lynchaj/nhyodyne/Z80BCKPLN2/ReadMe.md

# Extended backplane for Z80 Modular Backplane Computer

Sixteen backplane slots

Power LED indicator

Onboard power switch

Power input screw terminals for direct feed of 5V DC from power supply

# Jumpers

No jumpers or selectable options
