lynchaj/nhyodyne/Z80BCKPLN1/ReadMe.md

# Backplane board for Z80 Modular Backplane Computer

Eight backplane slots

Accepts 9V DC unregulated, center positive, 5.5mm external diameter, 2.1 internal diameter wall adapter power supply

Power LED

Uses either LM7805 5VDC voltage regulator or Pololu 5VDC switching power supply

Voltage regulator can be bypassed for direct 5VDC feed from power supply

# Jumpers

No jumpers or selectable options
