lynchaj/nhyodyne/Z80PROTO2/ReadMe.md

# Prototyping Board for Z80 Modular Backplane Computer

Provides area of plated through holes for general circuit prototyping

Provides pads and traces for common bus interface components

Power LED

Chip Select LED

No default IO ports but configurable if desired

# Jumpers

No jumpers to configure.  P47, P48, P49, and P50 are connect points for various CPU bus signals labeled on PCB
