lynchaj/nhyodyne/Z80ESP/HARDWARE/ReadMe.md

Z80 ESP IO is a board for video, keyboard, mouse, wifi, bluetooth, & sound using a pair of ESP32 dev modules

This board is currently not complete and should not be considered stable
