lynchaj/nhyodyne/6502PERI/Z80-6502IO.jpg

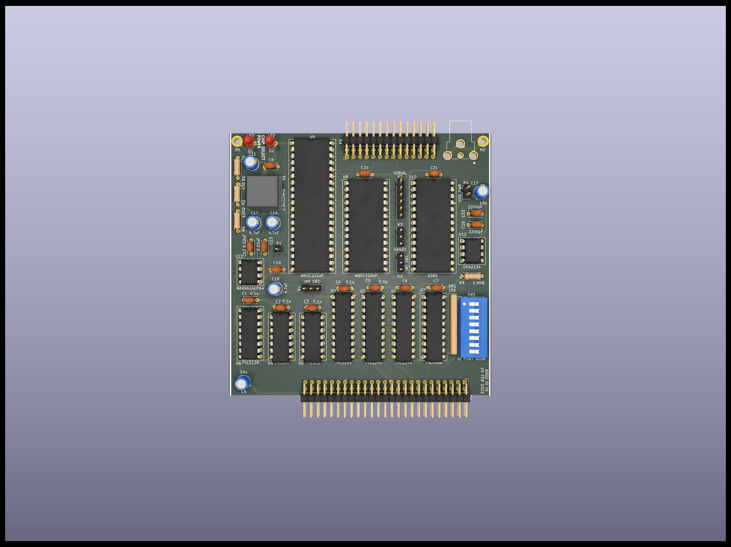
6502PERI/Z80-6502IO.jpg
