lynchaj/nhyodyne/Z80BCKPLN2/Z80BCKPLN2.jpg

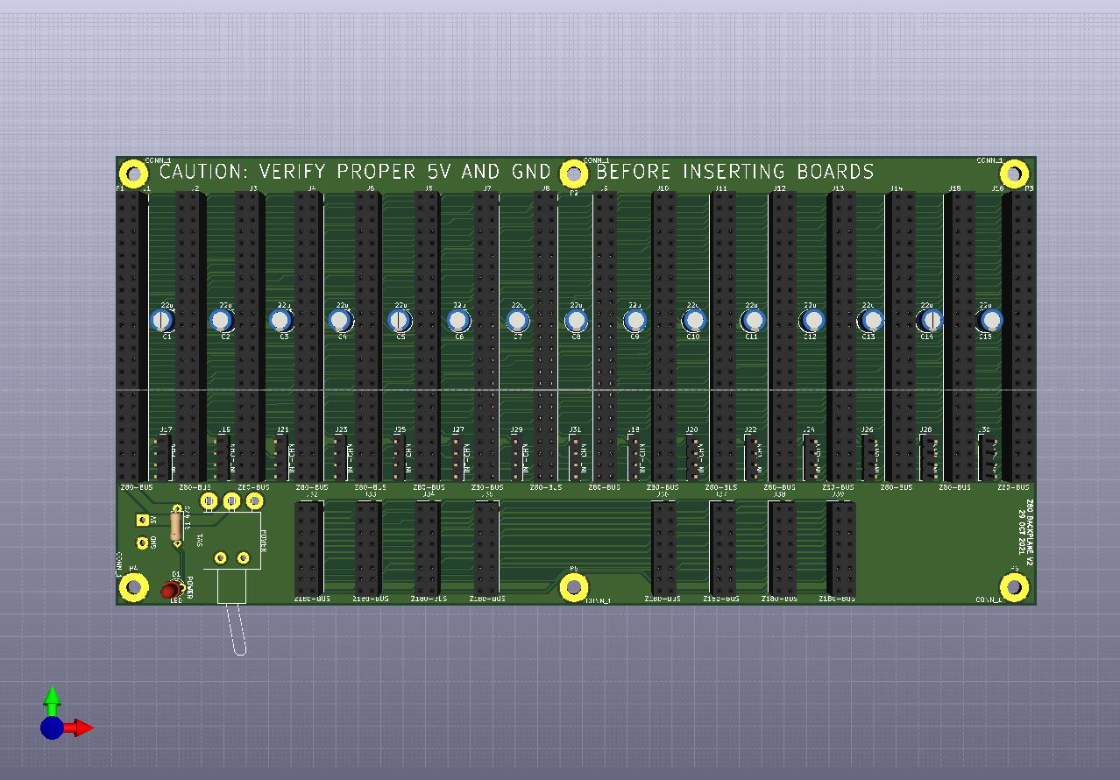
Z80BCKPLN2/Z80BCKPLN2.jpg
