lynchaj/nhyodyne/Z80CLOCK2/Z80CLOCK2.jpg

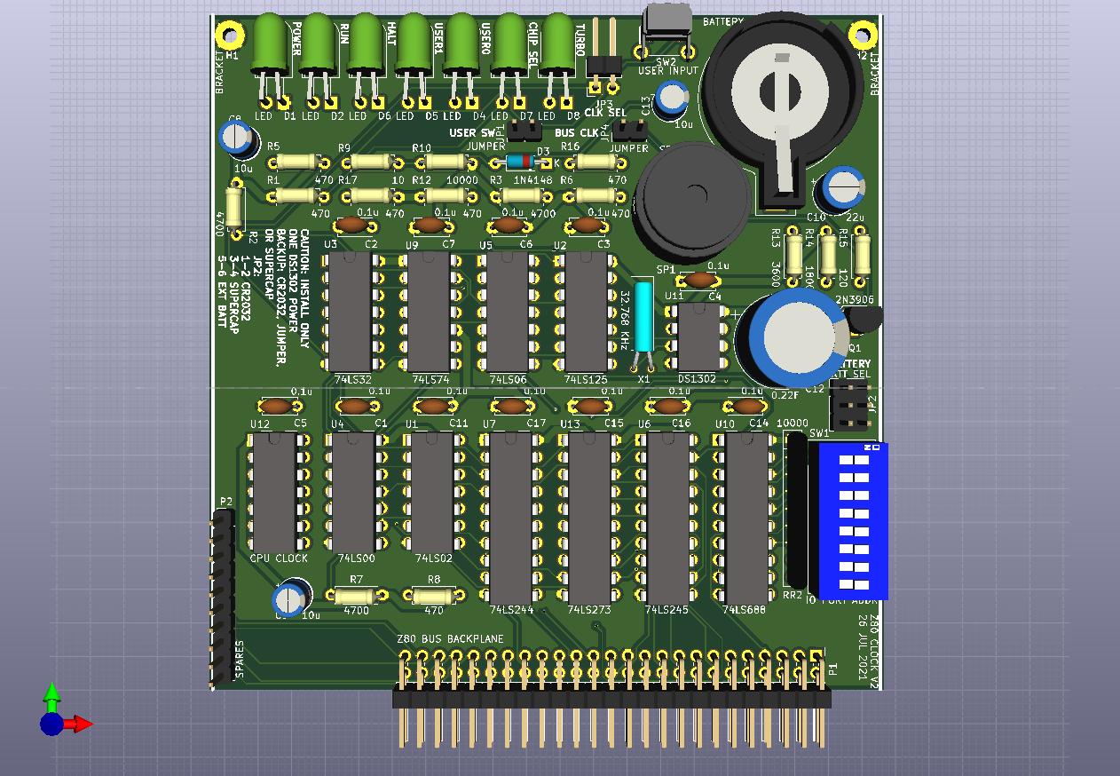
Z80CLOCK2/Z80CLOCK2.jpg
