lynchaj/nhyodyne/Z80CTCDART2/Z80CTCDART2.jpg

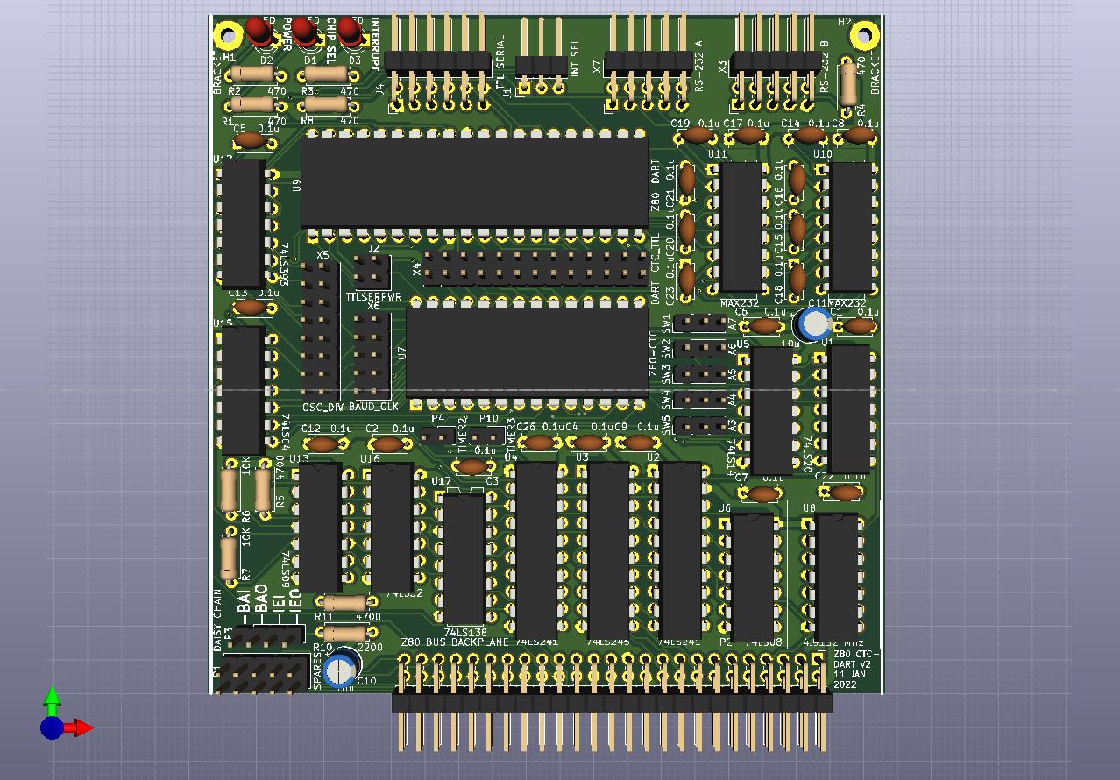
Z80CTCDART2/Z80CTCDART2.jpg
