lynchaj/nhyodyne/Z80DMA2/Z80DMA2.jpg

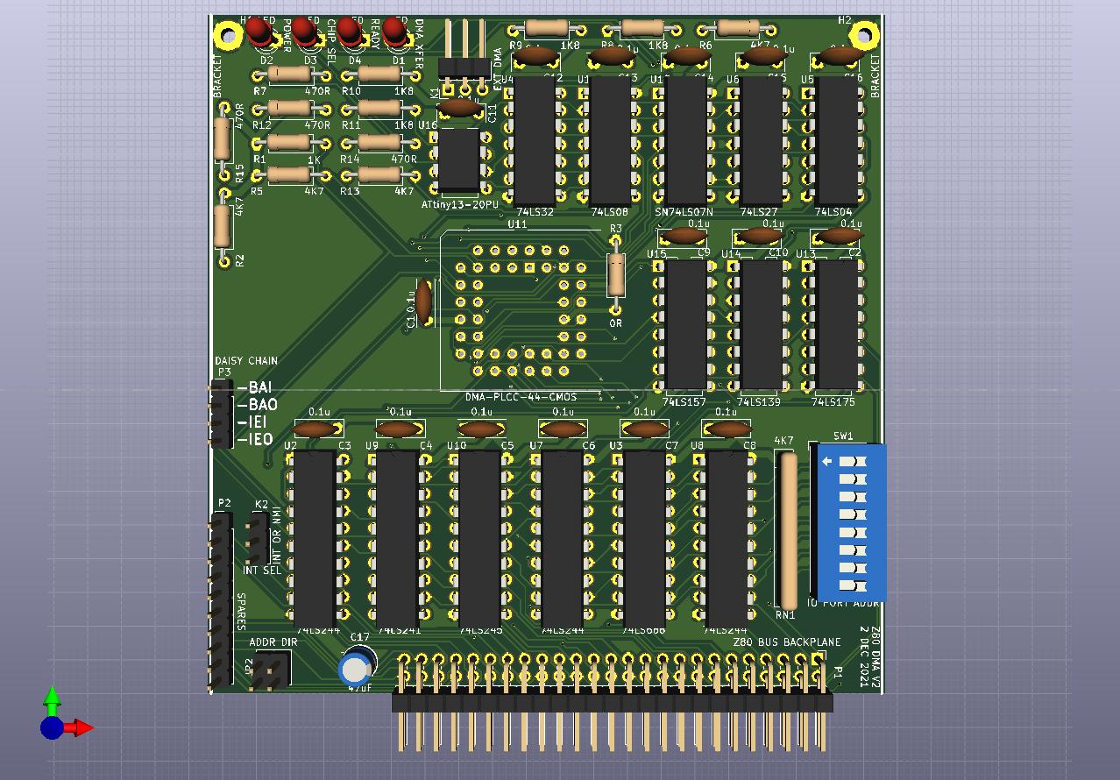
Z80DMA2/Z80DMA2.jpg
