lynchaj/nhyodyne/Z80DUALPIO2/Z80DUALPIO2.jpg

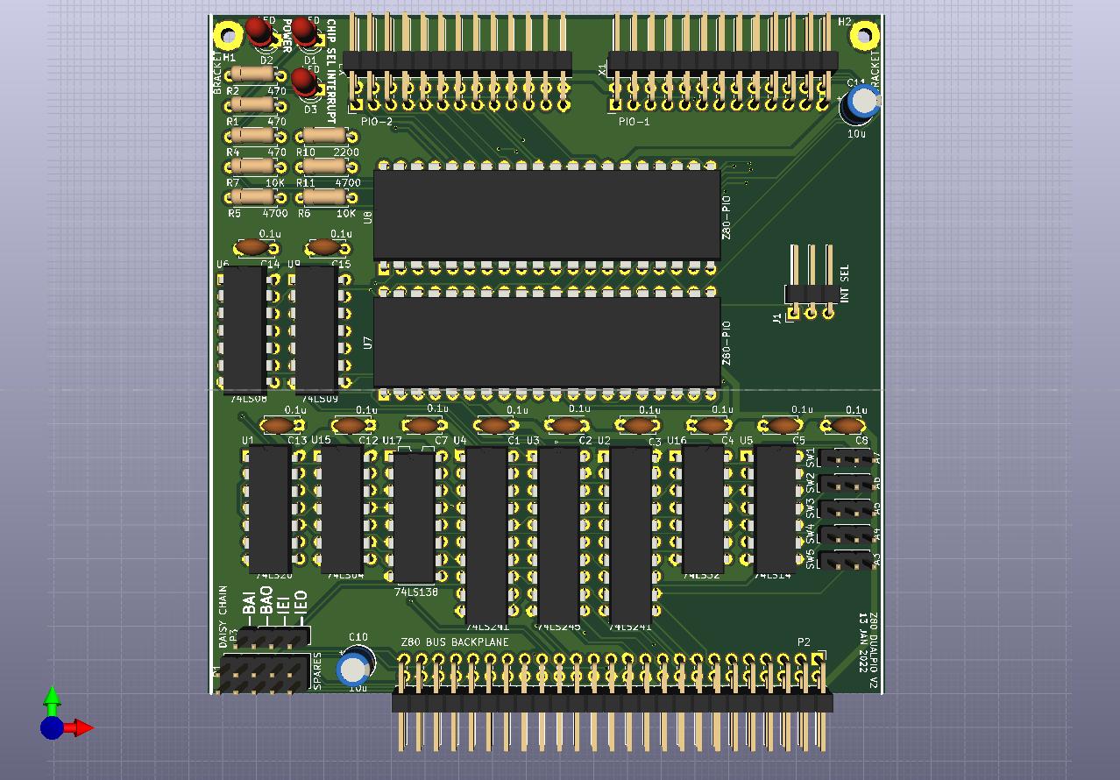
Z80DUALPIO2/Z80DUALPIO2.jpg
