lynchaj/nhyodyne/Z80DUART2/Z80DUART2.jpg

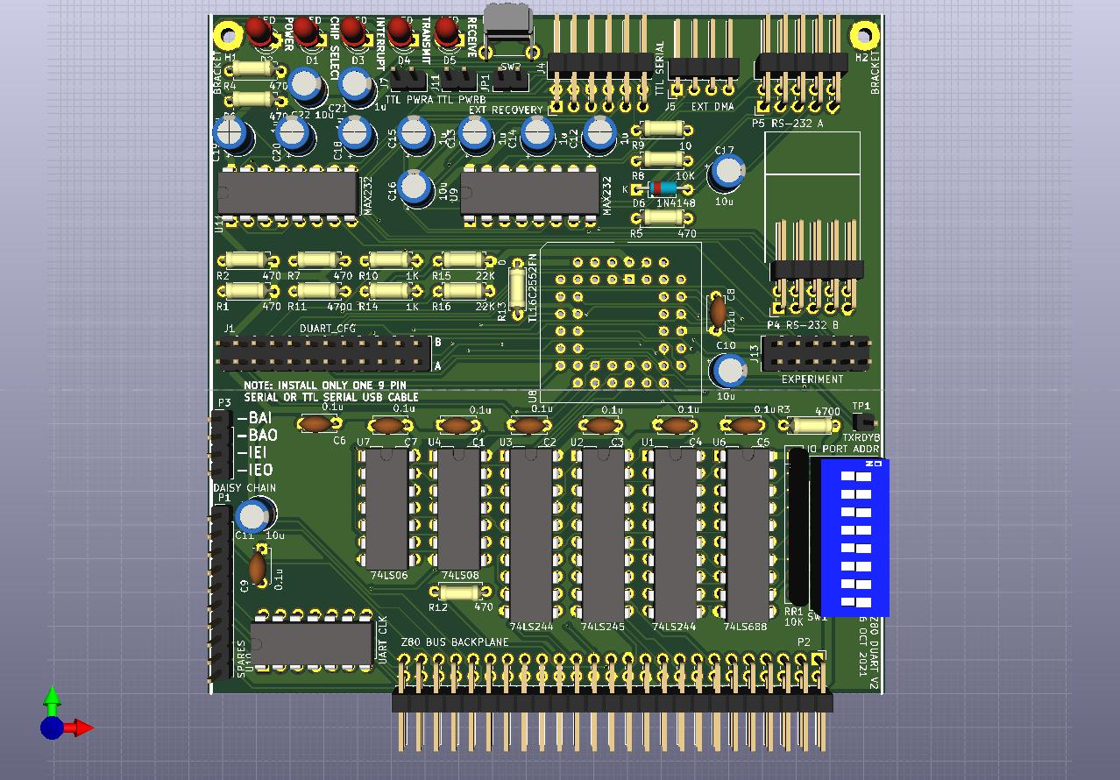
Z80DUART2/Z80DUART2.jpg
