lynchaj/nhyodyne/Z80ENET/Z80ENET.jpg

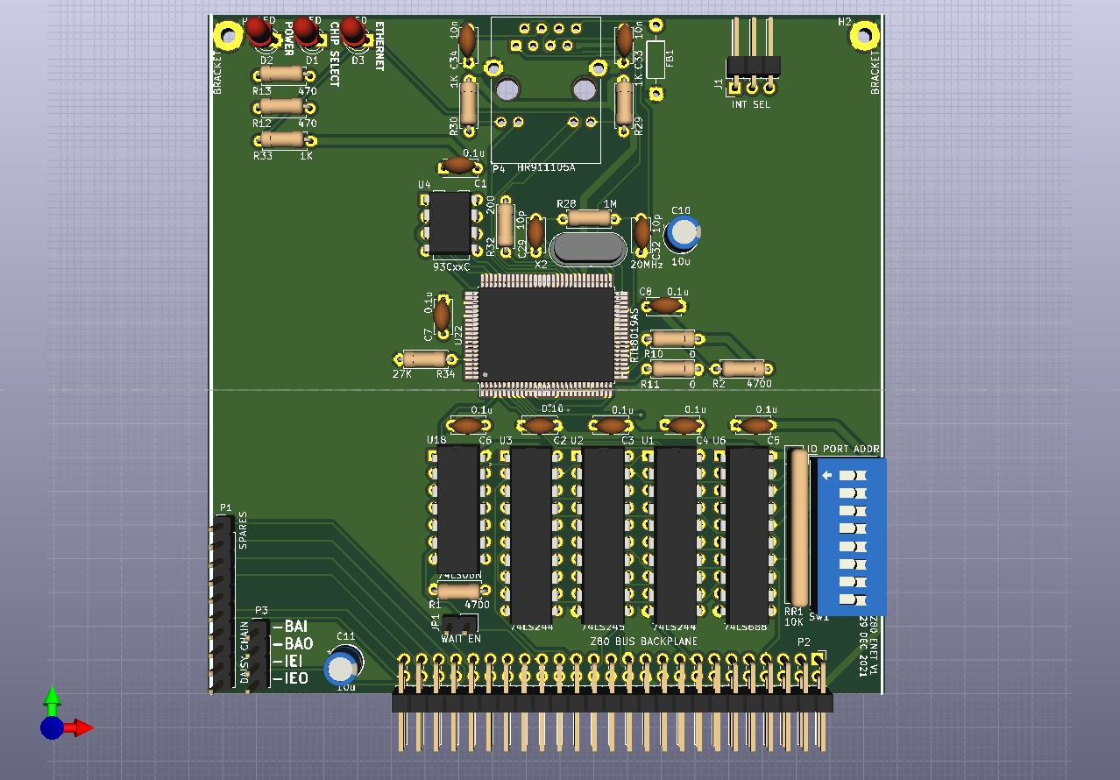
Z80ENET/Z80ENET.jpg
