lynchaj/nhyodyne/Z80FDC1/Z80FDC.jpg

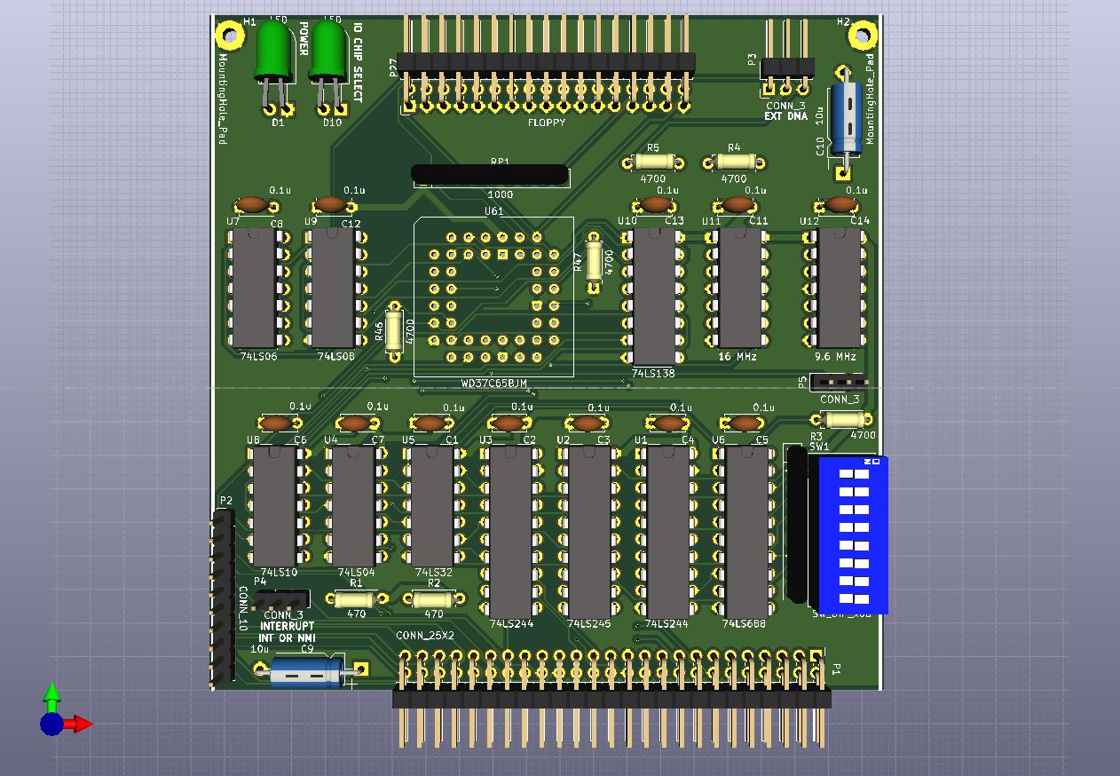
Z80FDC1/Z80FDC.jpg
