lynchaj/nhyodyne/Z80KBDMSE1/Photos/IMG_5907.JPG

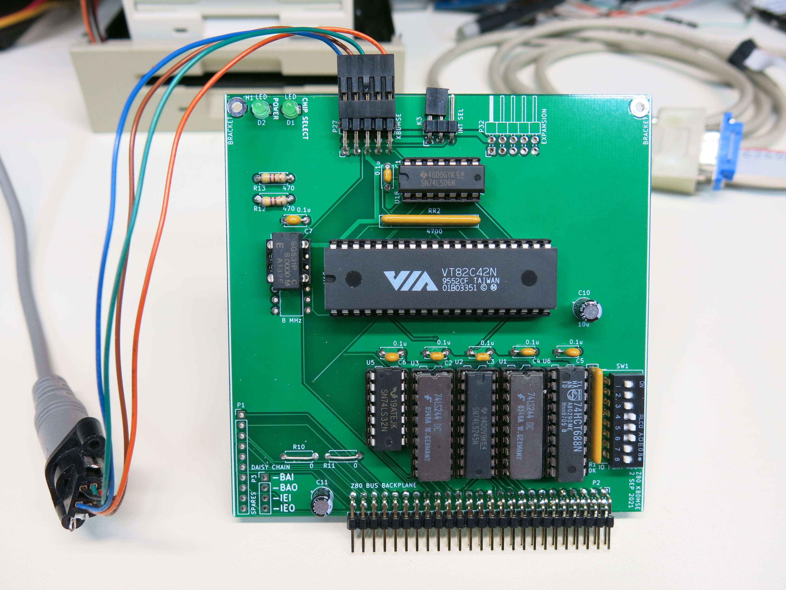
Z80KBDMSE1/Photos/IMG_5907.JPG
