lynchaj/nhyodyne/Z80KBDMSE1/Z80KBDMSE.jpg

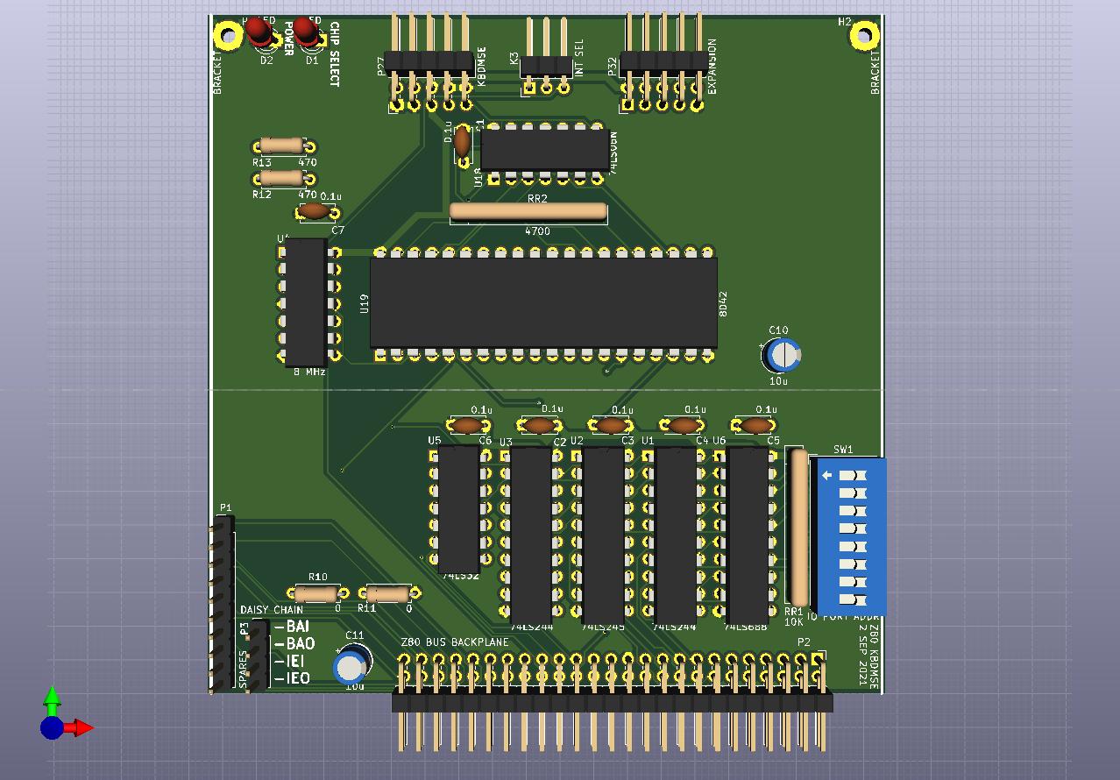
Z80KBDMSE1/Z80KBDMSE.jpg
