lynchaj/nhyodyne/Z80PPIDE2/Z80PPIDE2.jpg

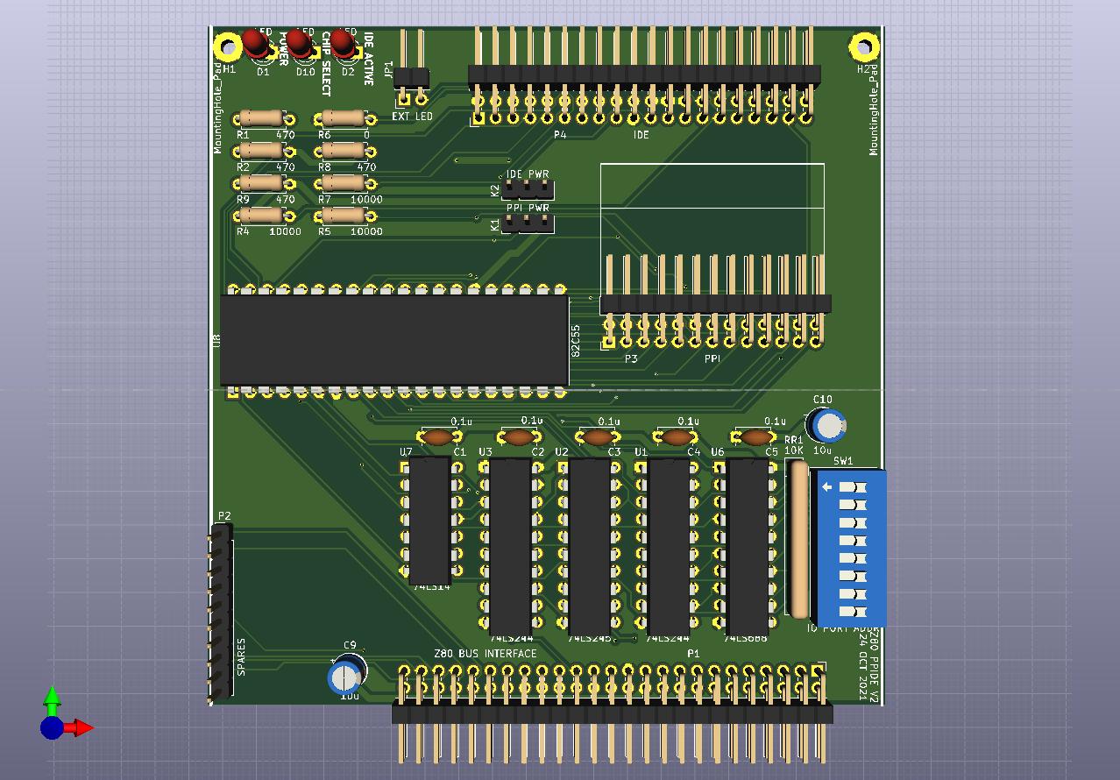
Z80PPIDE2/Z80PPIDE2.jpg
