lynchaj/nhyodyne/Z80PROC3/Z80PROC3.jpg

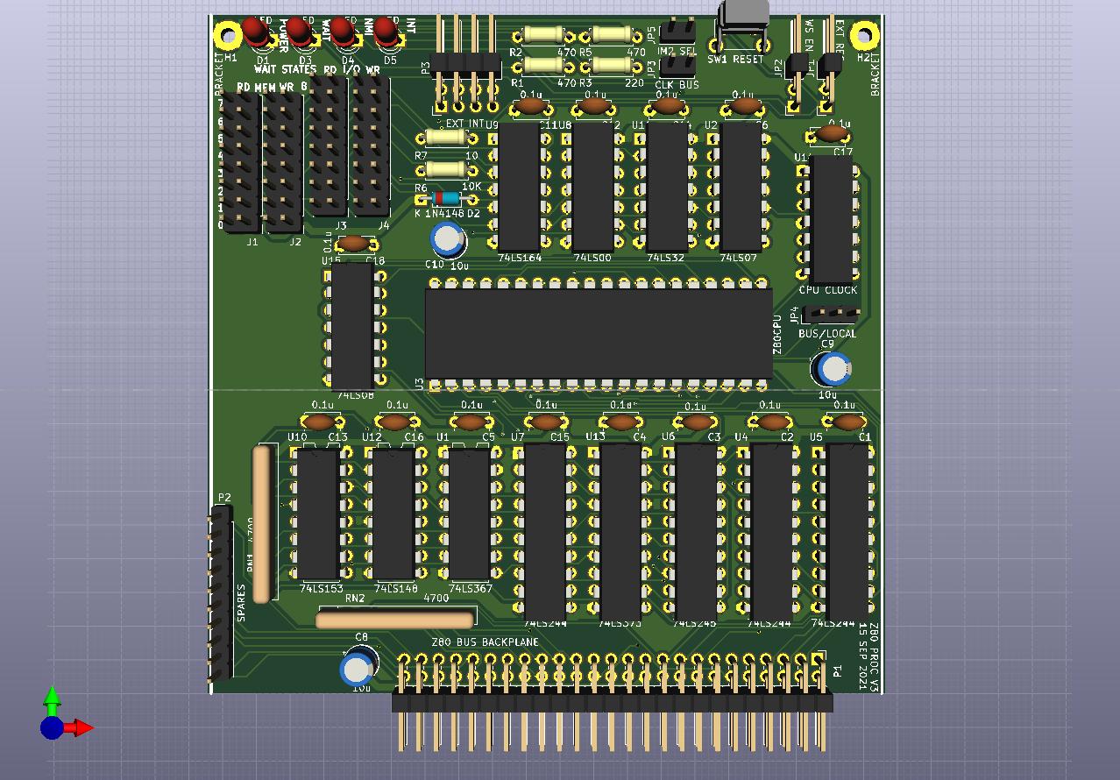
Z80PROC3/Z80PROC3.jpg
