lynchaj/nhyodyne/Z80PROTO2/Z80PROTO2.jpg

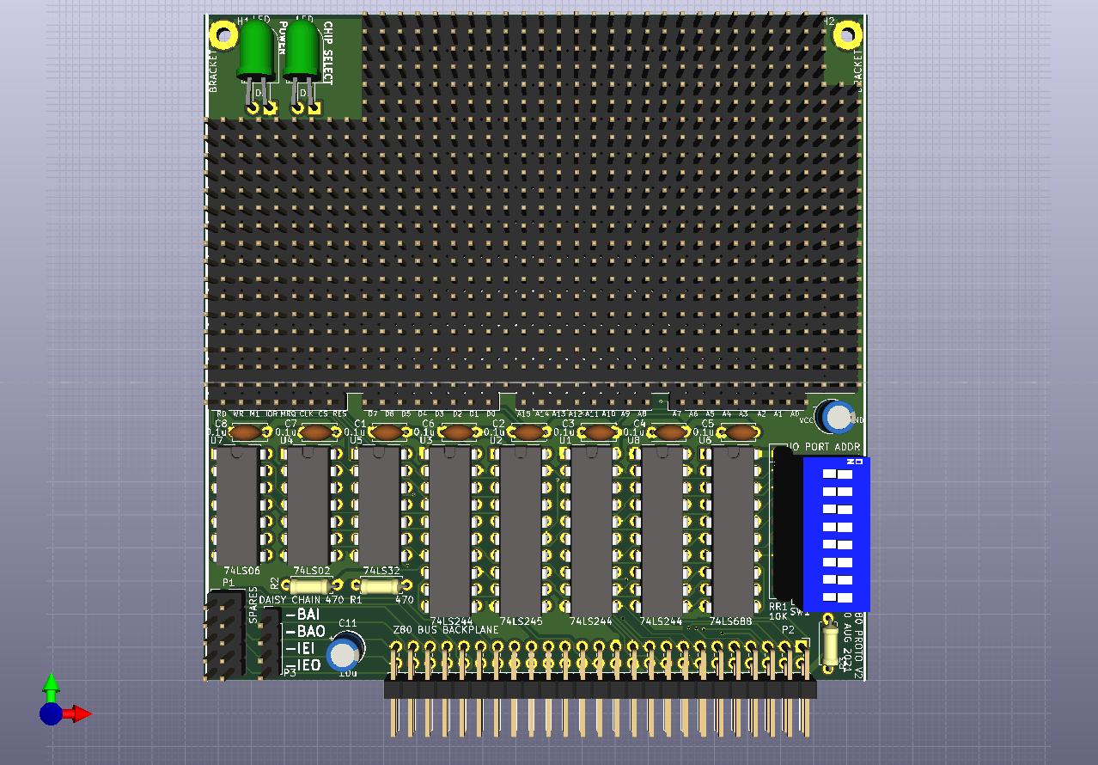
Z80PROTO2/Z80PROTO2.jpg
