lynchaj/nhyodyne/Z80RAM3/Z80RAM3.jpg

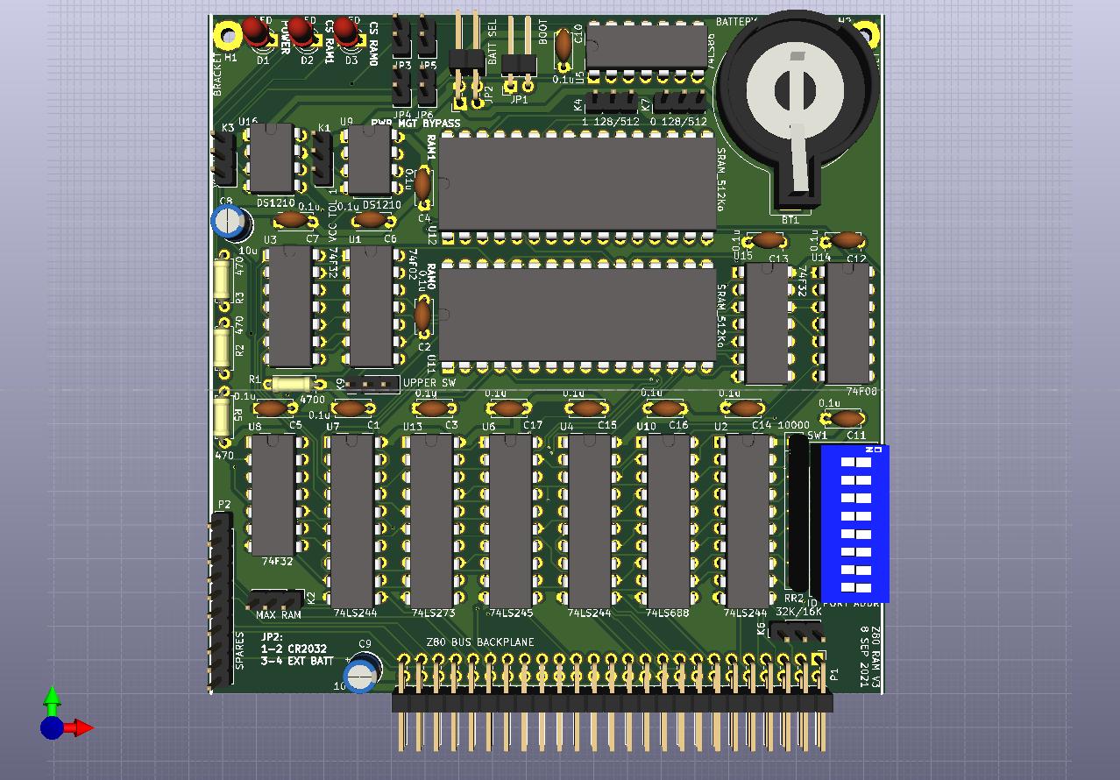
Z80RAM3/Z80RAM3.jpg
