lynchaj/nhyodyne/Z80SERIAL2/Z80SERIAL2.jpg

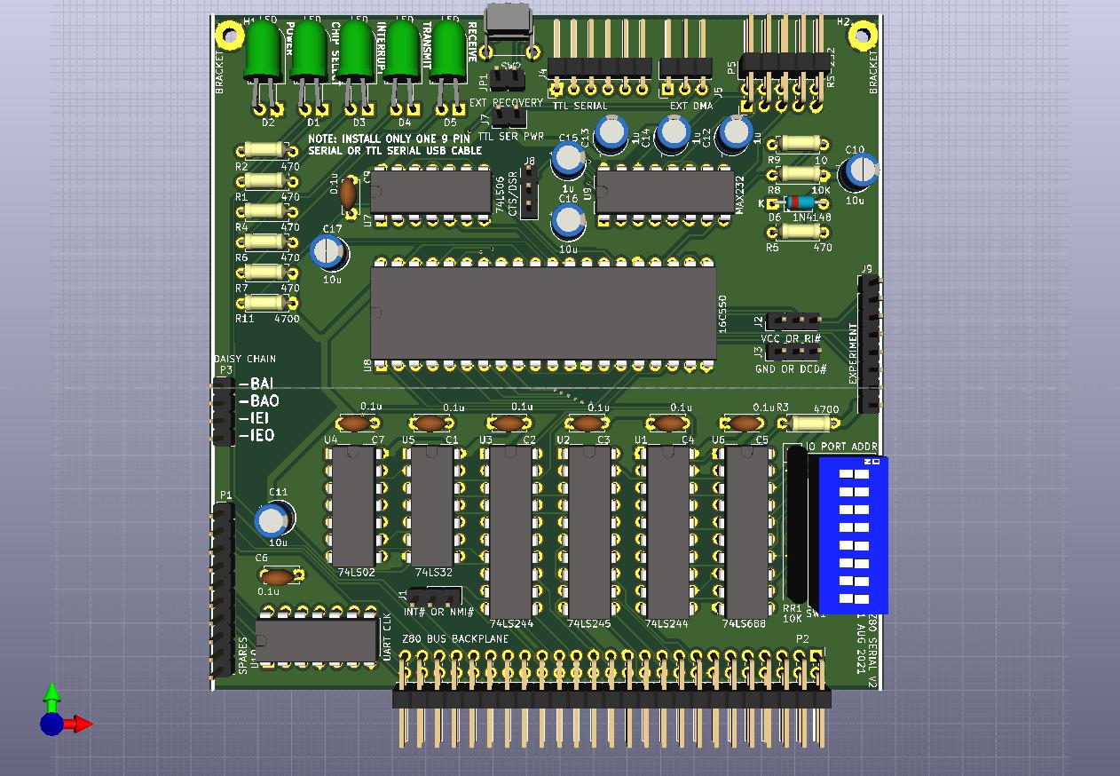
Z80SERIAL2/Z80SERIAL2.jpg
