lynchaj/nhyodyne/Z80SERIAL3/Z80SERIAL3.jpg

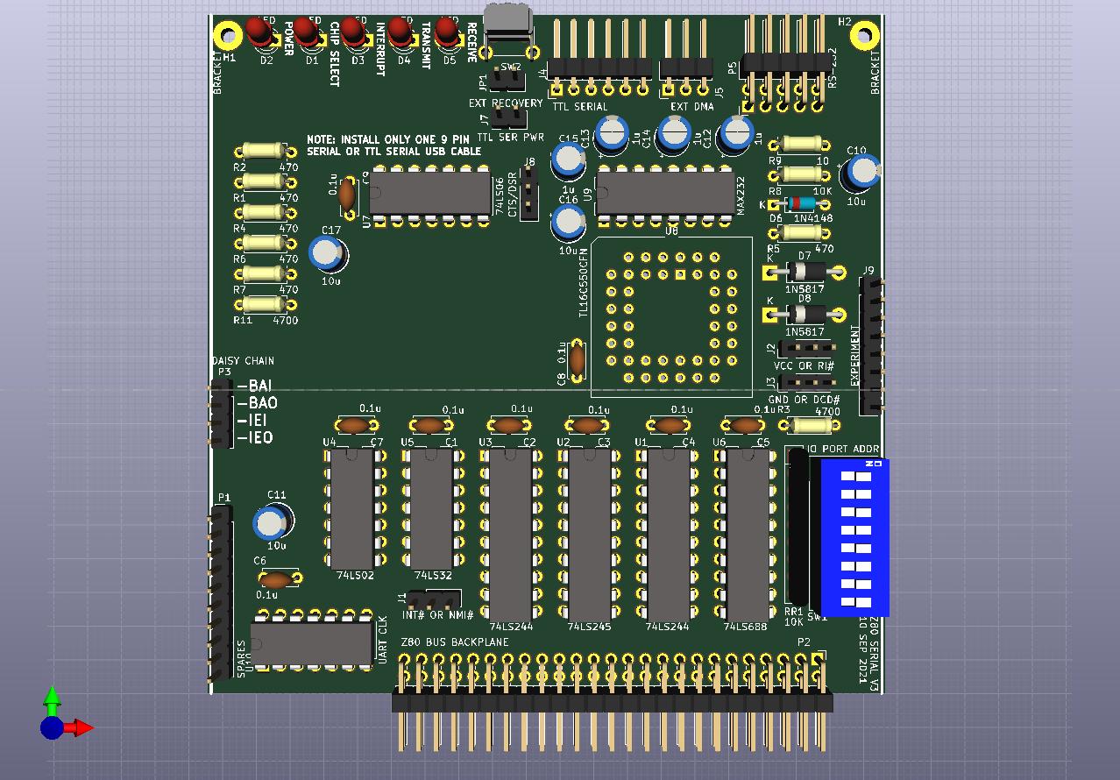
Z80SERIAL3/Z80SERIAL3.jpg
