lynchaj/nhyodyne/Z80VDC1/Photos/20211210_194827.jpg

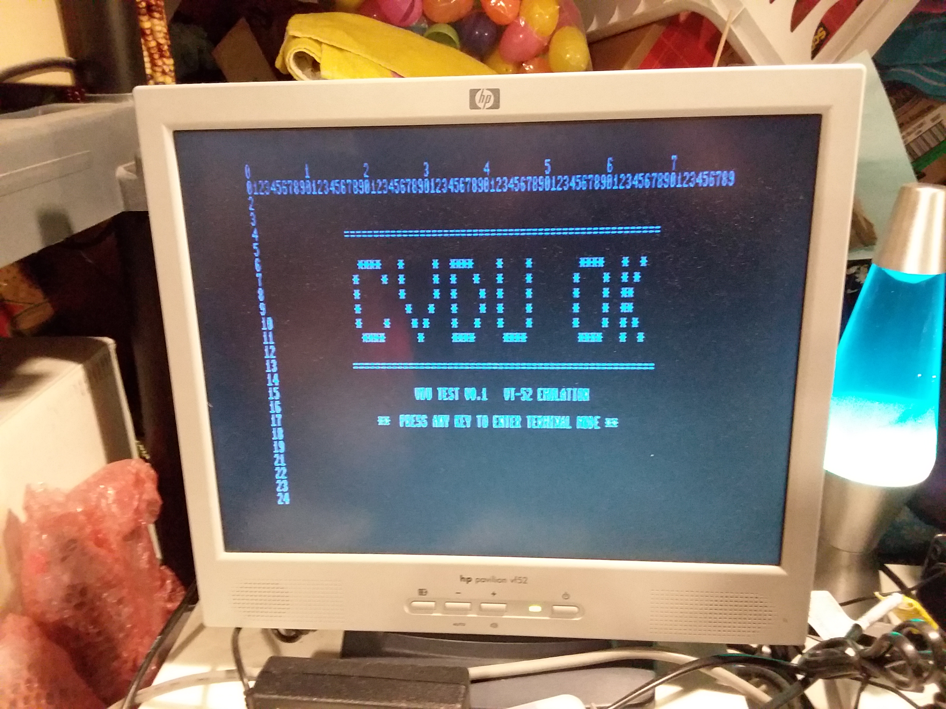
Z80VDC1/Photos/20211210_194827.jpg
