lynchaj/nhyodyne/Z80VDC1/Photos/IMG_5908.JPG

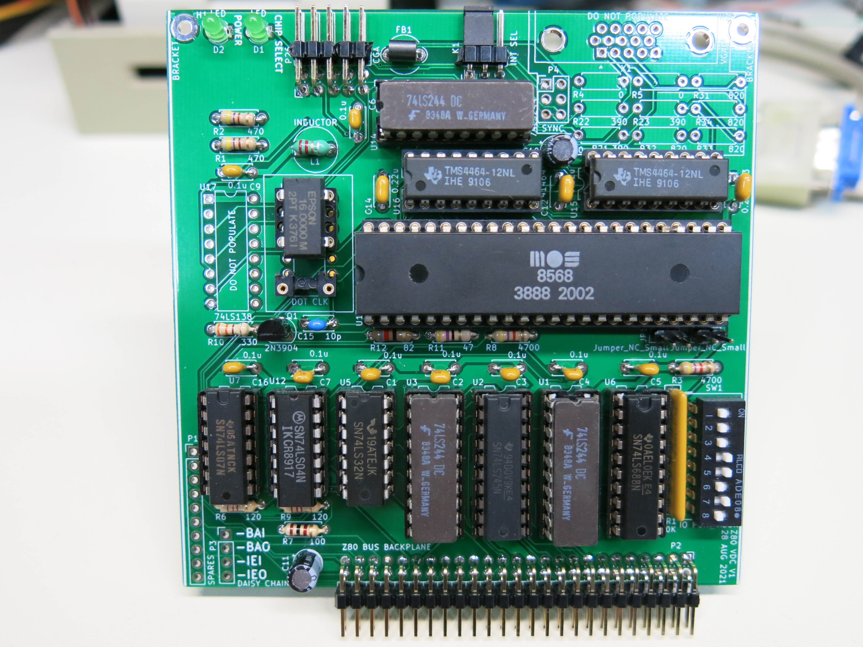
Z80VDC1/Photos/IMG_5908.JPG
