lynchaj/nhyodyne/Z80VDC1/Photos/IMG_5909.JPG

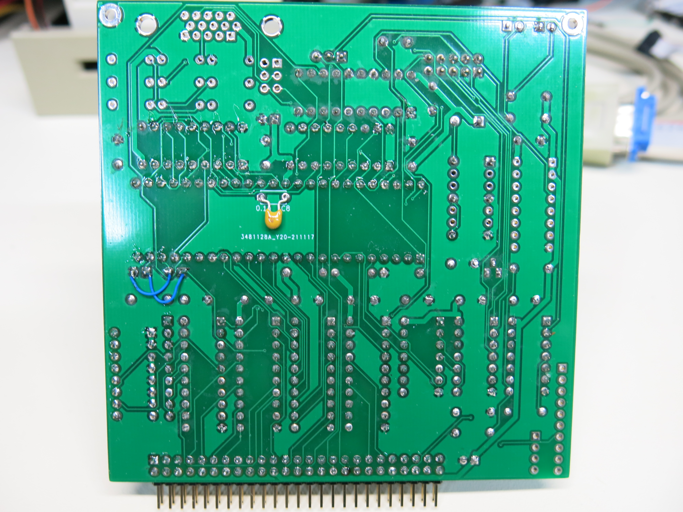
Z80VDC1/Photos/IMG_5909.JPG
