lynchaj/nhyodyne/Z80VDC1/Photos/IMG_5910.JPG

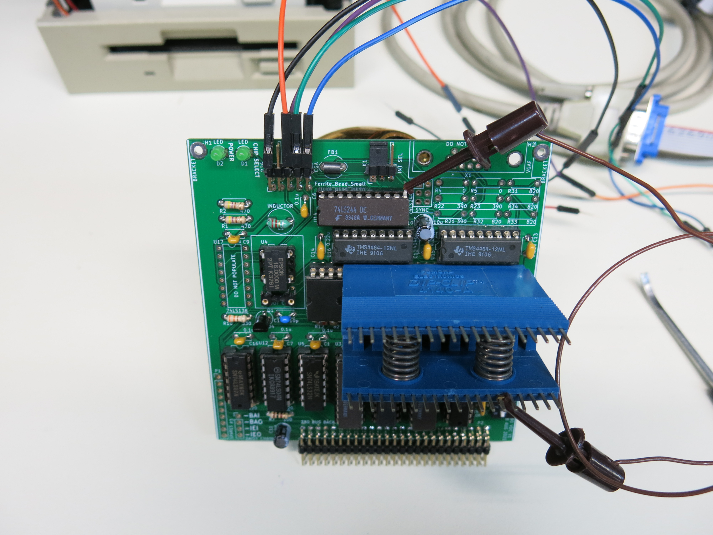
Z80VDC1/Photos/IMG_5910.JPG
