lynchaj/nhyodyne/Z80VDP1A/Z80VDP1A.jpg

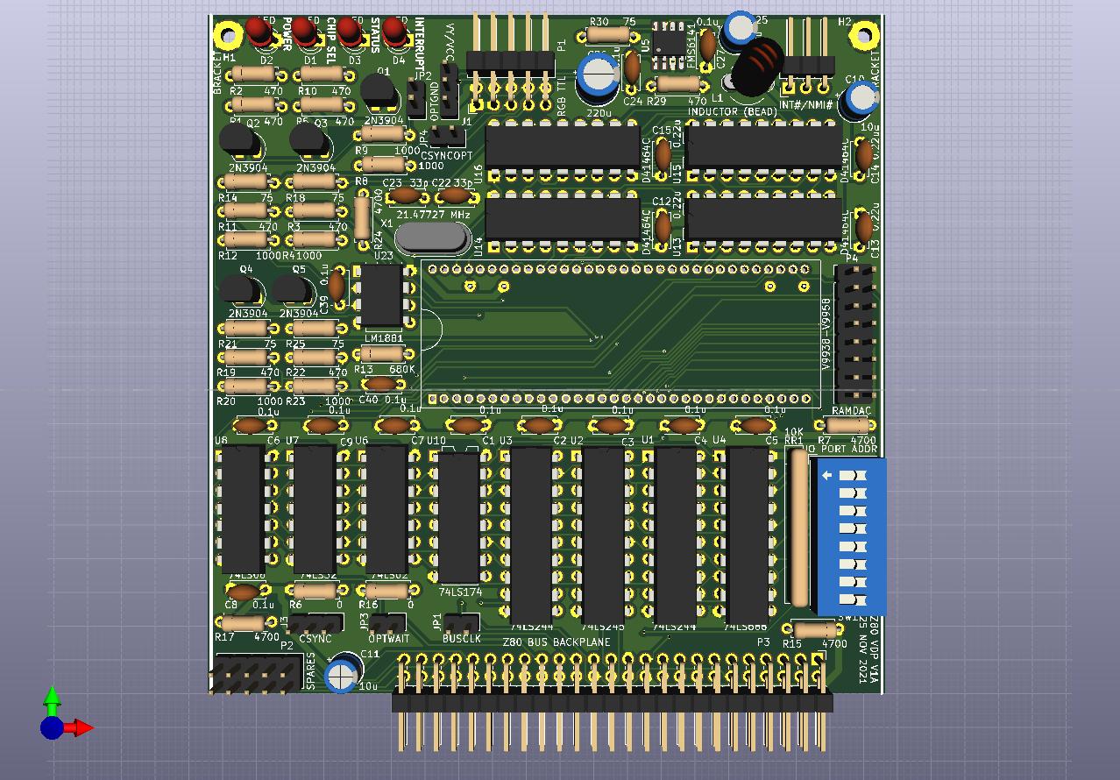
Z80VDP1A/Z80VDP1A.jpg
