lynchaj/nhyodyne/Z80MBC/TestPrograms/ReadMe.md

Folder for Z80 MBC test programs for initial build.  Meant to be burned into a ROM for hardware verification prior to booting RomWBW
