lynchaj/nhyodyne/Z80MBC/TestPrograms/mon8080/ReadMe.md

Folder for Dave Dunfield's Hardware Debug Monitor (HDM80) the amazing RAMless ROMonly debugging monitor for initial build debugging
