lynchaj/nhyodyne/Z80VDC1/Z80VDC-schematic.pdf

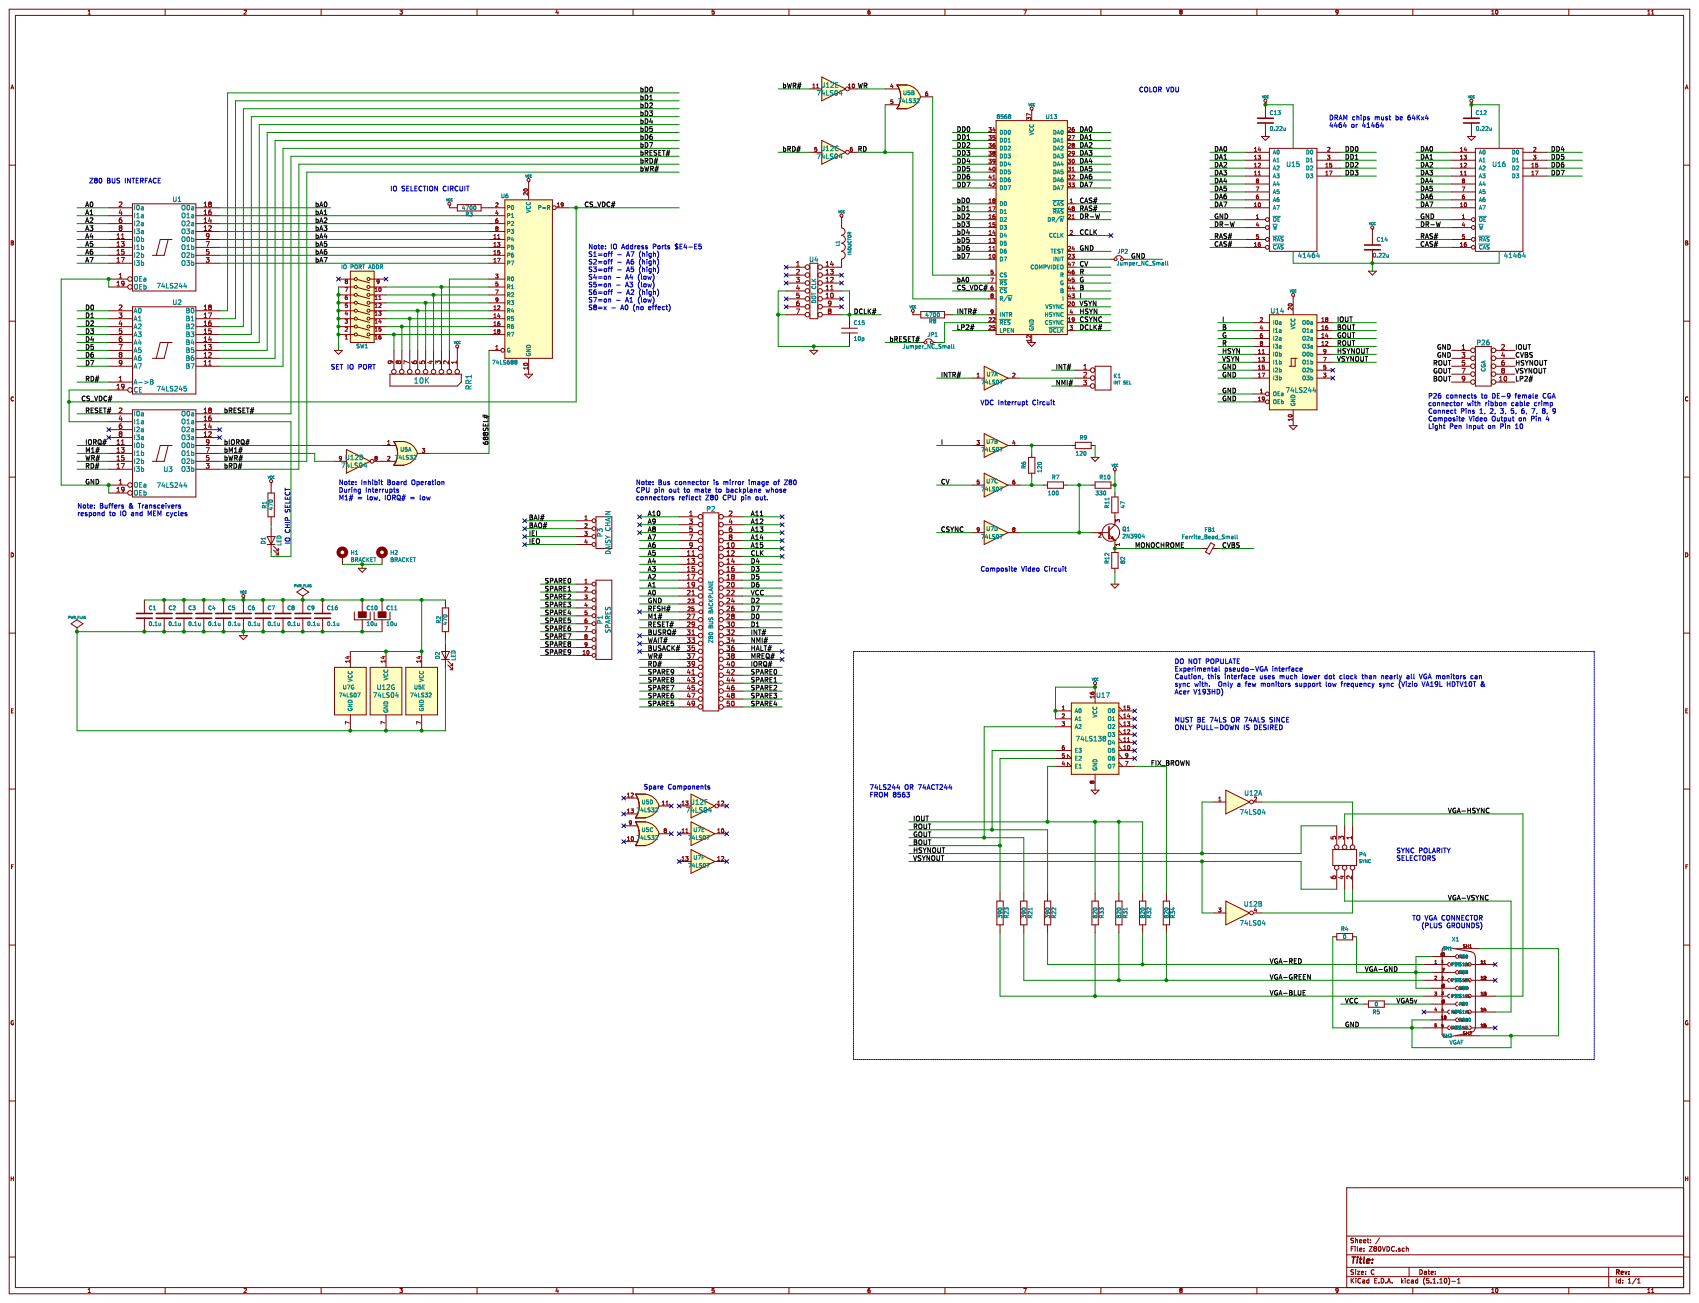
[picture p66: page 1]
