lynchaj/nhyodyne/Z80SERIAL3/Z80SERIAL3-schematic.pdf

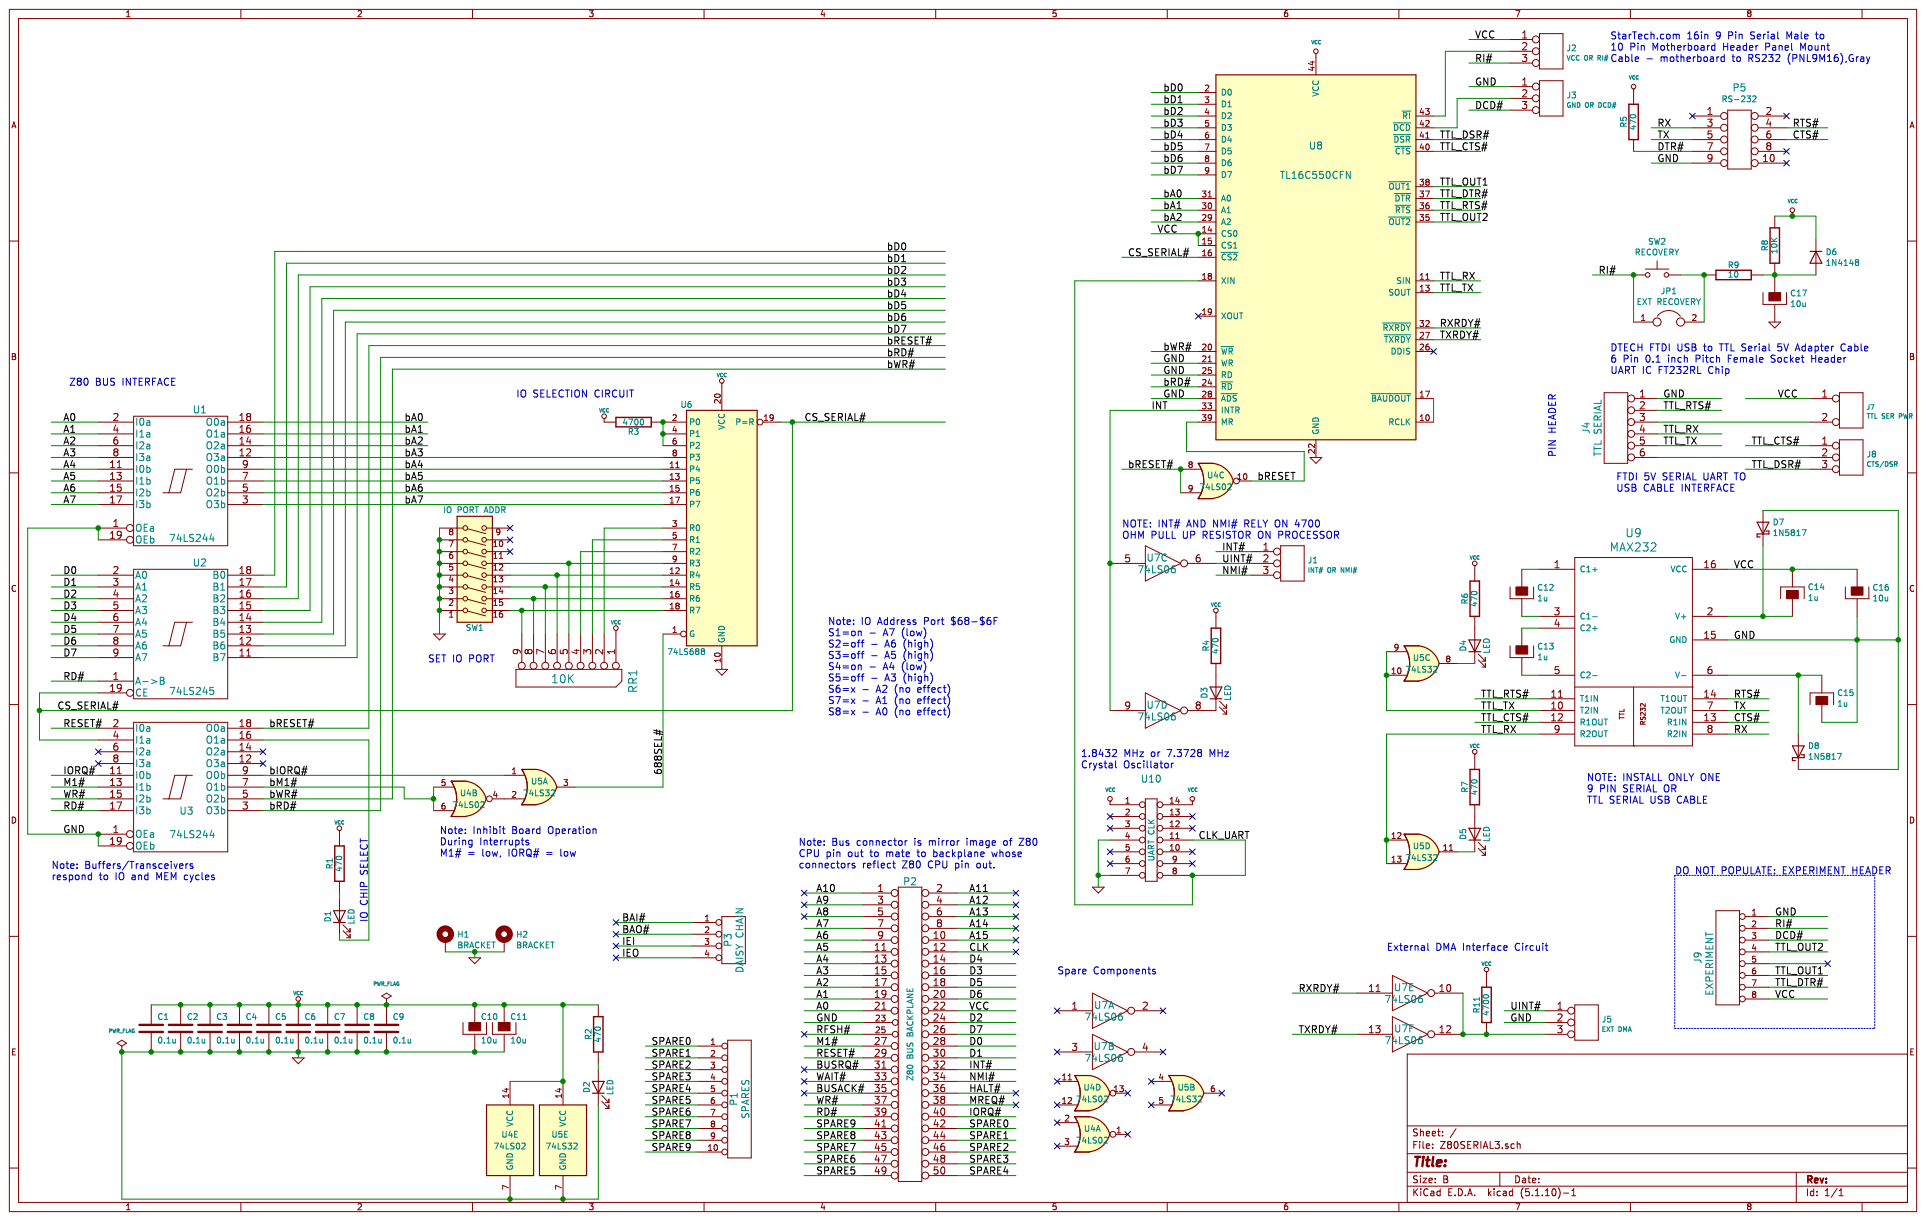
[picture p67: page 1]
