lynchaj/nhyodyne/Z80SERIAL2/Z80SERIAL2-schematic.pdf

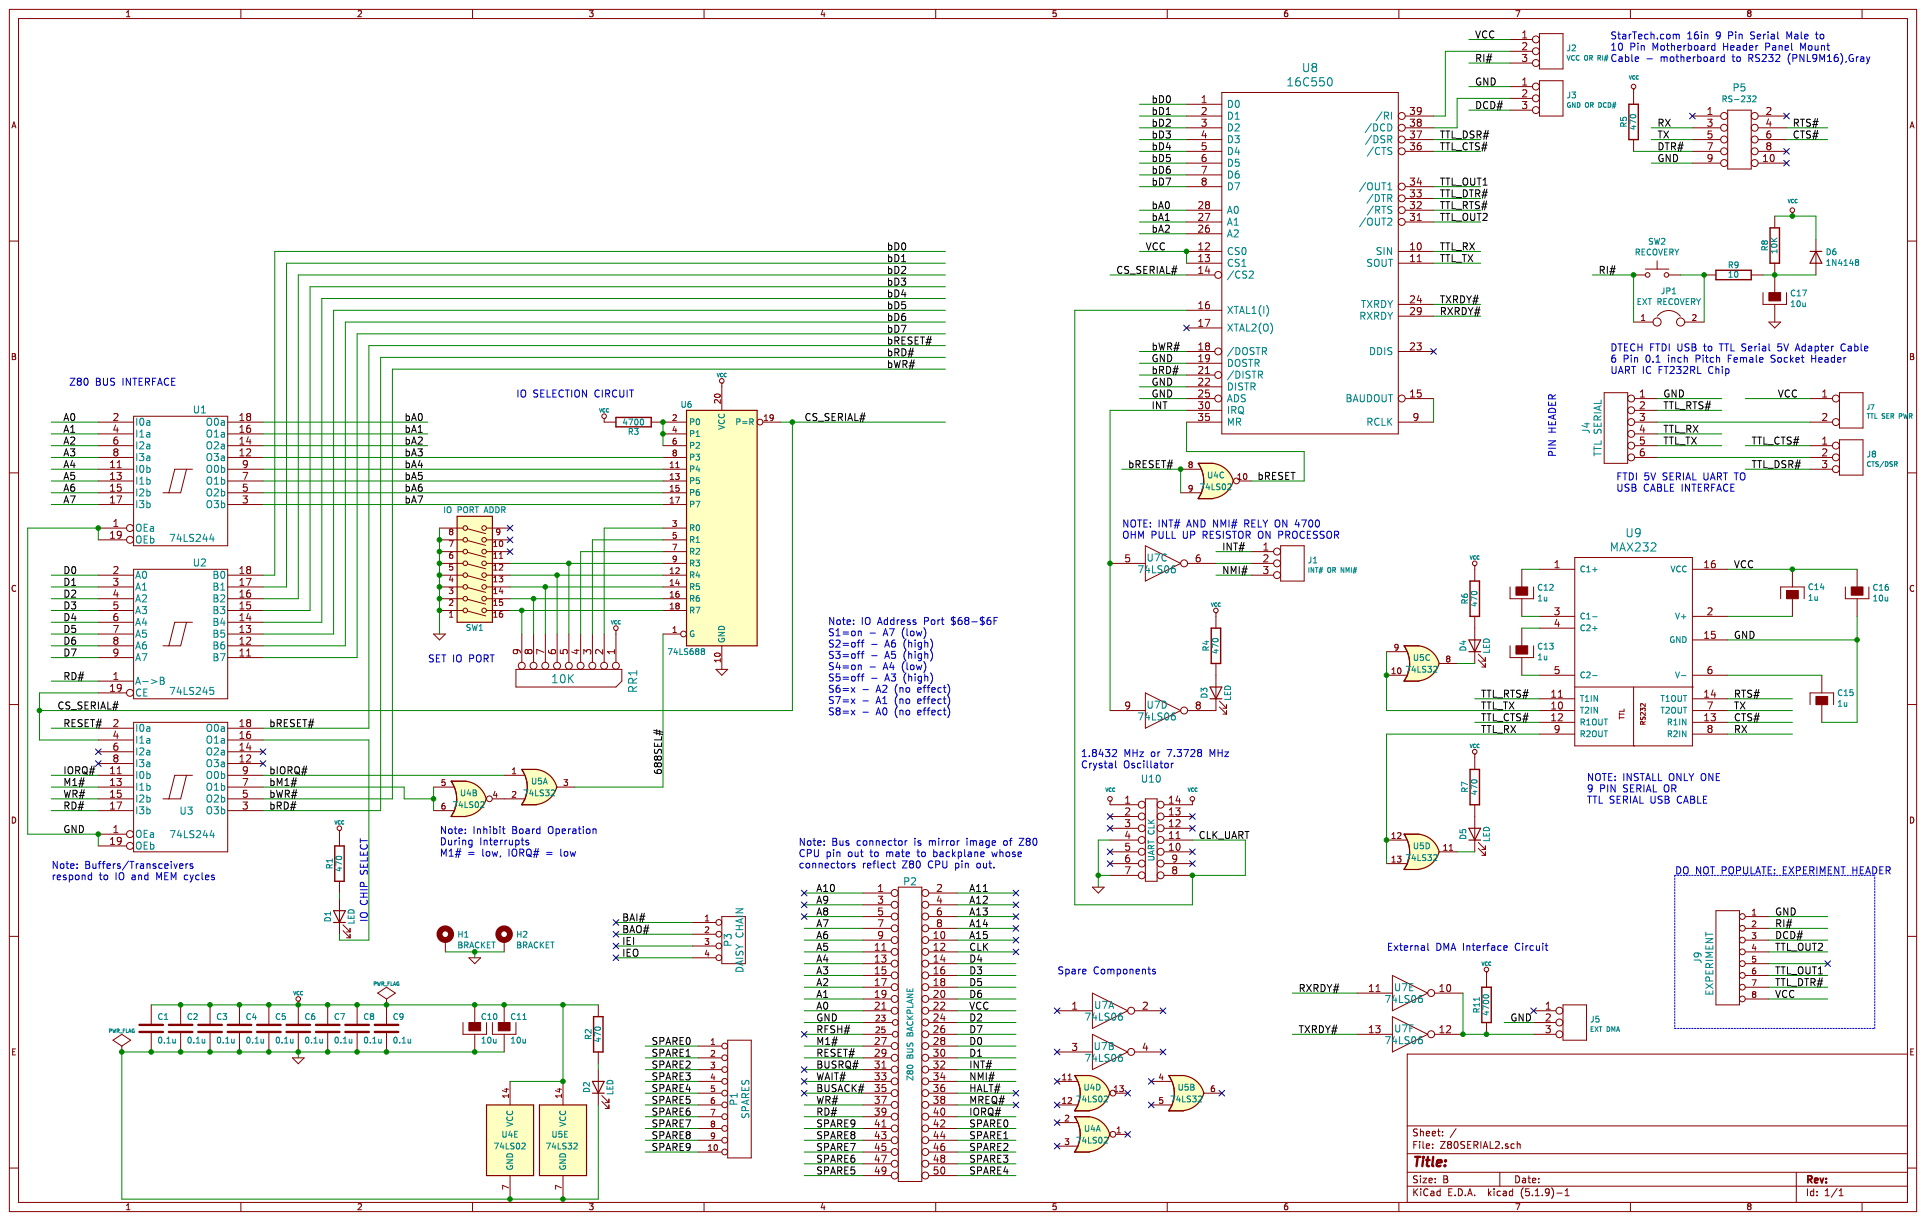
[picture p68: page 1]
