lynchaj/nhyodyne/Z80ROM2/Z80ROM2-schematic.pdf

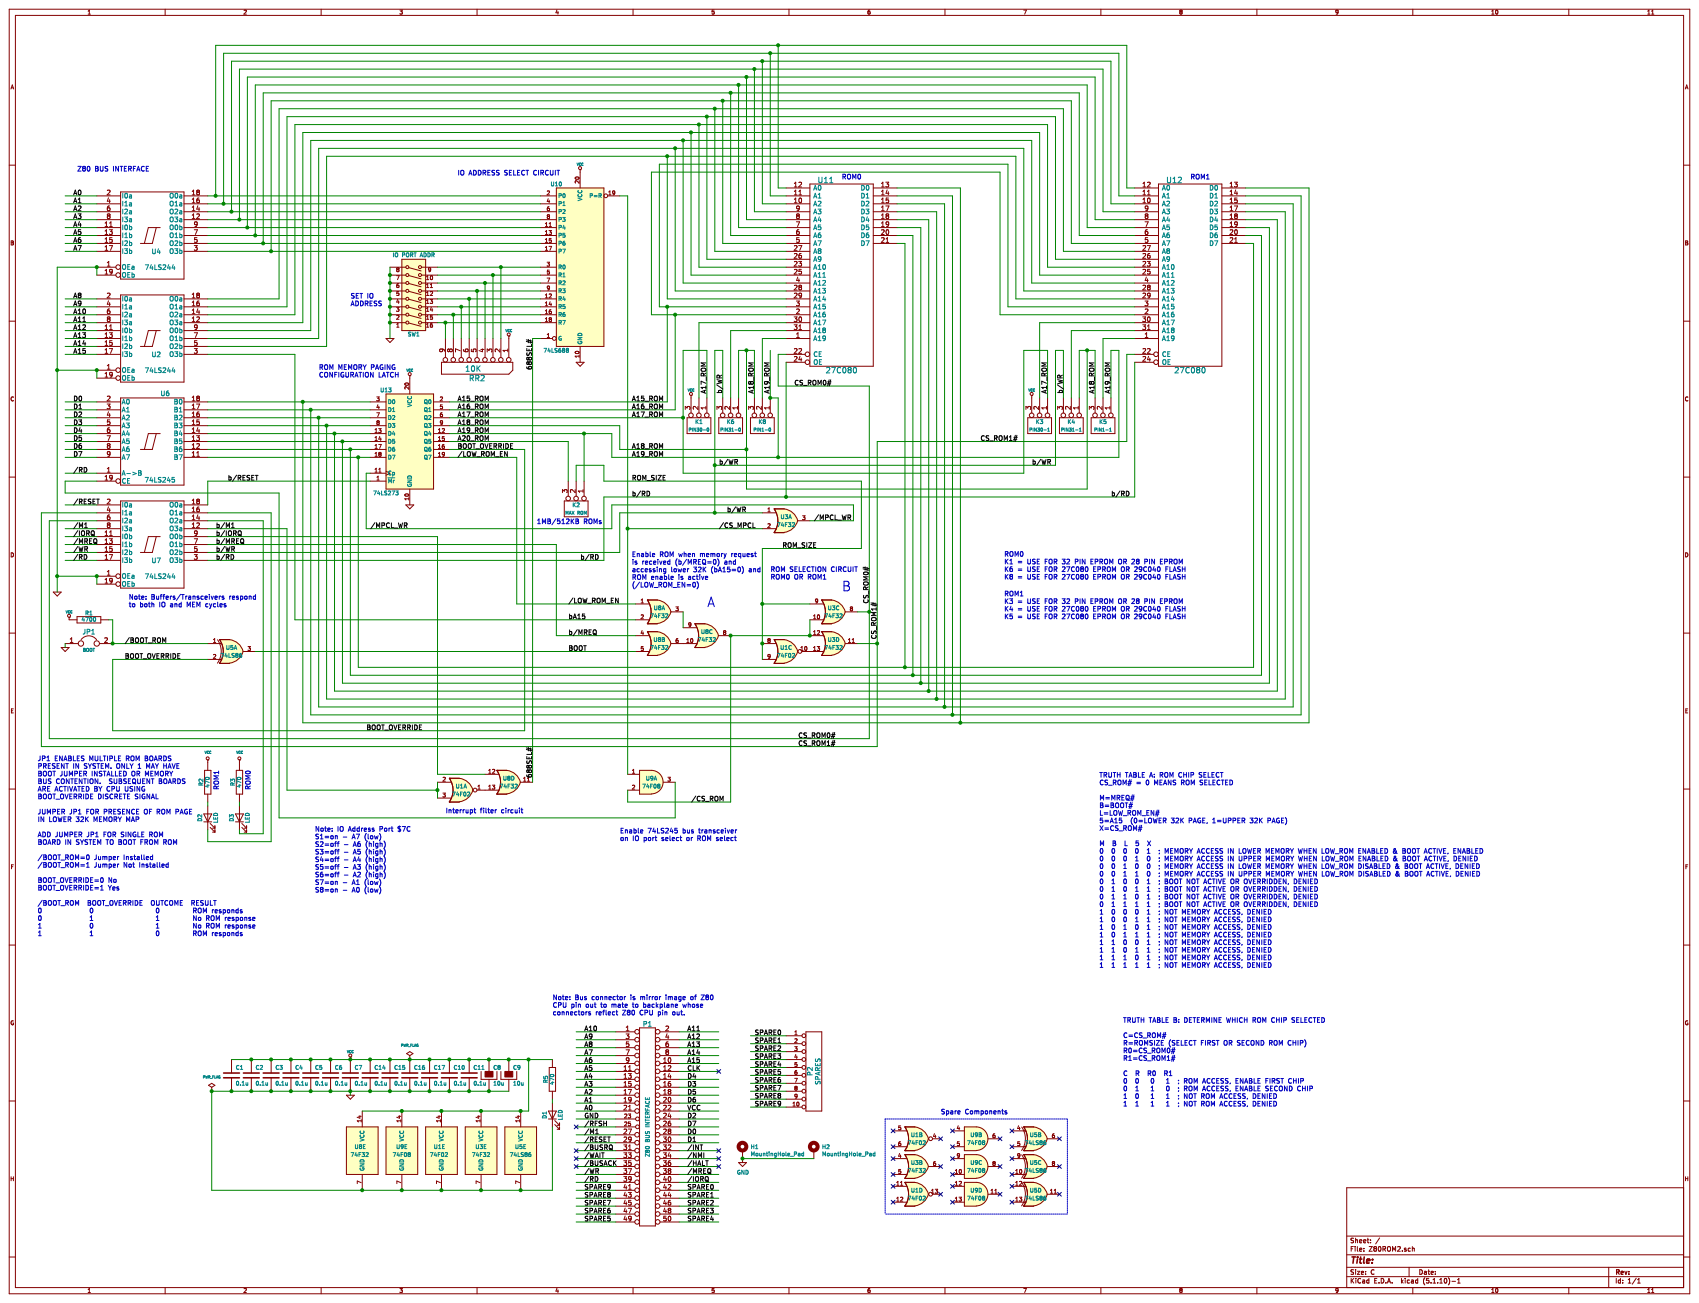
[picture p69: page 1]
