lynchaj/nhyodyne/Z80RAM3/Z80RAM3-schematic.pdf

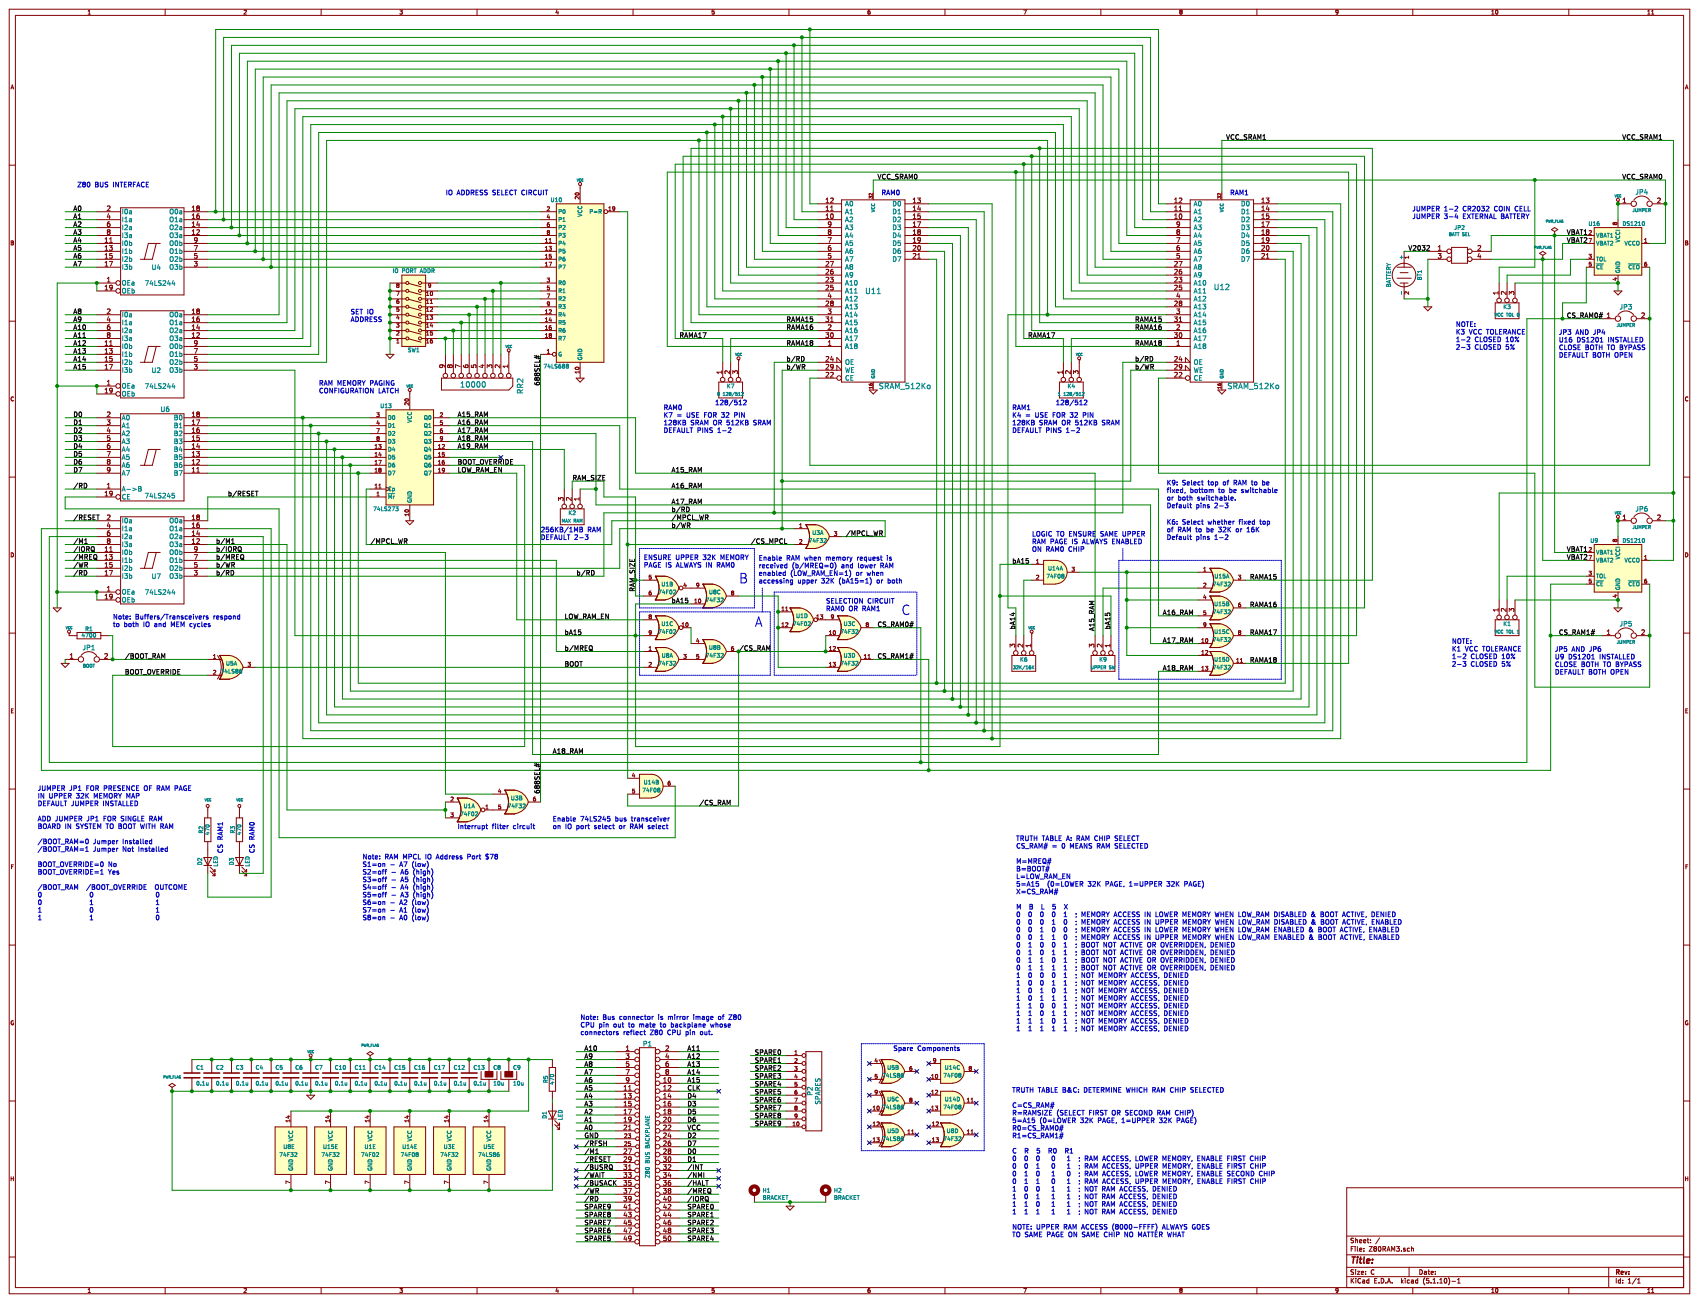
[picture p70: page 1]
