lynchaj/nhyodyne/Z80PROTO2/Z80PROTO2-schematic.pdf

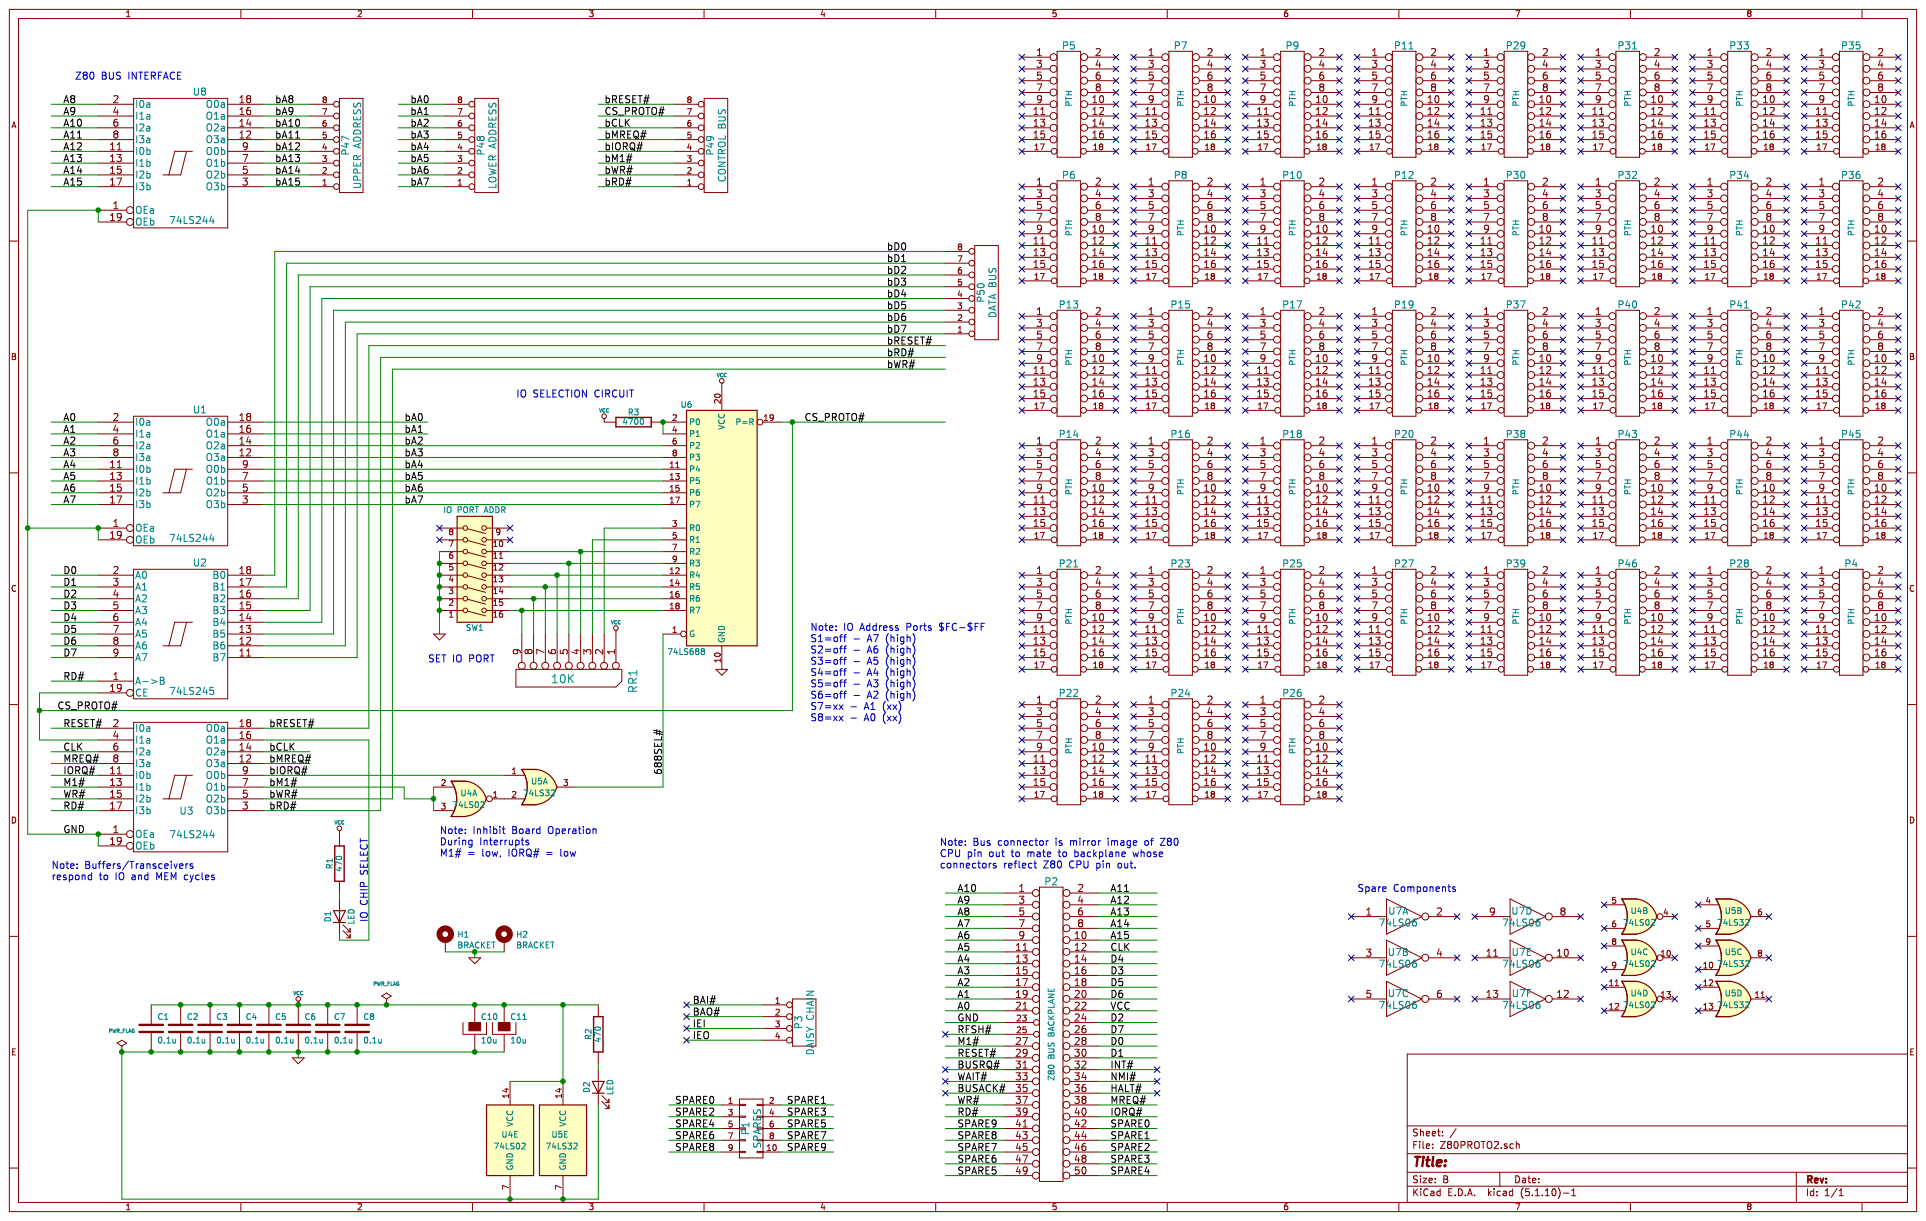
[picture p71: page 1]
