lynchaj/nhyodyne/Z80PROC3/Z80PROC3-schematic.pdf

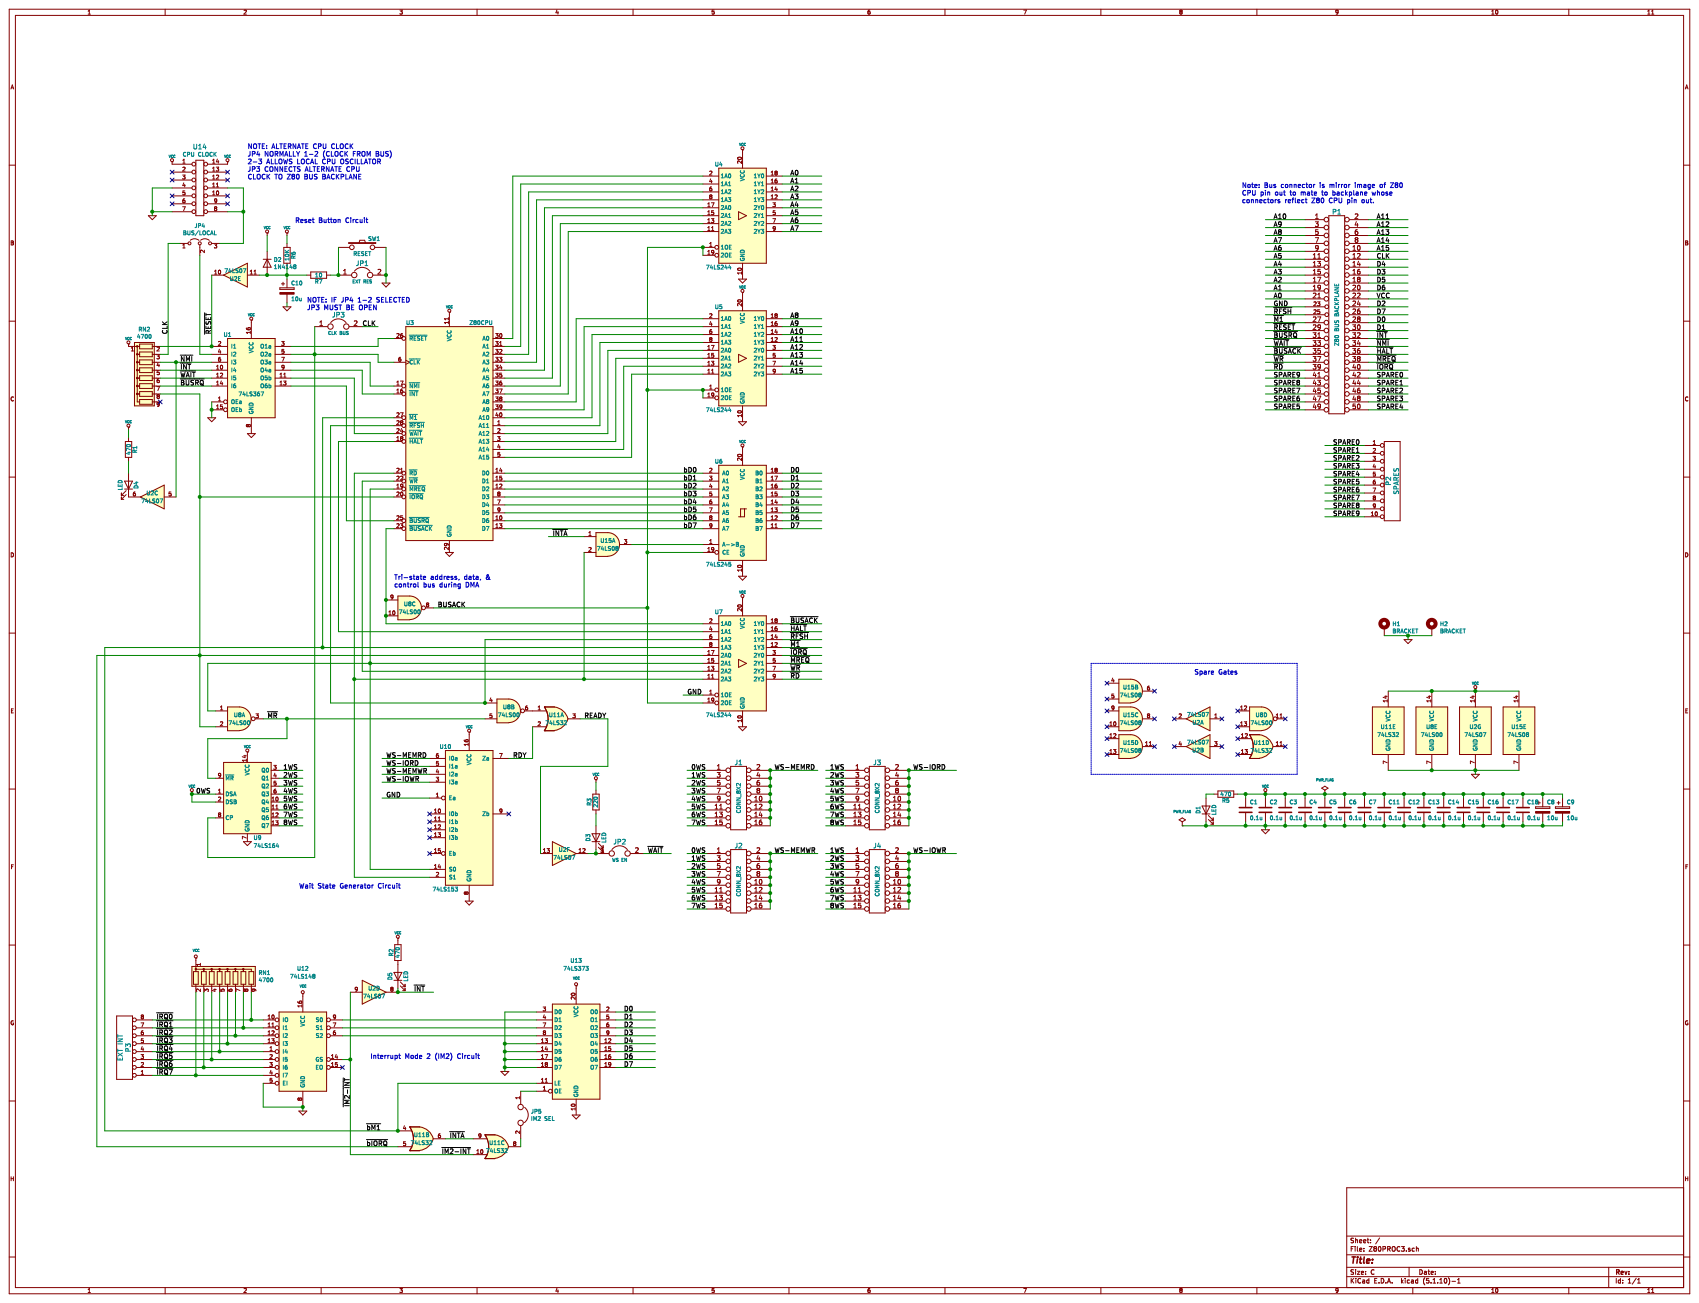
[picture p72: page 1]
