lynchaj/nhyodyne/Z80PPIDE2/Z80PPIDE2-schematic.pdf

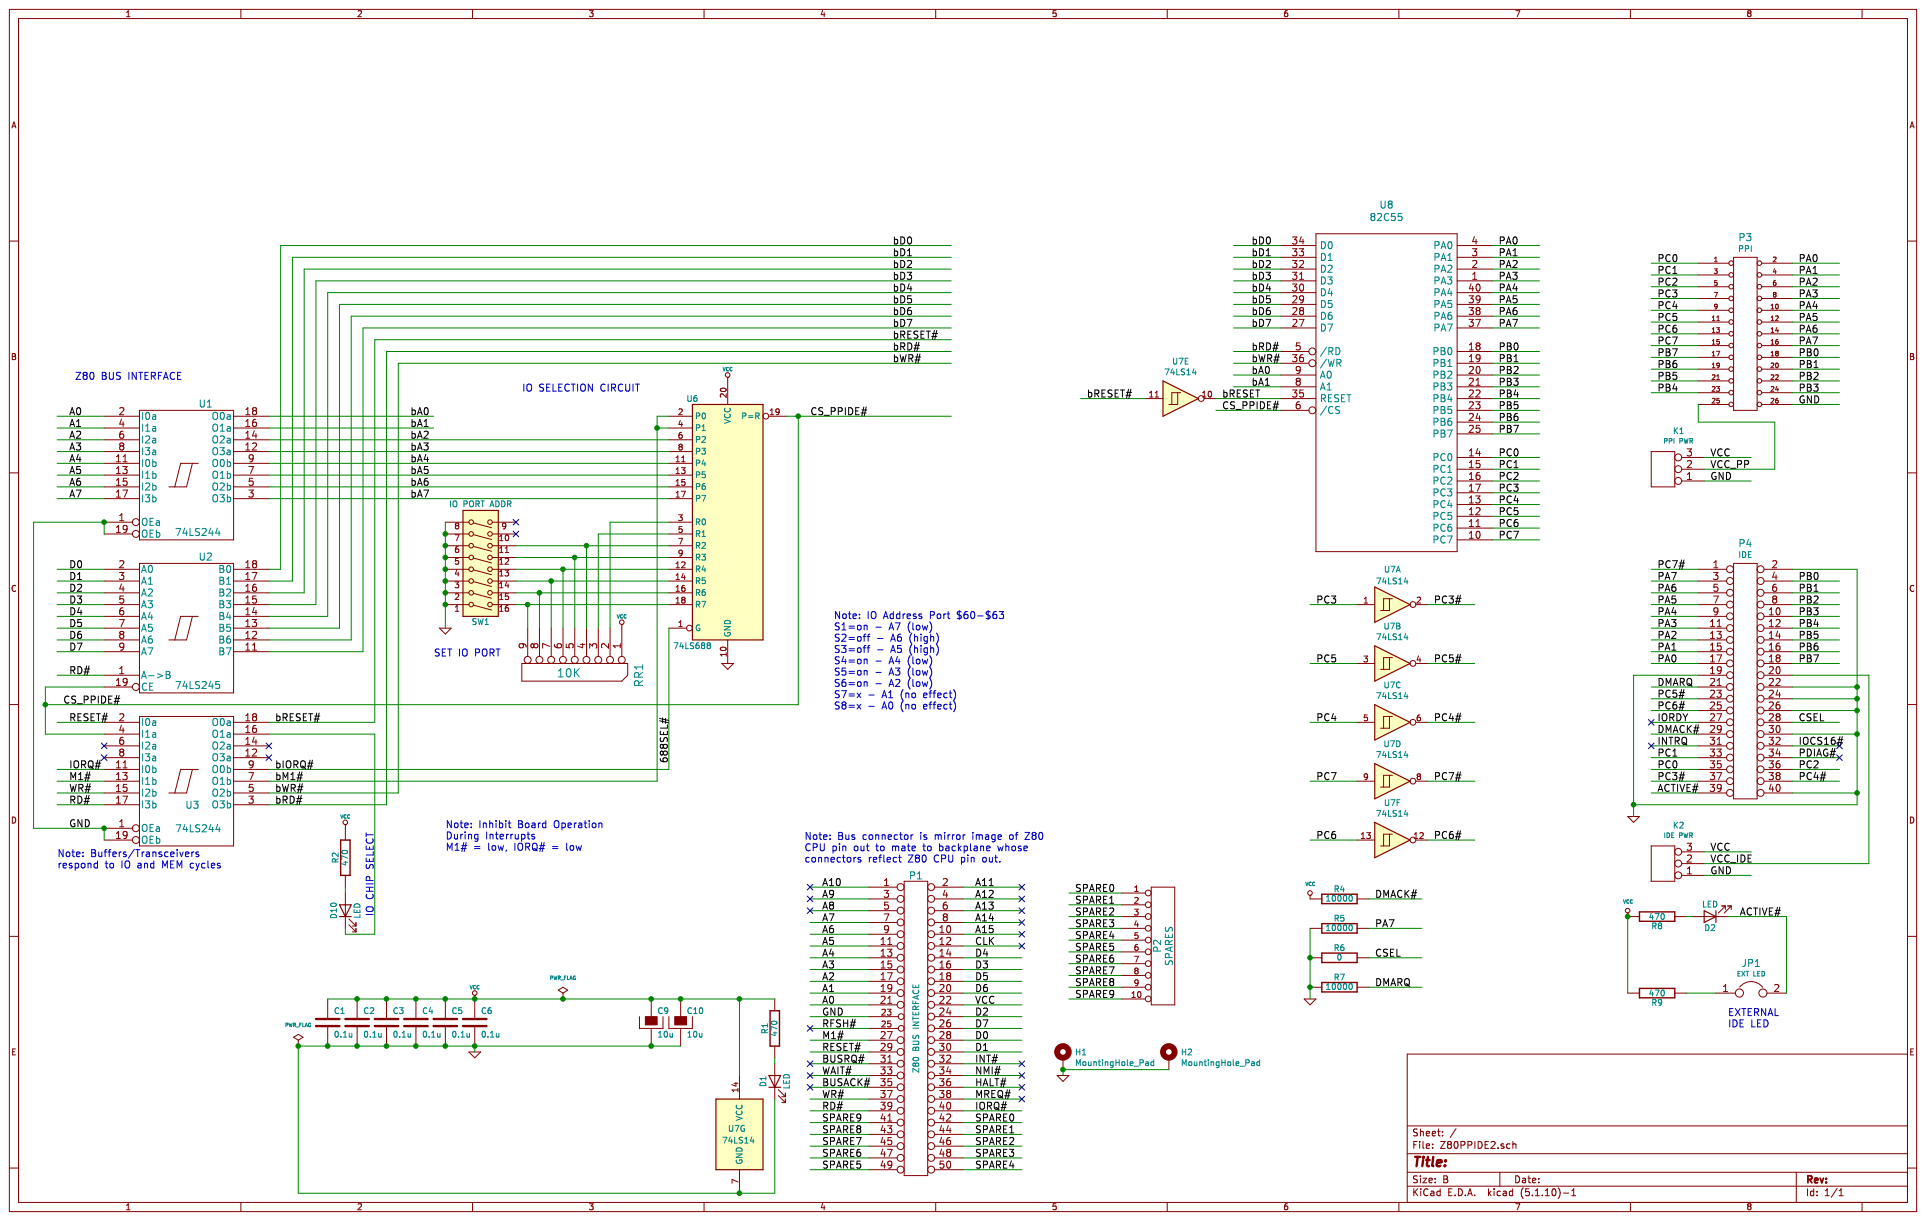
[picture p73: page 1]
