lynchaj/nhyodyne/Z80CLOCK2/Z80CLOCK2-schematic.pdf

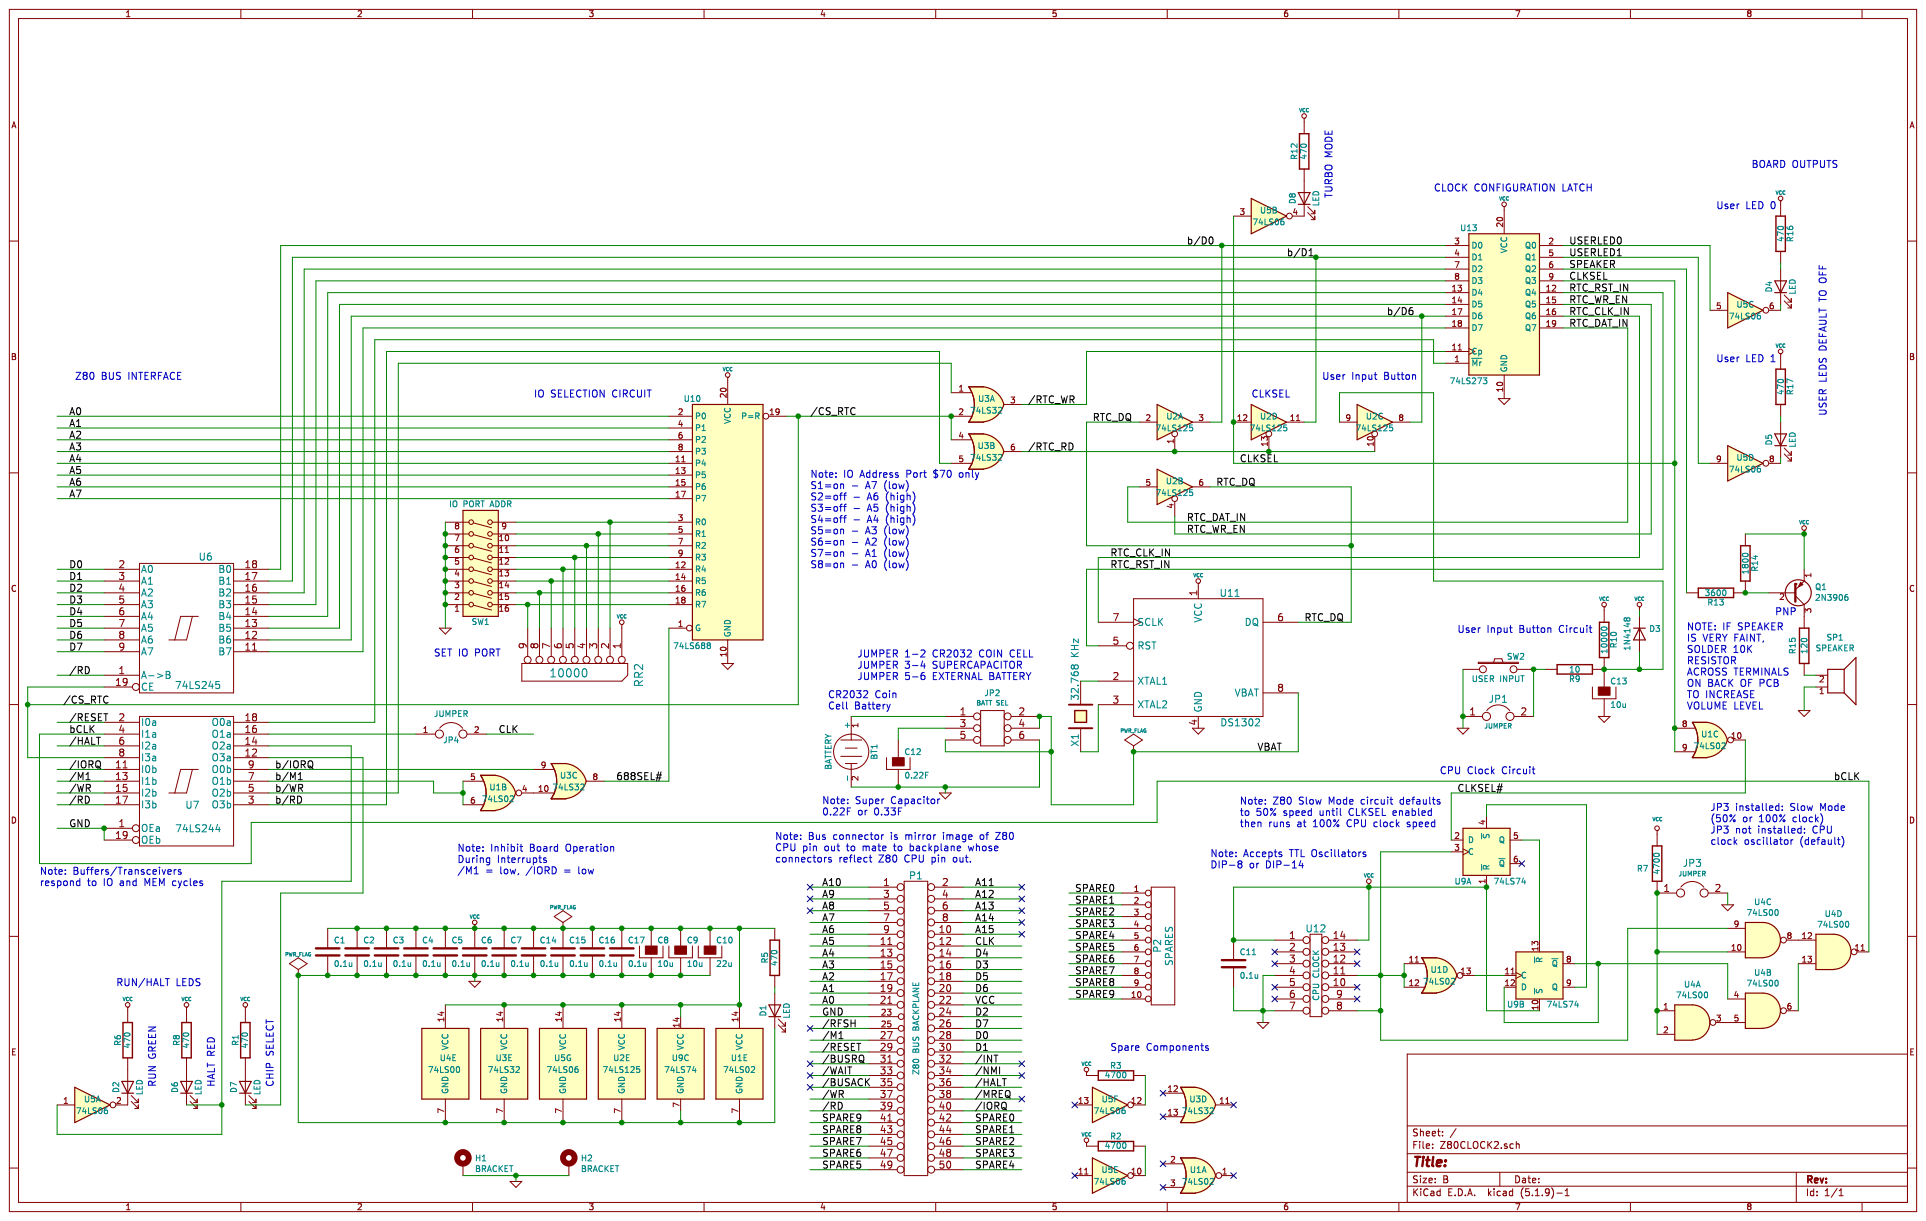
[picture p74: page 1]
