lynchaj/nhyodyne/Z80BCKPLN2/Z80BCKPLN2-schematic.pdf

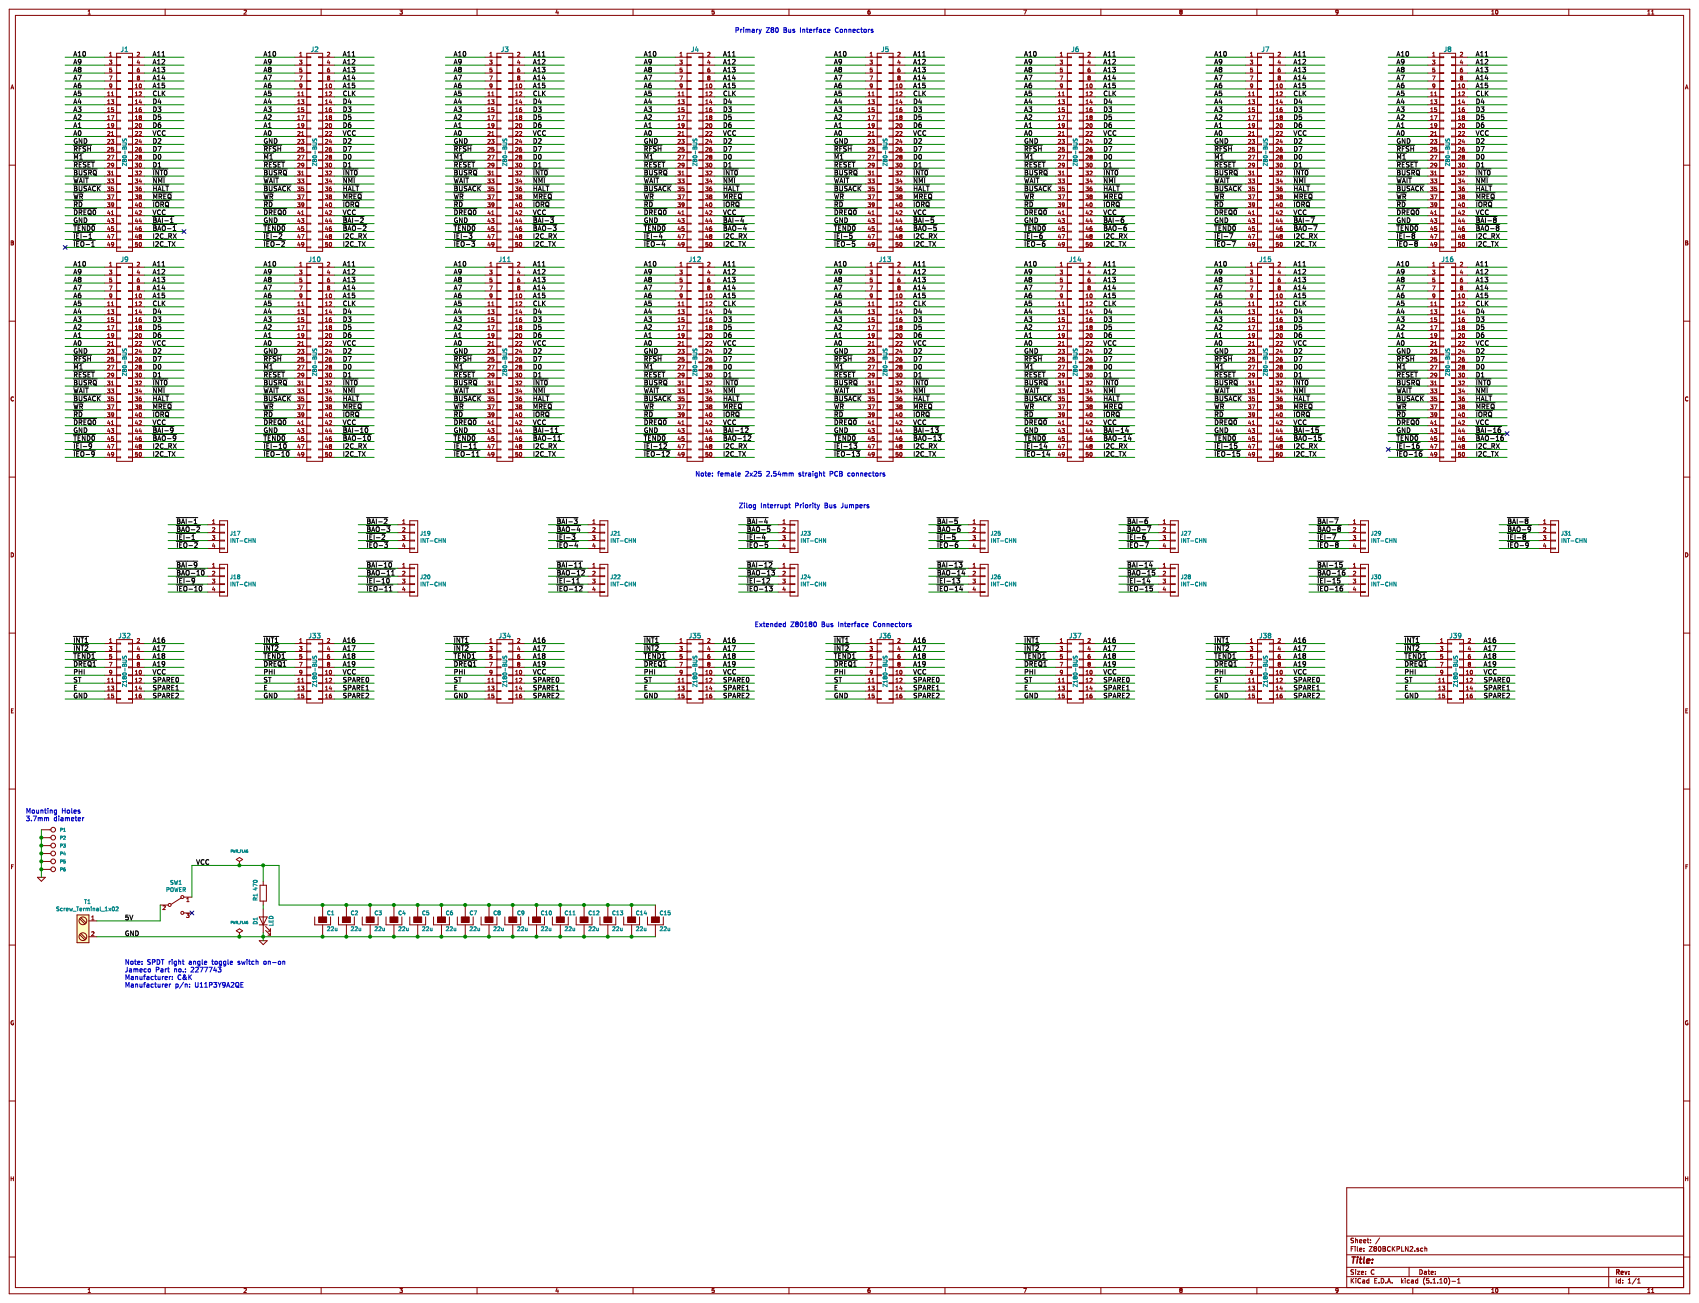
[picture p75: page 1]
