lynchaj/nhyodyne/Z80BCKPLN1/Z80BCKPLN-schematic.pdf

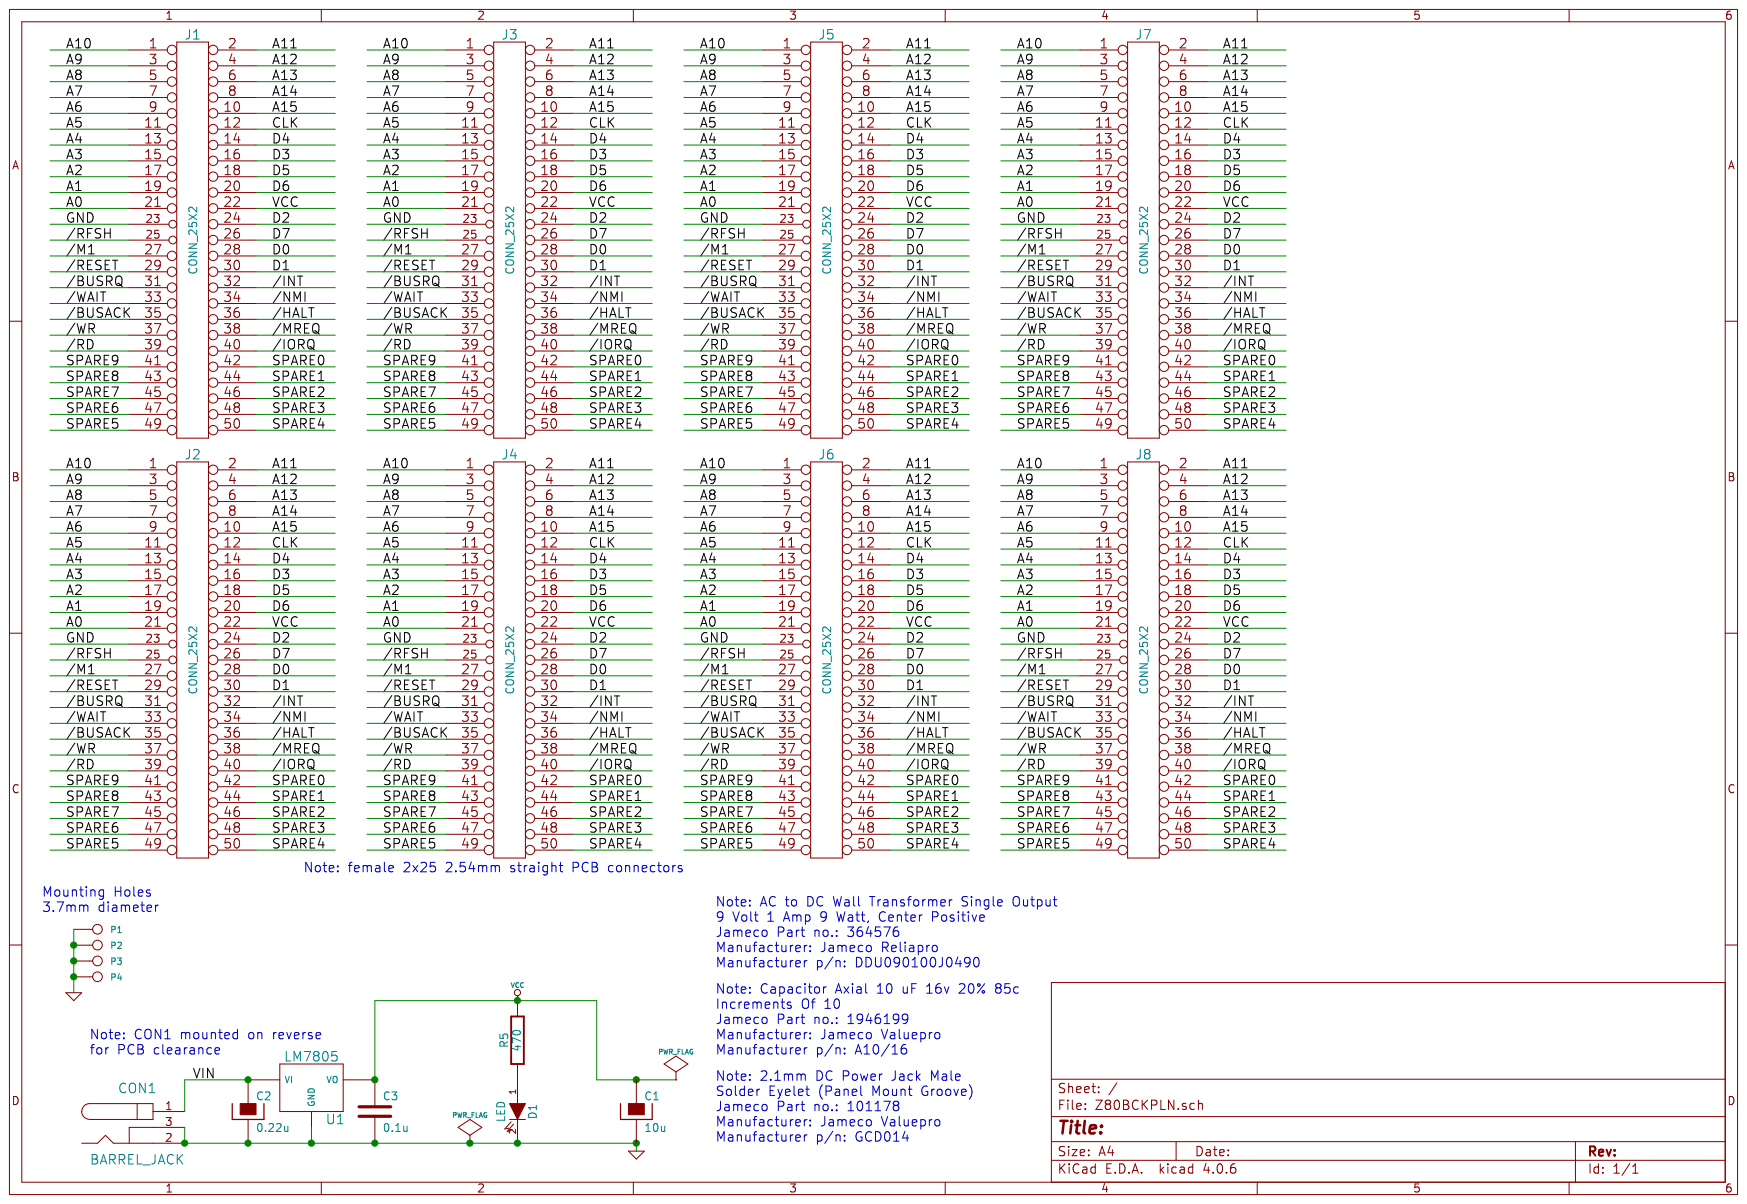
[picture p76: page 1]
