lynchaj/nhyodyne/Z80ESP/HARDWARE/z80esp-pcb-V1.pdf

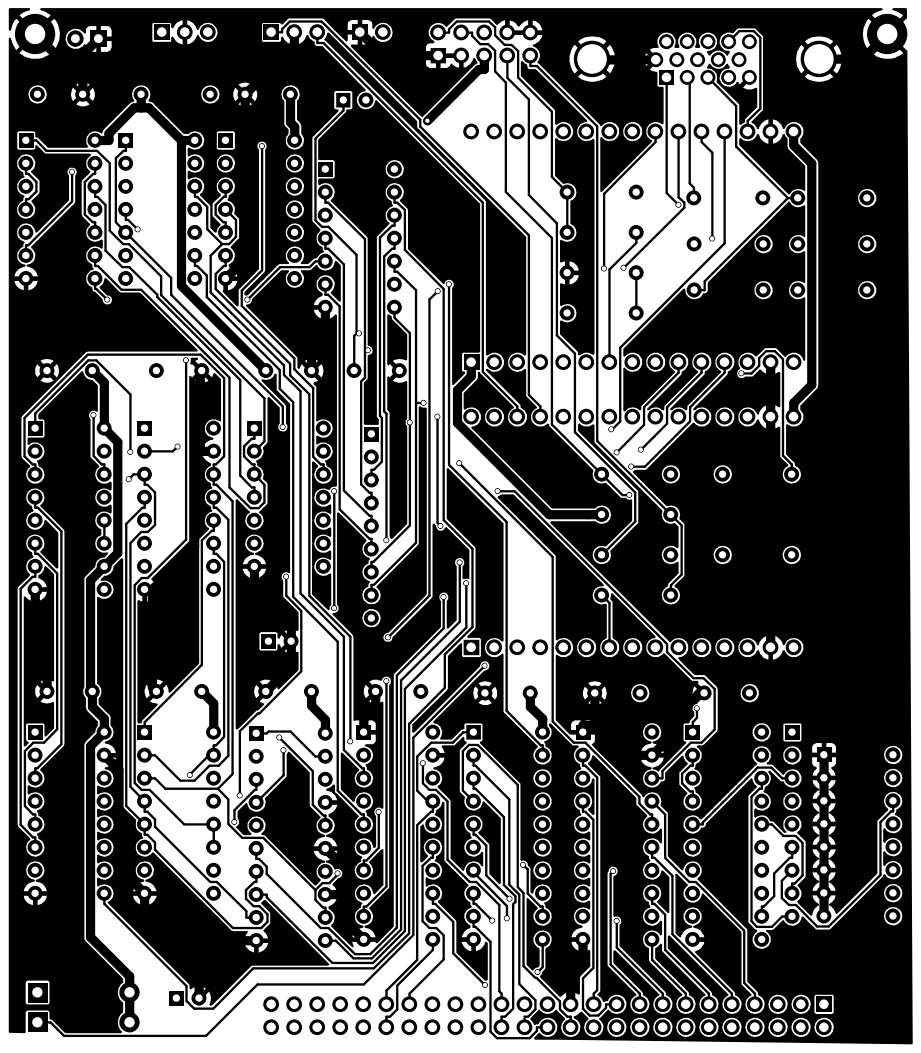
[picture p77: page 1]

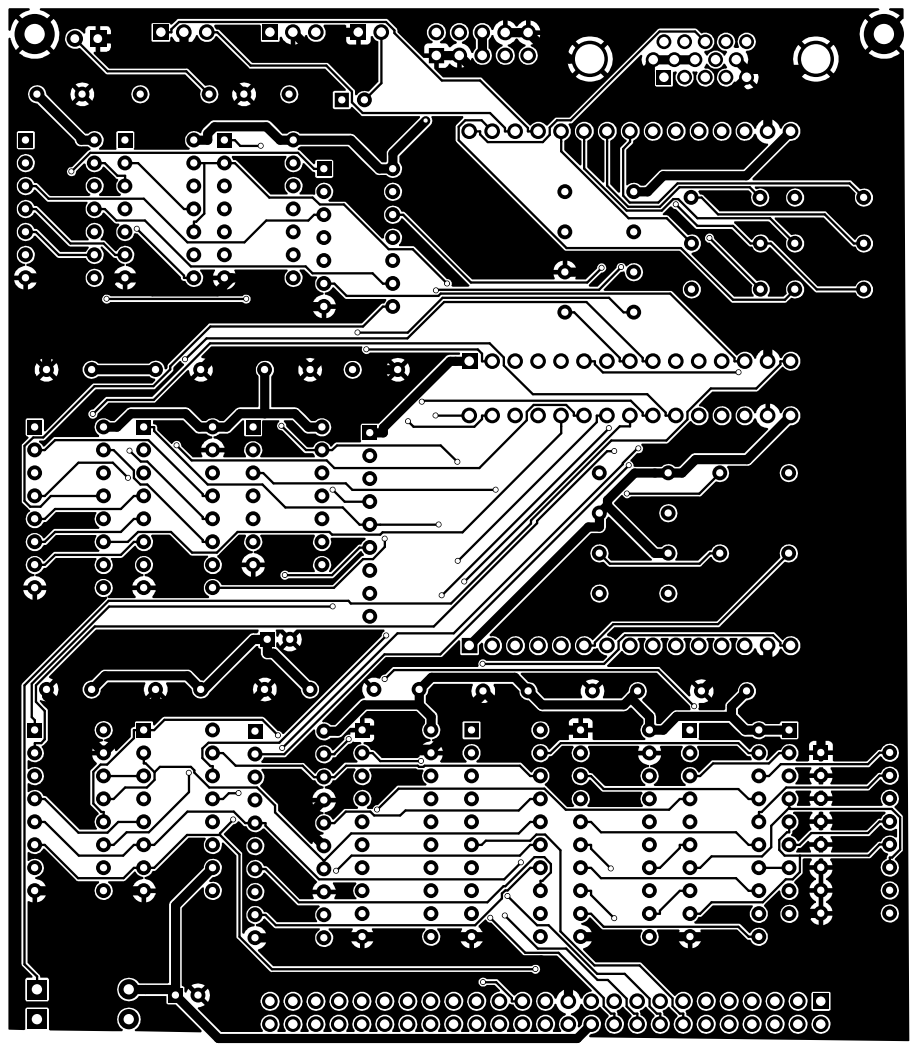
[picture p78: page 2]

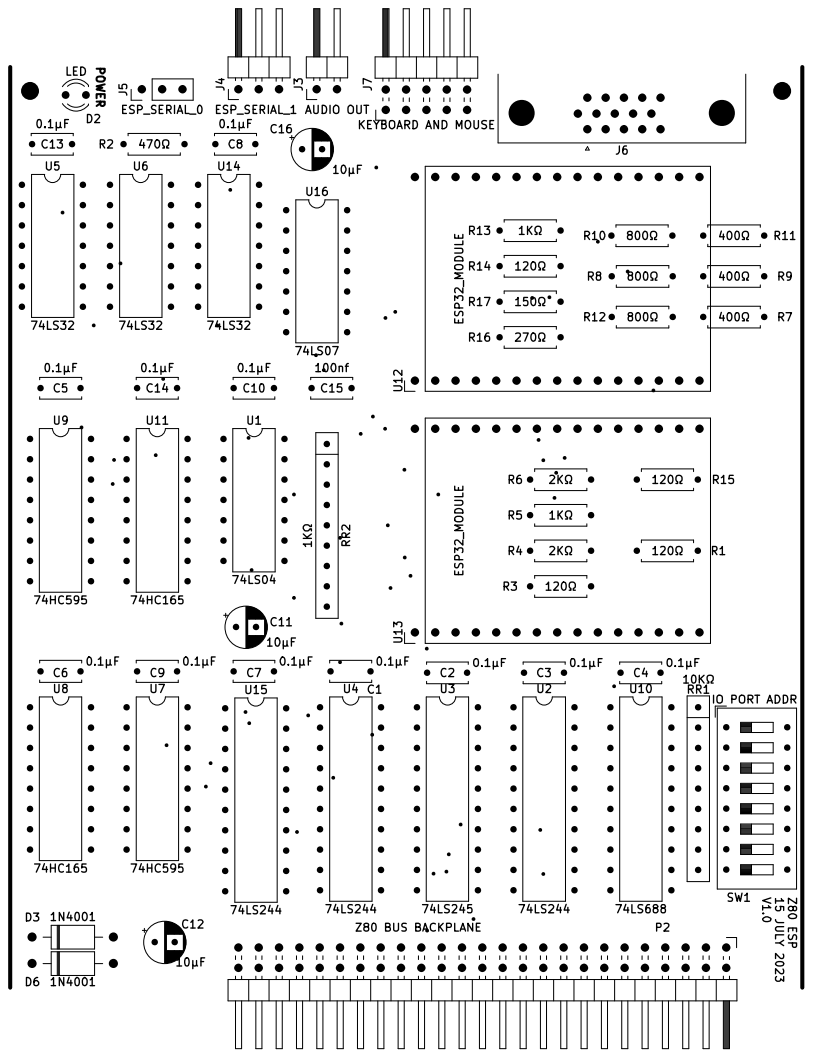
[picture p79: page 3]

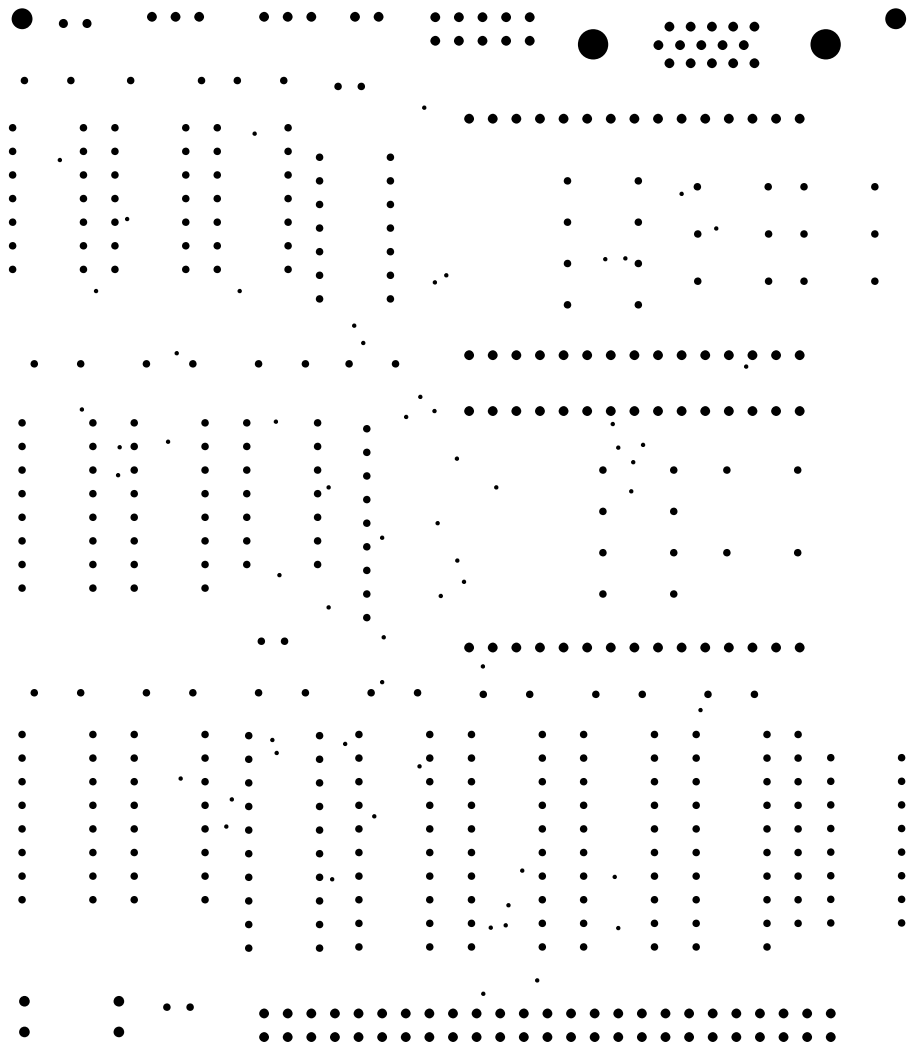
[picture p80: page 4]

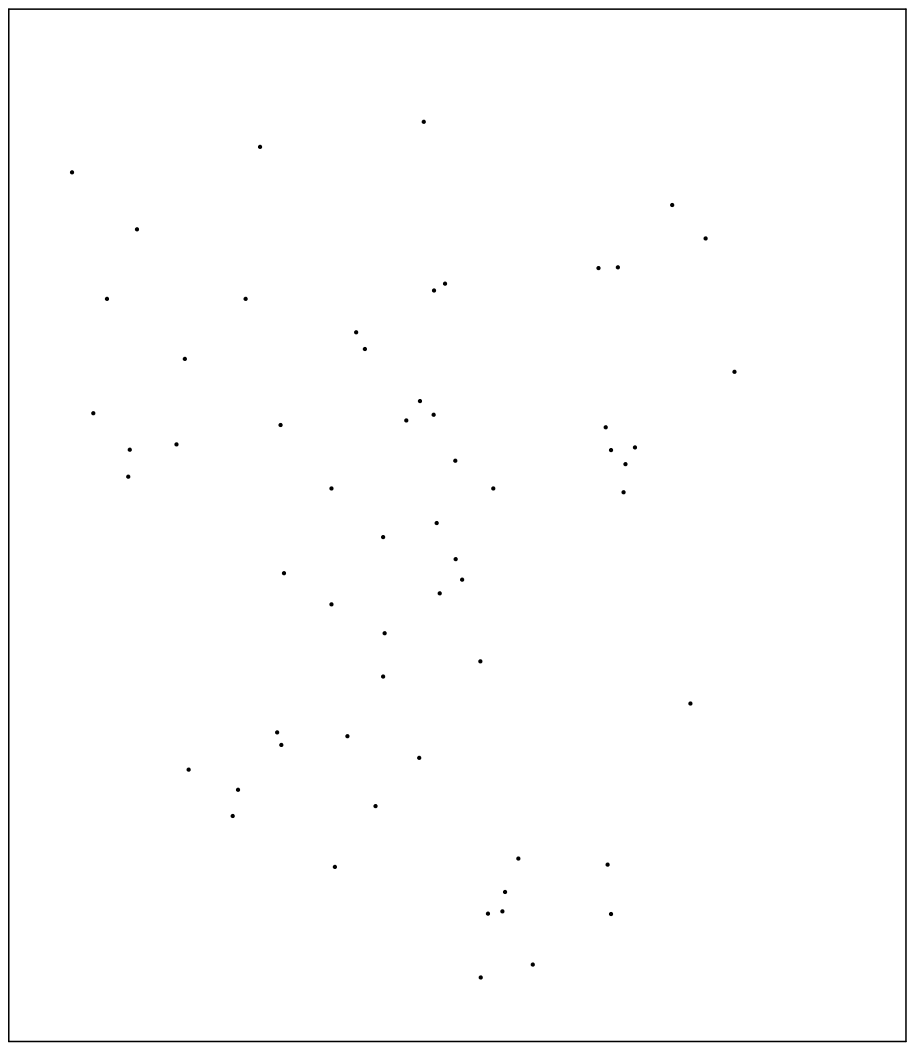
[picture p81: page 5]

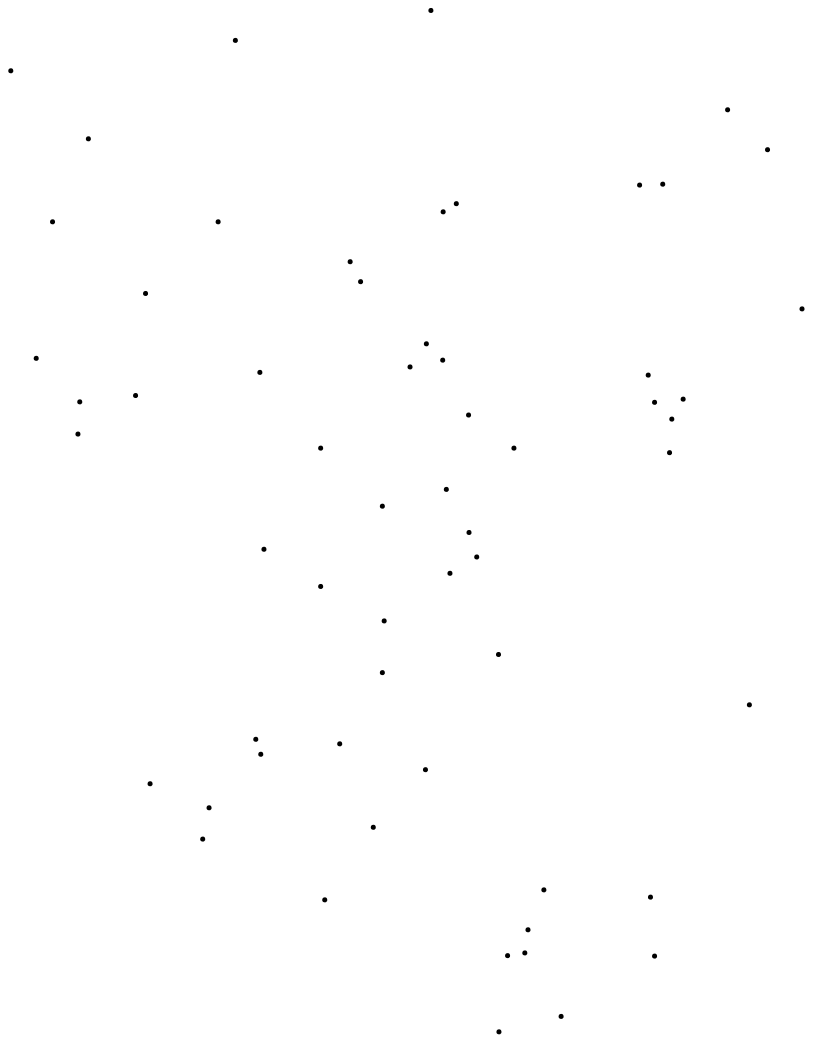
[picture p82: page 6]

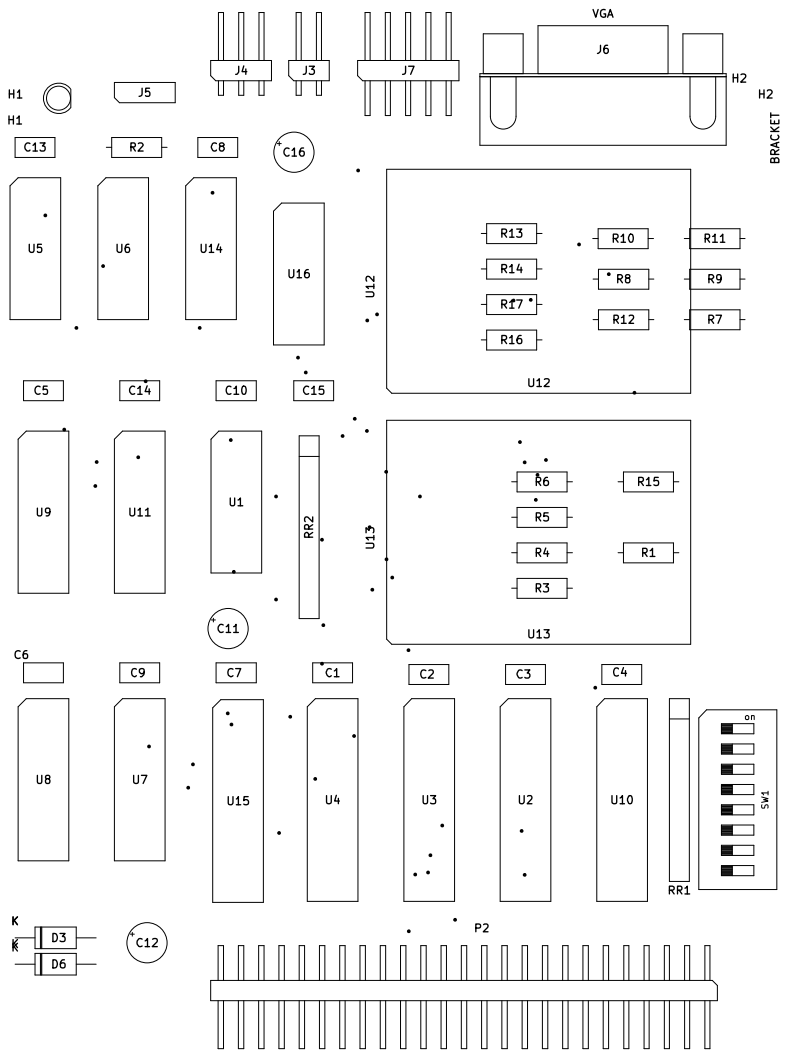
[picture p83: page 7]
