lynchaj/nhyodyne/Z80ESP/HARDWARE/z80esp-schematic-V1.pdf

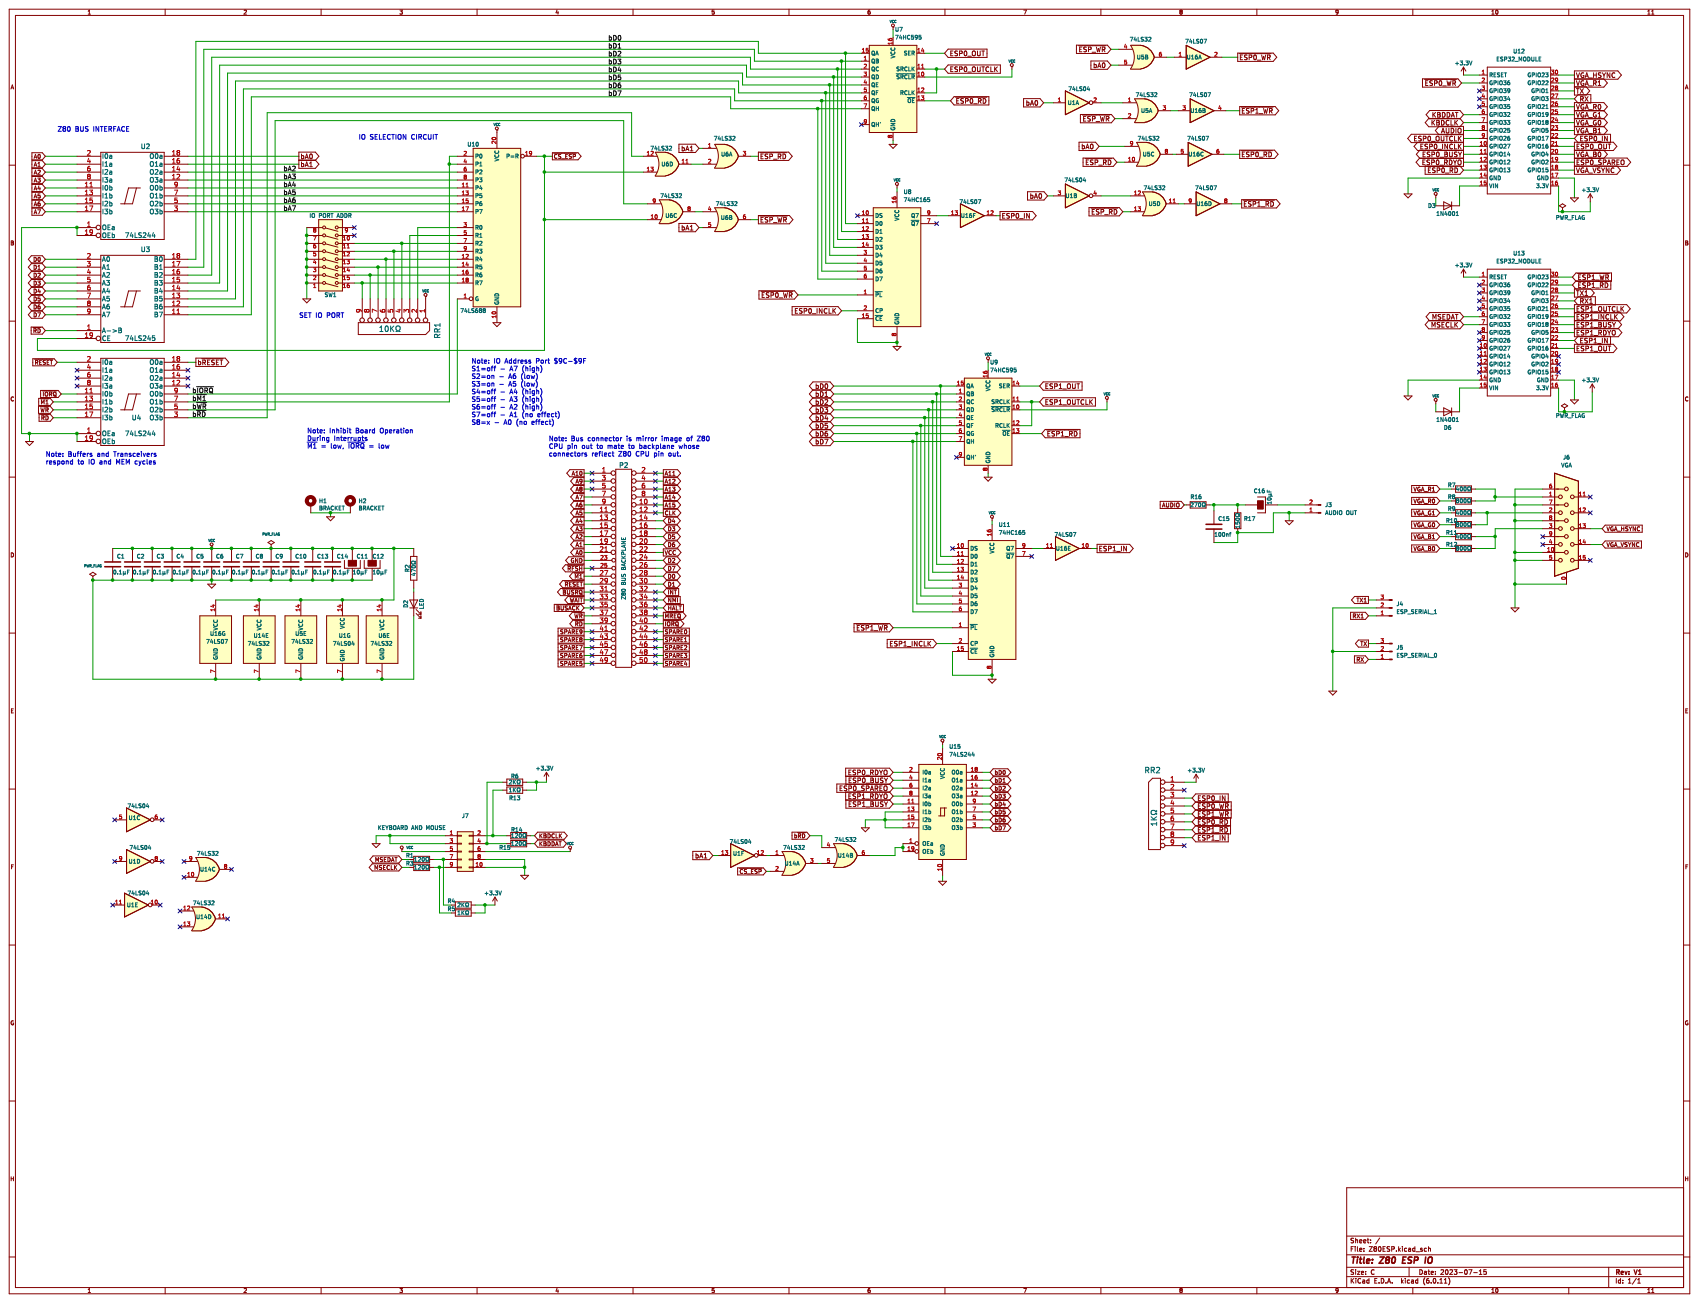
[picture p84: page 1]
