lynchaj/nhyodyne/6502PROC/hardware/MBC65C02_PCB_V1.4.pdf

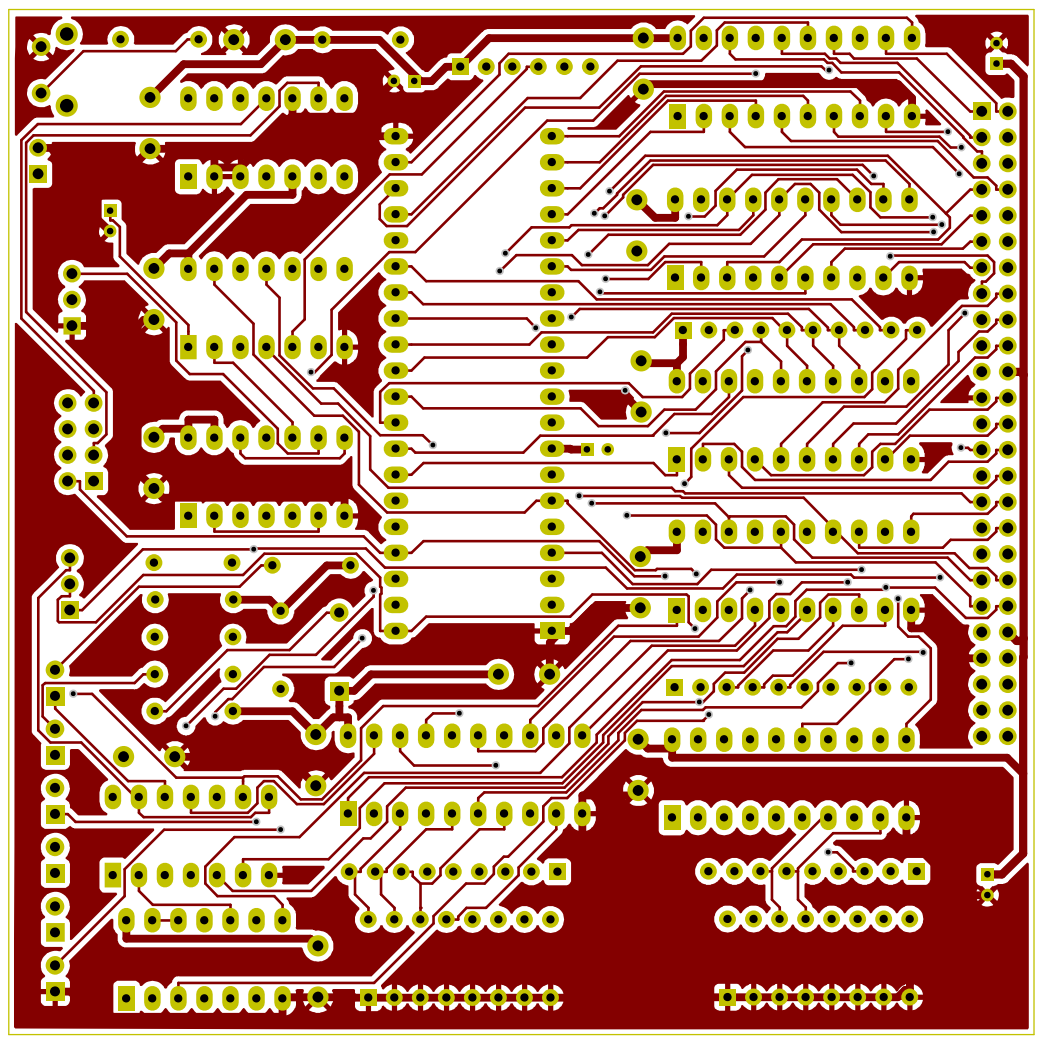
[picture p85: page 1]

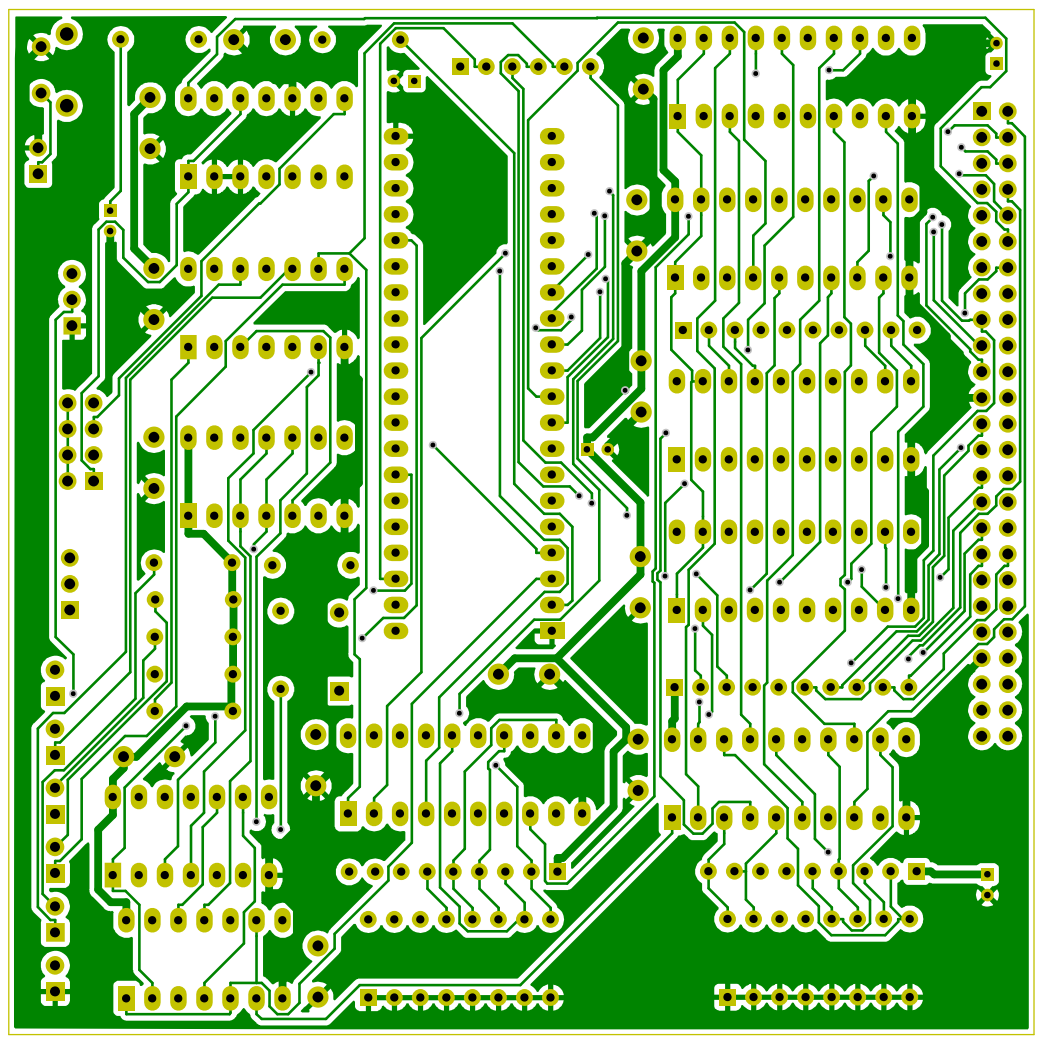
[picture p86: page 2]

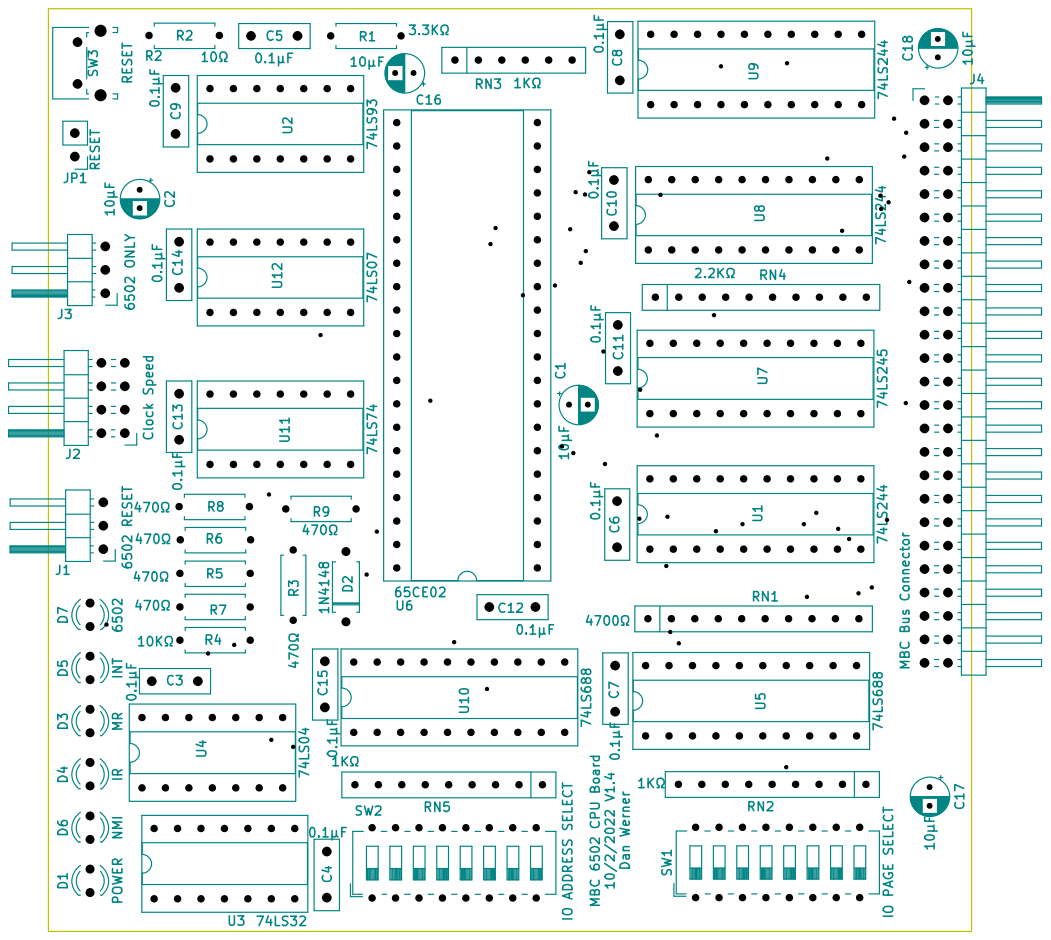
[picture p87: page 3]

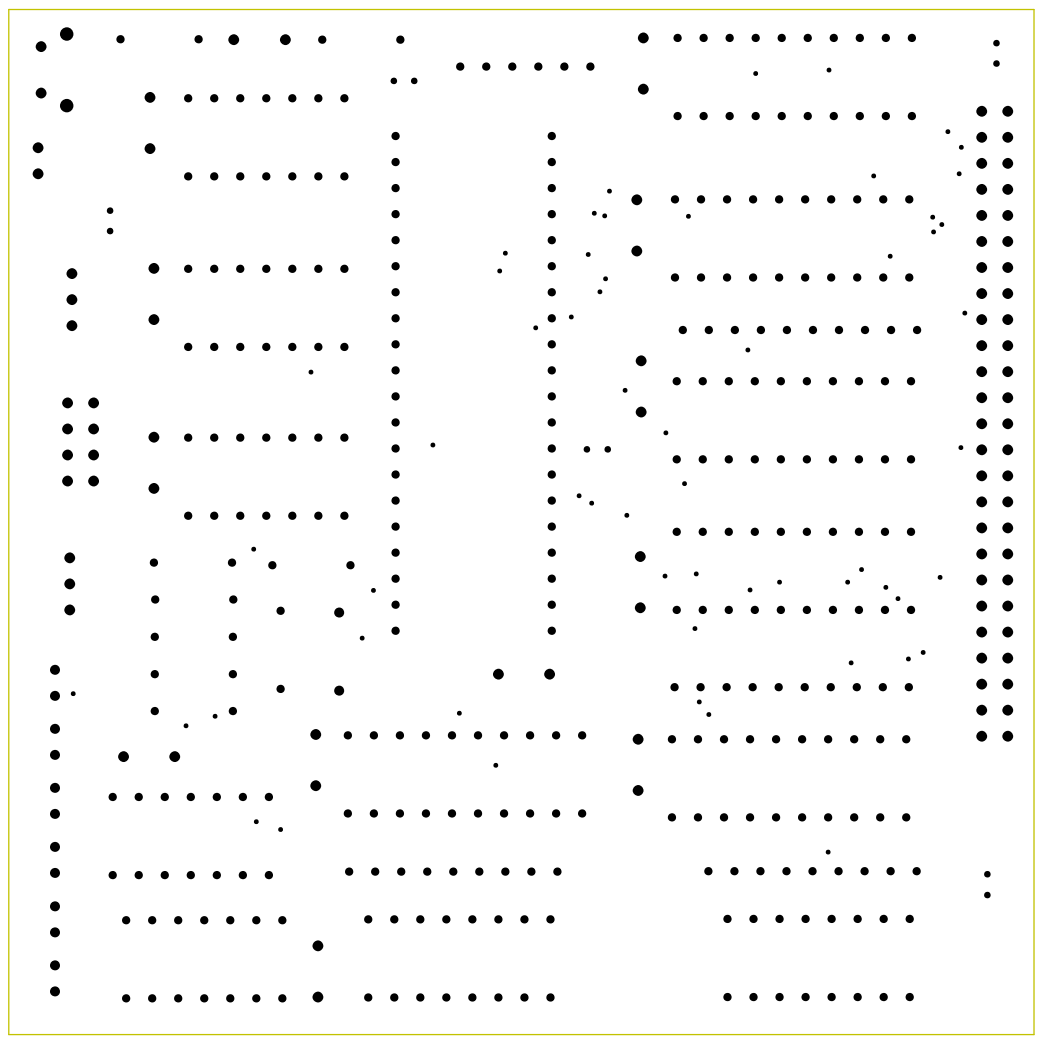
[picture p88: page 4]

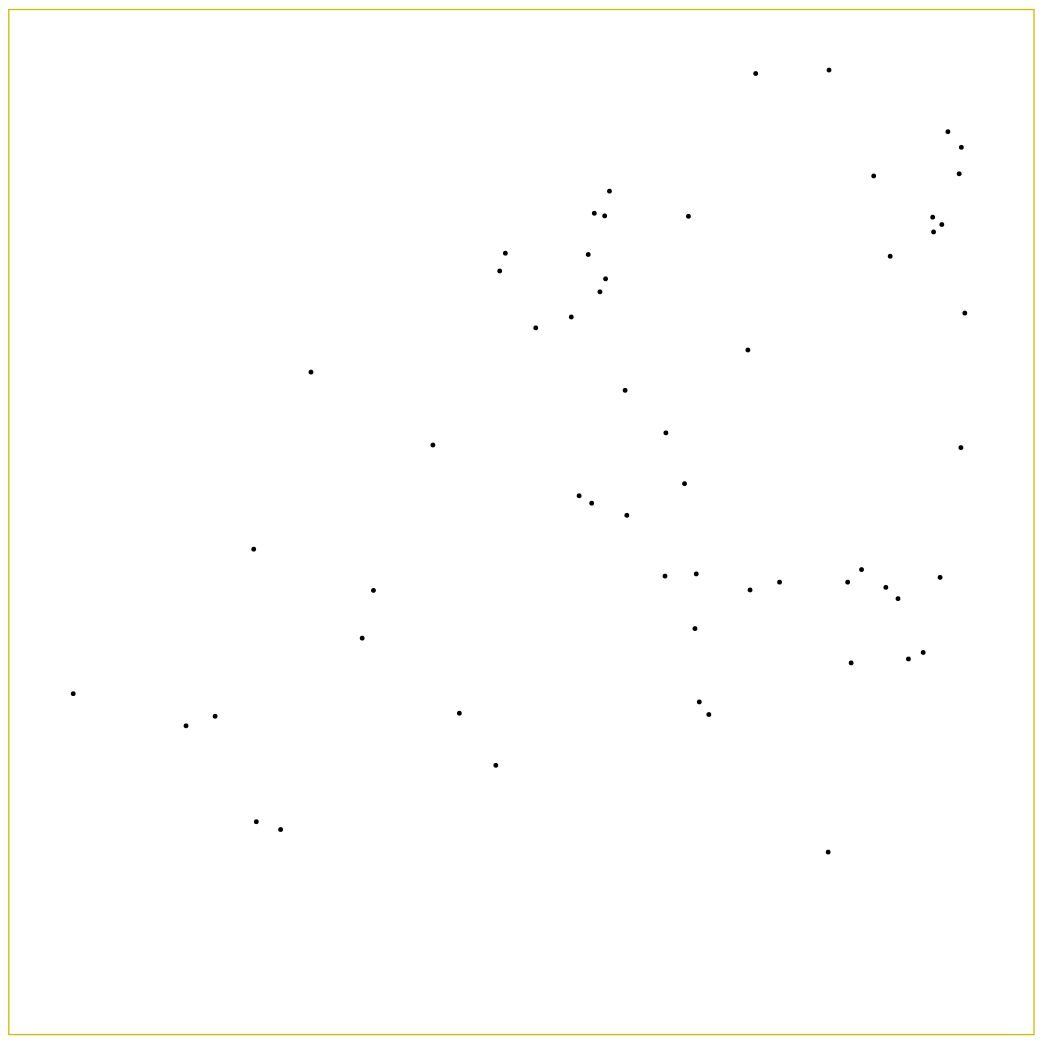
[picture p89: page 5]
