lynchaj/nhyodyne/6502PROC/hardware/MBC65C02_V1.4.pdf

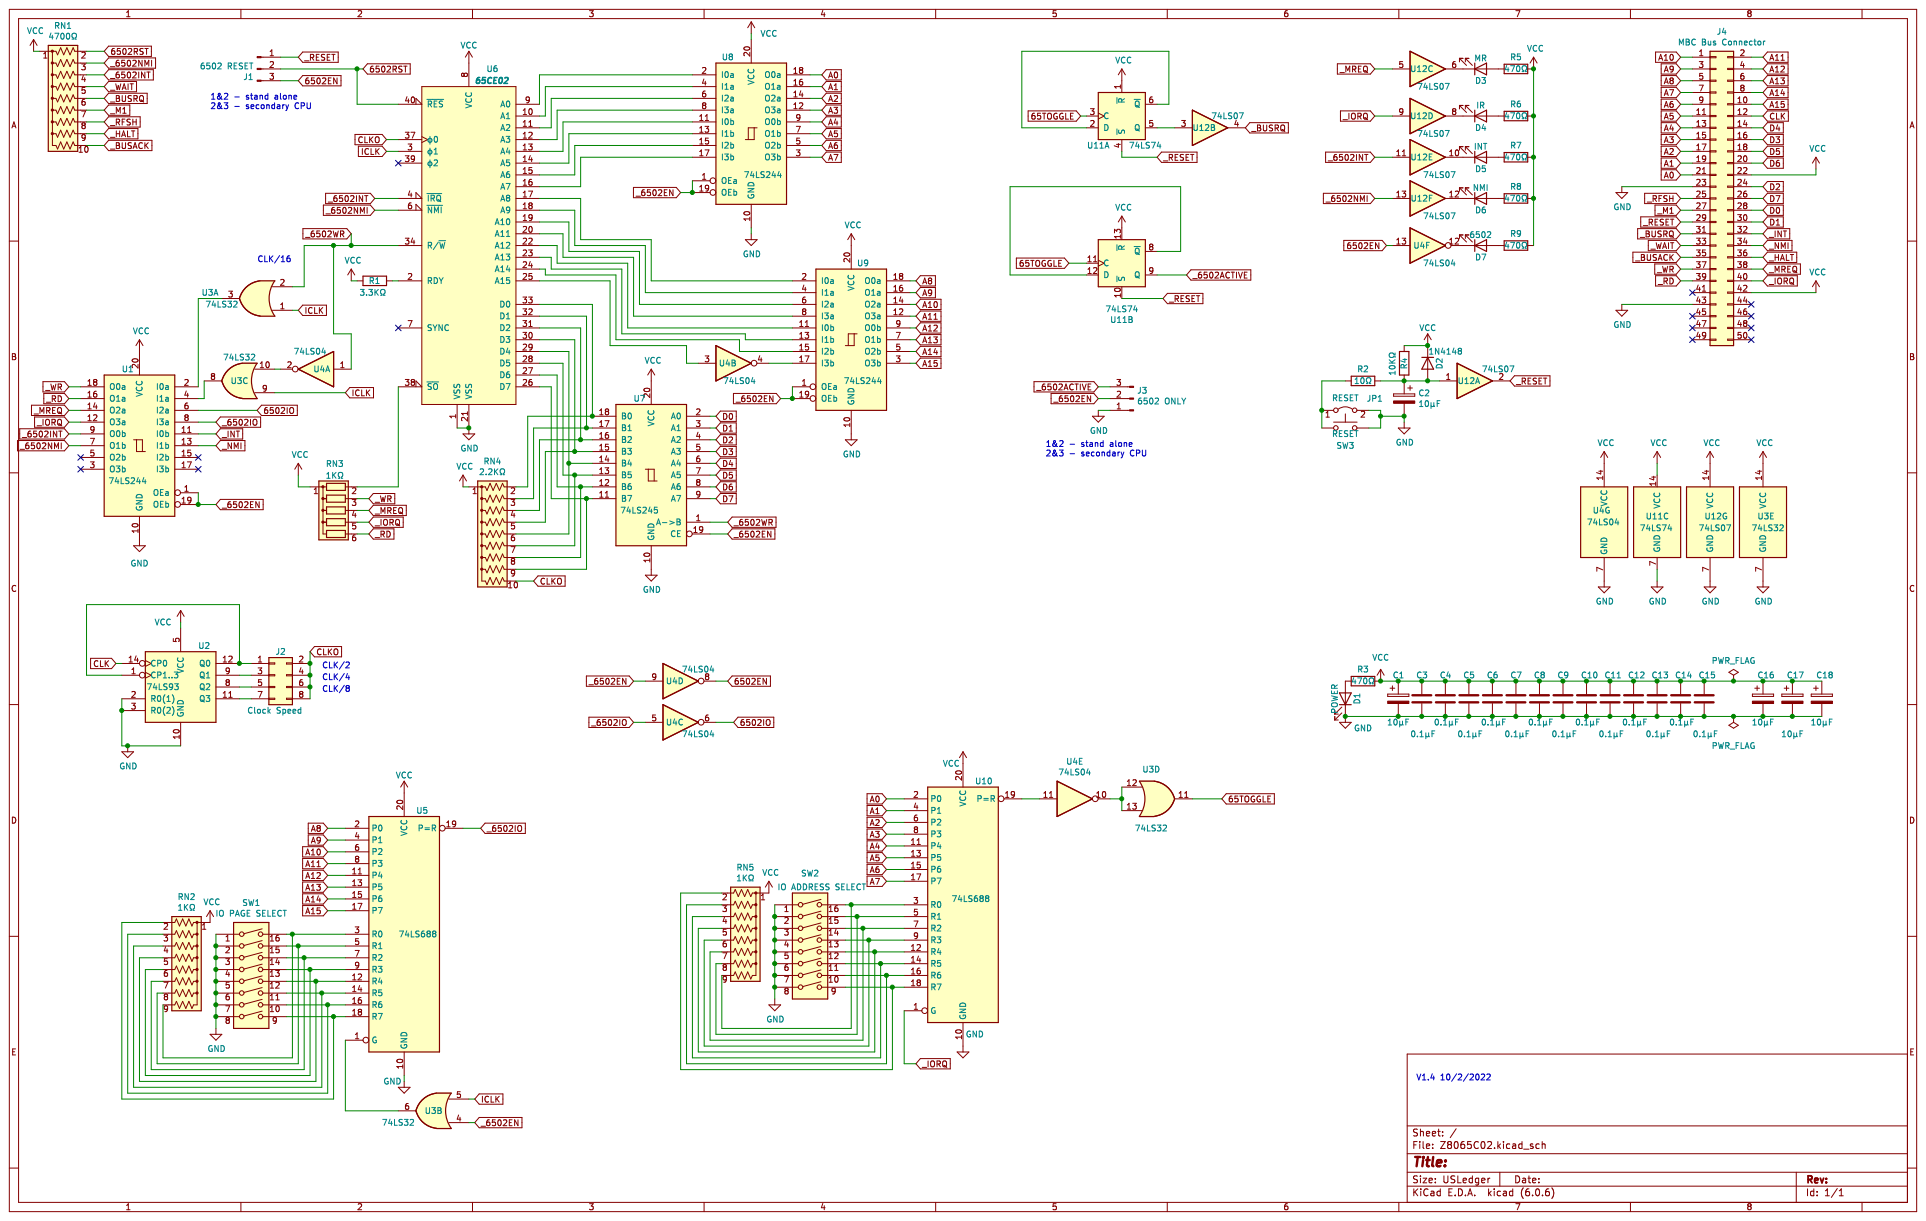
[picture p90: page 1]
