lynchaj/nhyodyne/6809PROC/hardware/6809Proc_PCB_1.2.pdf

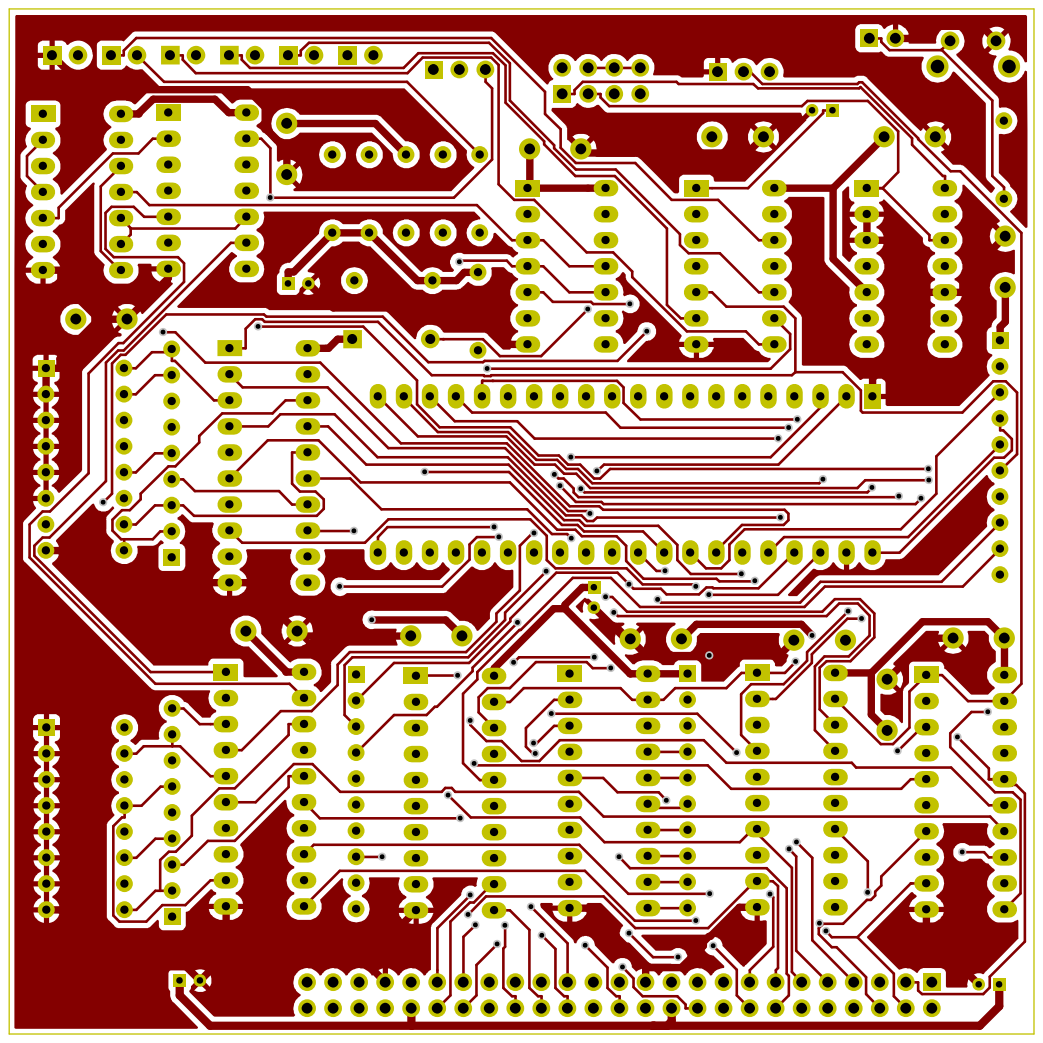
[picture p91: page 1]

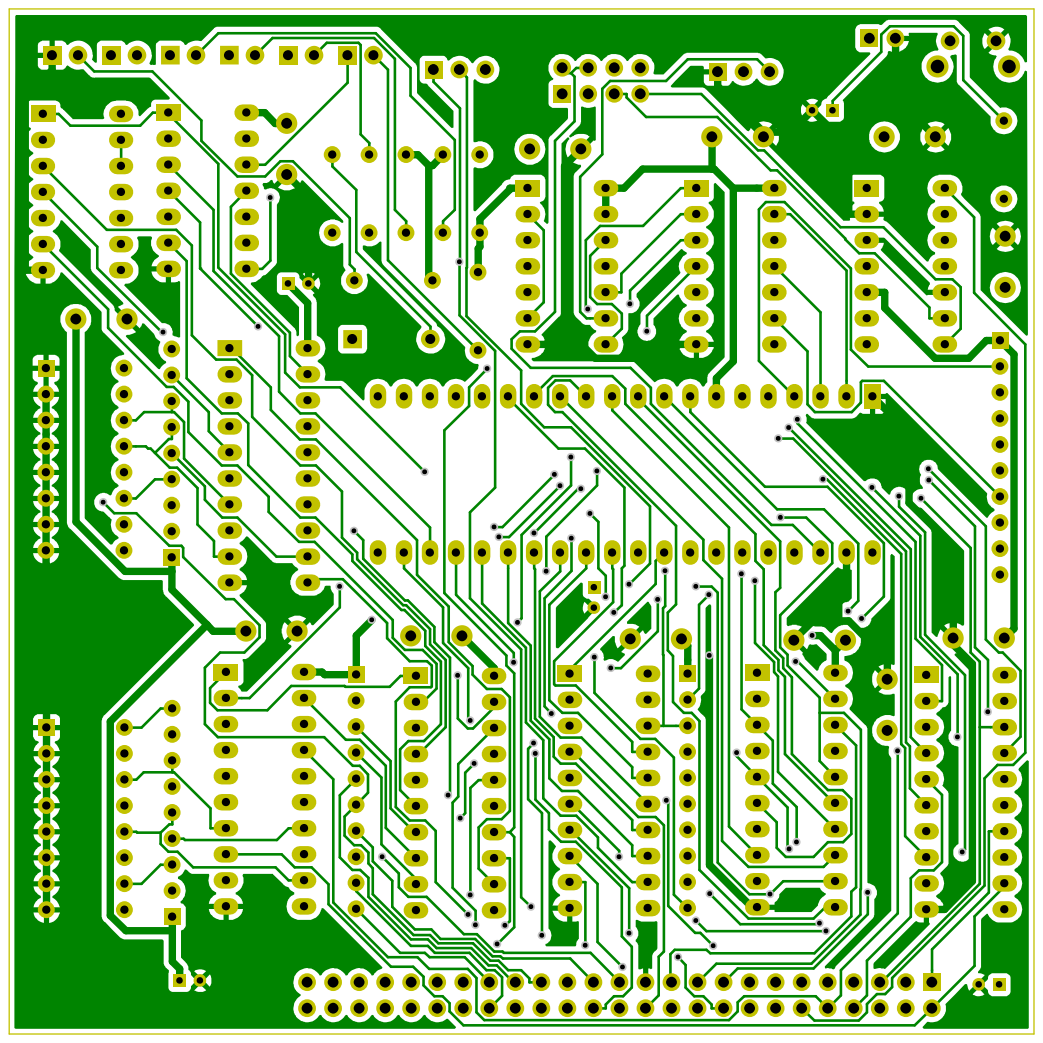
[picture p92: page 2]

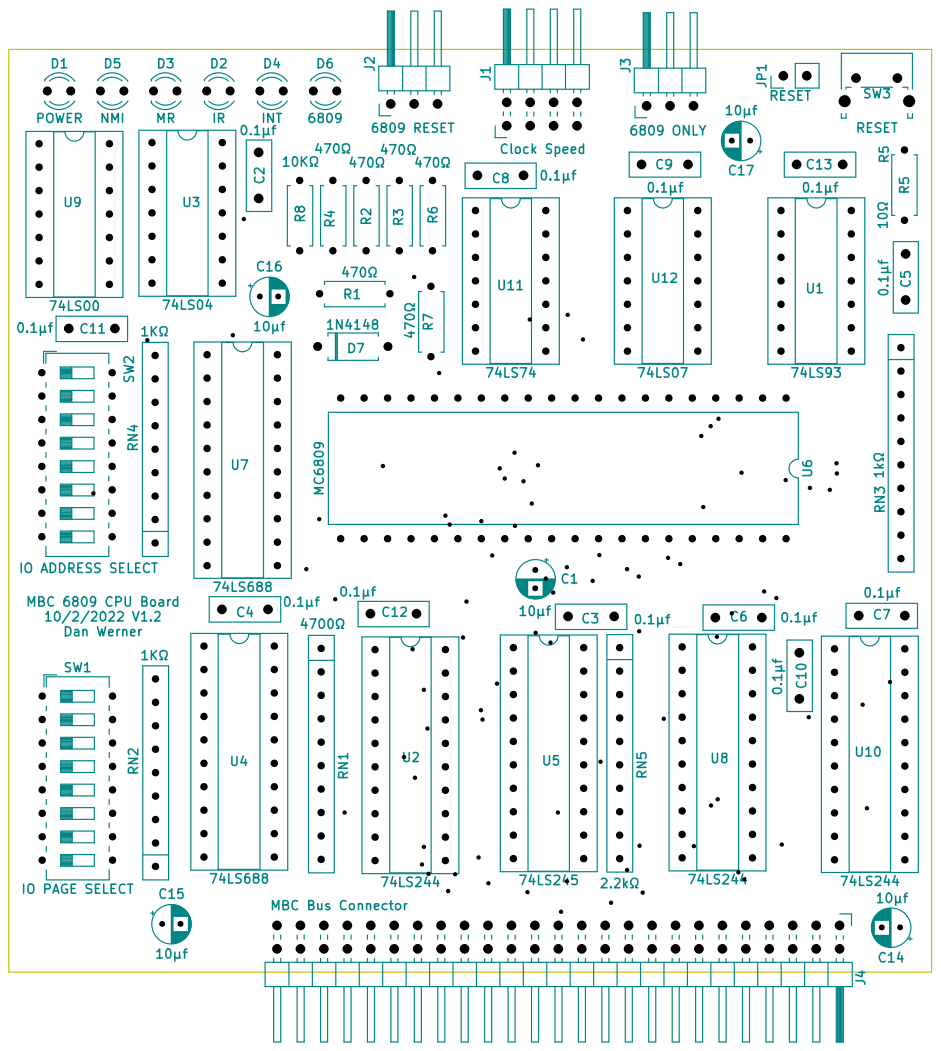
[picture p93: page 3]

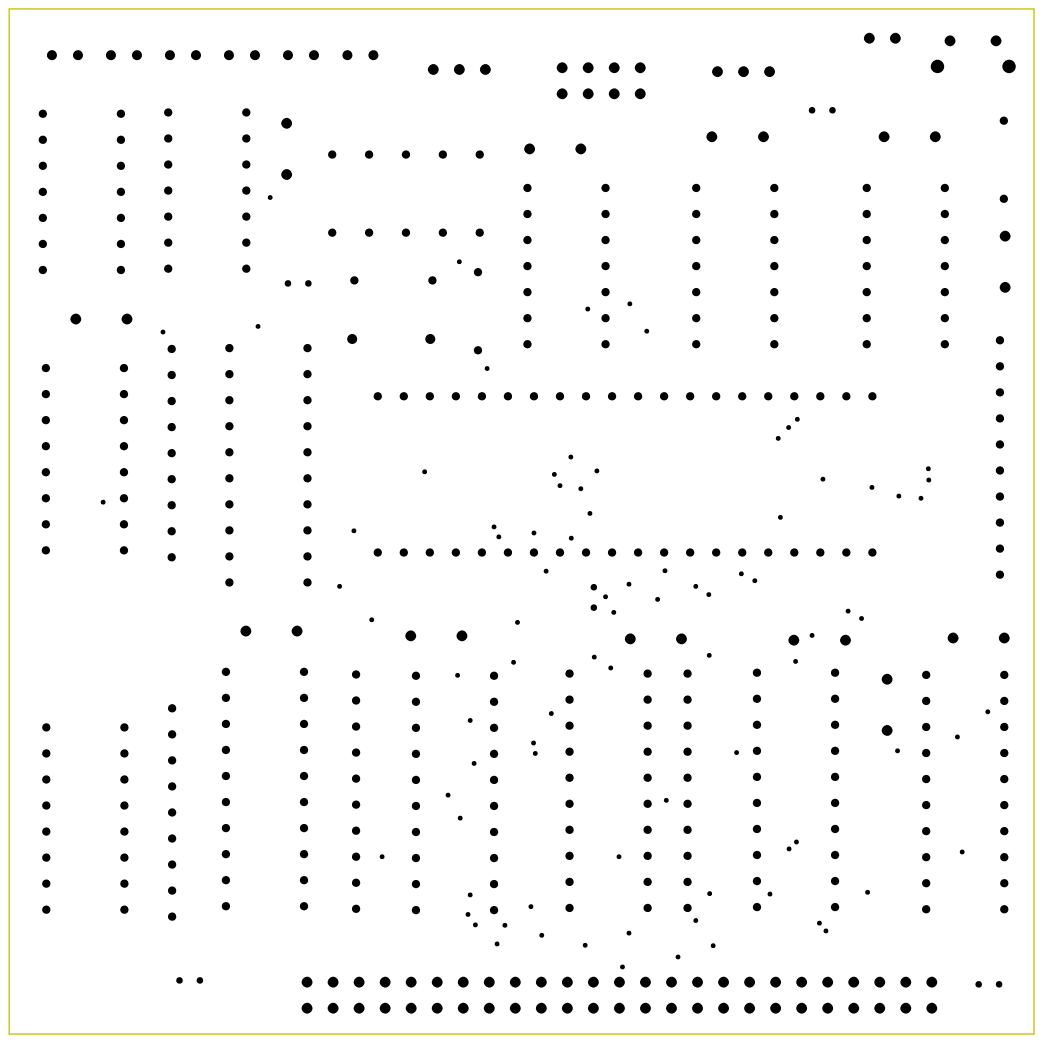
[picture p94: page 4]

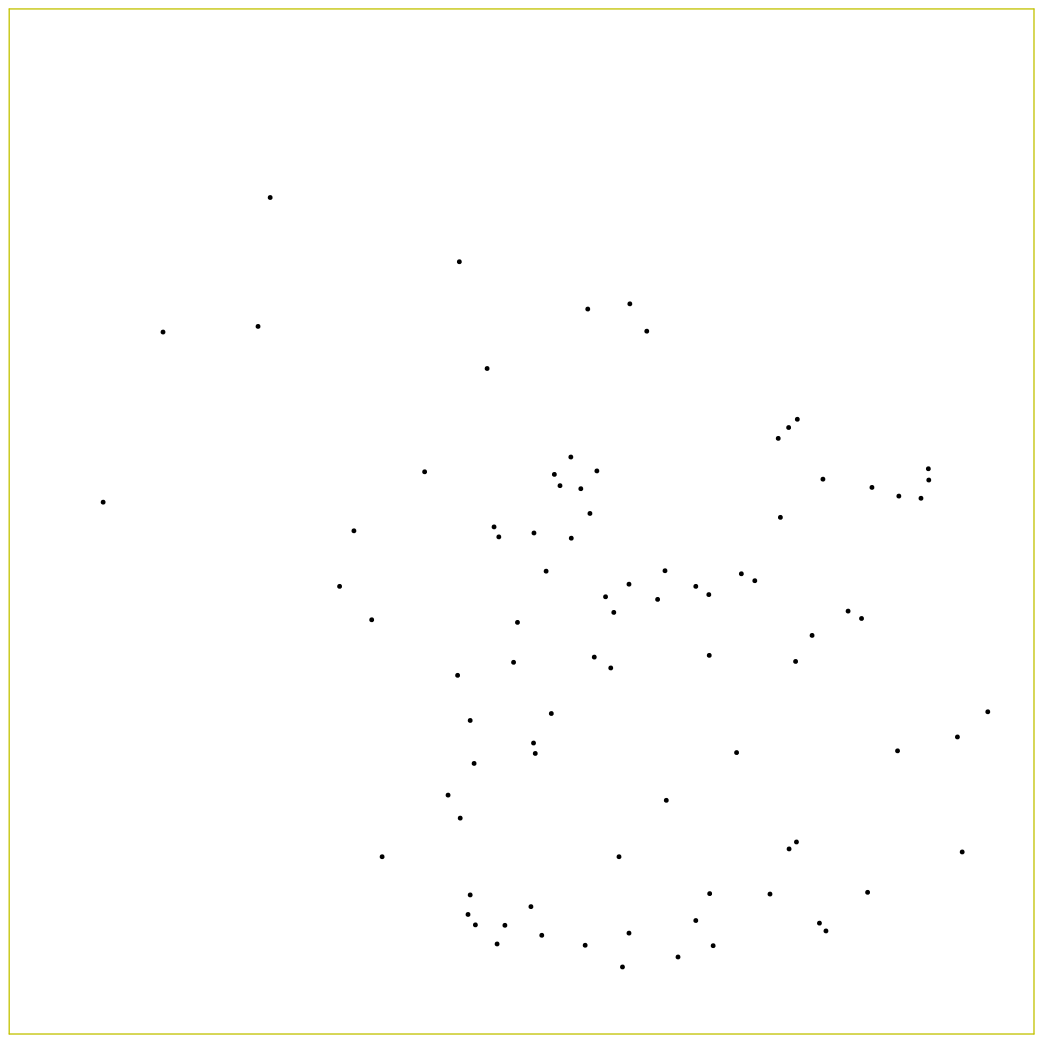
[picture p95: page 5]
