lynchaj/nhyodyne/6809PROC/hardware/6809Proc_Schematic_1.2.pdf

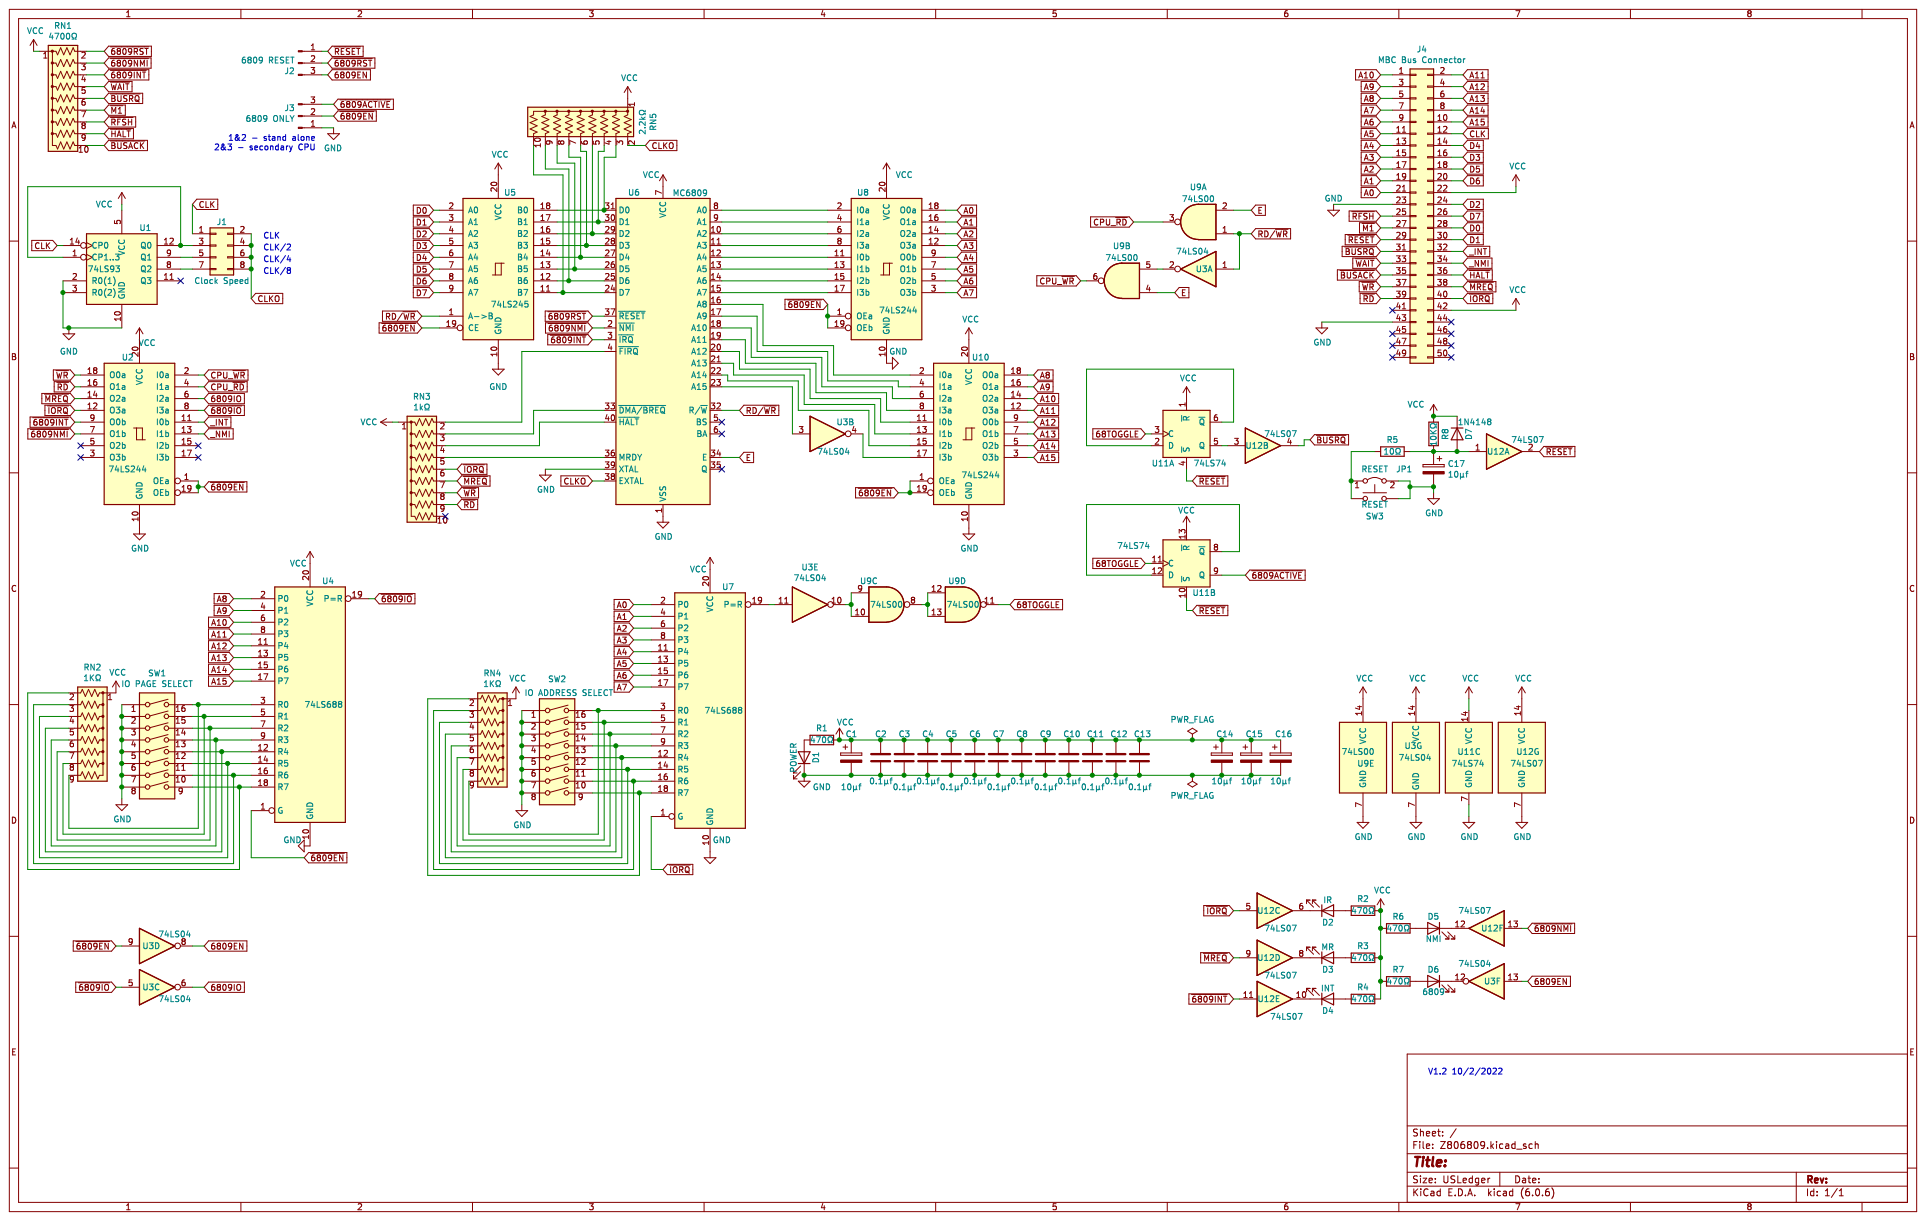
[picture p96: page 1]
