lynchaj/nhyodyne/6809PROC/hardware/6809Proc_PCB_1.1.pdf

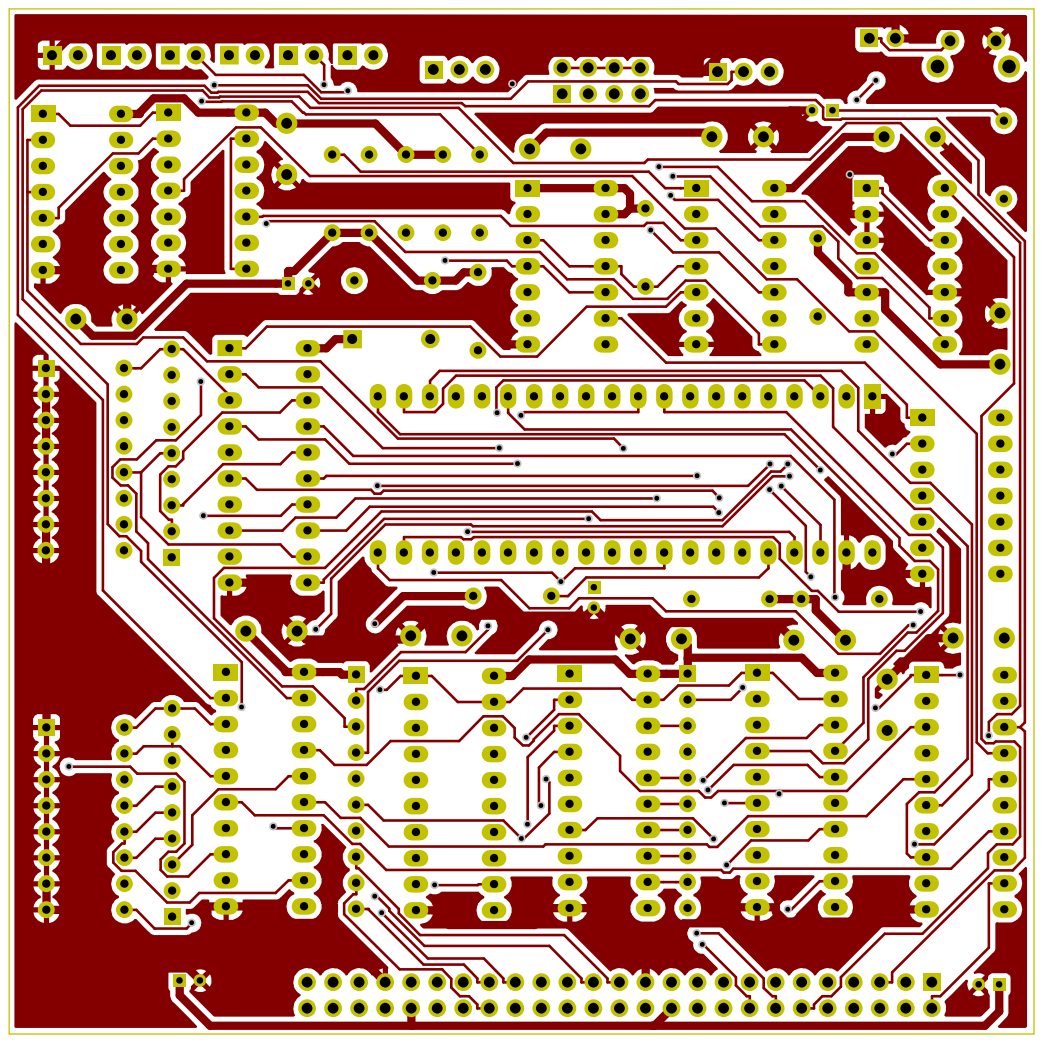
[picture p97: page 1]

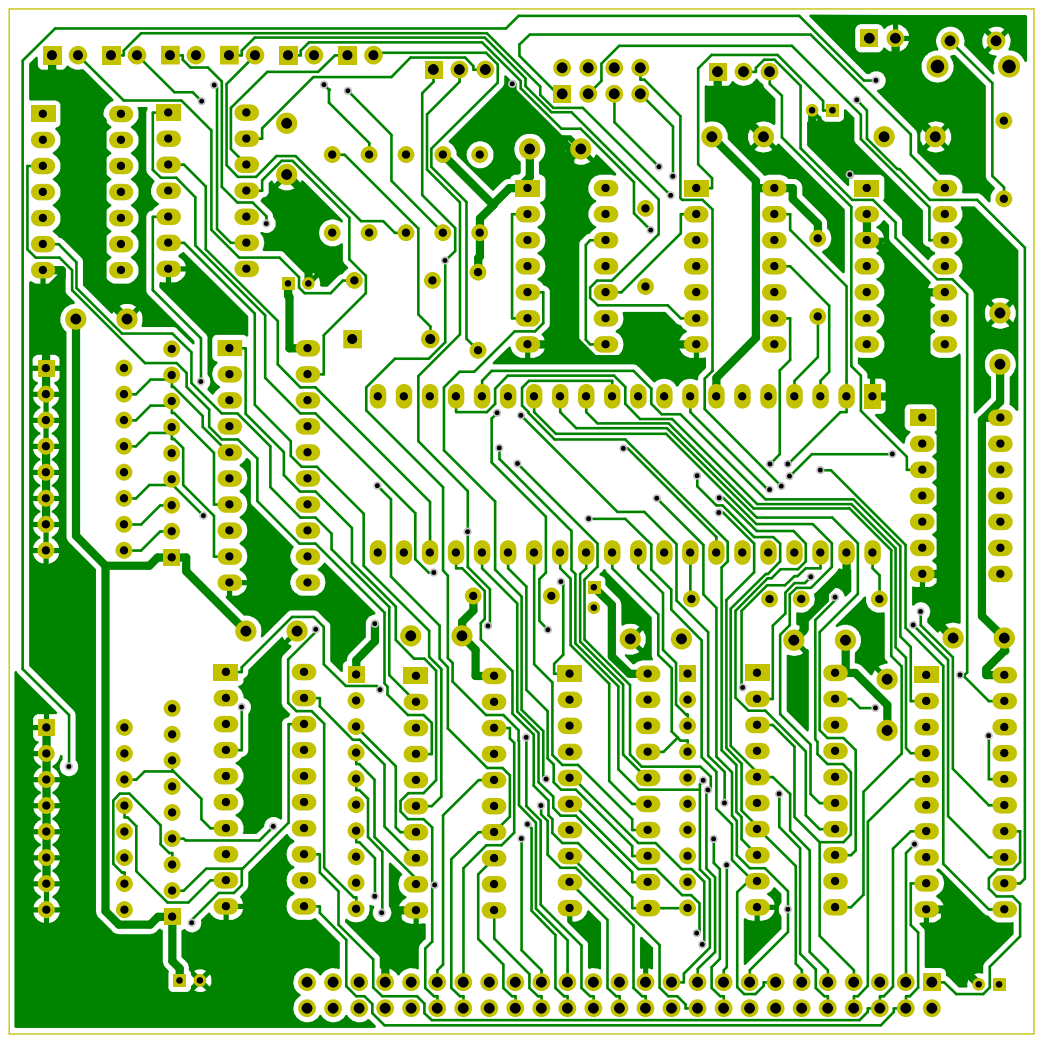
[picture p98: page 2]

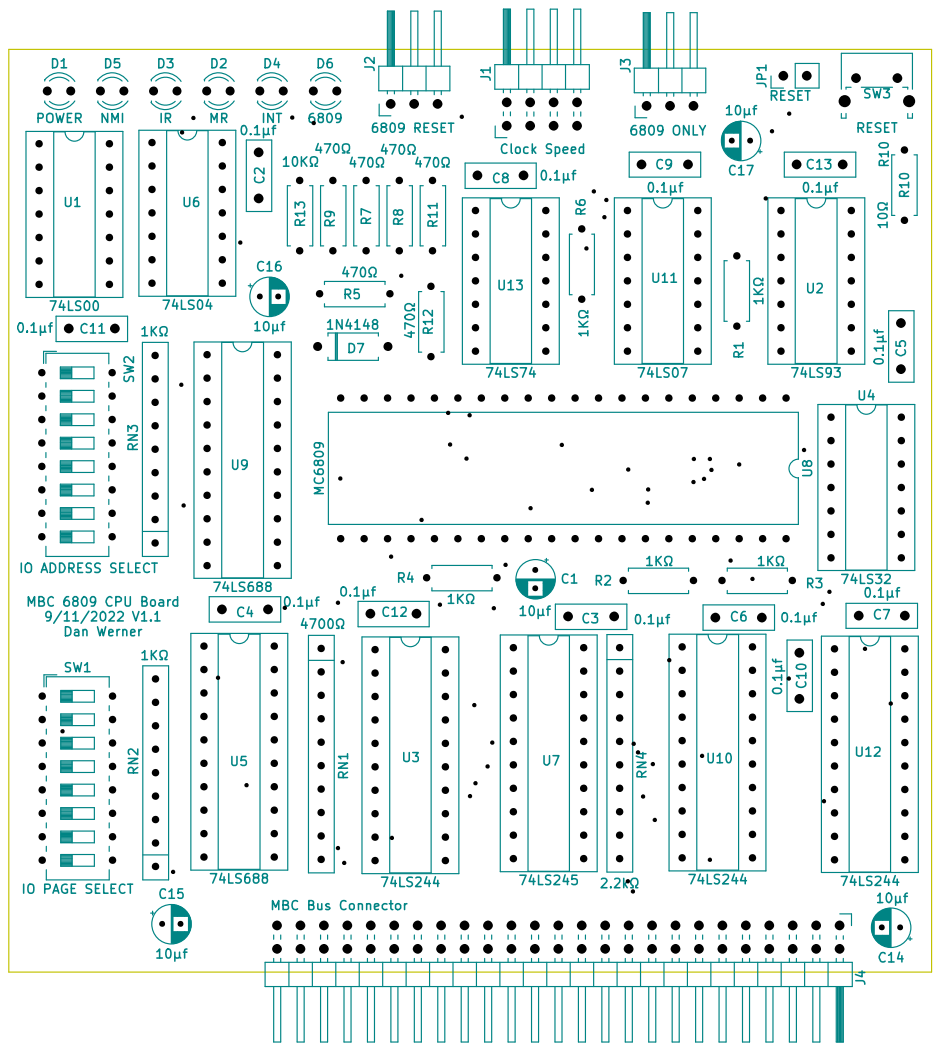
[picture p99: page 3]

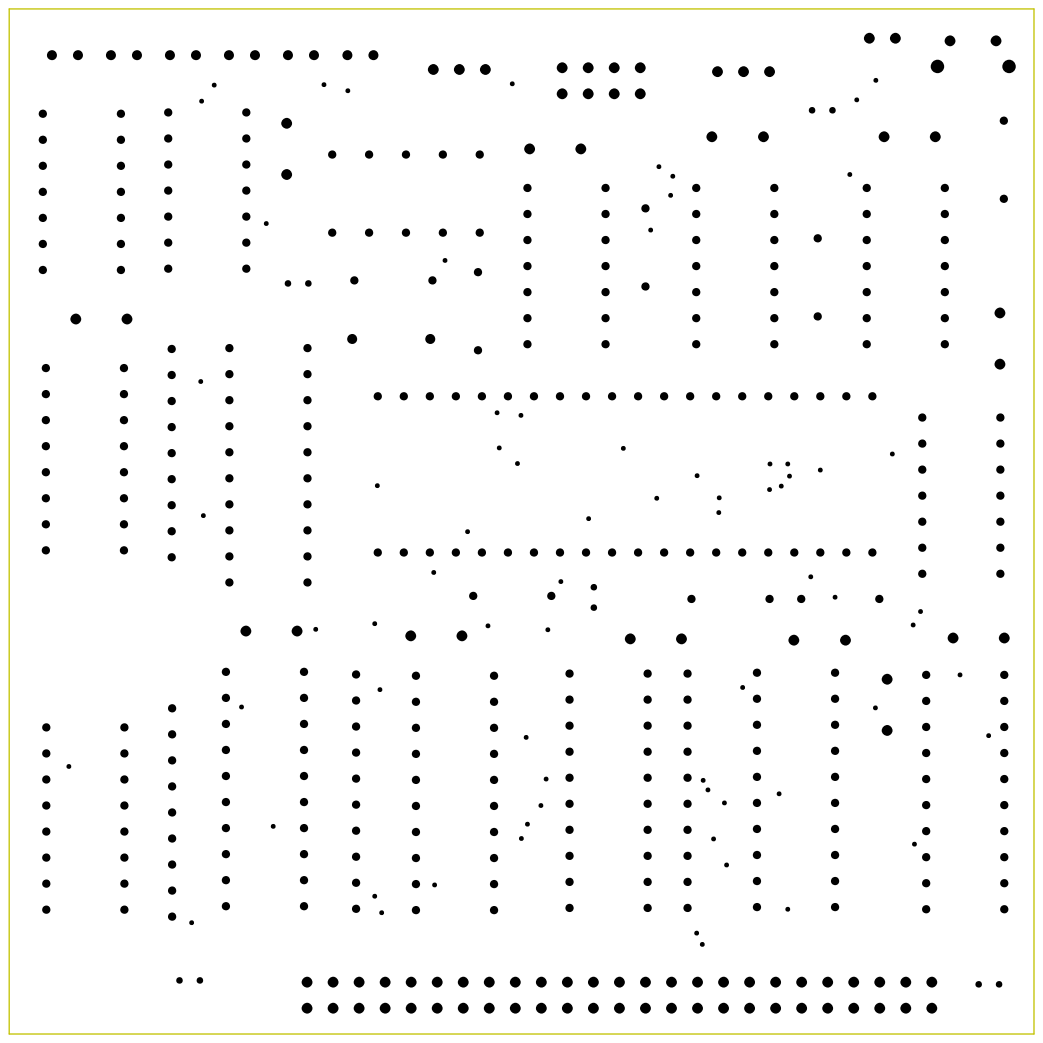
[picture p100: page 4]

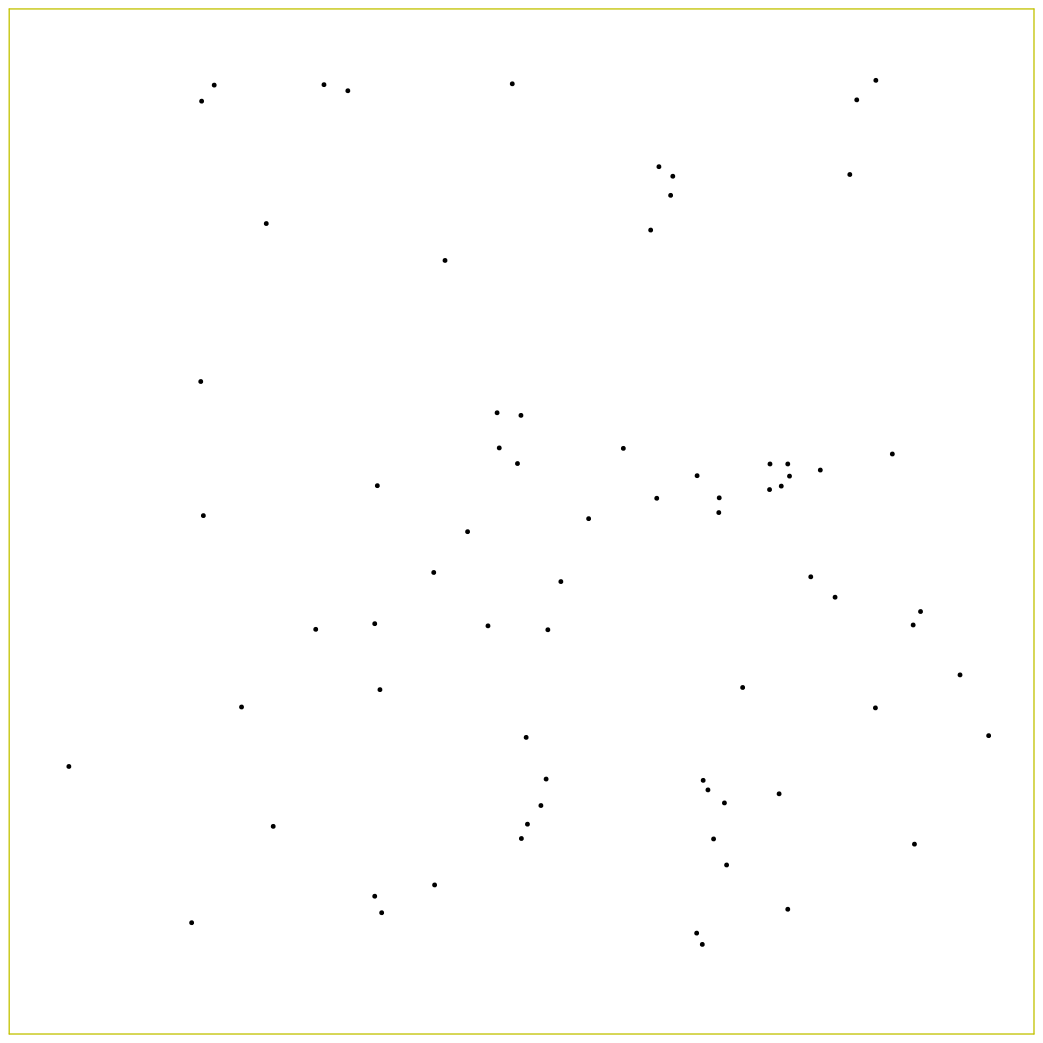
[picture p101: page 5]
