lynchaj/nhyodyne/6809PROC/hardware/6809Proc_Schematic_1.1.pdf

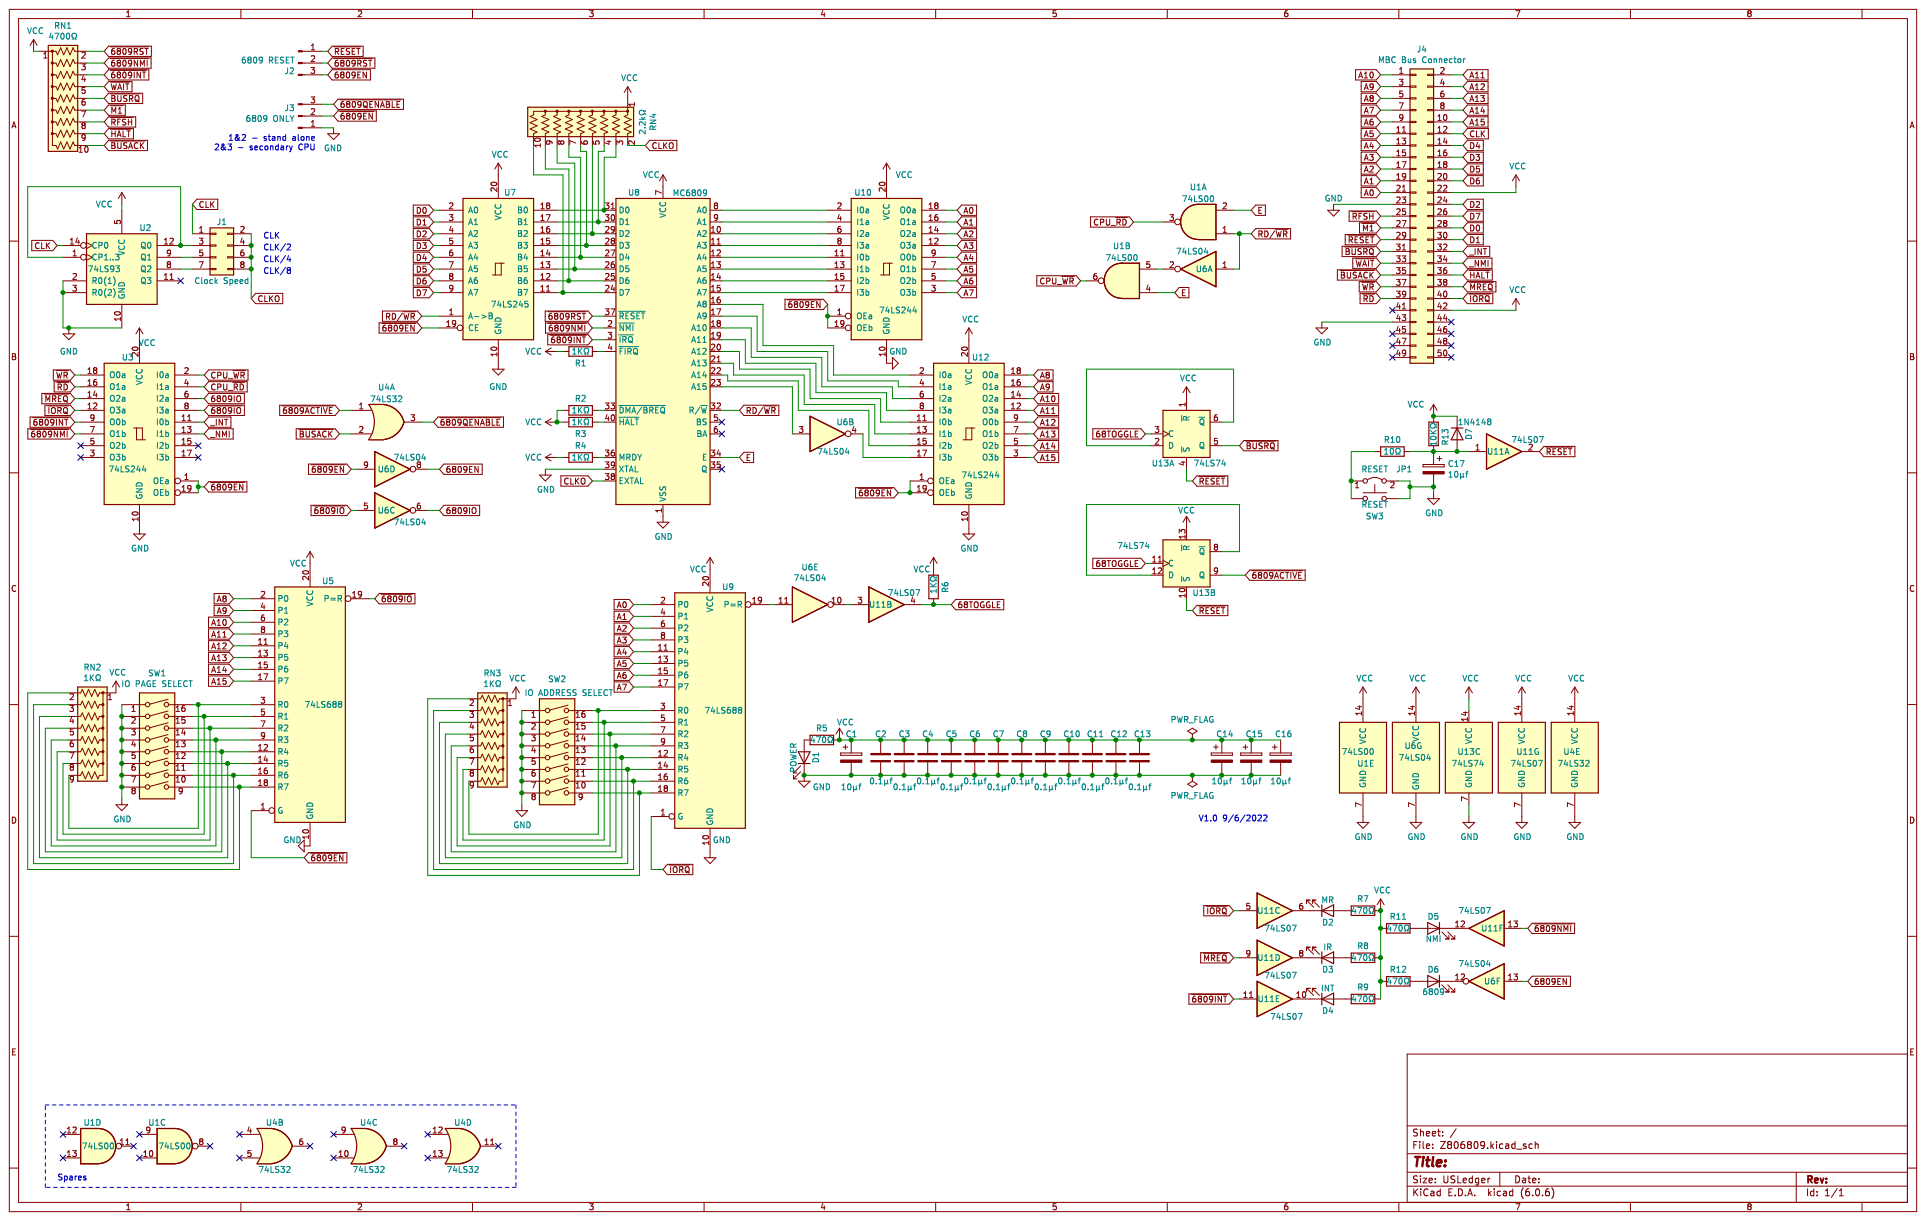
[picture p102: page 1]
