lynchaj/nhyodyne/6809PROC/hardware/6809Proc_PCB_1.0.pdf

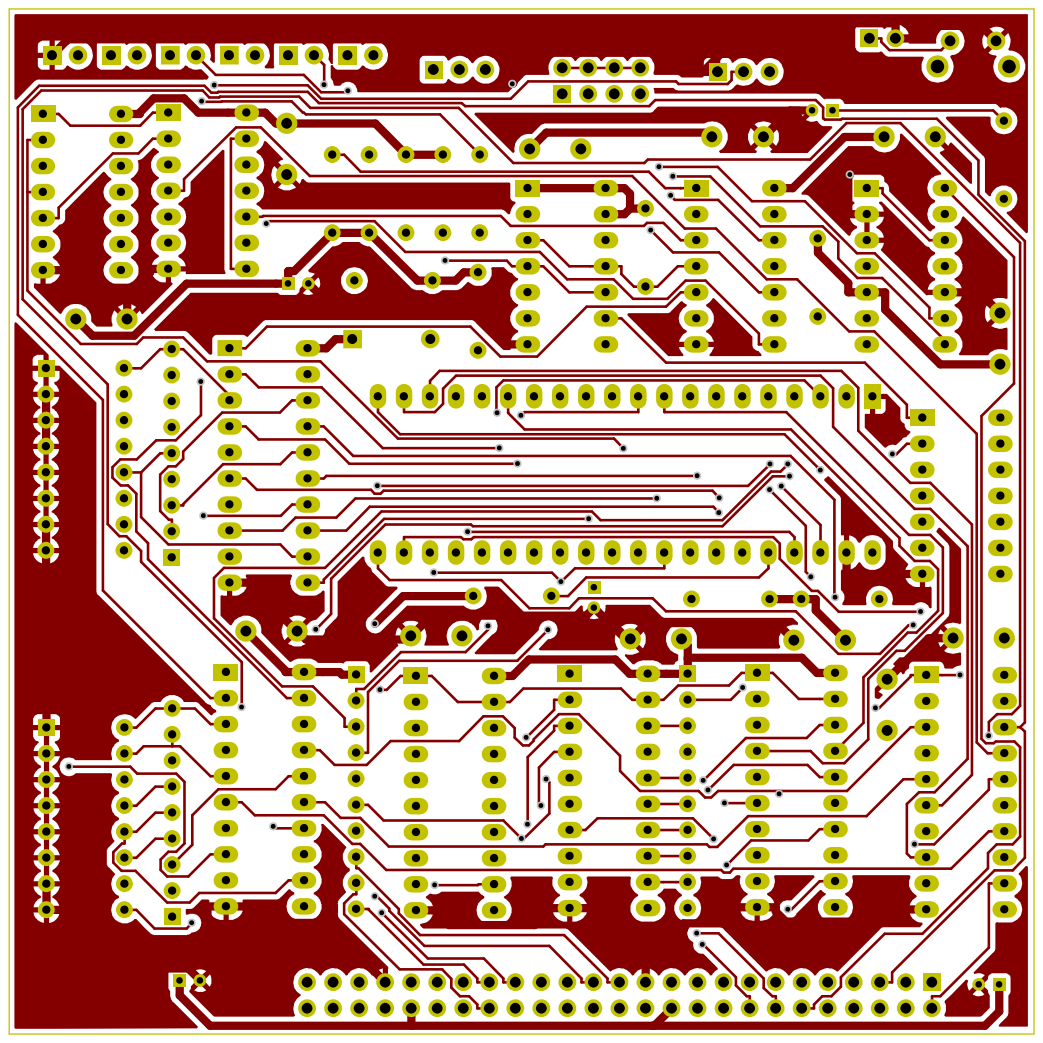
[picture p103: page 1]

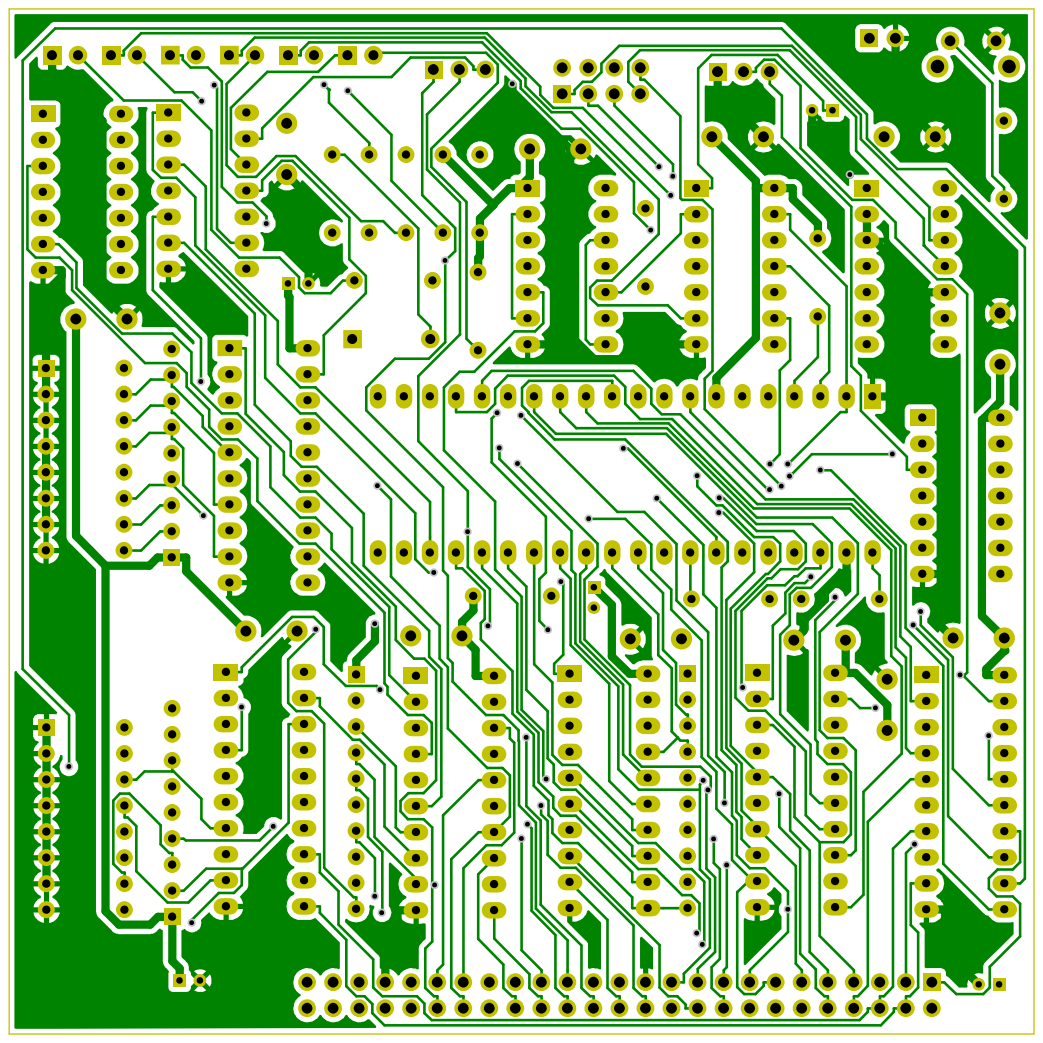
[picture p104: page 2]

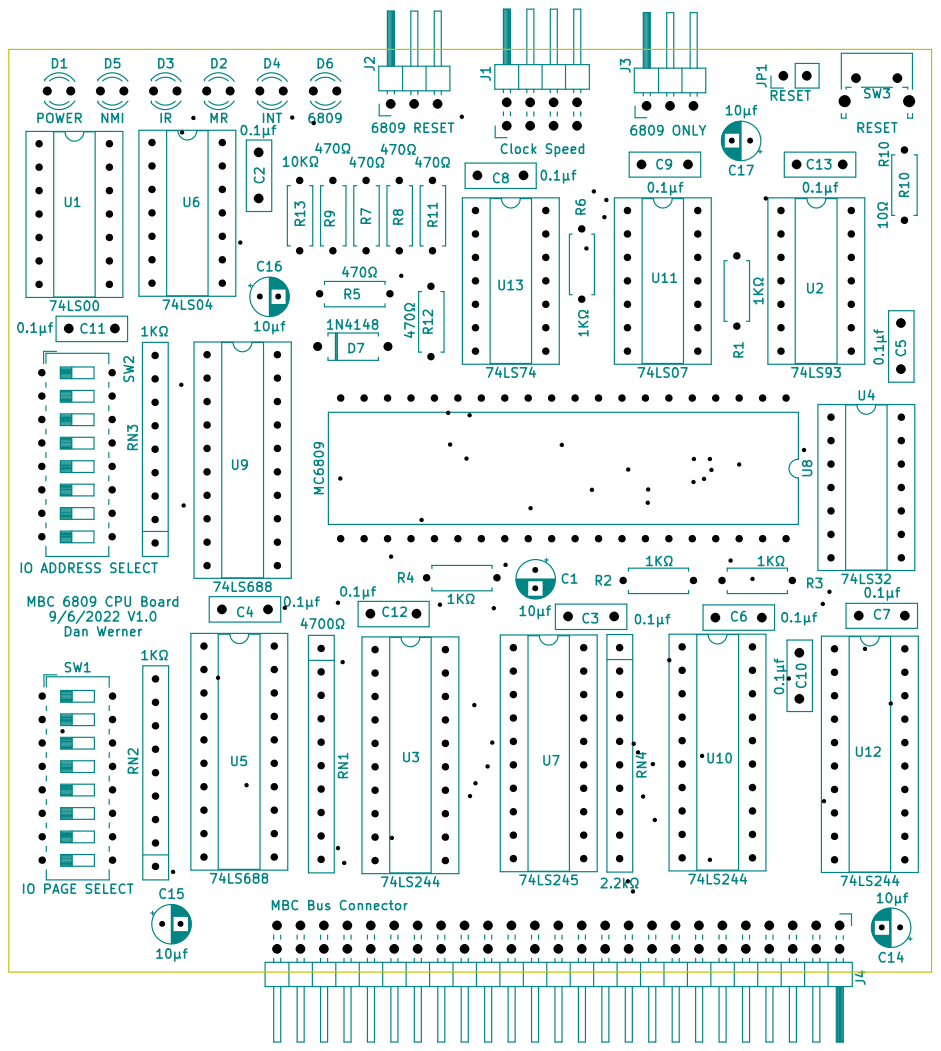
[picture p105: page 3]

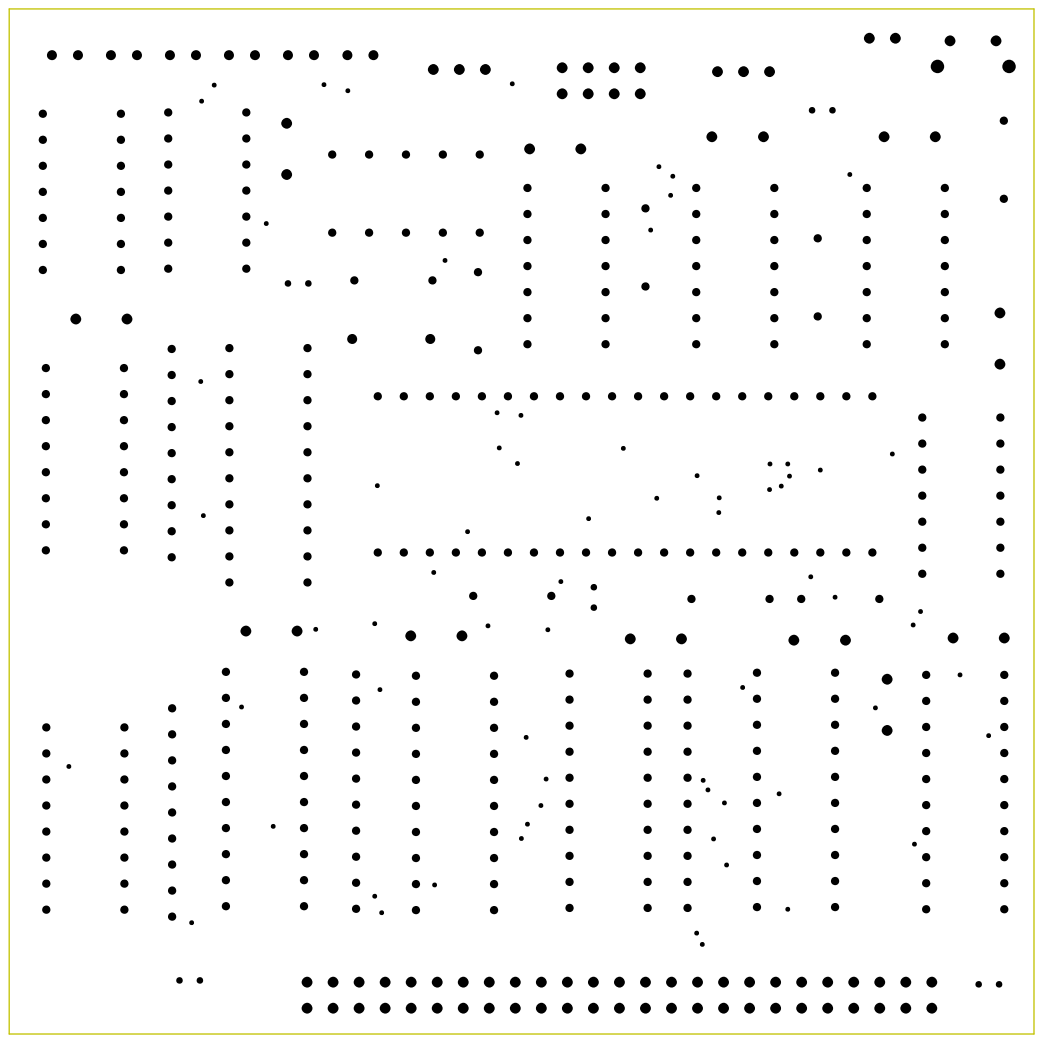
[picture p106: page 4]

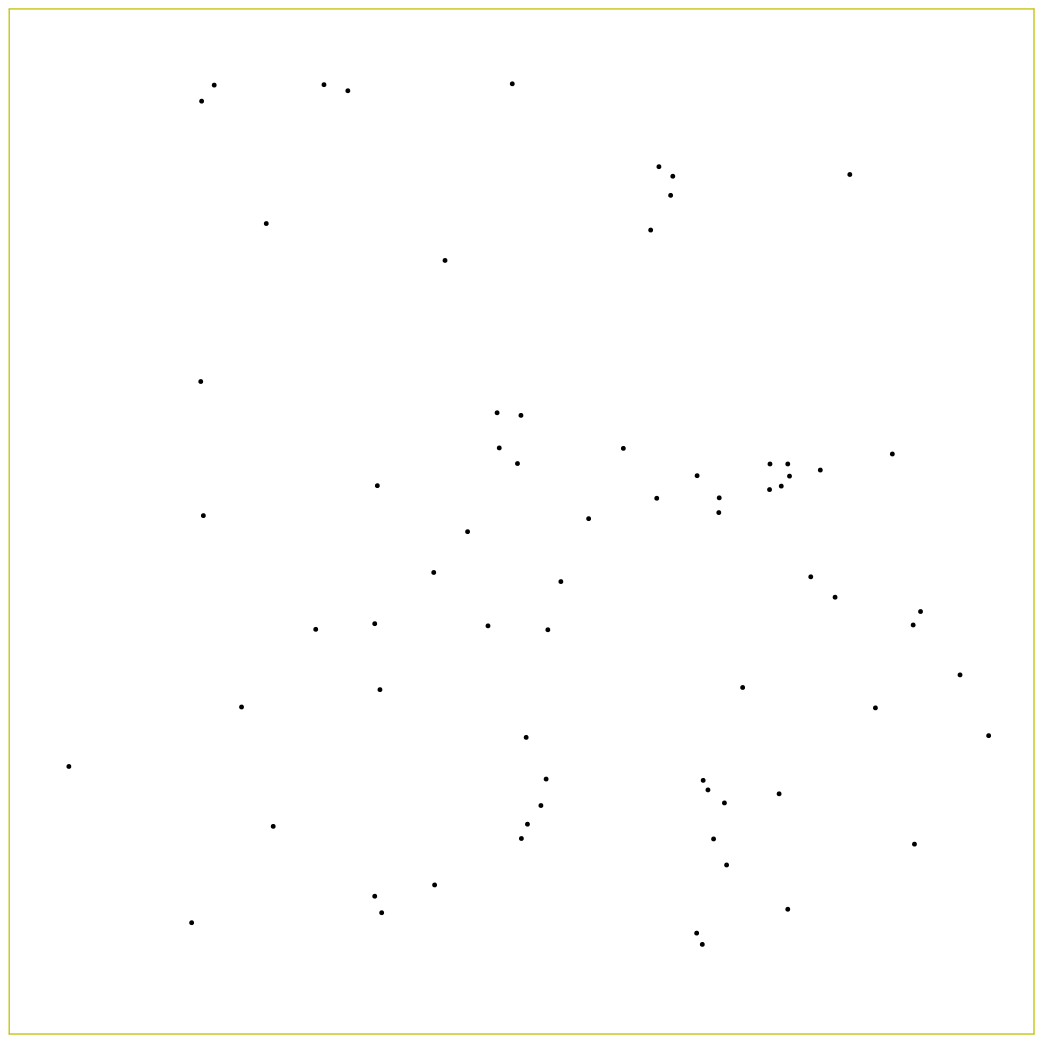
[picture p107: page 5]
