lynchaj/nhyodyne/6809PROC/hardware/6809Proc_Schematic_1.0.pdf

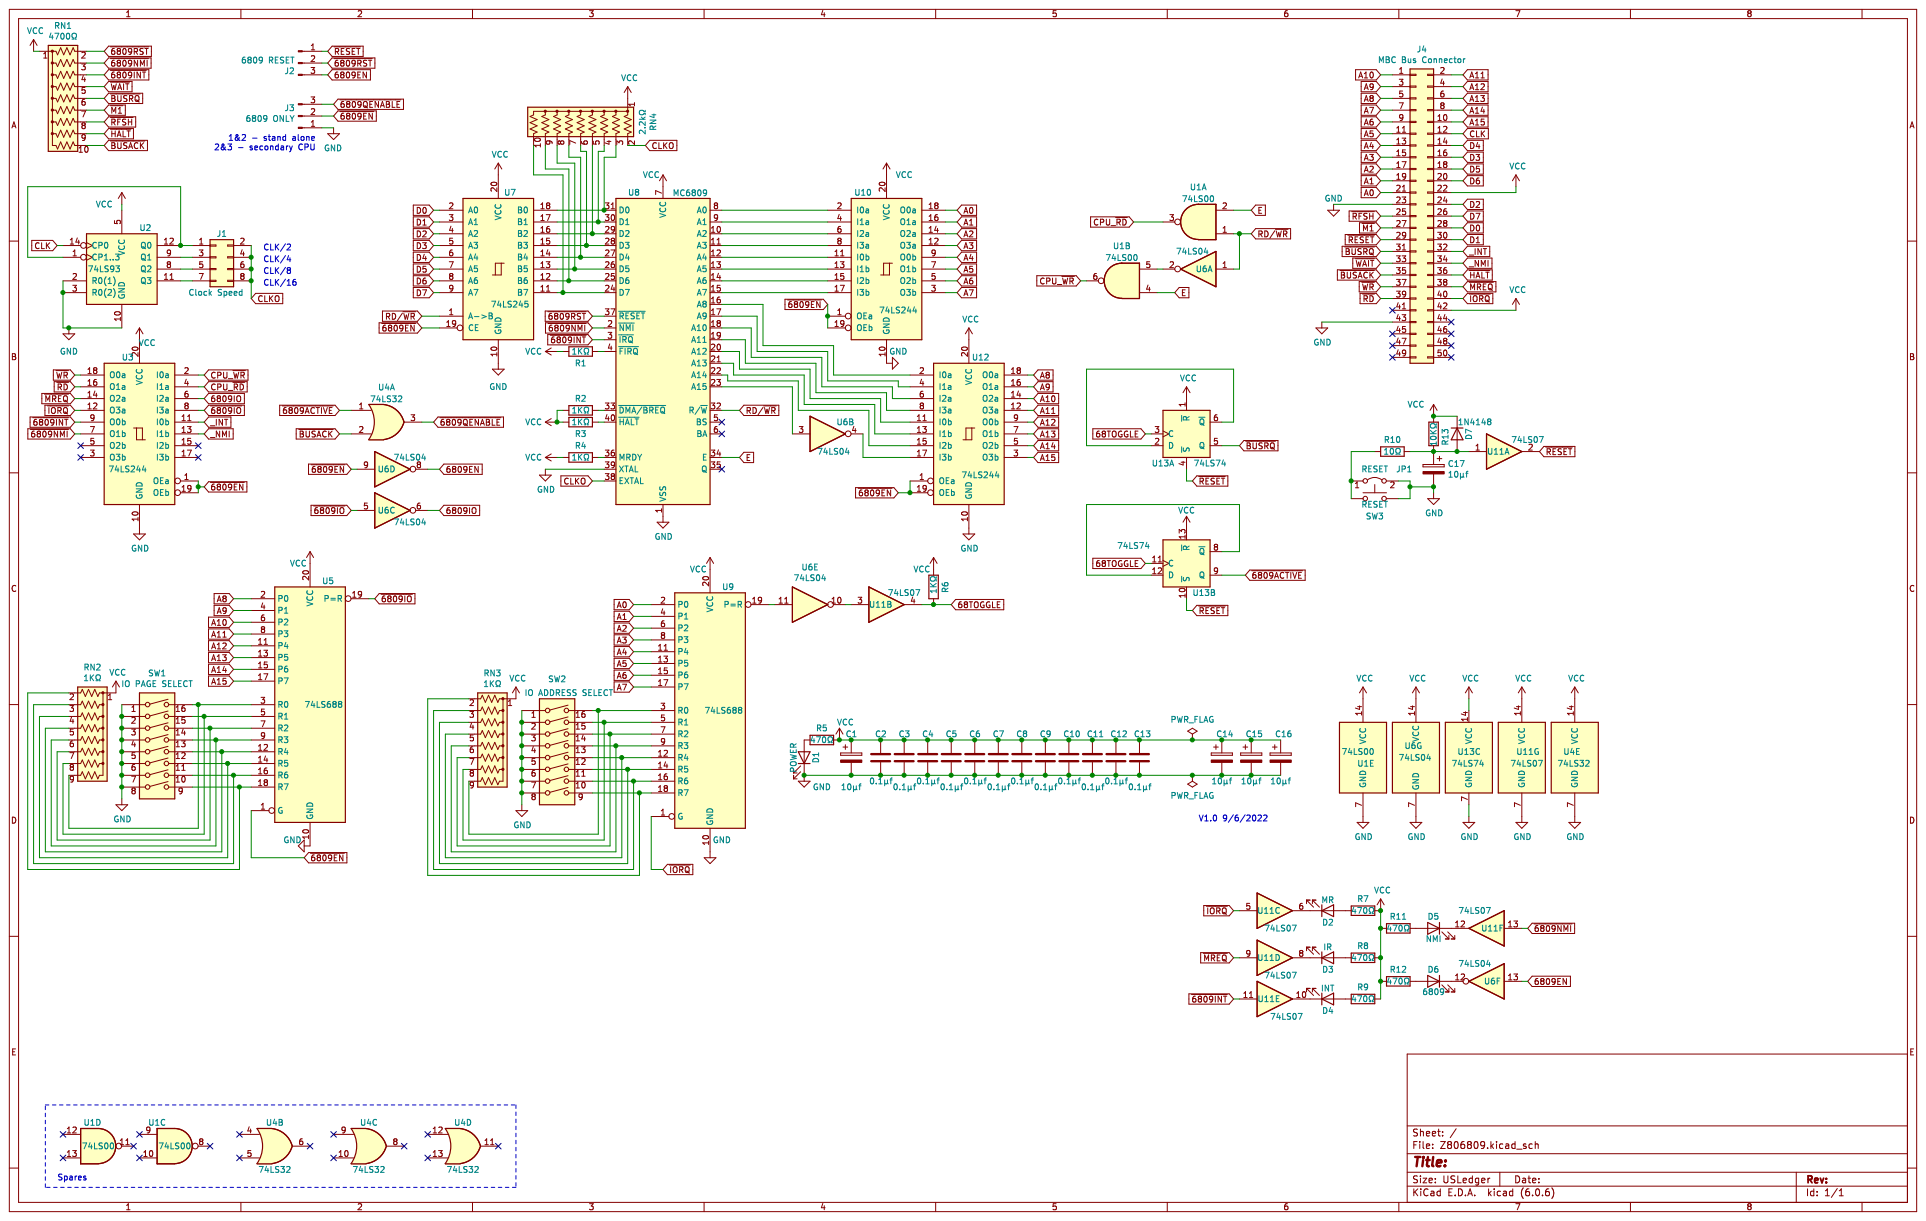
[picture p108: page 1]
