lynchaj/nhyodyne/6809PROC/hardware/6809Proc_PCB_0.75.pdf

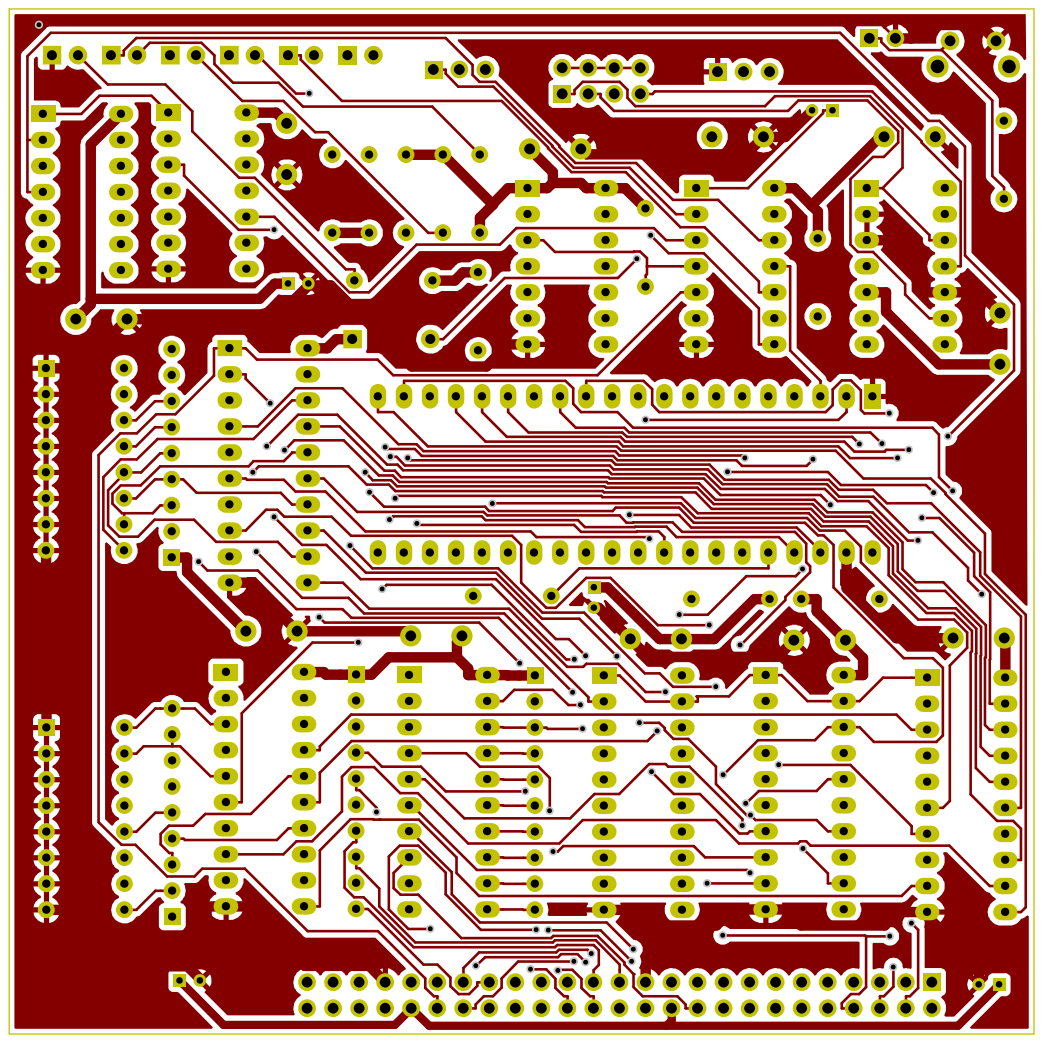
[picture p109: page 1]

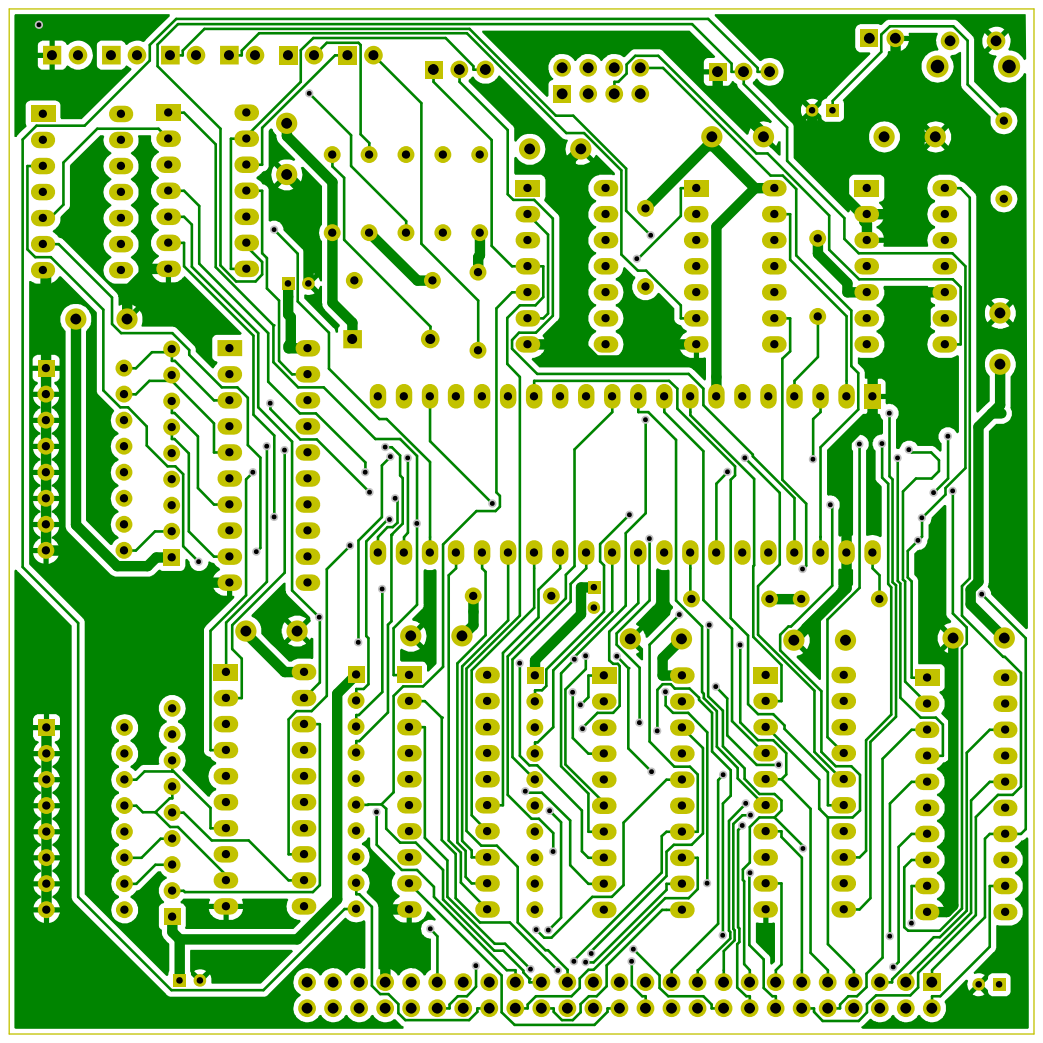
[picture p110: page 2]

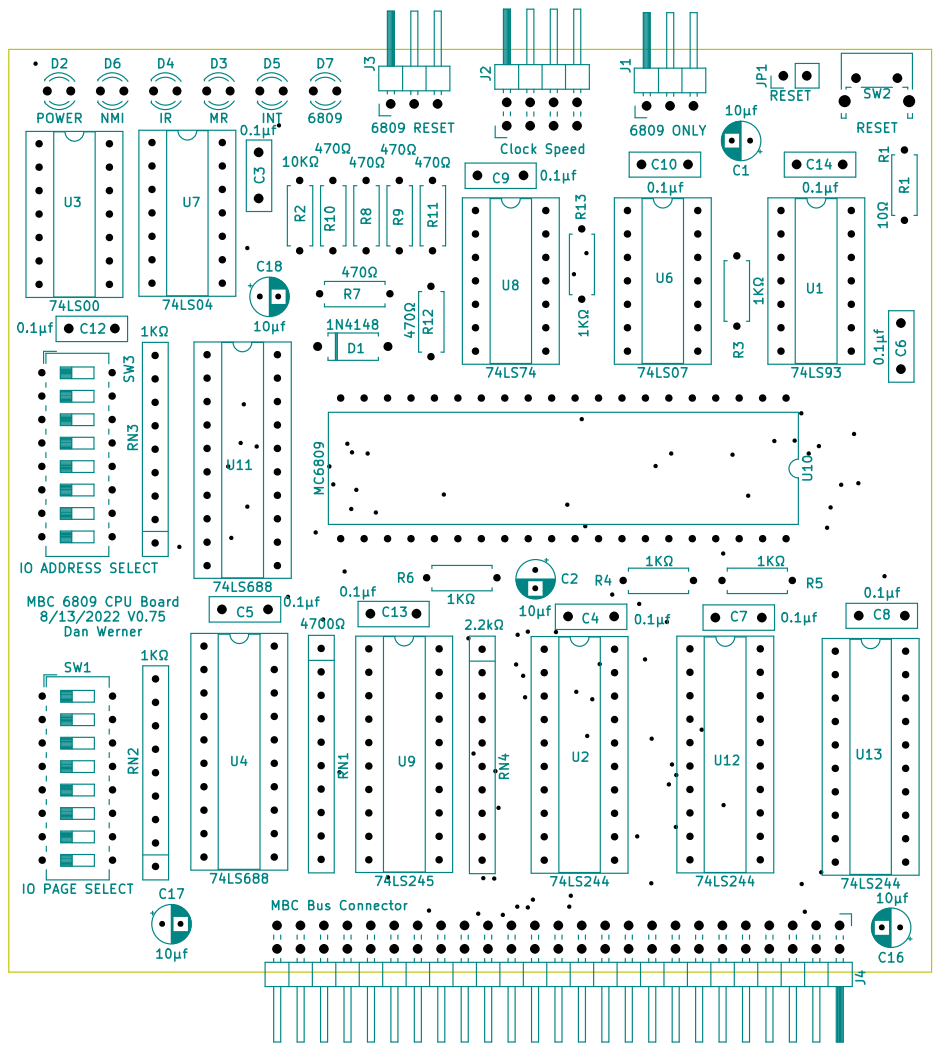
[picture p111: page 3]

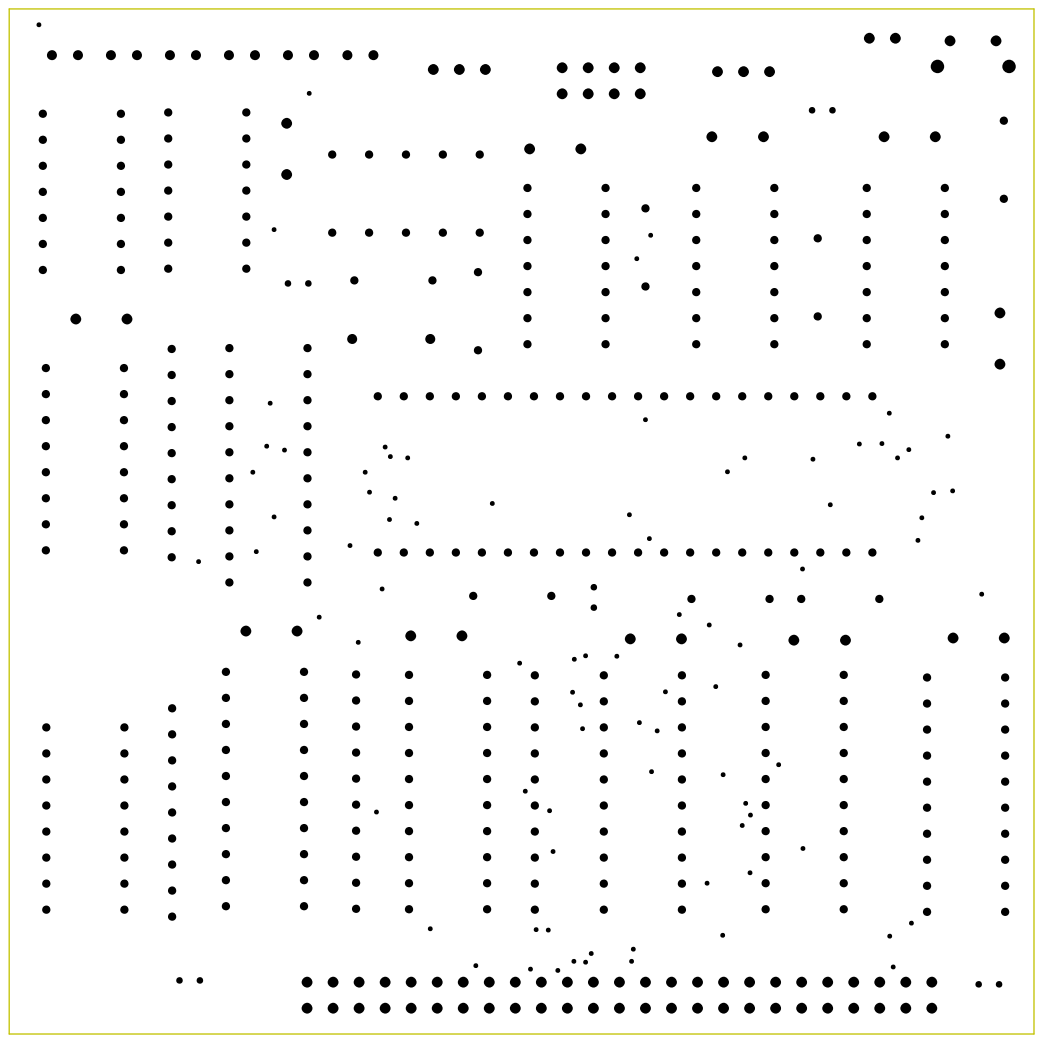
[picture p112: page 4]

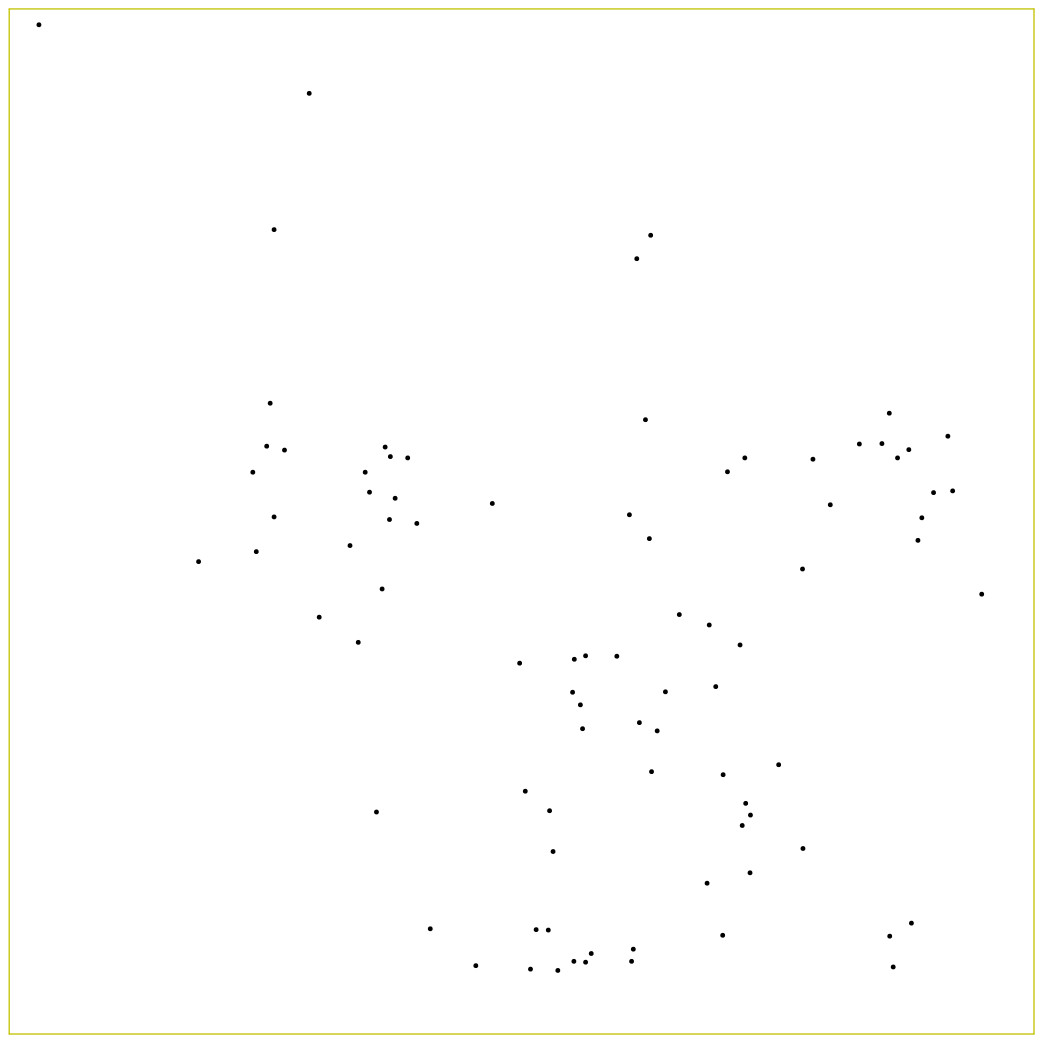
[picture p113: page 5]
