lynchaj/nhyodyne/6809PROC/hardware/6809Proc_Schematic_0.75.pdf

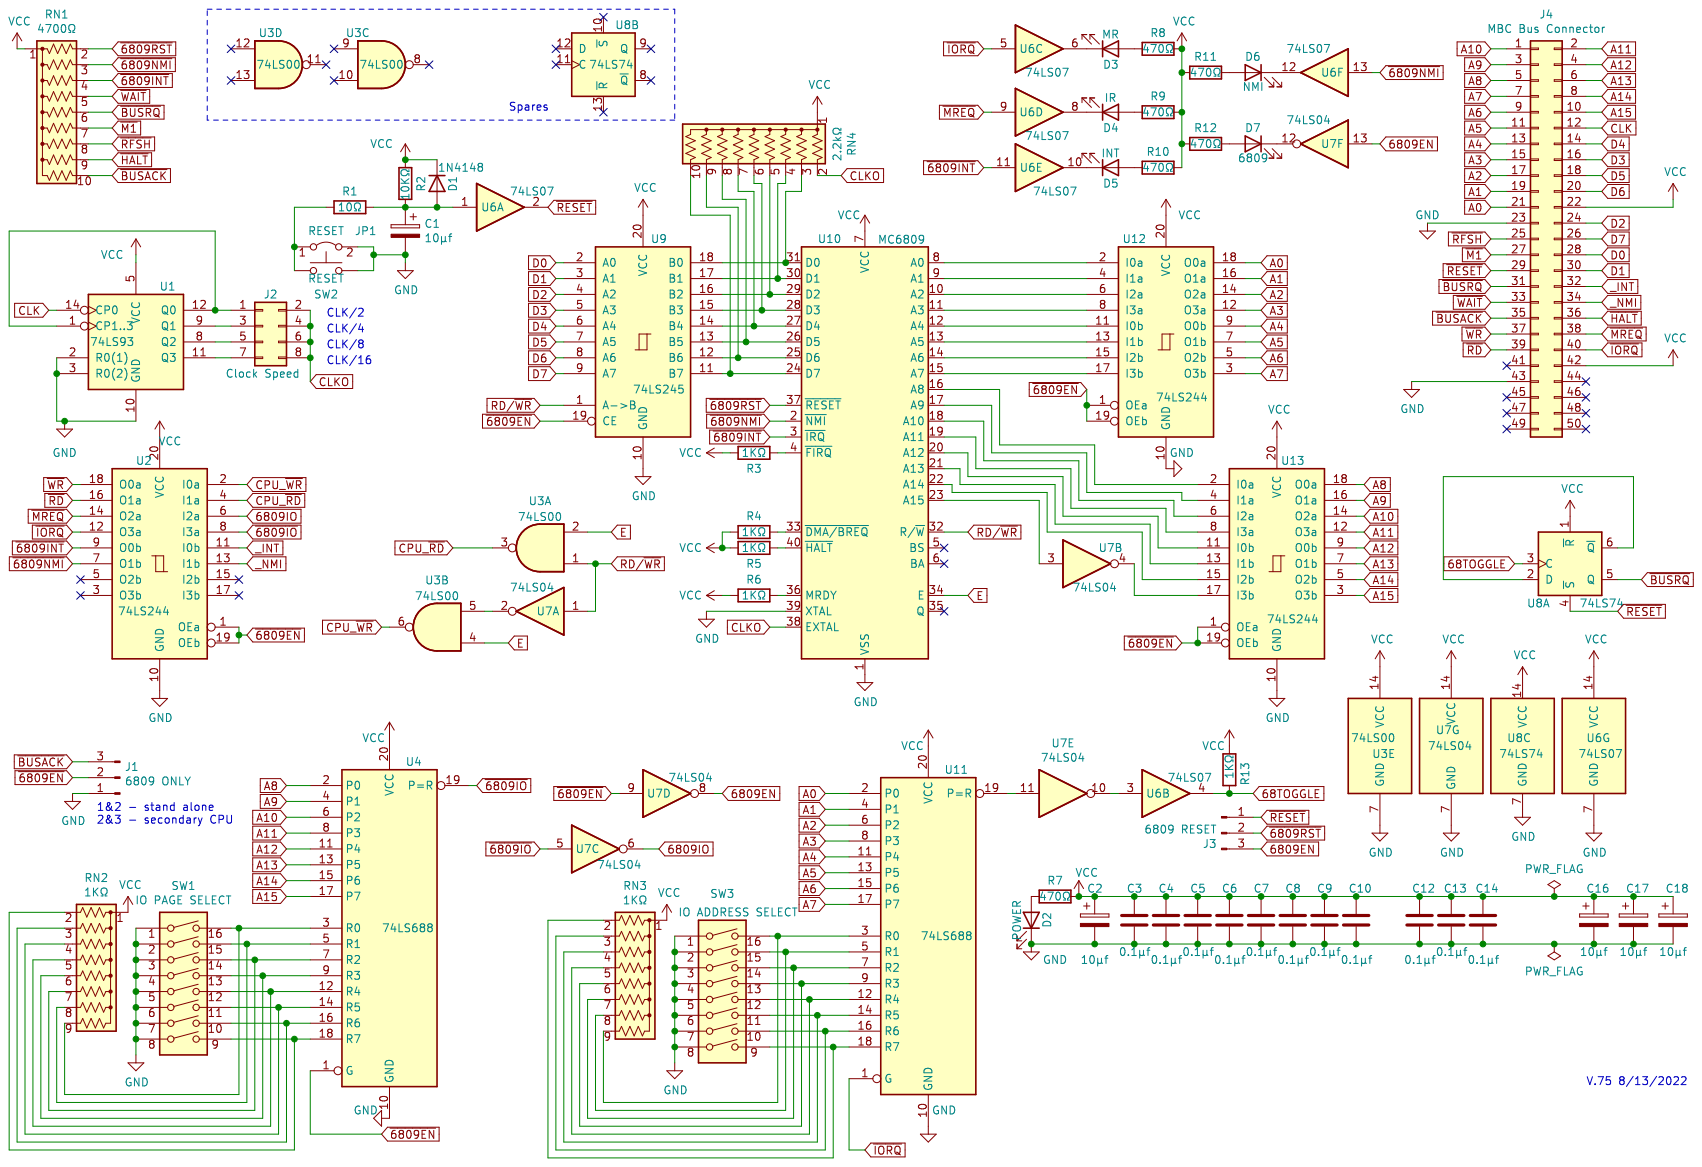
[picture p114: page 1]
