lynchaj/nhyodyne/6809PROC/hardware/6809Proc_PCB_0.5.pdf

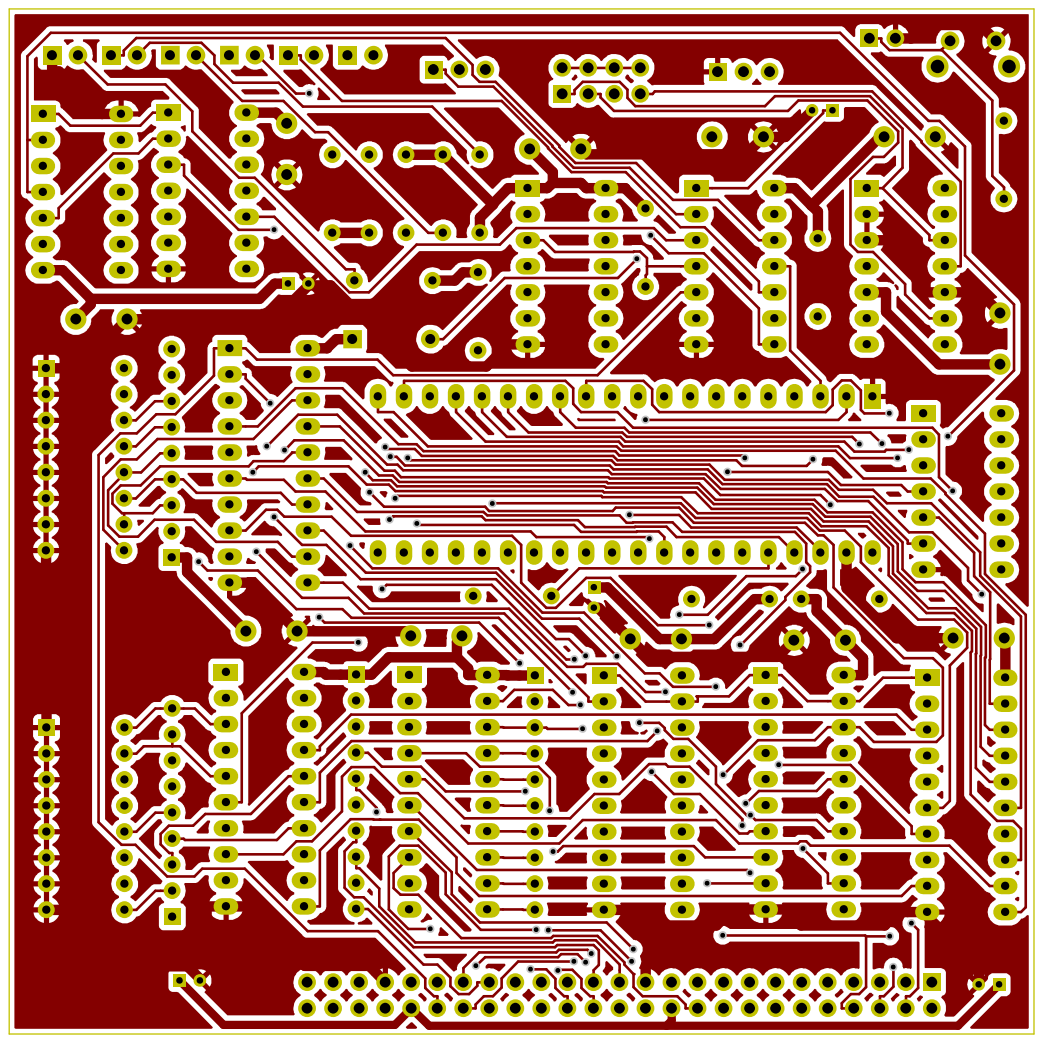
[picture p115: page 1]

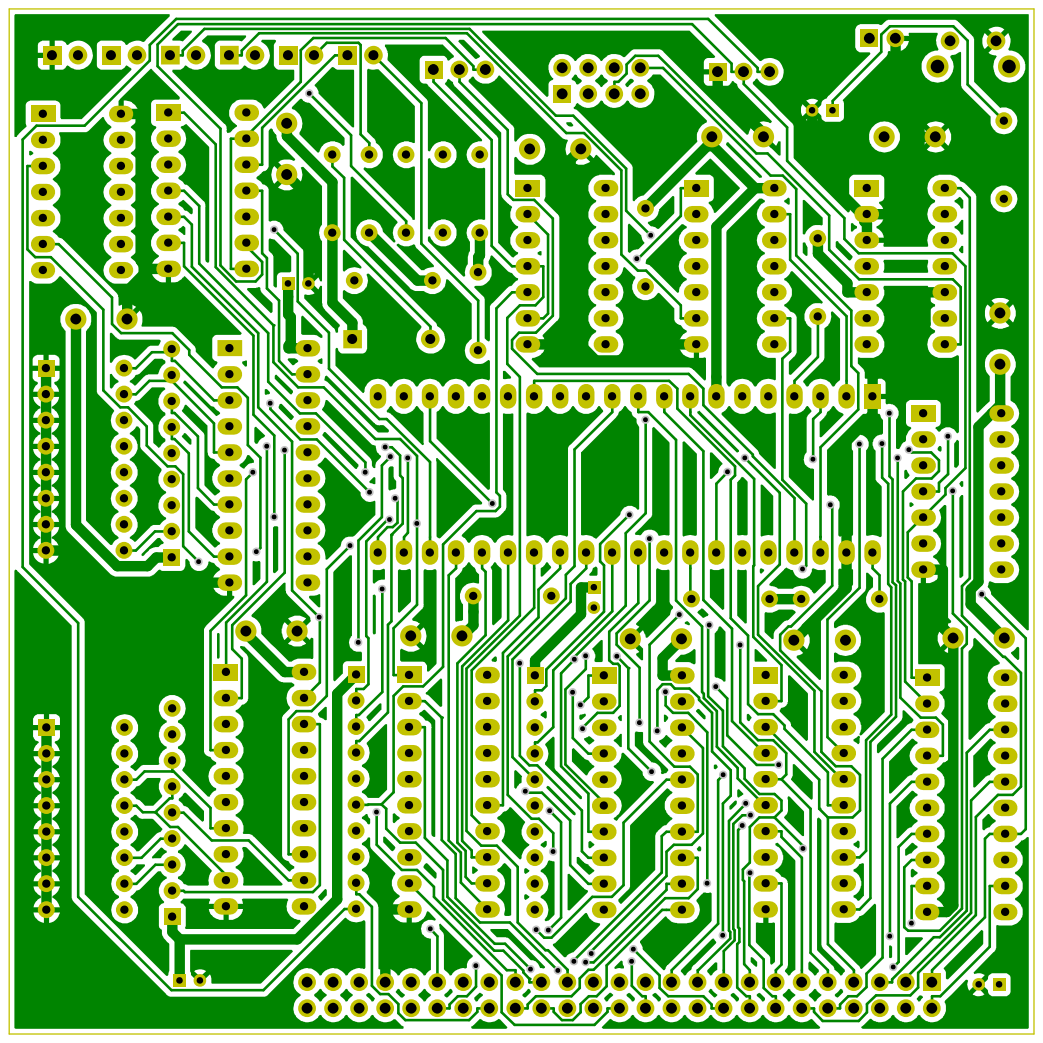
[picture p116: page 2]

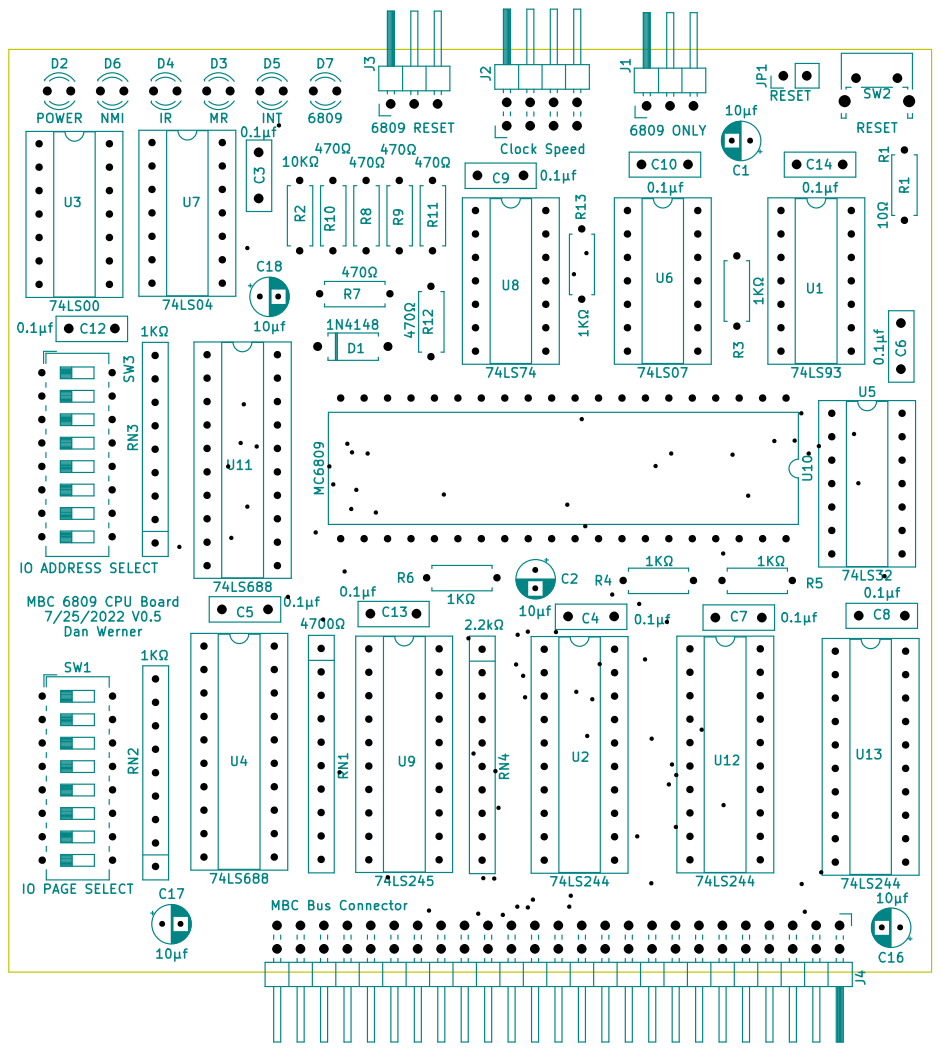
[picture p117: page 3]

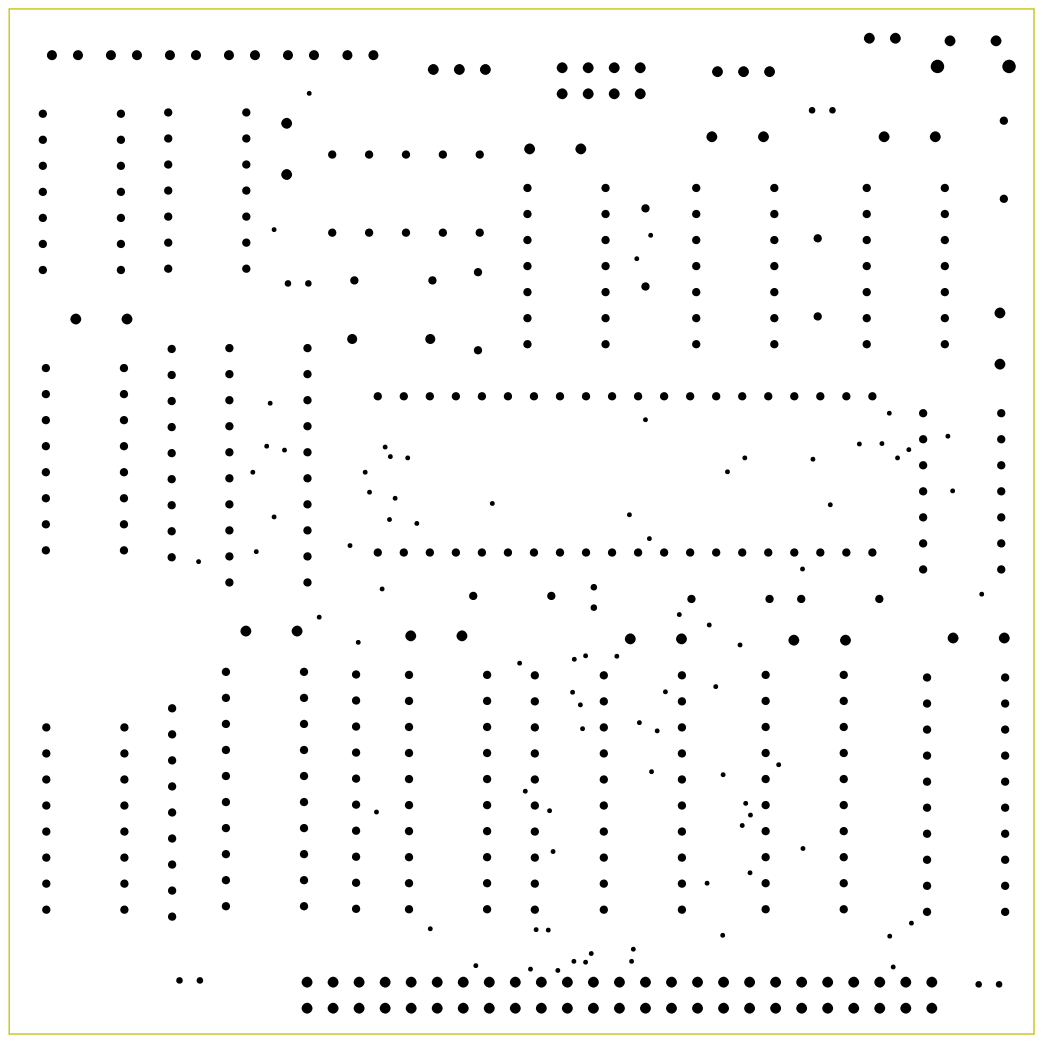
[picture p118: page 4]

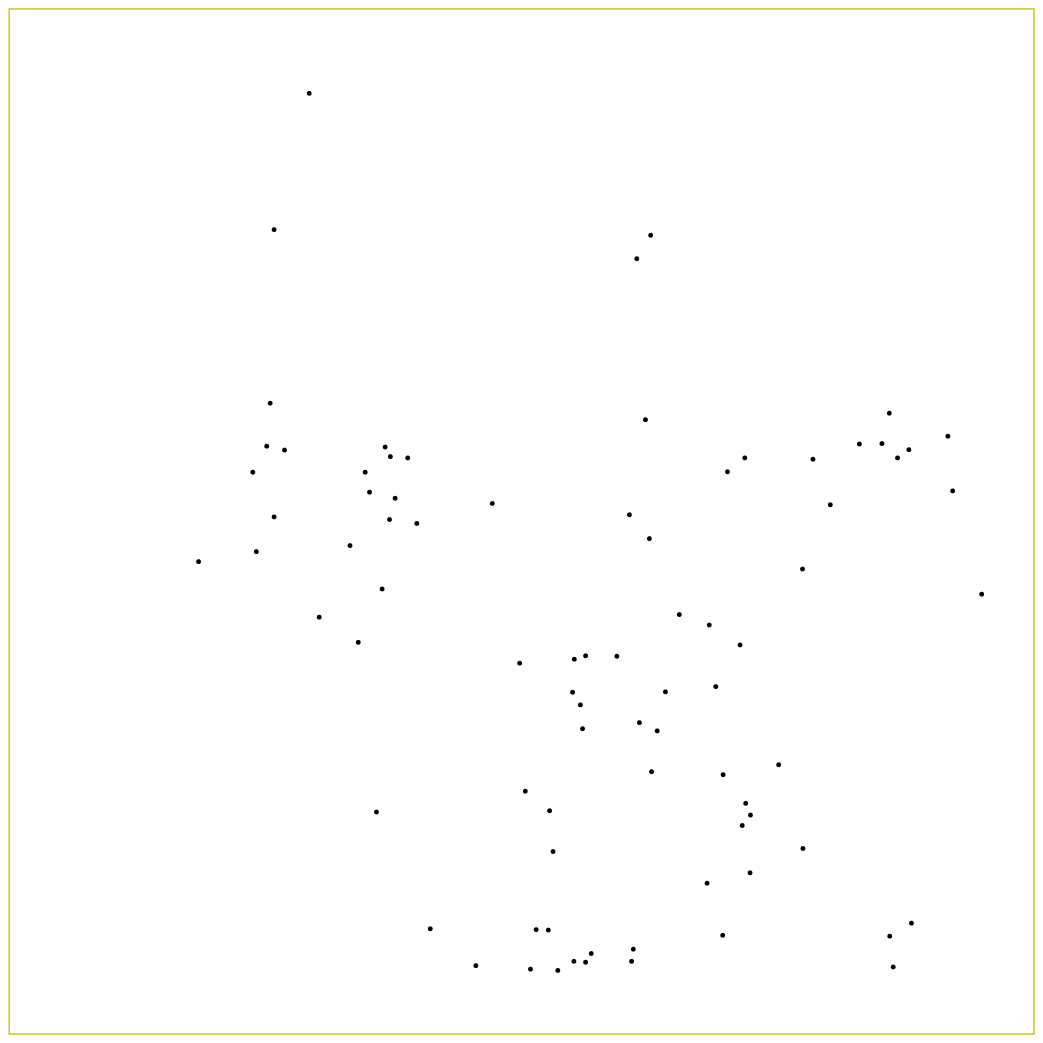
[picture p119: page 5]
