lynchaj/nhyodyne/6809PROC/hardware/6809Proc_Schematic_0.5.pdf

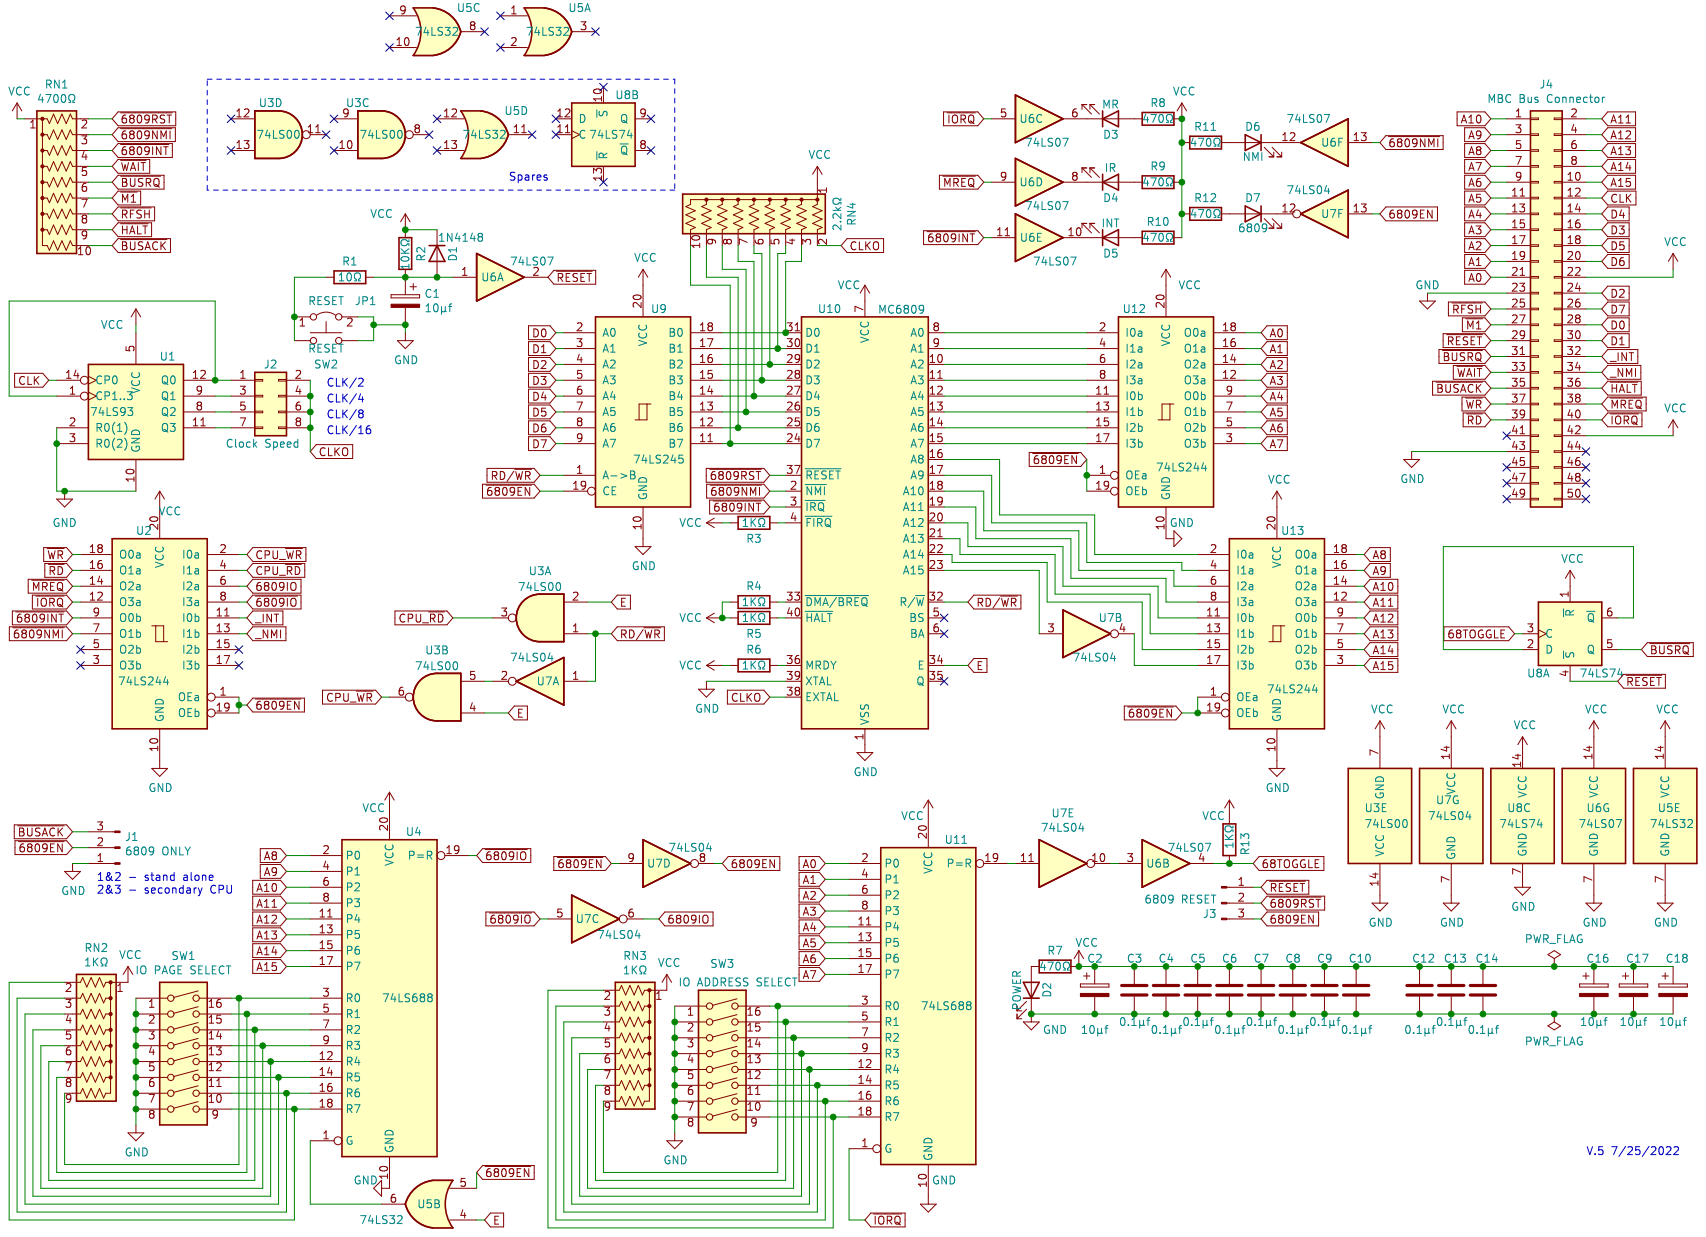
[picture p120: page 1]
