lynchaj/nhyodyne/Z80VDP1B/Z80VDP1B-PCB.pdf

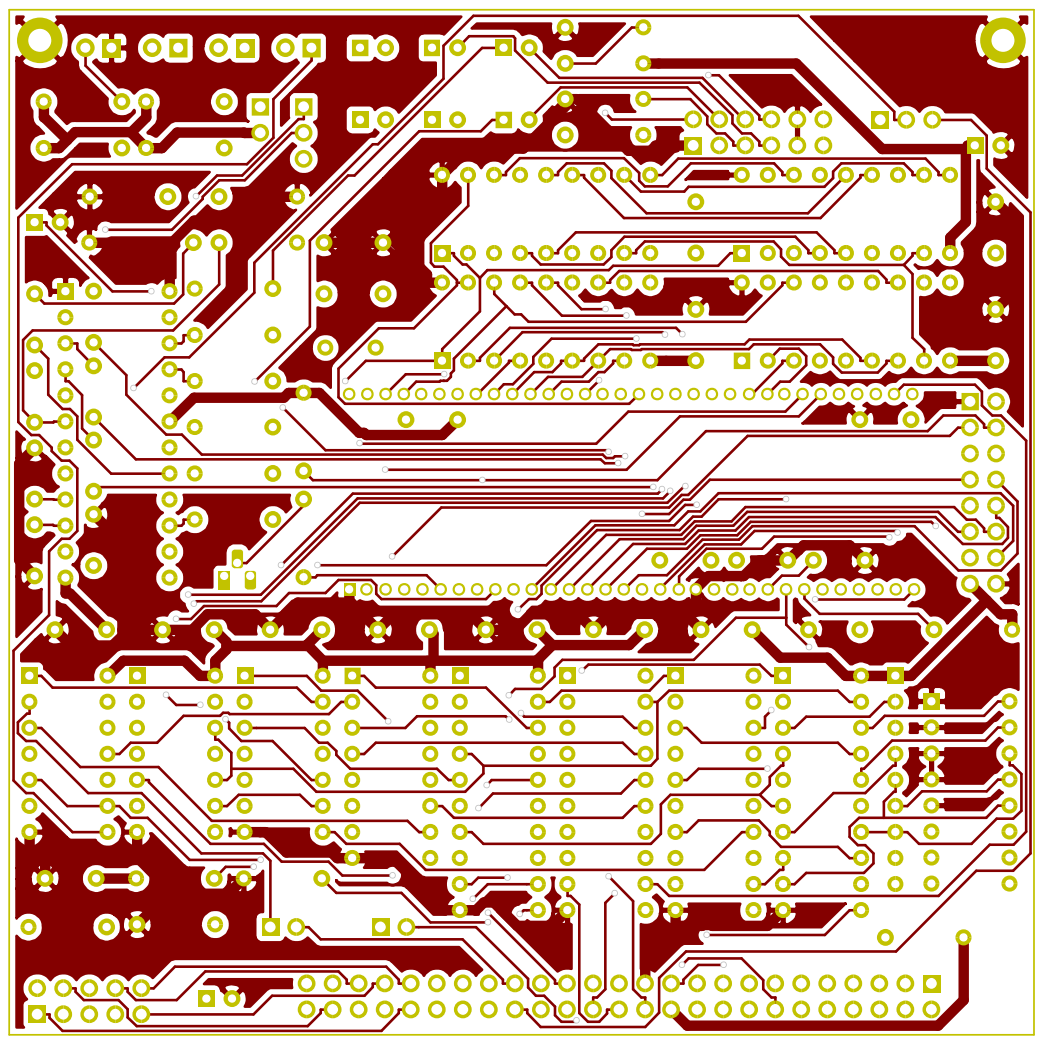
[picture p121: page 1]

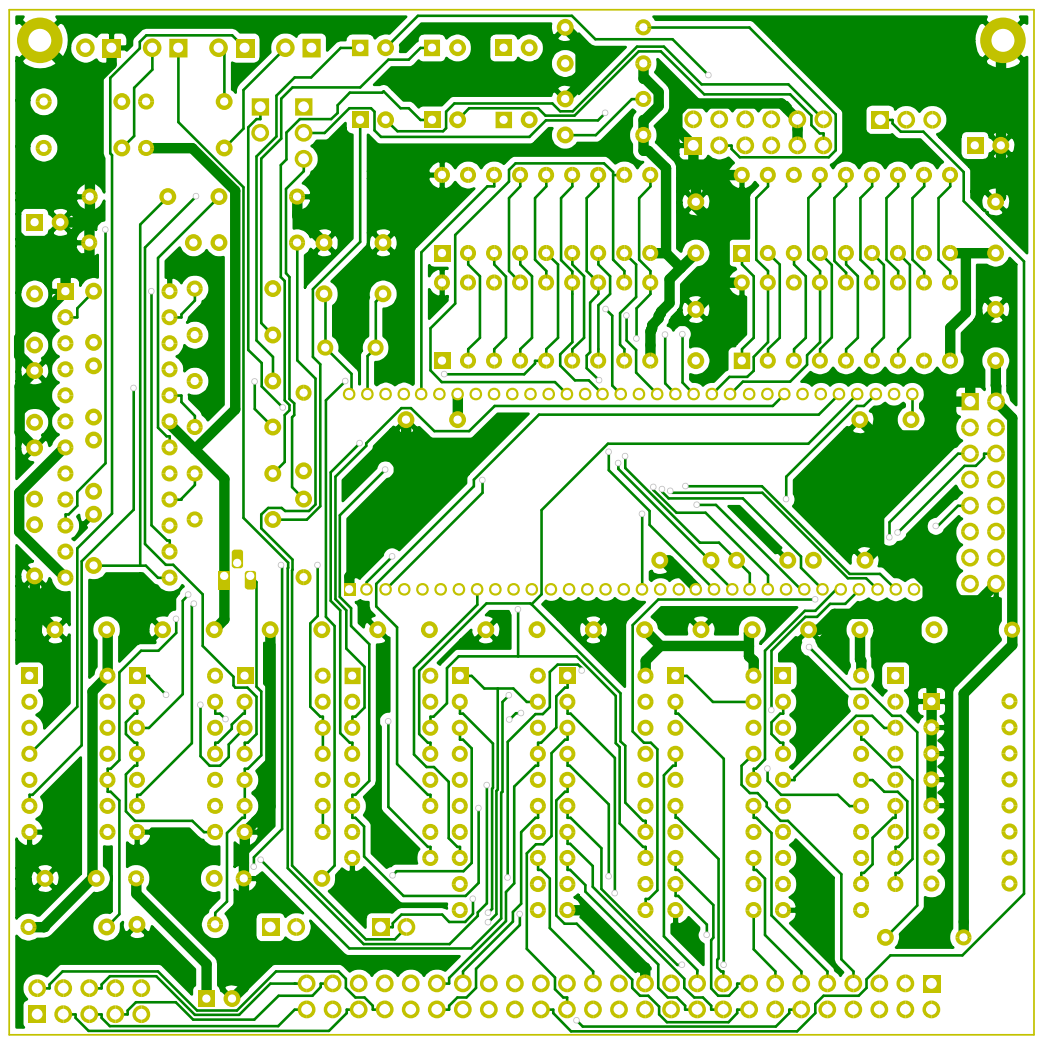
[picture p122: page 2]

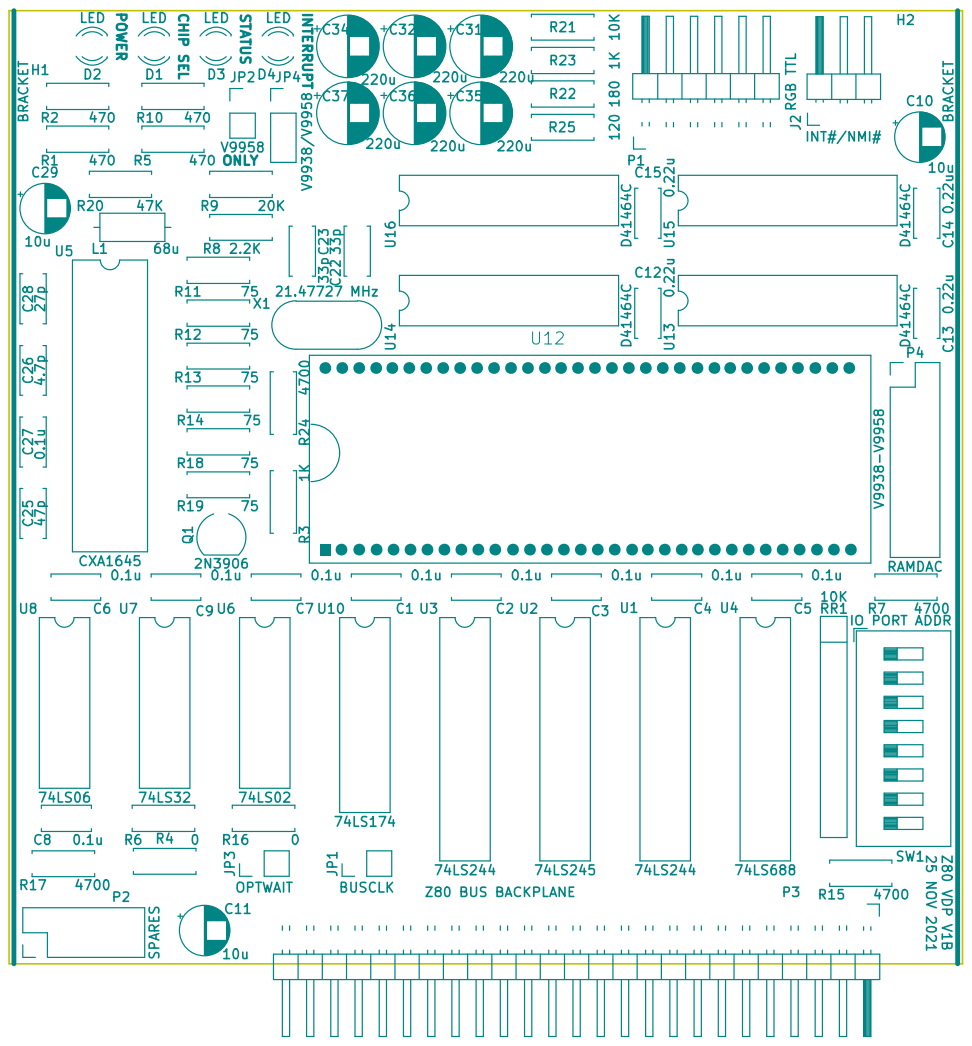
[picture p123: page 3]

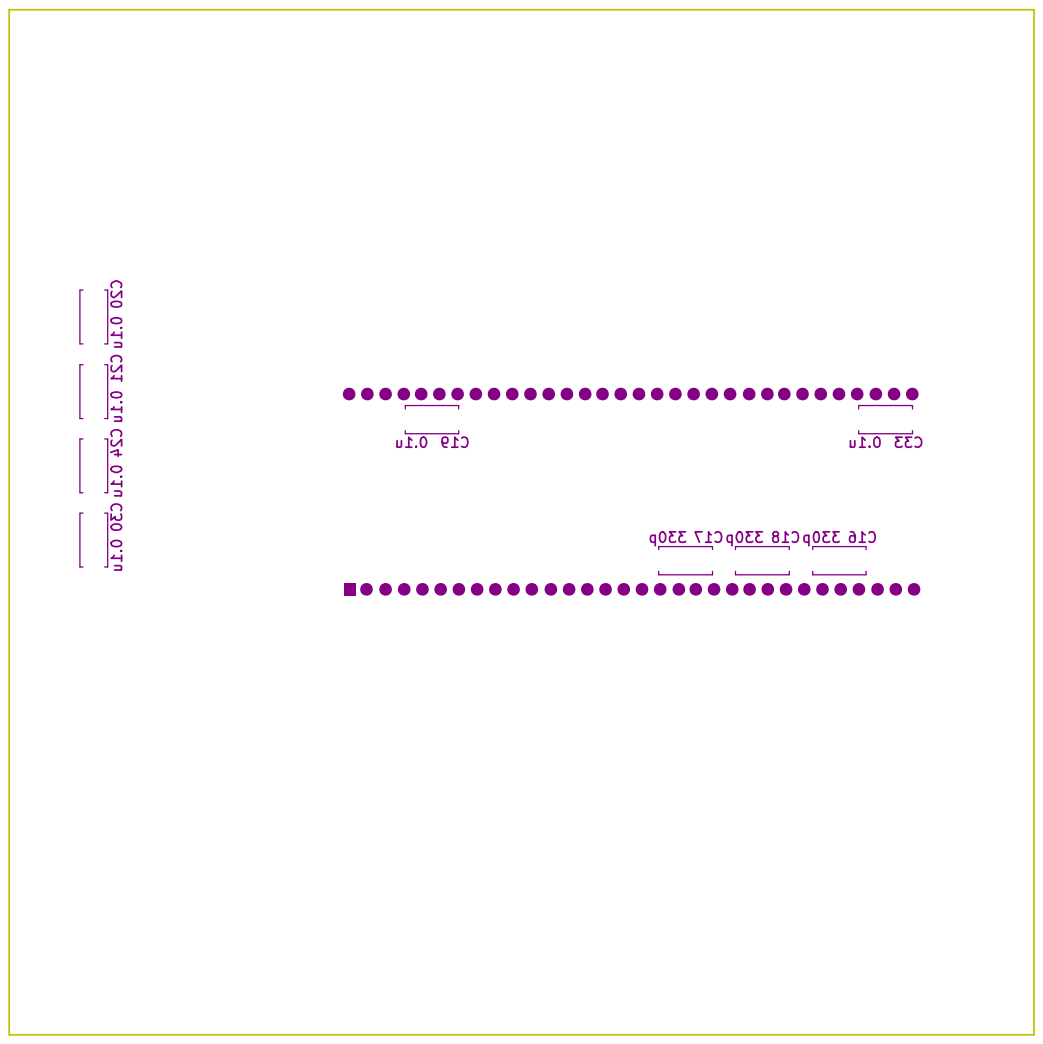
[picture p124: page 4]

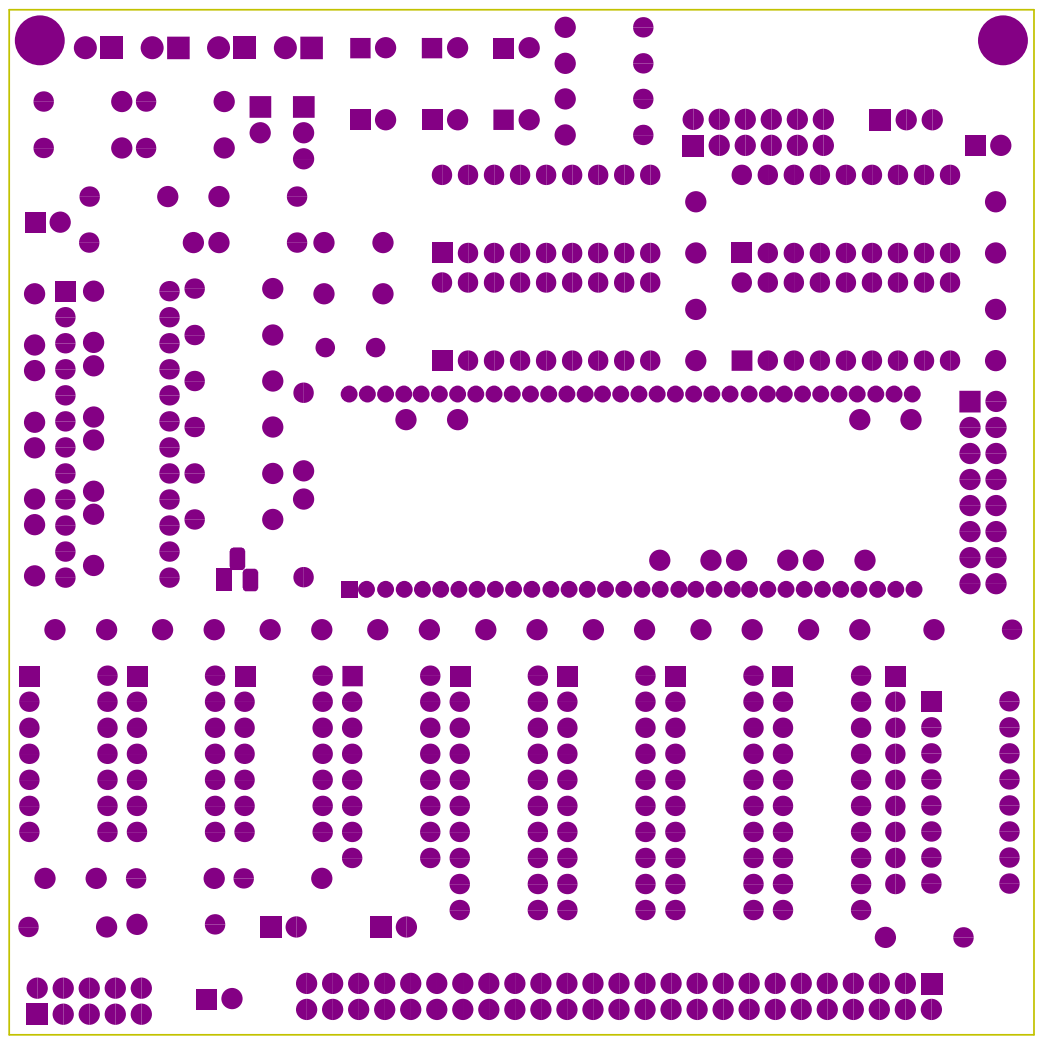
[picture p125: page 5]

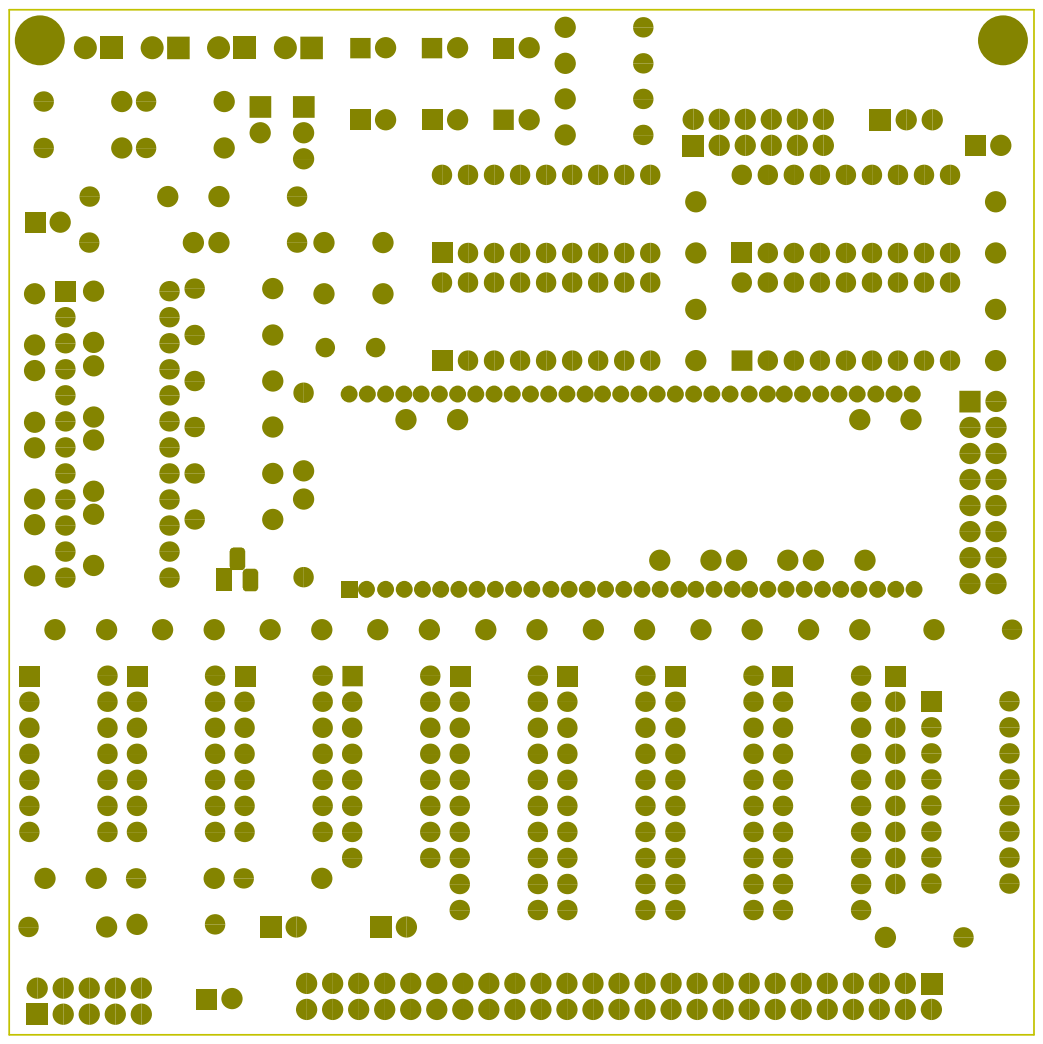
[picture p126: page 6]



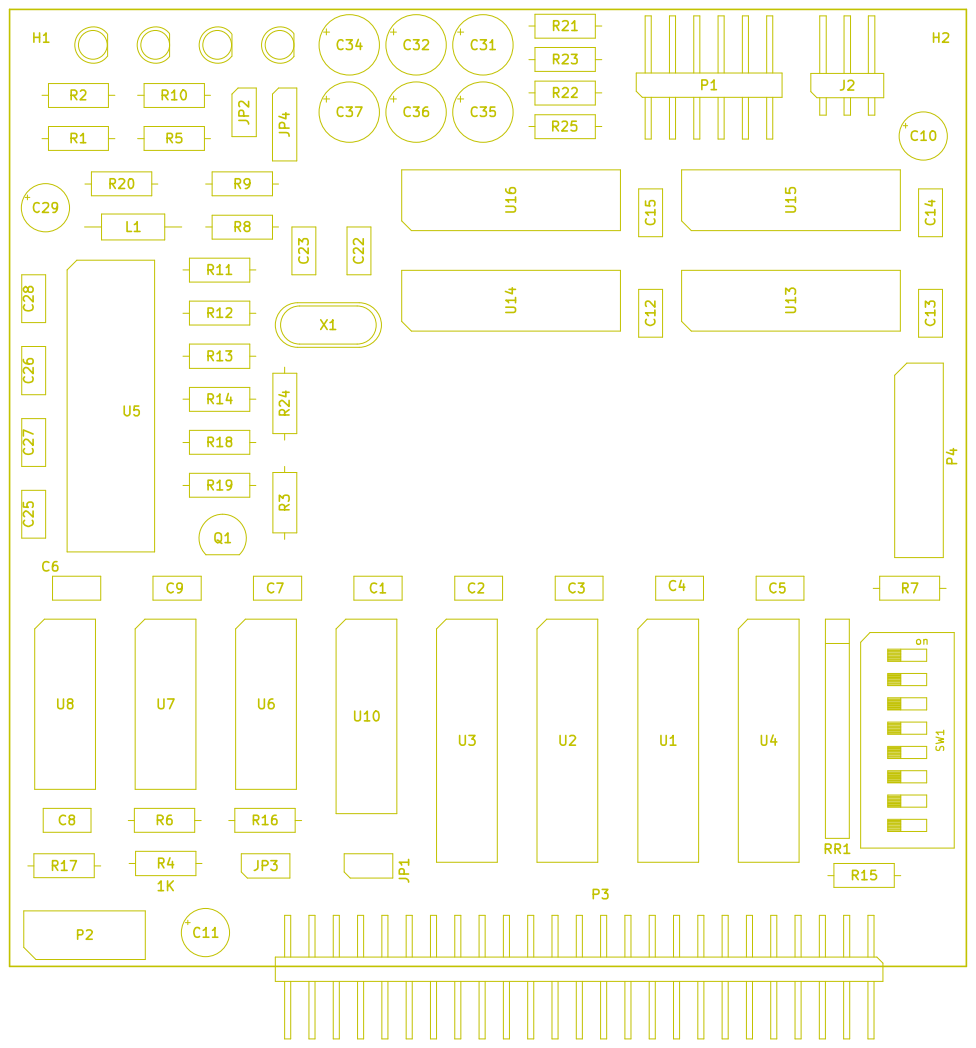
[picture p127: page 9]

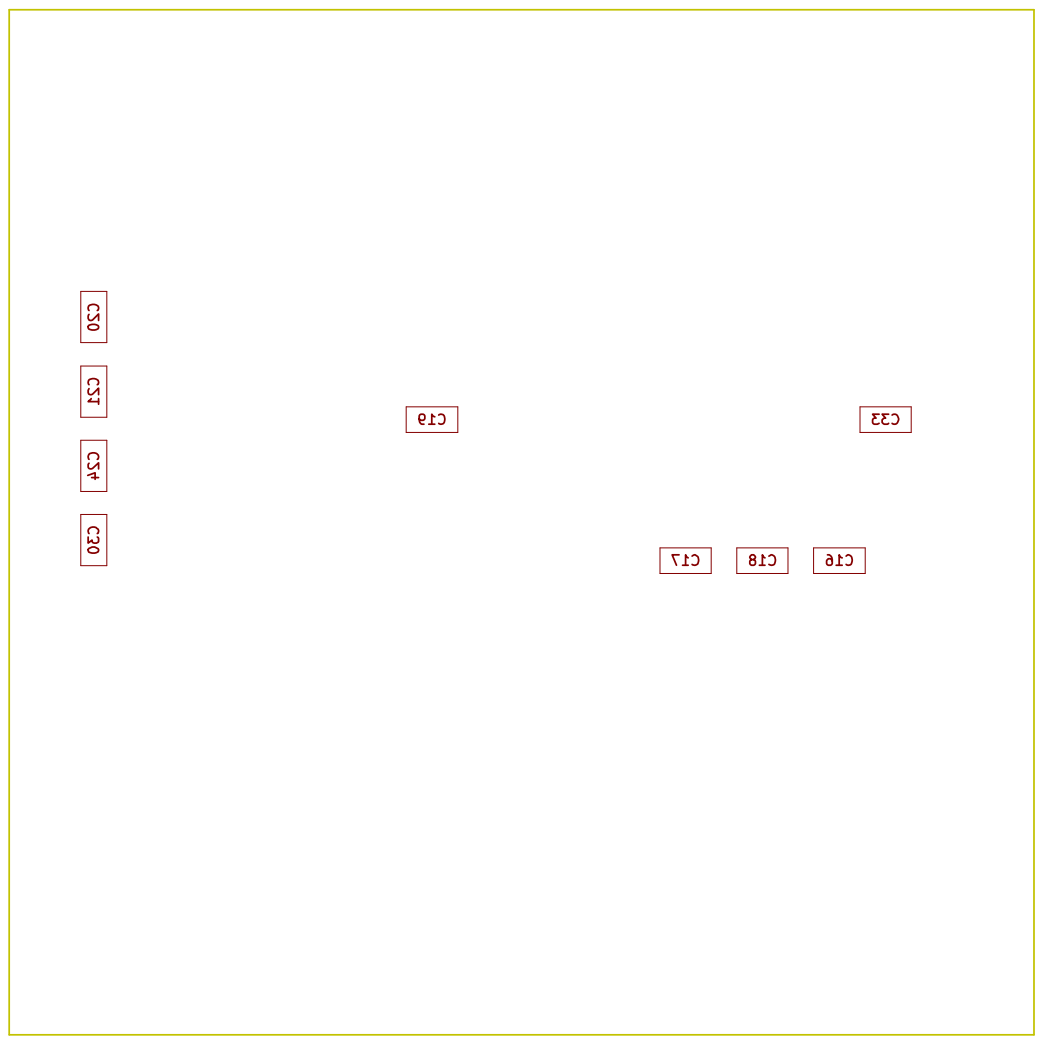
[picture p128: page 10]
