lynchaj/nhyodyne/Z80VDP1A/Z80VDP1A-PCB.pdf

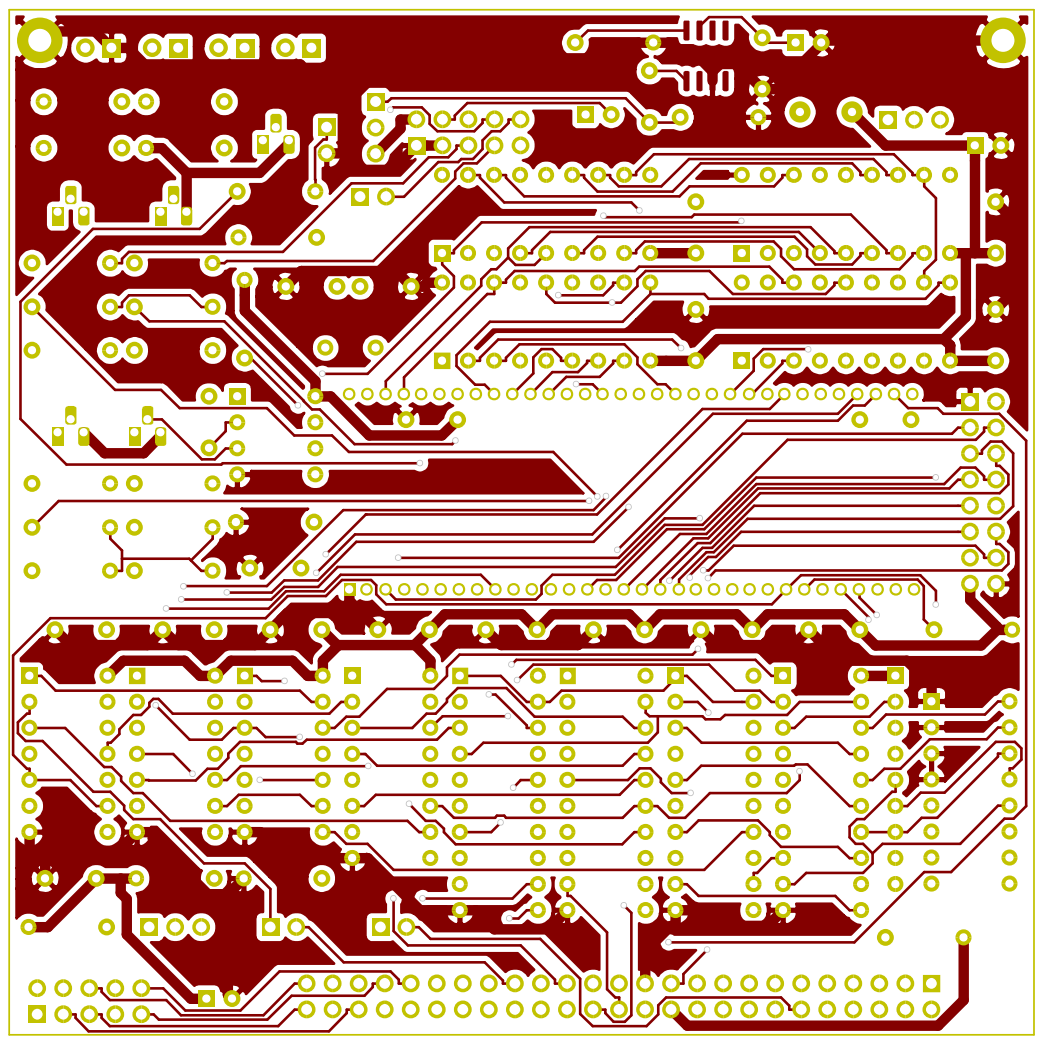
[picture p129: page 1]

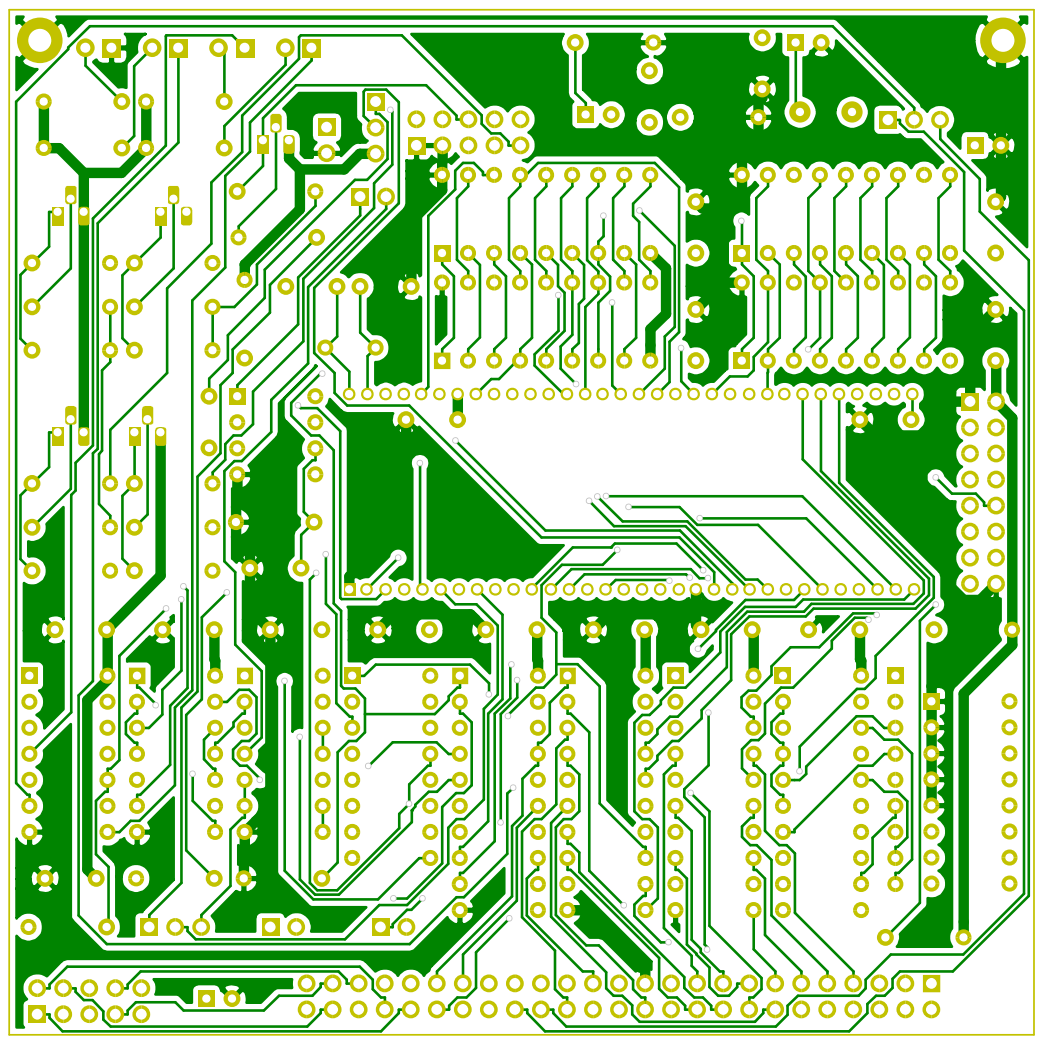
[picture p130: page 2]

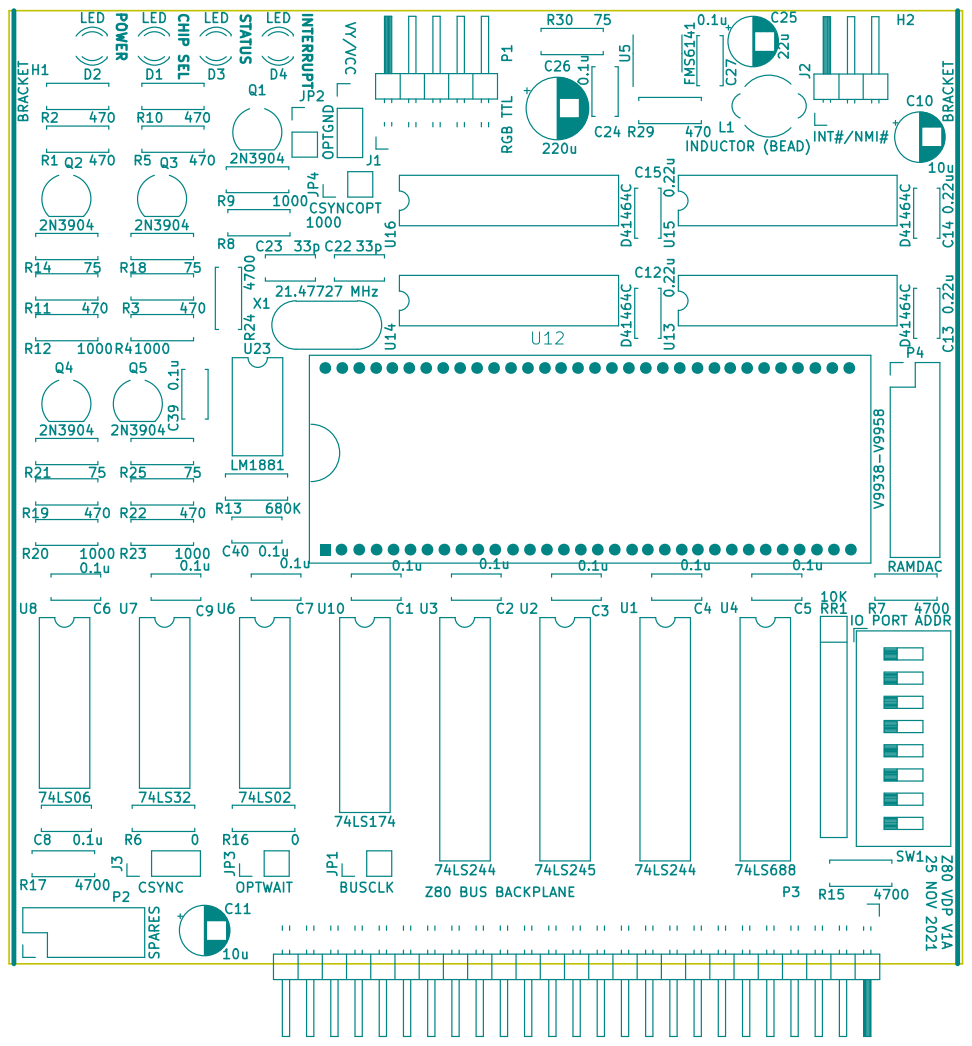
[picture p131: page 3]

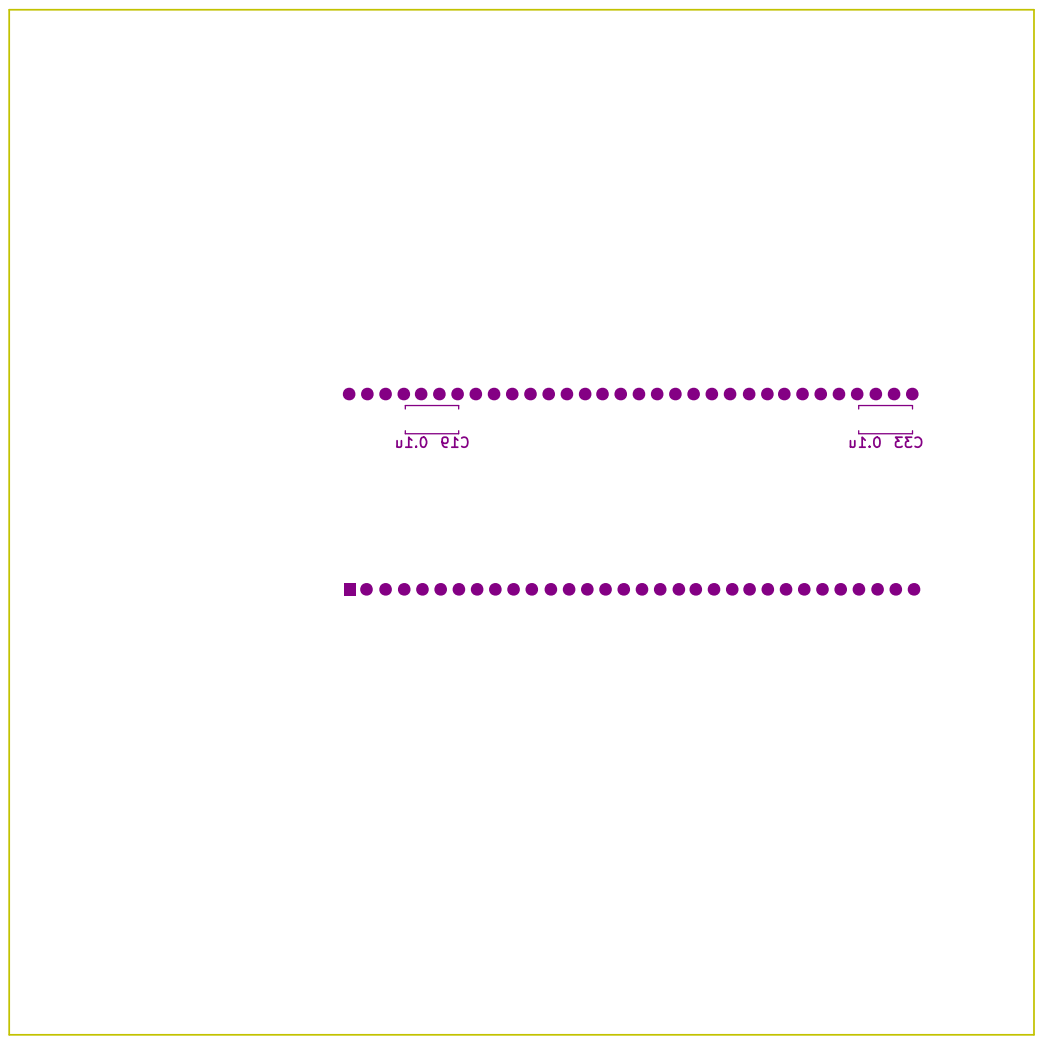
[picture p132: page 4]

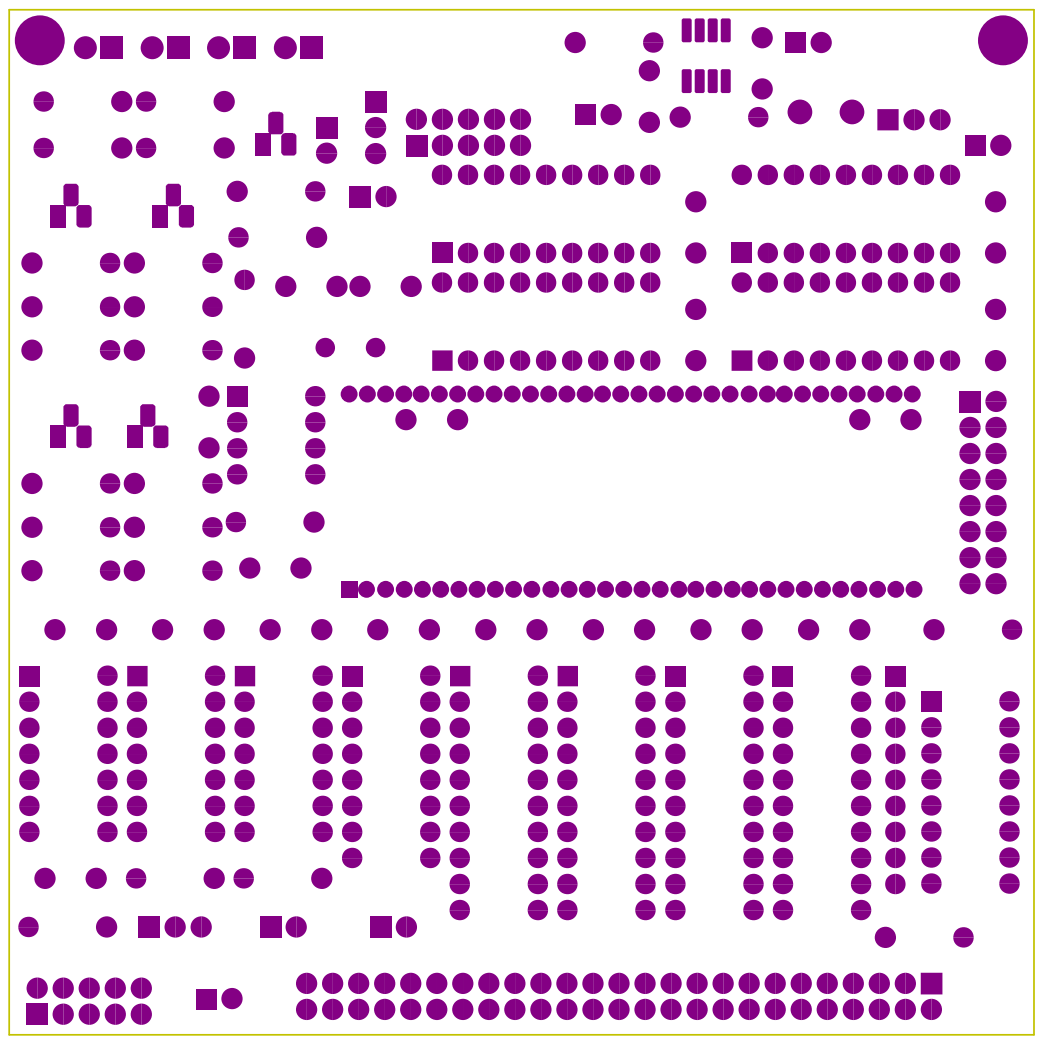
[picture p133: page 5]

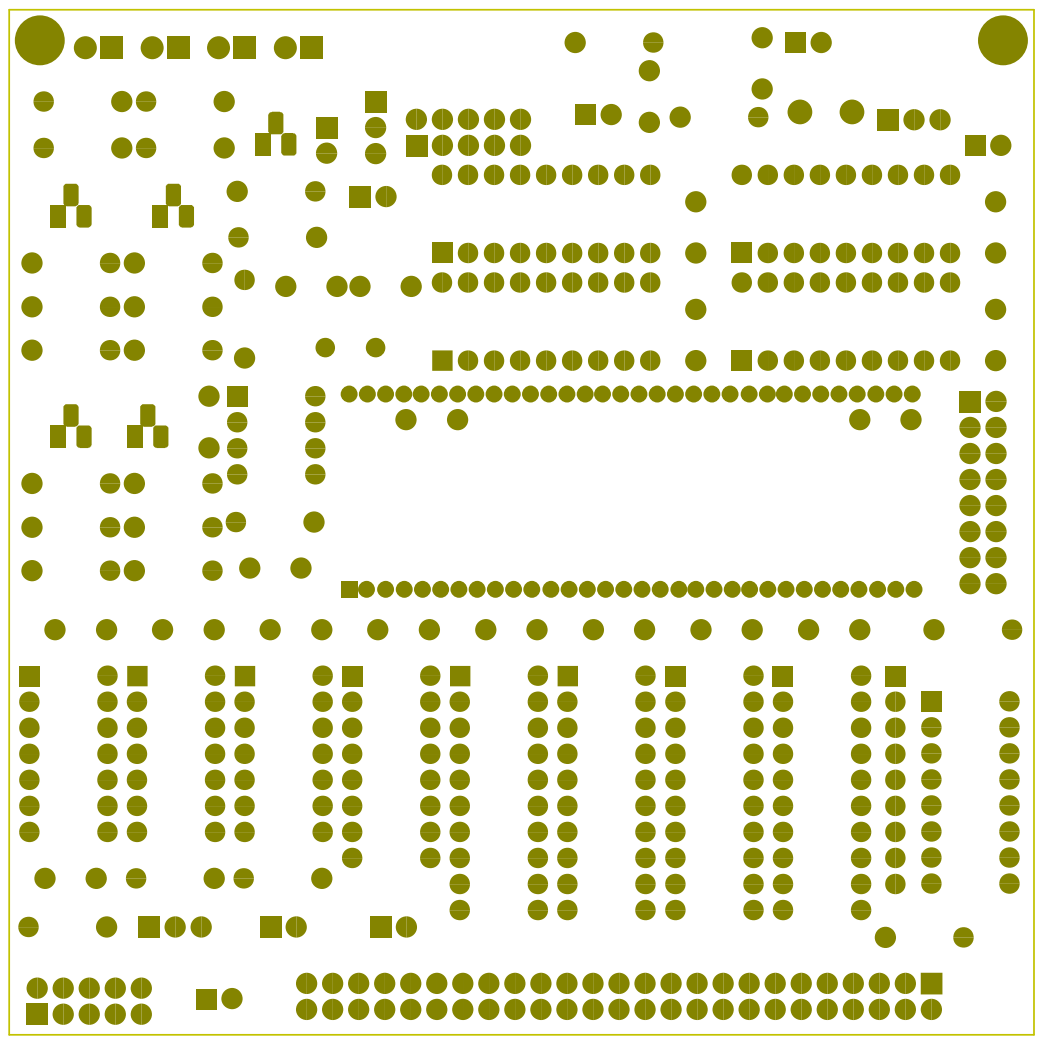
[picture p134: page 6]



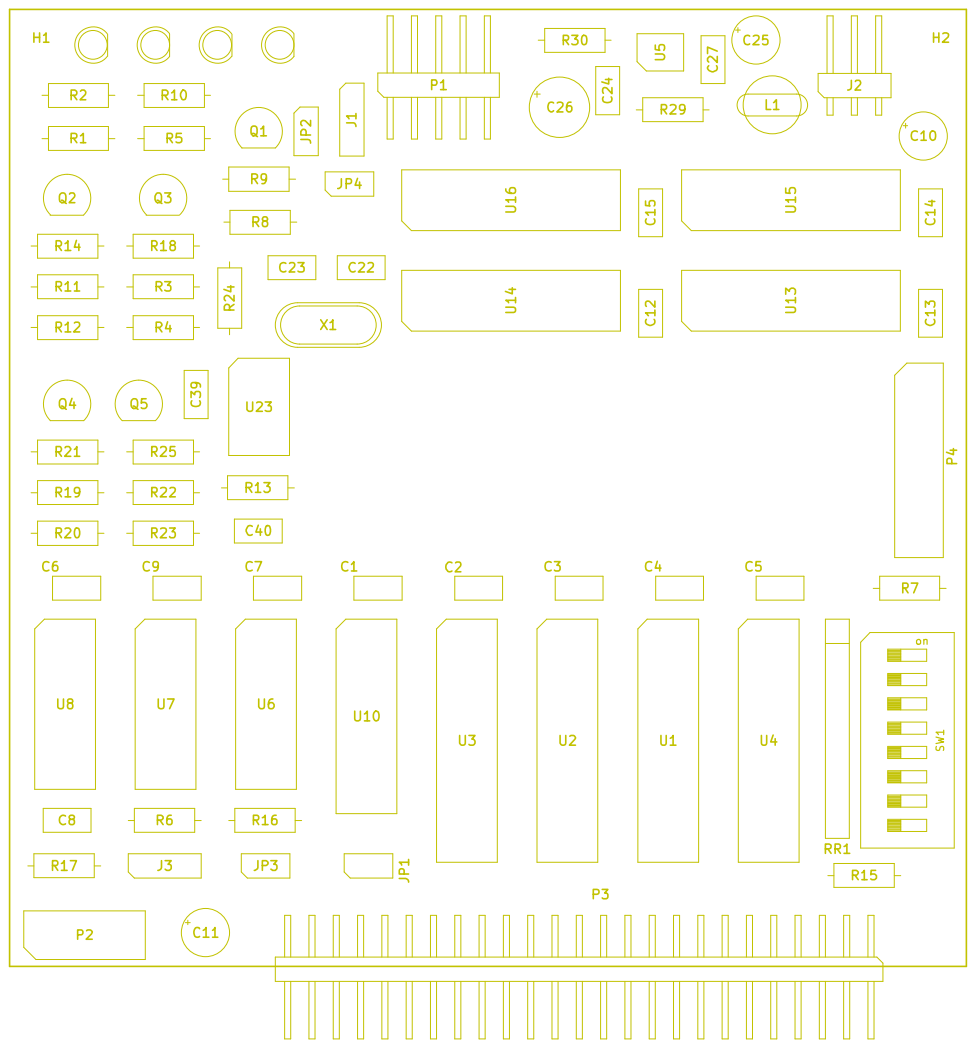
[picture p135: page 9]

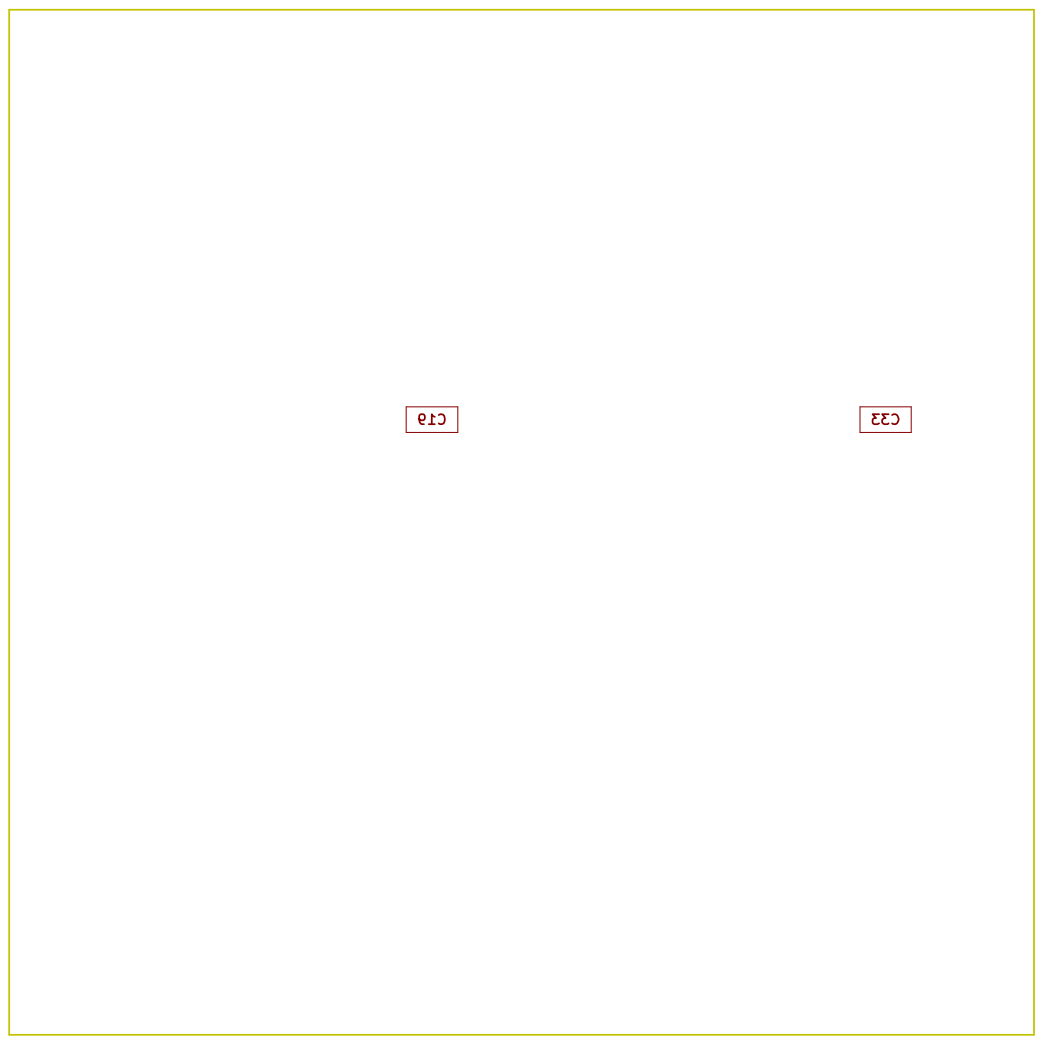
[picture p136: page 10]
