lynchaj/nhyodyne/Z80PSG1/Z80PSG1-PCB.pdf

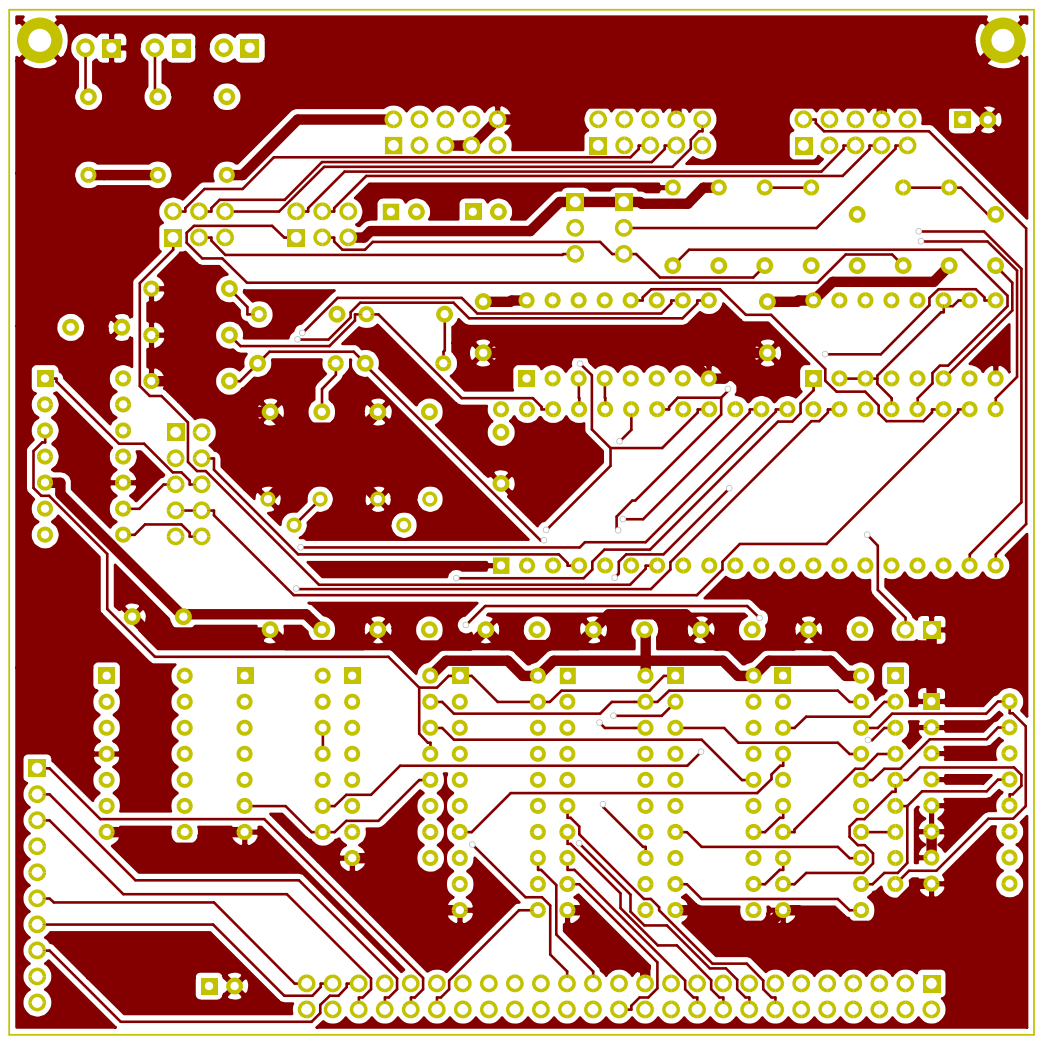
[picture p137: page 1]

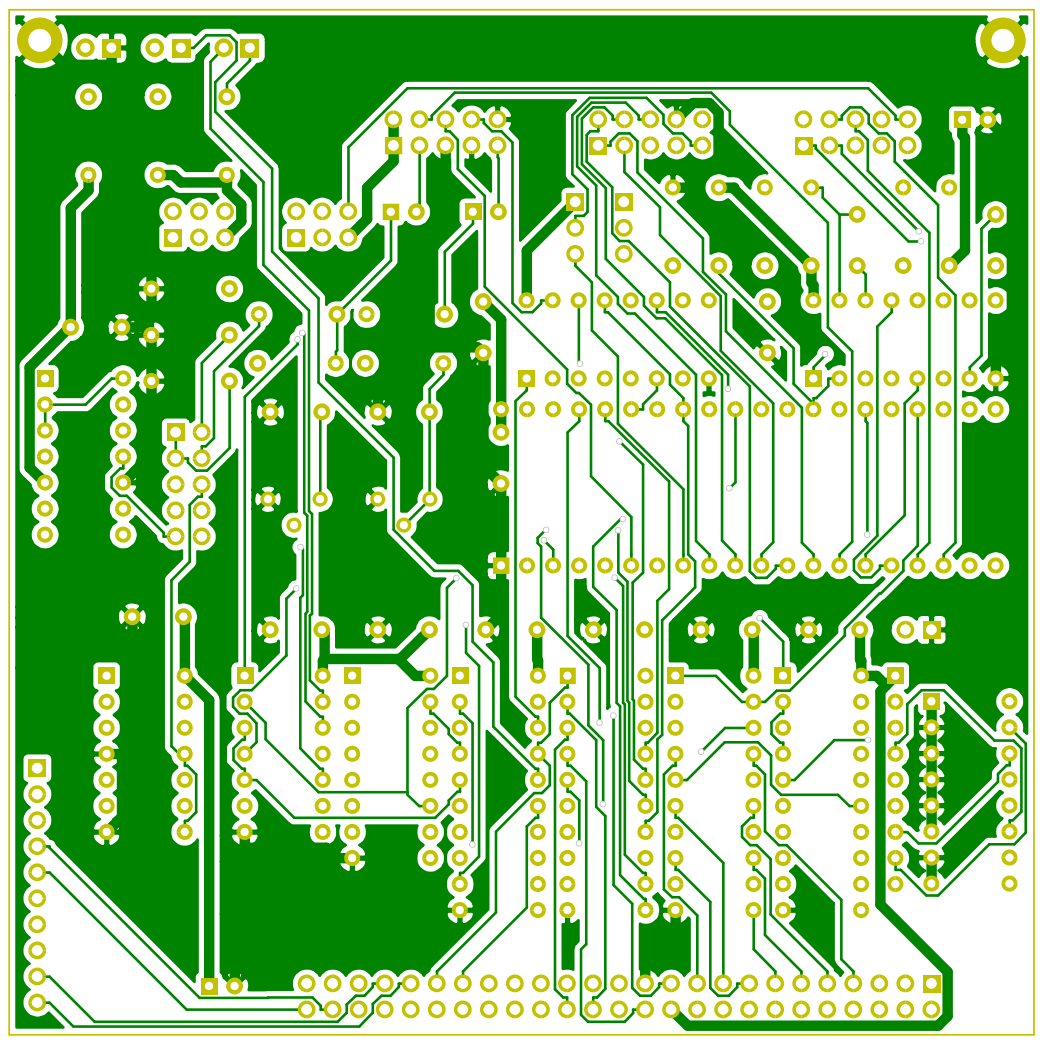
[picture p138: page 2]

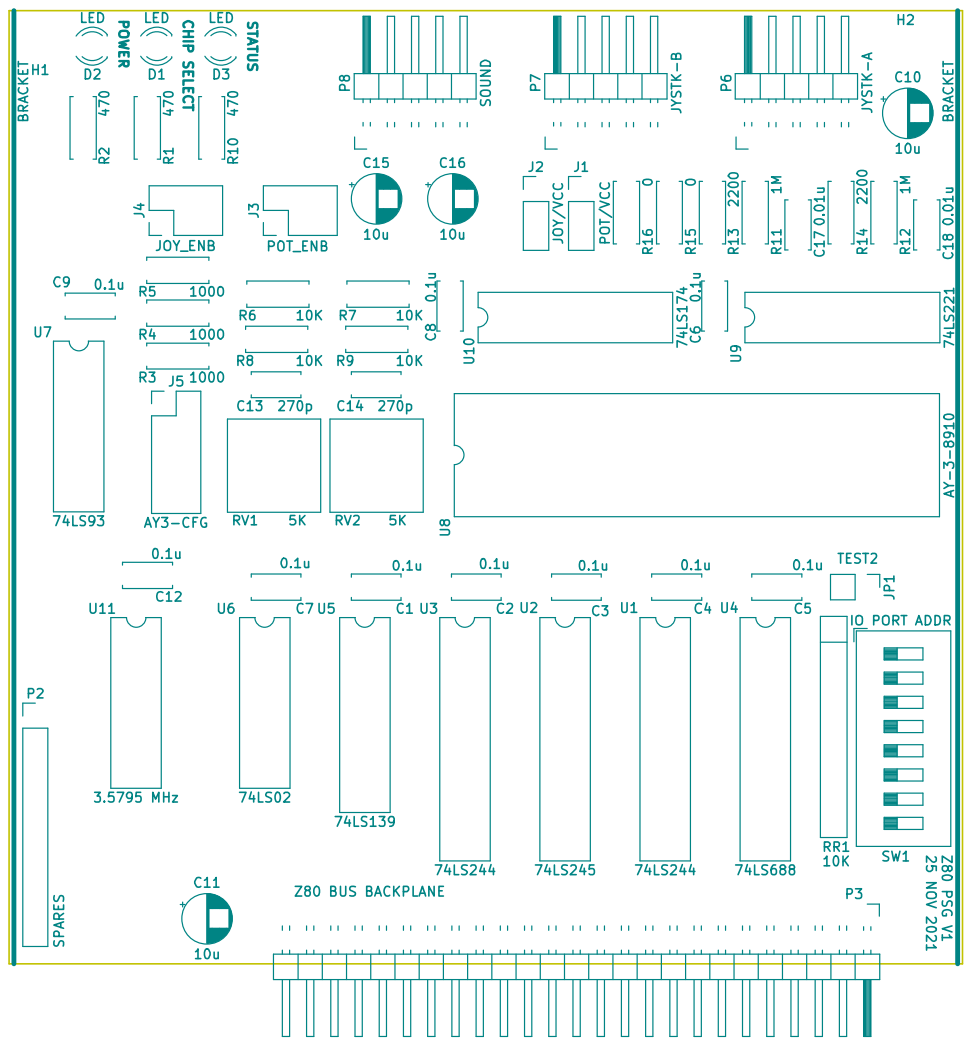
[picture p139: page 3]

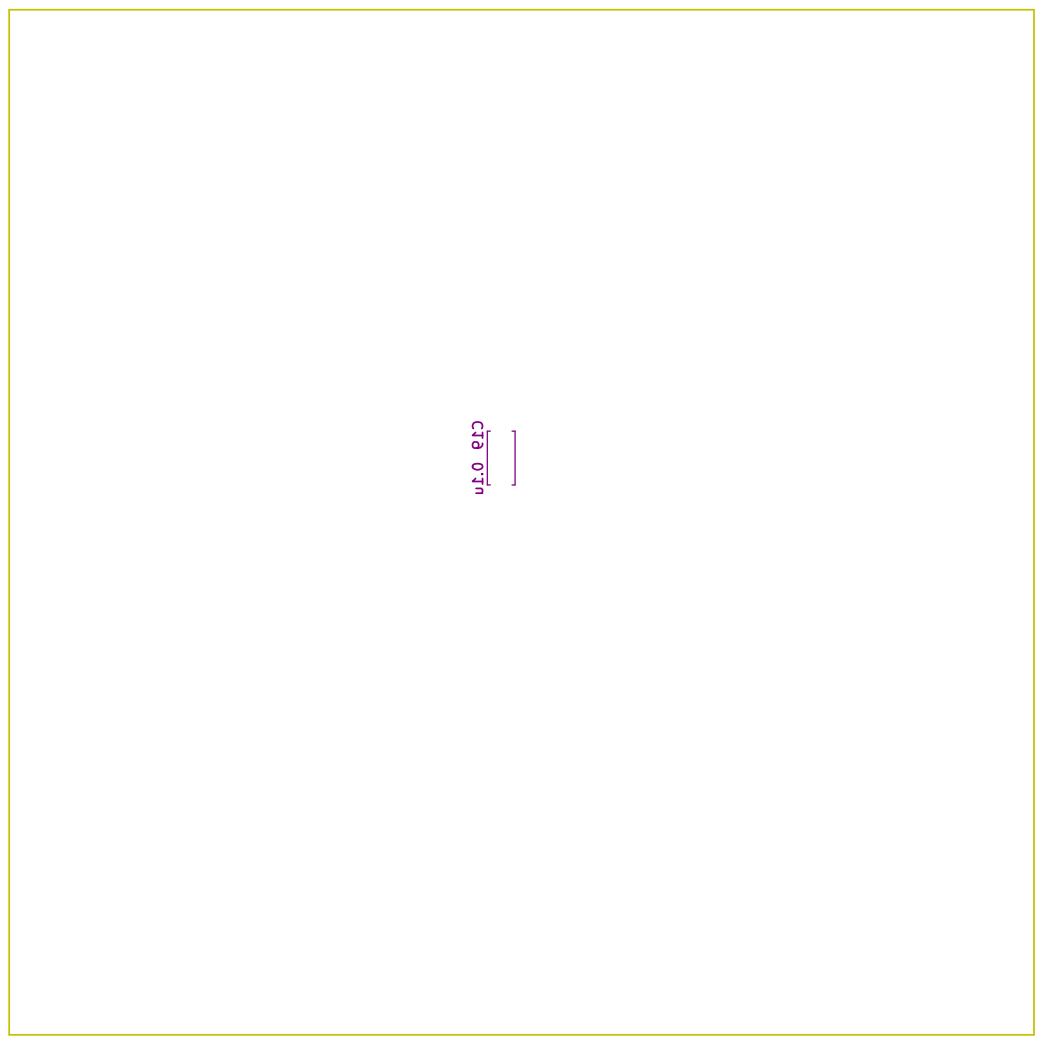
[picture p140: page 4]

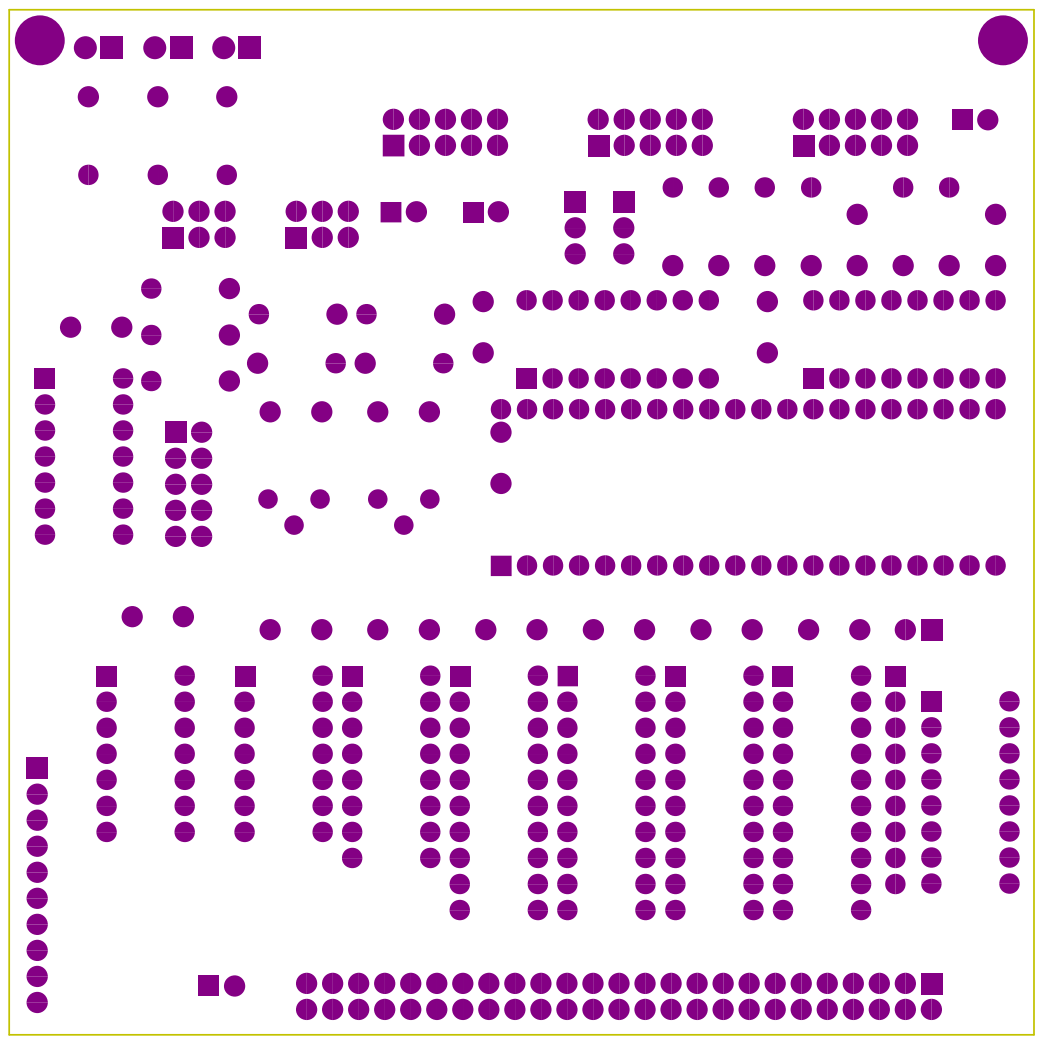
[picture p141: page 5]

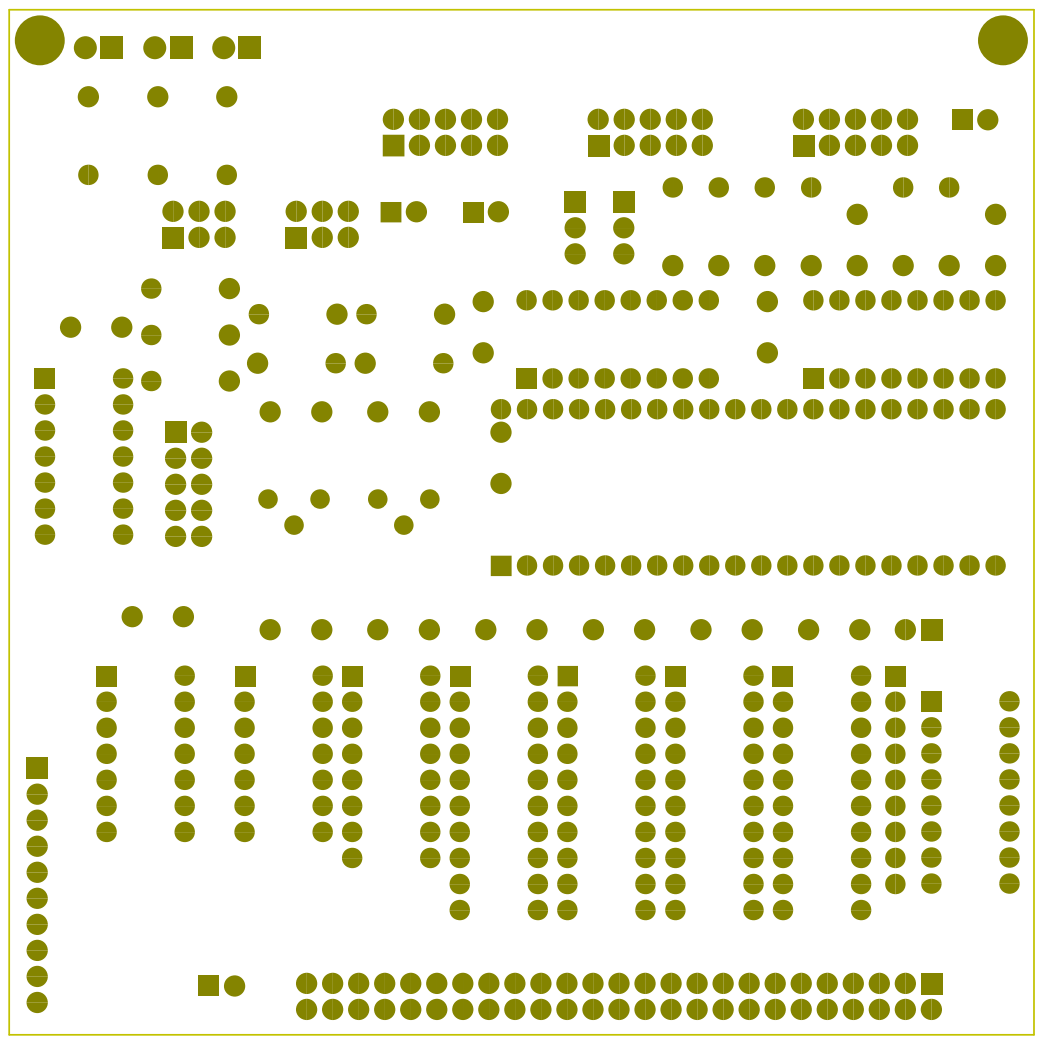
[picture p142: page 6]



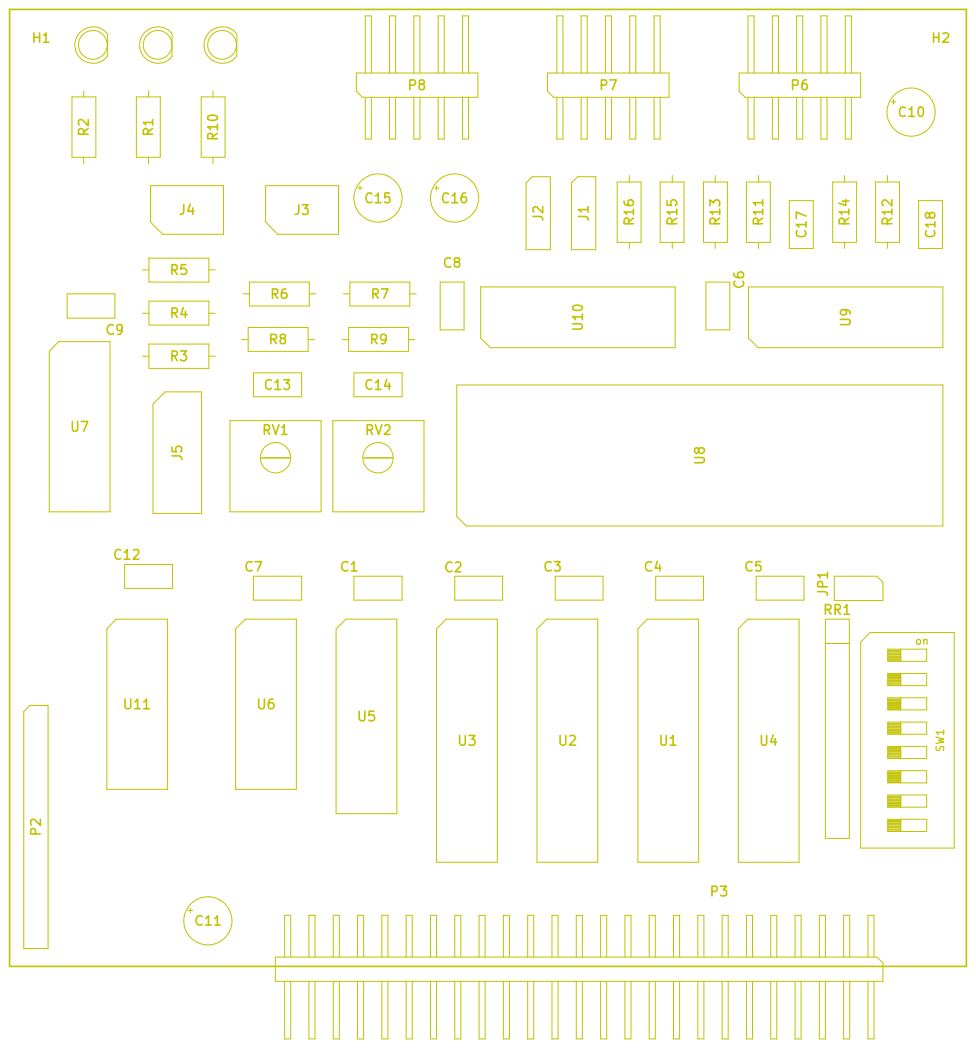
[picture p143: page 9]

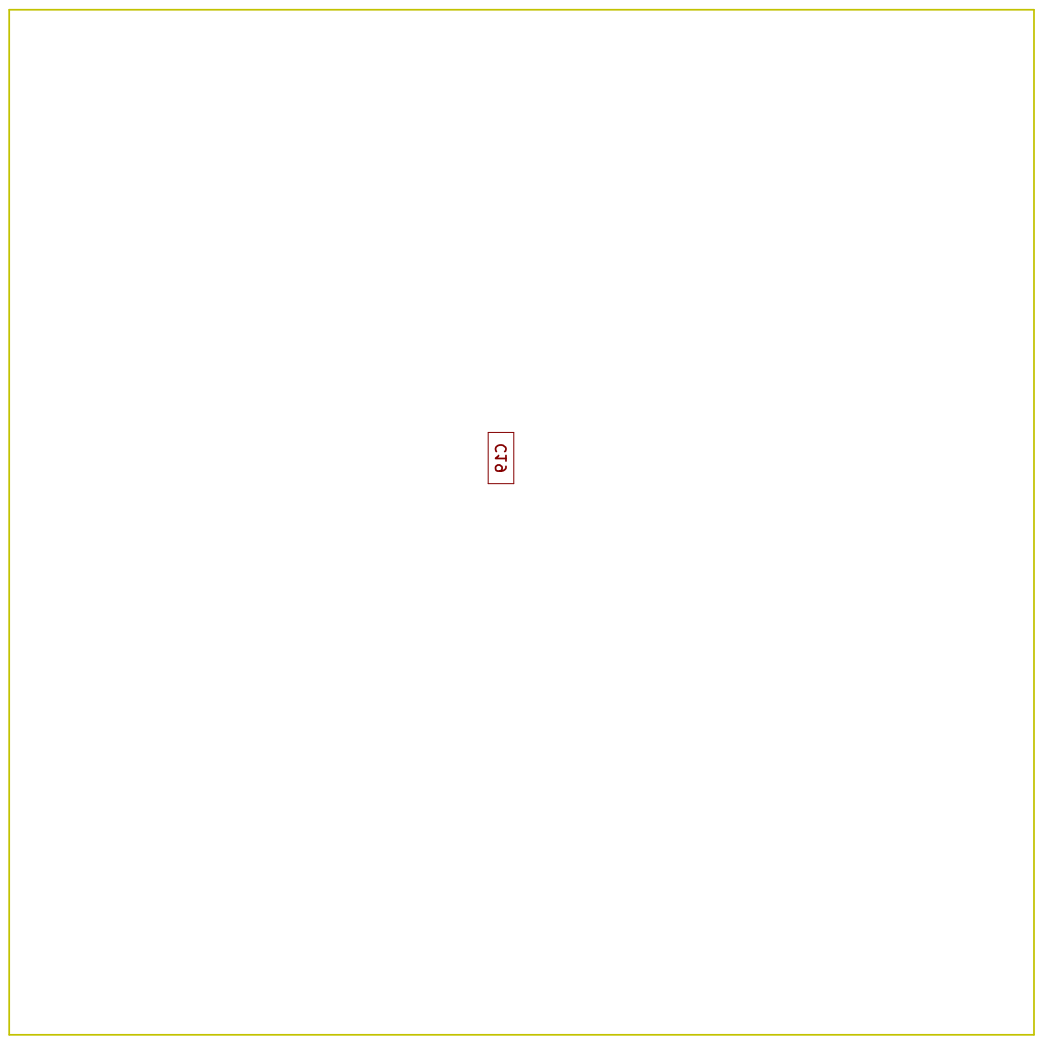
[picture p144: page 10]
