lynchaj/nhyodyne/Z80DUALPIO2/Z80DUALPIO2-PCB.pdf

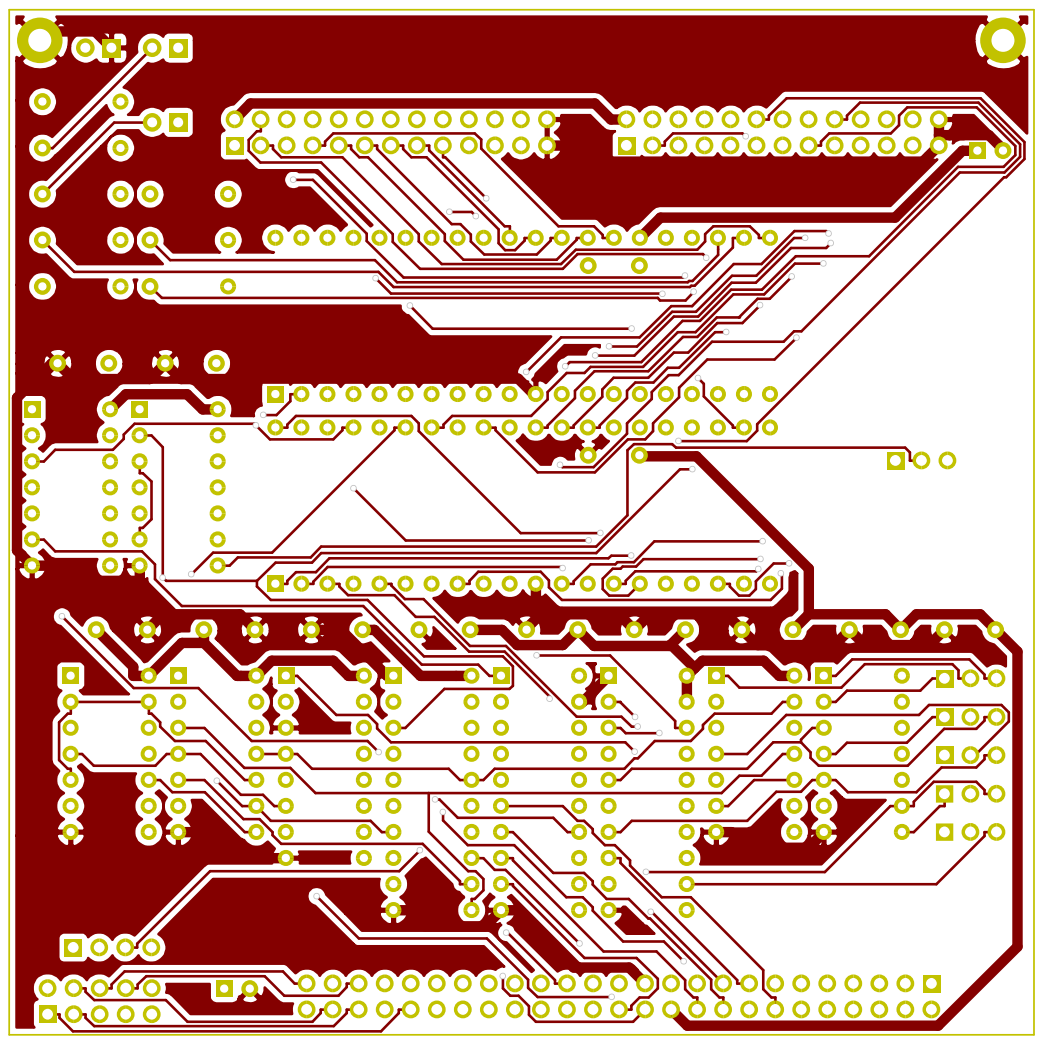
[picture p145: page 1]

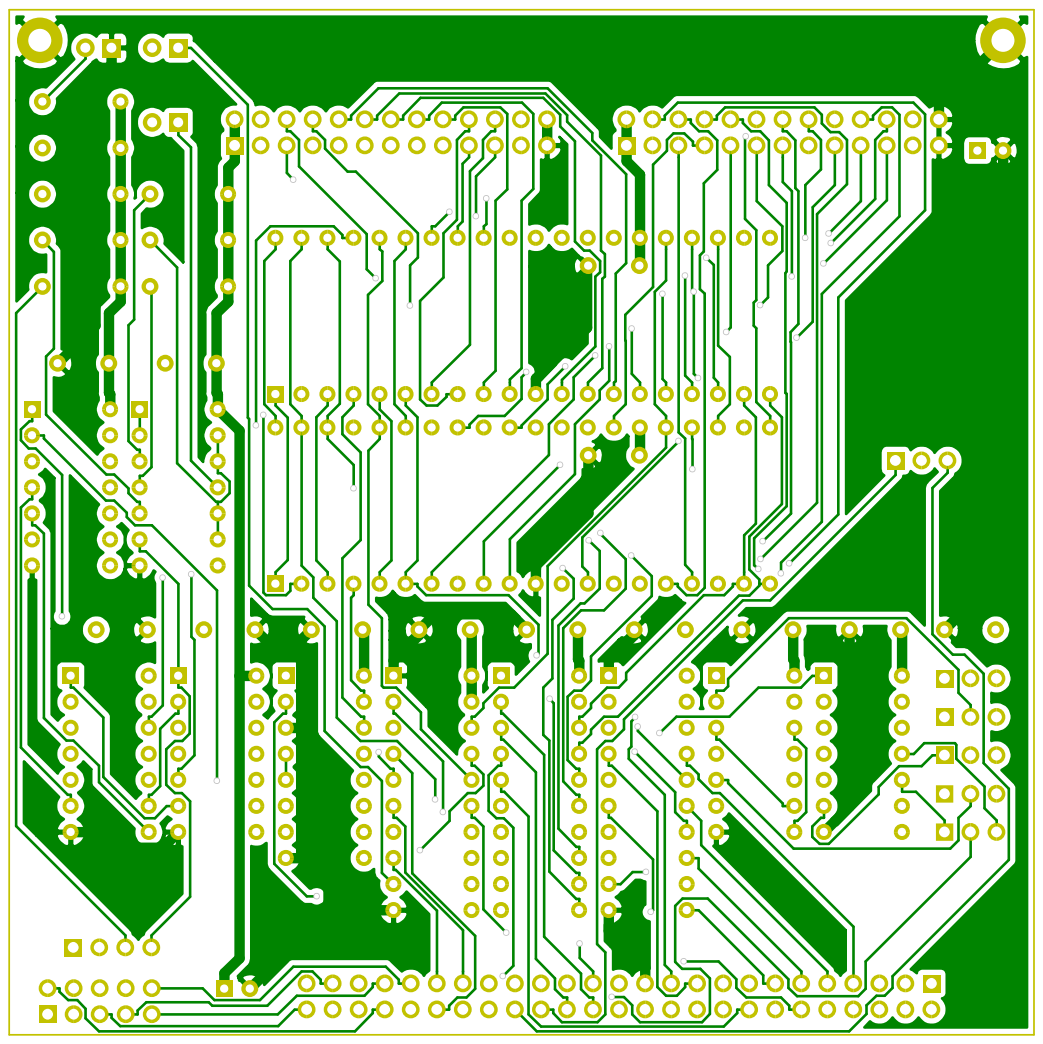
[picture p146: page 2]

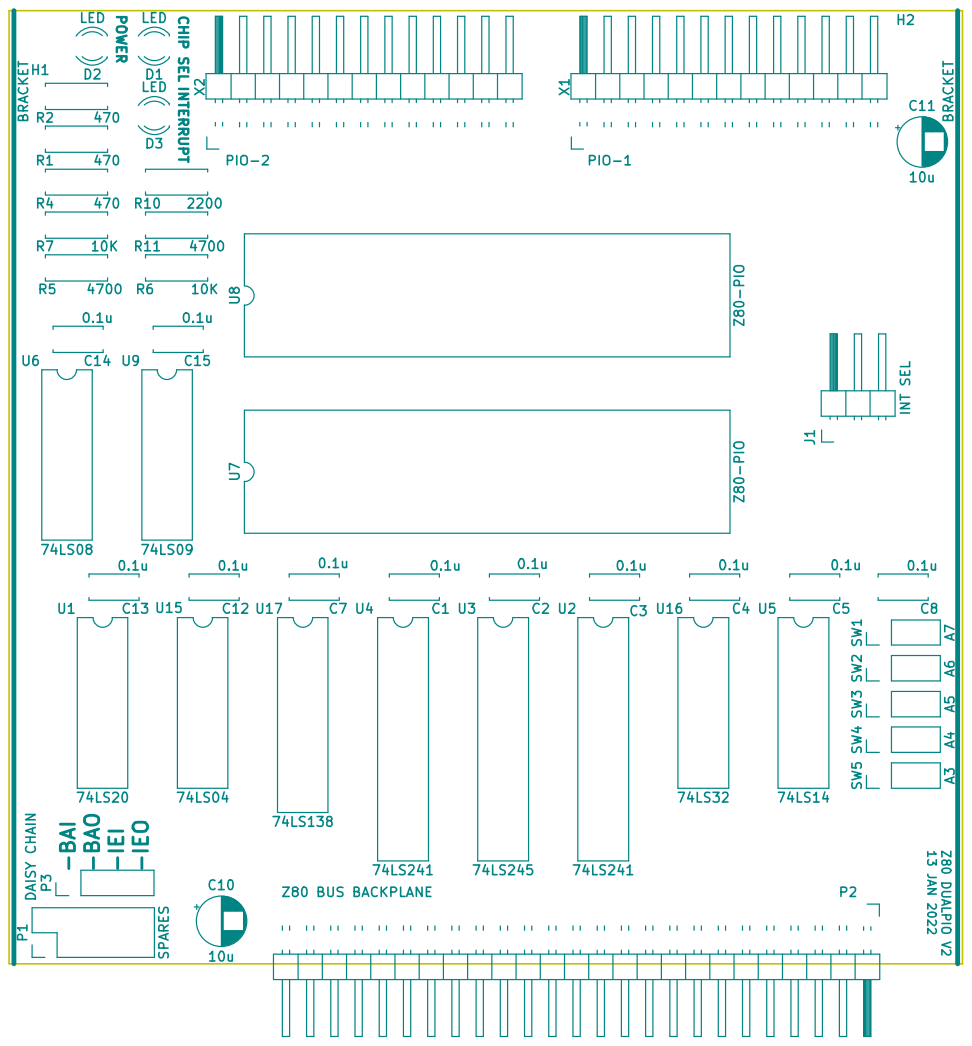
[picture p147: page 3]

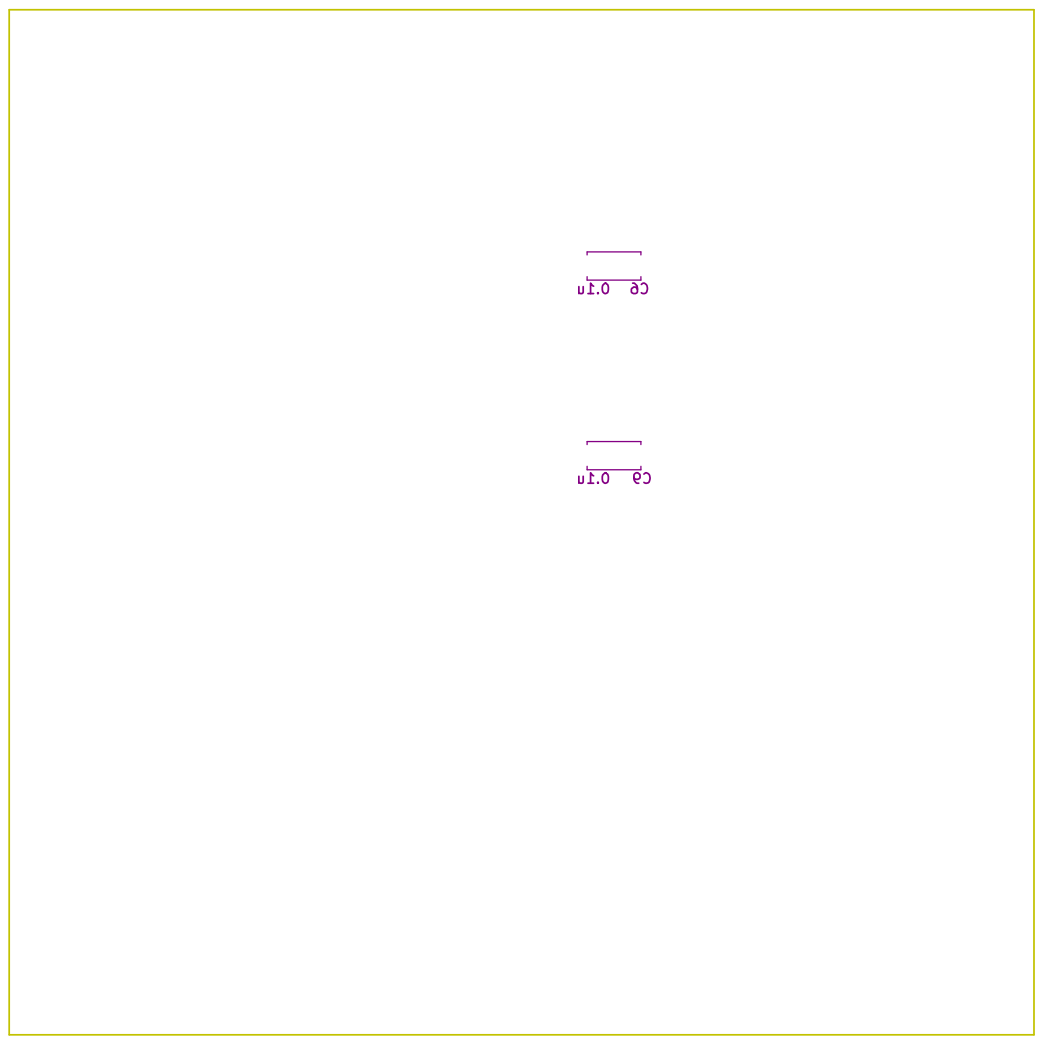
[picture p148: page 4]

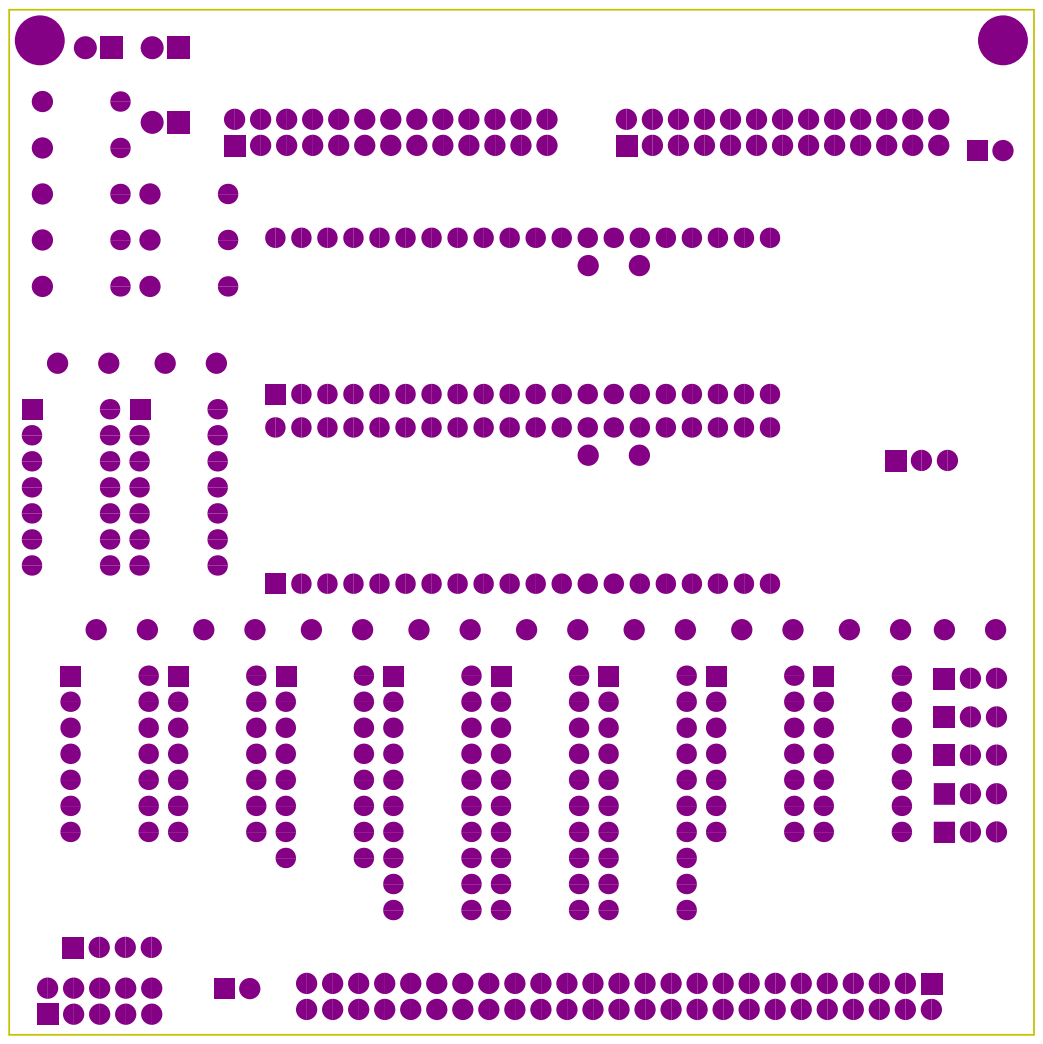
[picture p149: page 5]

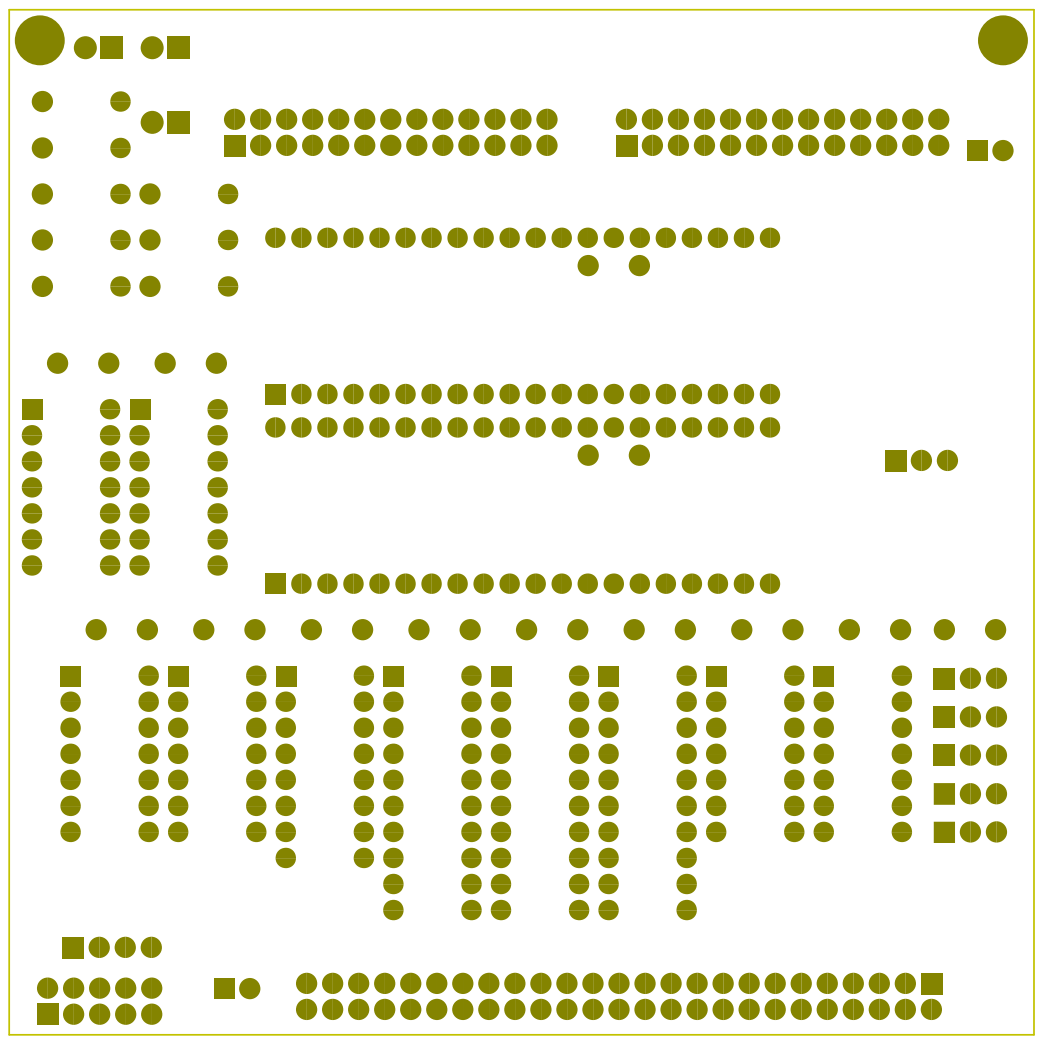
[picture p150: page 6]
