lynchaj/nhyodyne/Z80CTCDART2/Z80CTCDART2-PCB.pdf

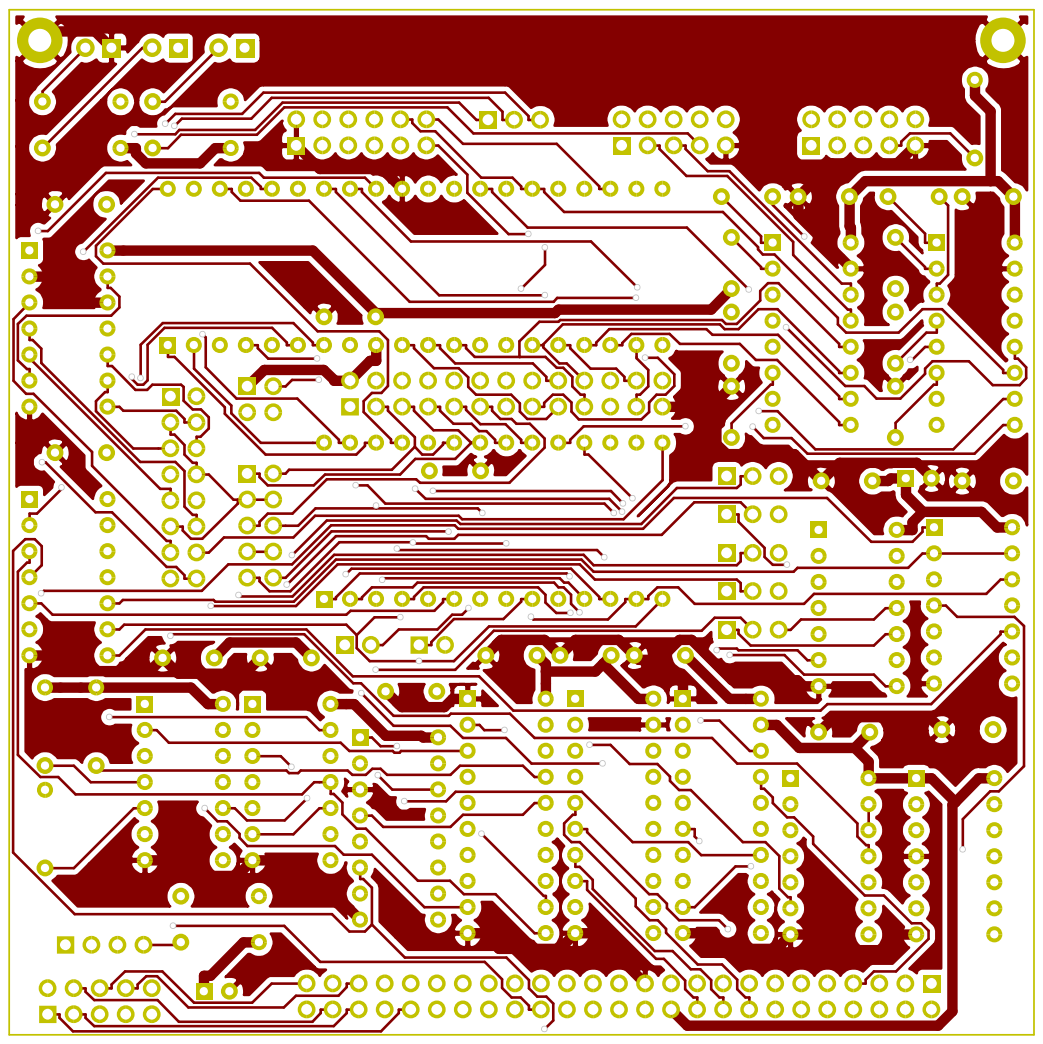
[picture p151: page 1]

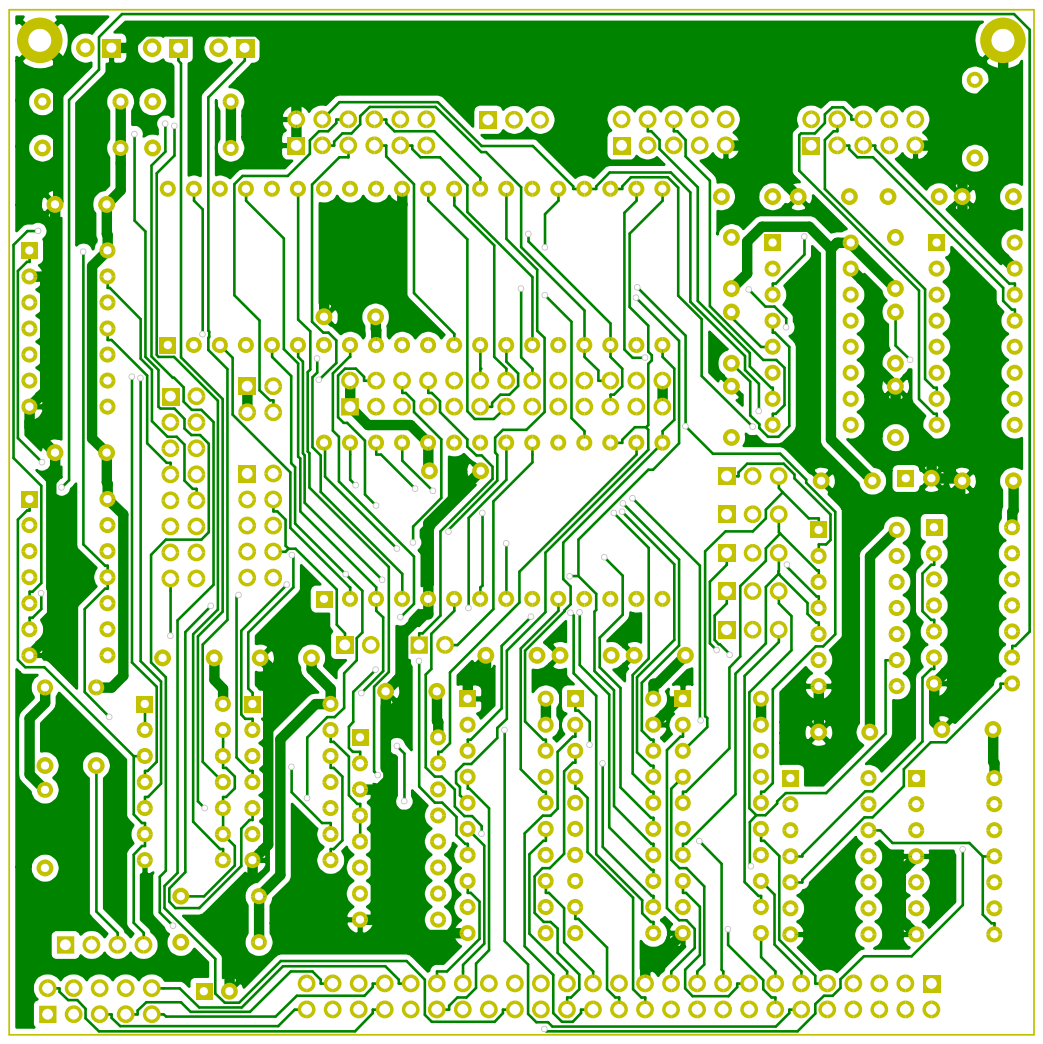
[picture p152: page 2]

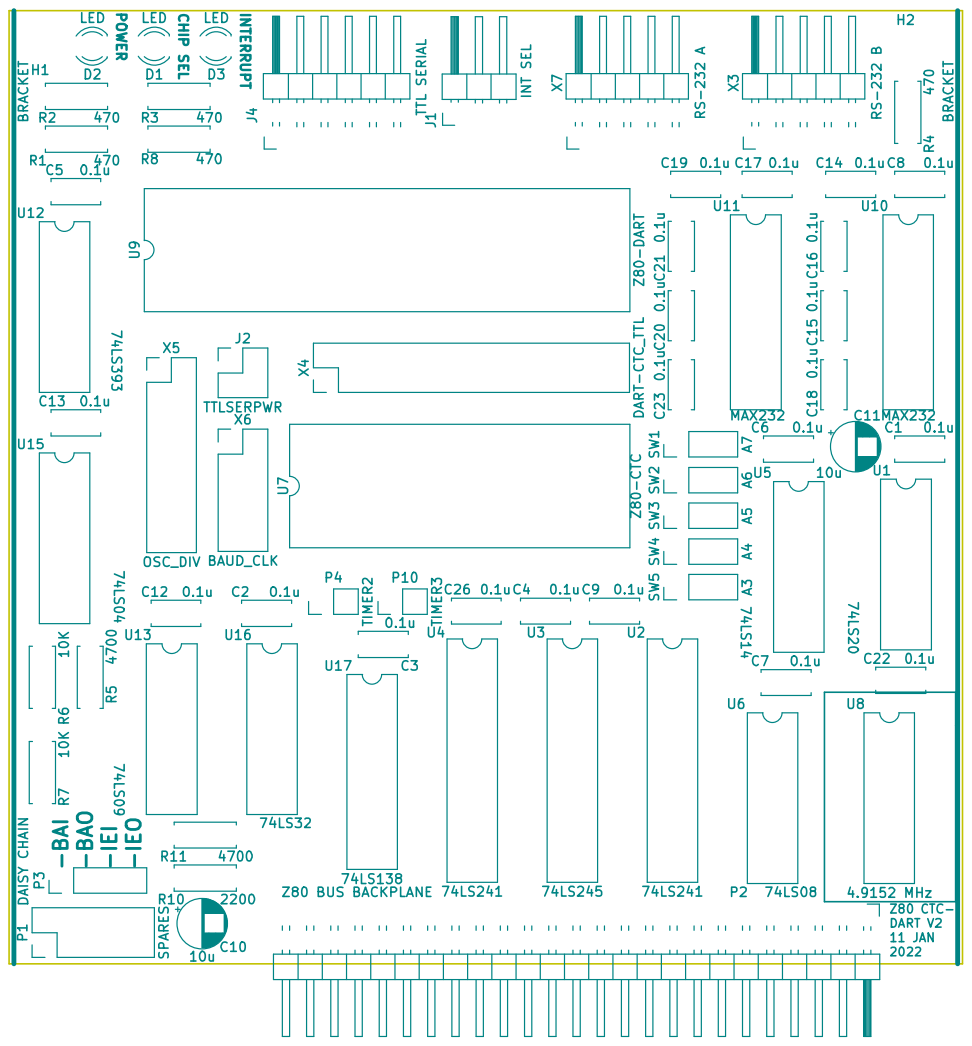
[picture p153: page 3]

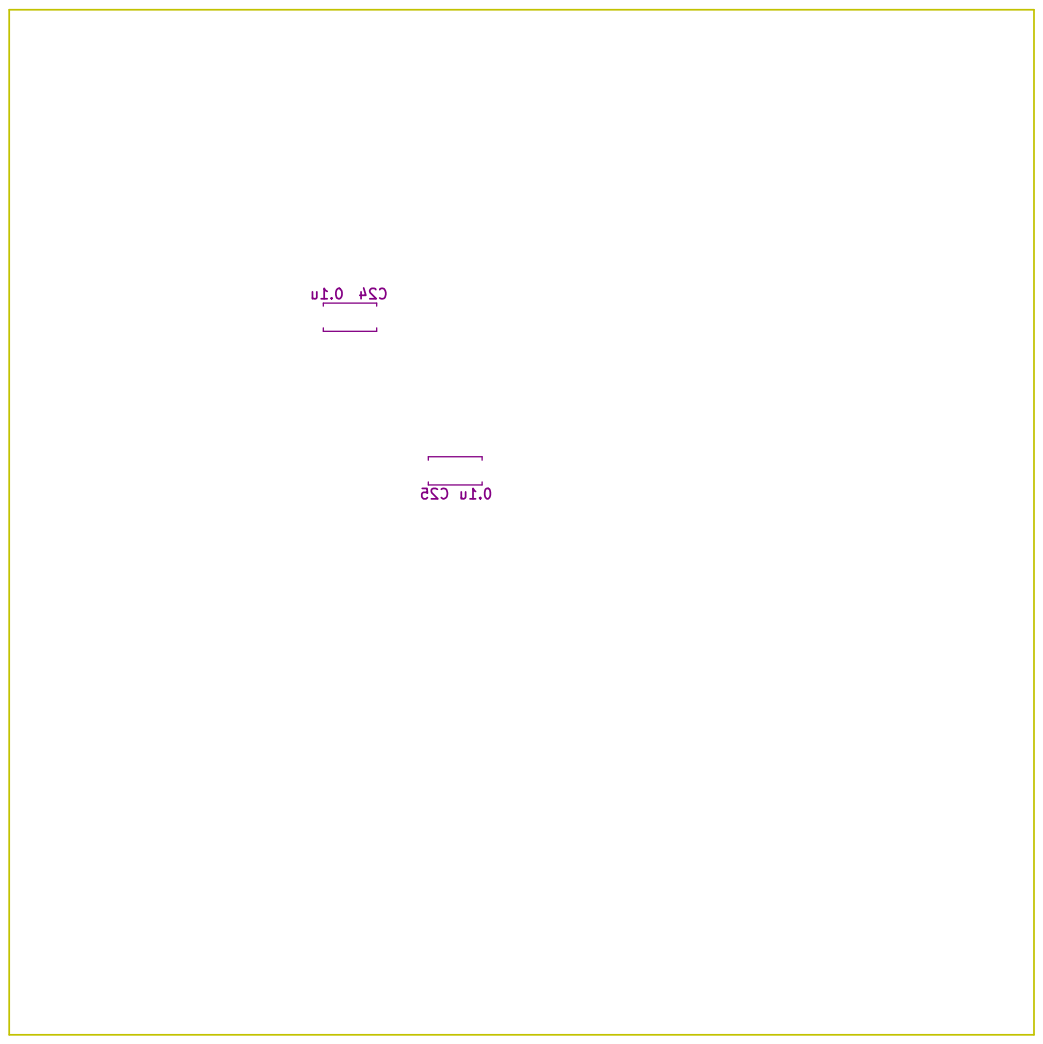
[picture p154: page 4]

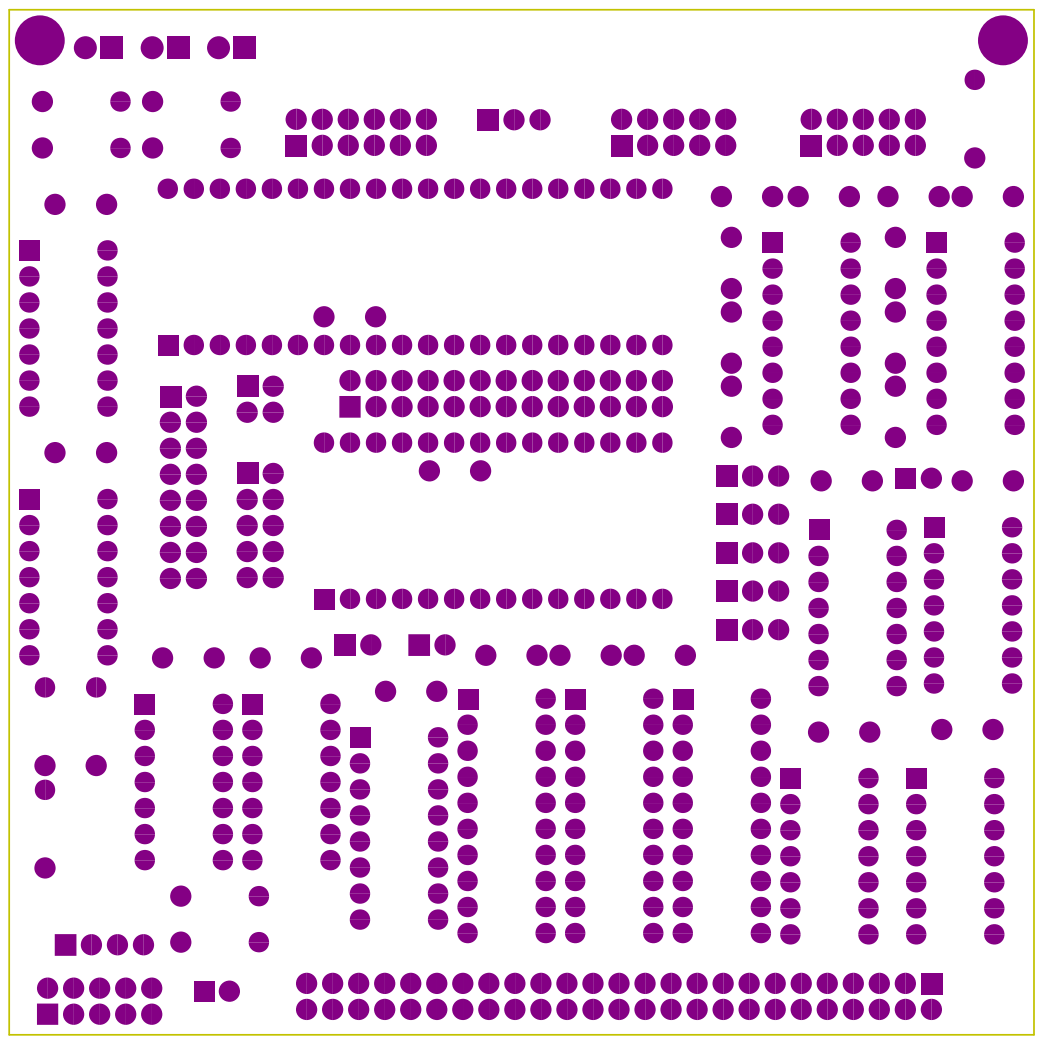
[picture p155: page 5]

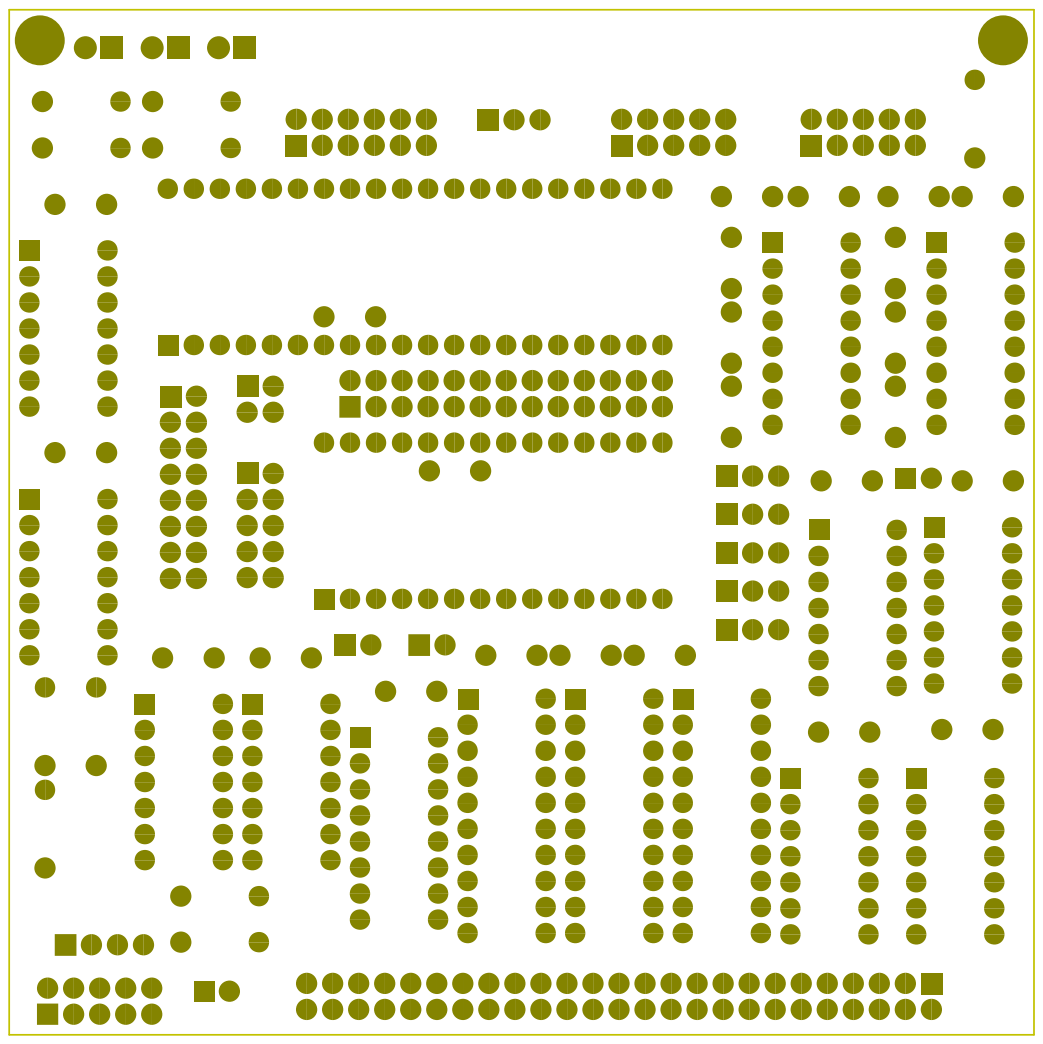
[picture p156: page 6]
