lynchaj/nhyodyne/Z80ENET/Z80ENET-PCB.pdf

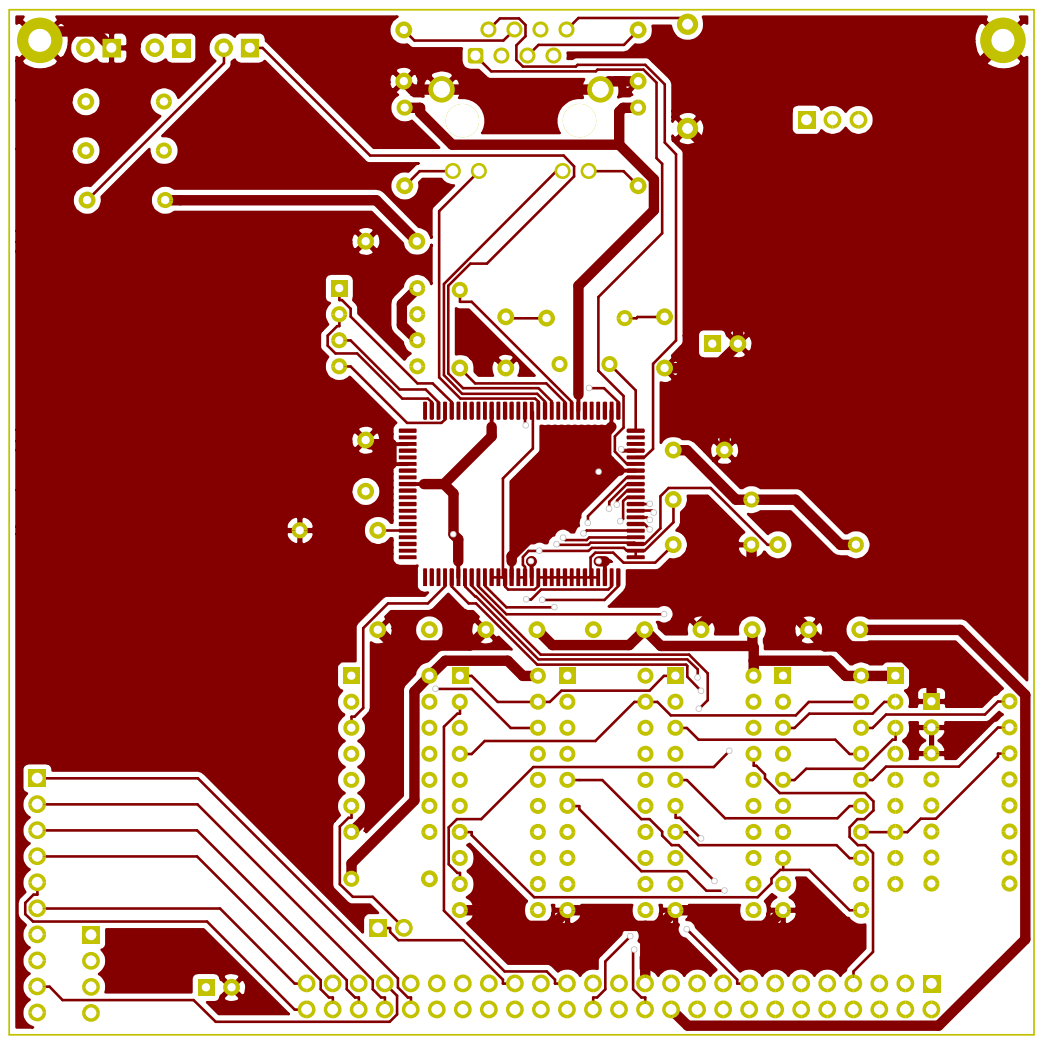
[picture p157: page 1]

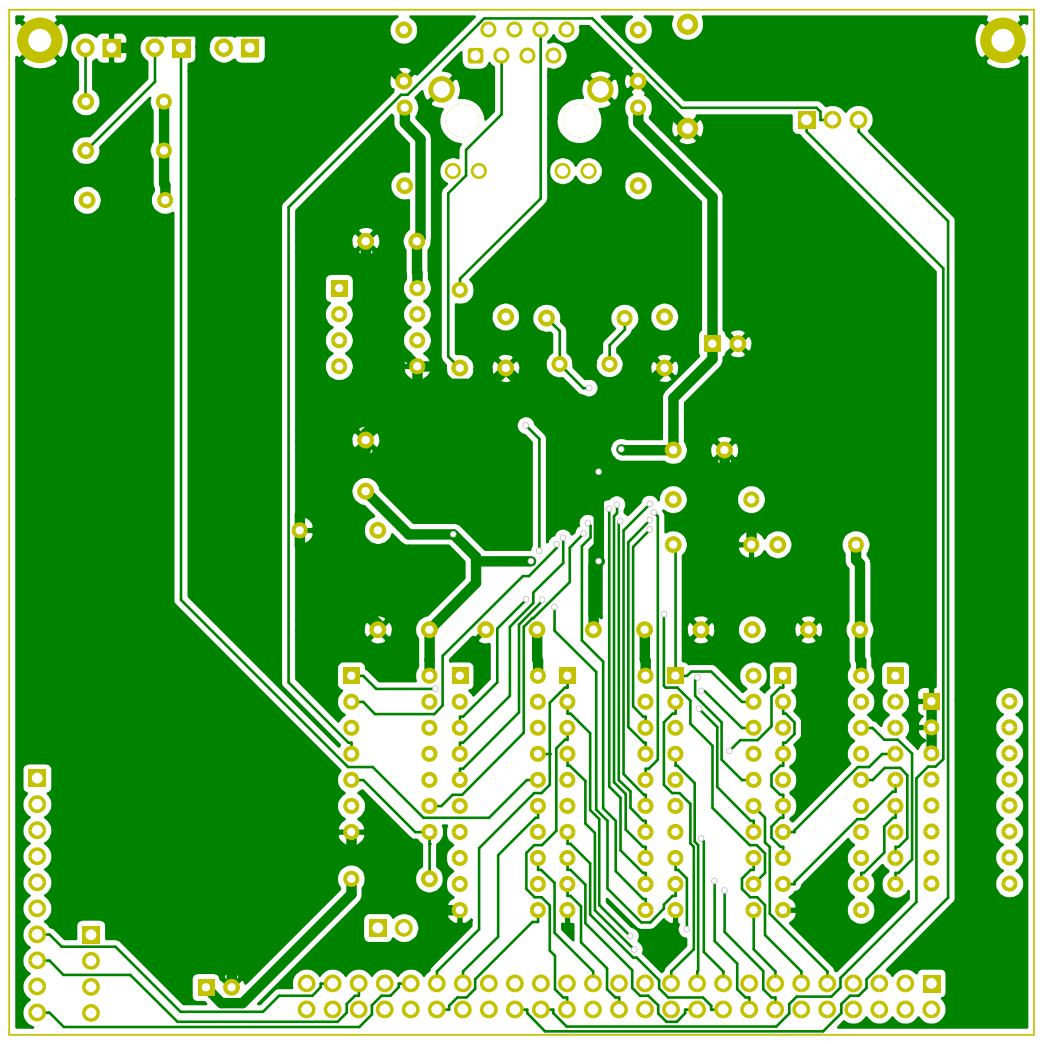
[picture p158: page 2]

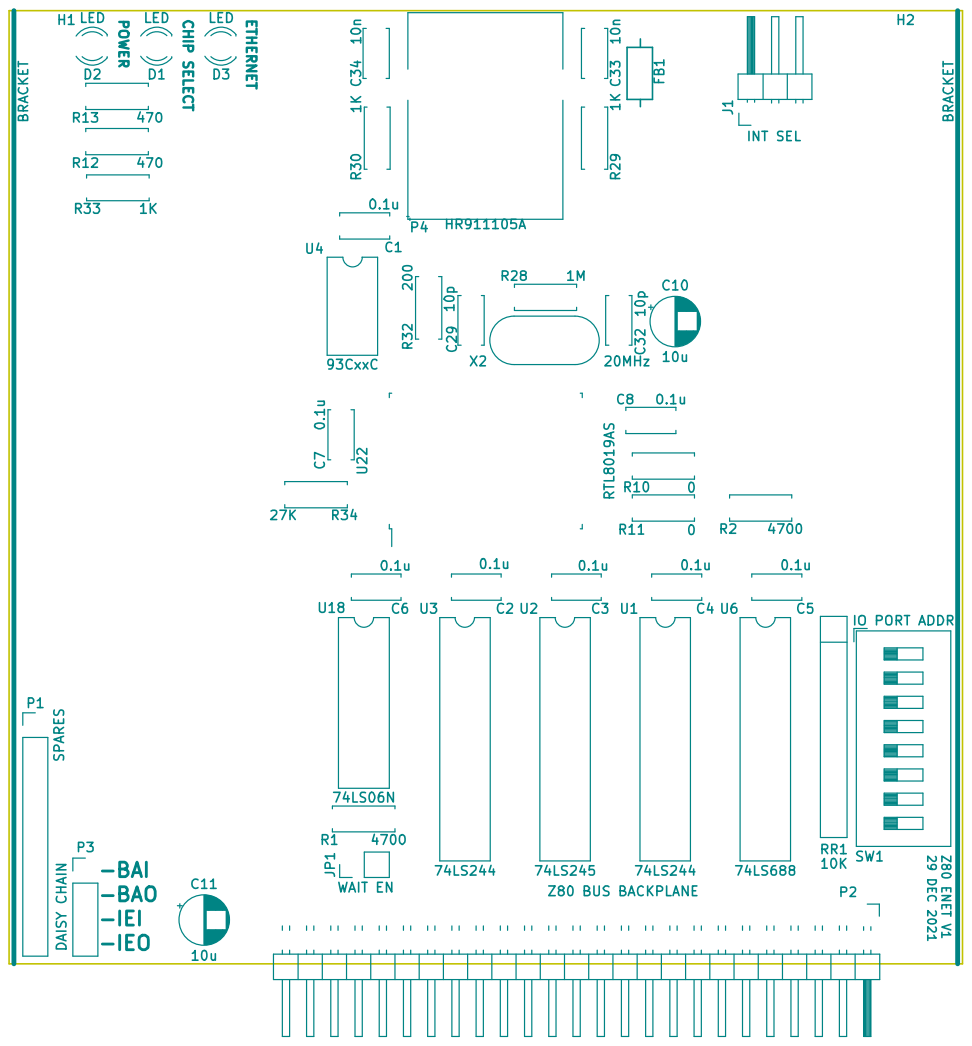
[picture p159: page 3]


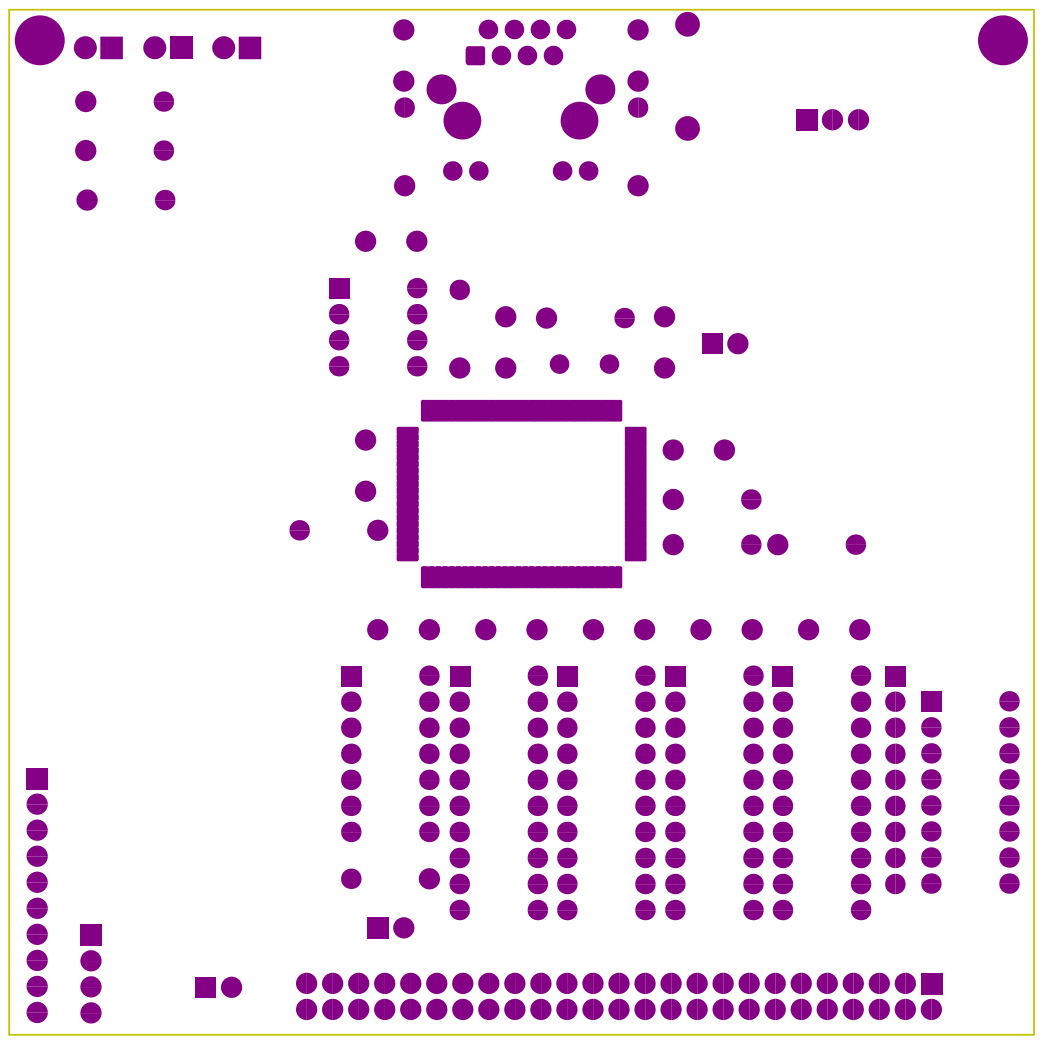
[picture p160: page 5]

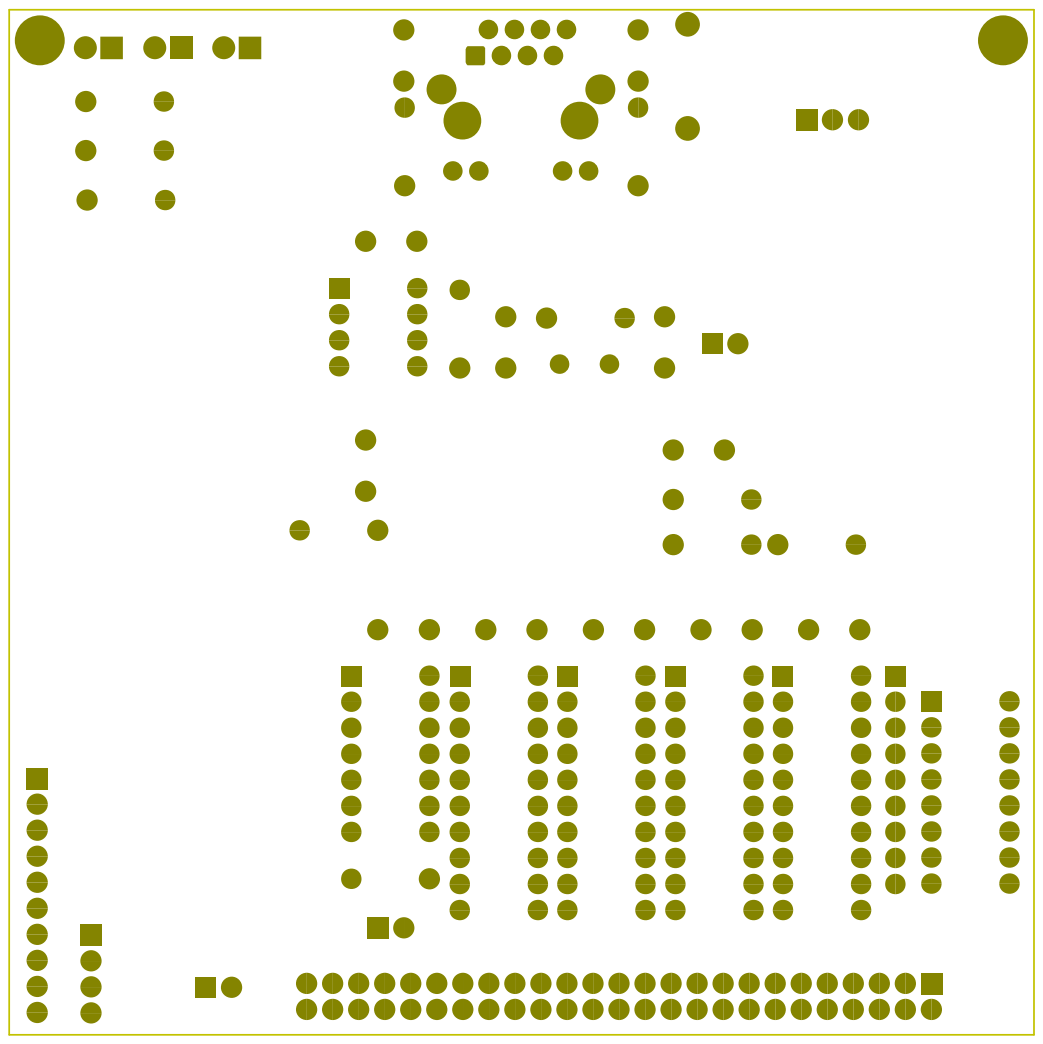
[picture p161: page 6]
