lynchaj/nhyodyne/Z80DUART2/Z80DUART2-PCB.pdf

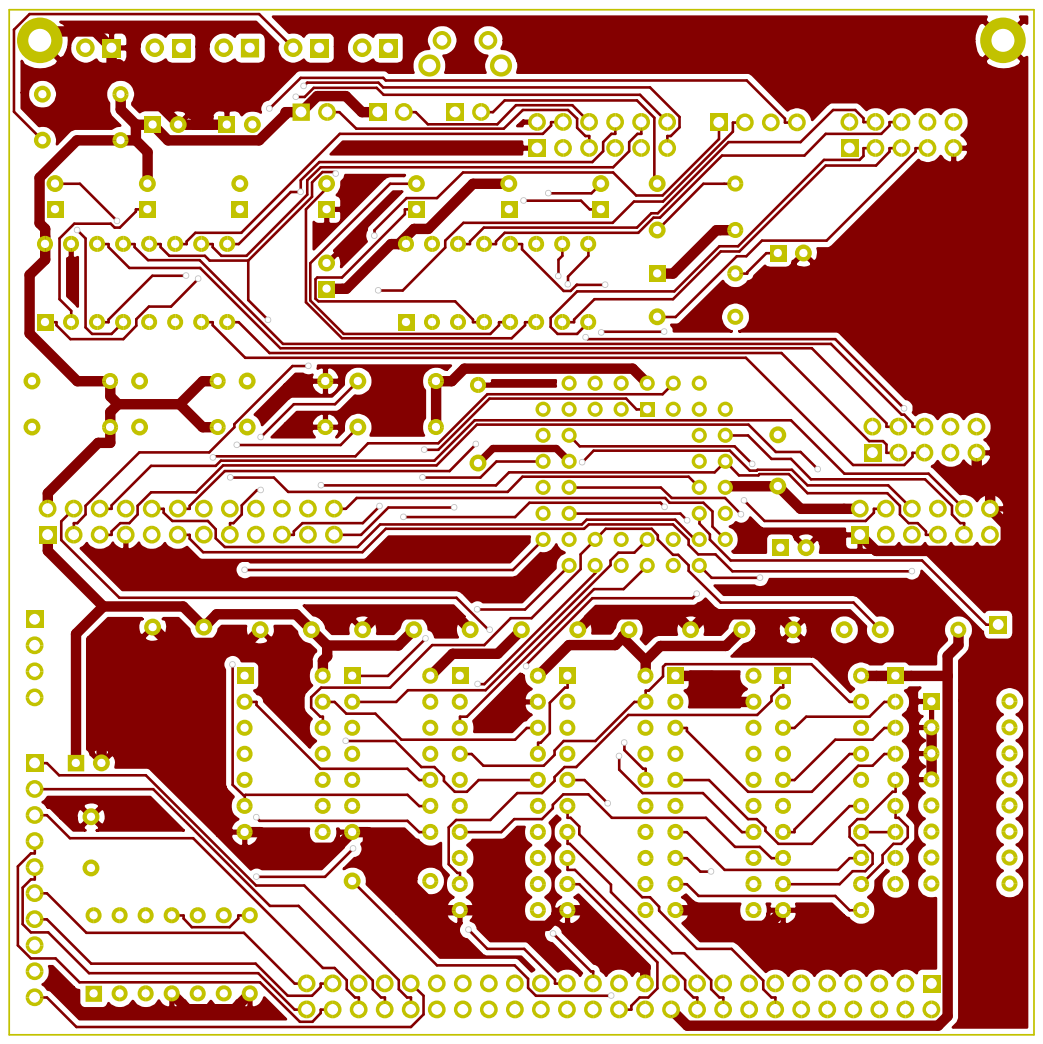
[picture p162: page 1]

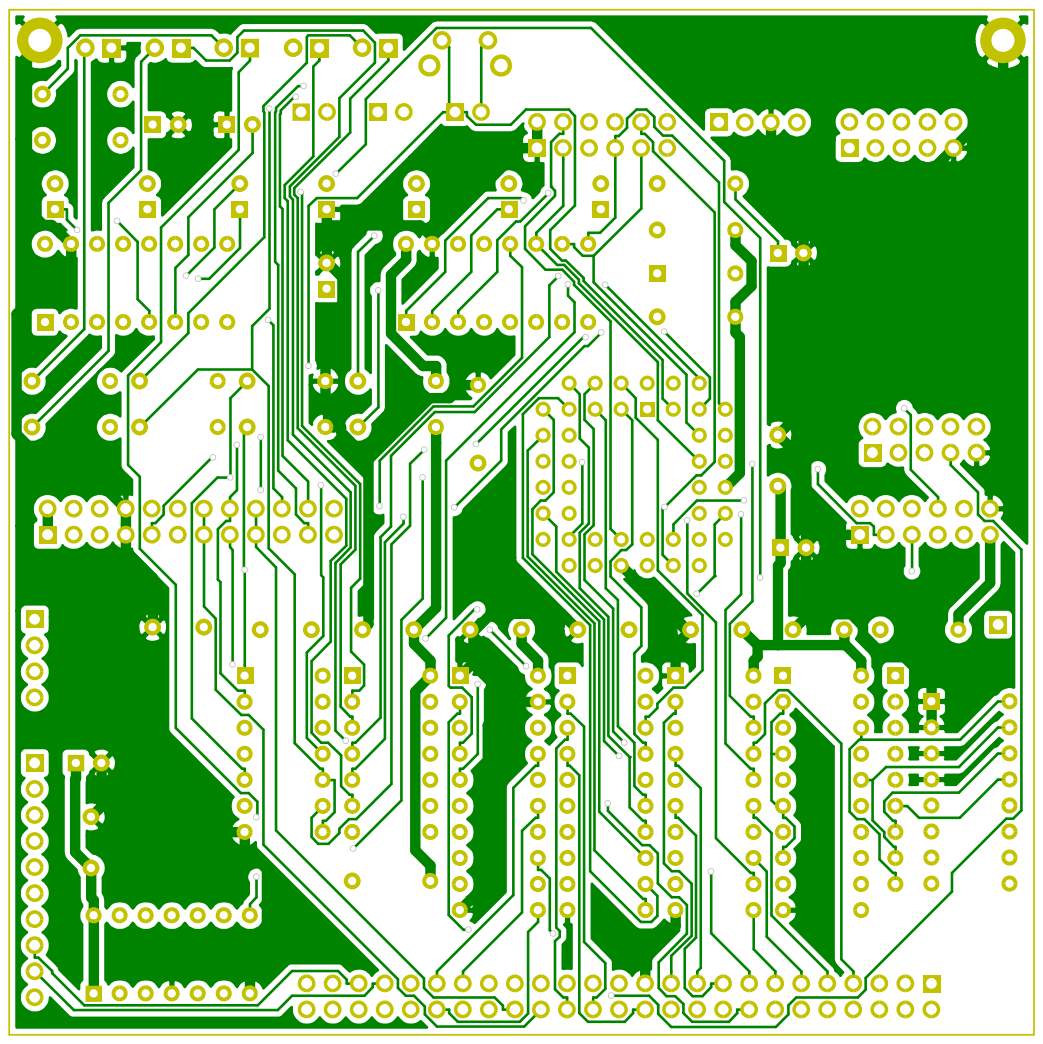
[picture p163: page 2]

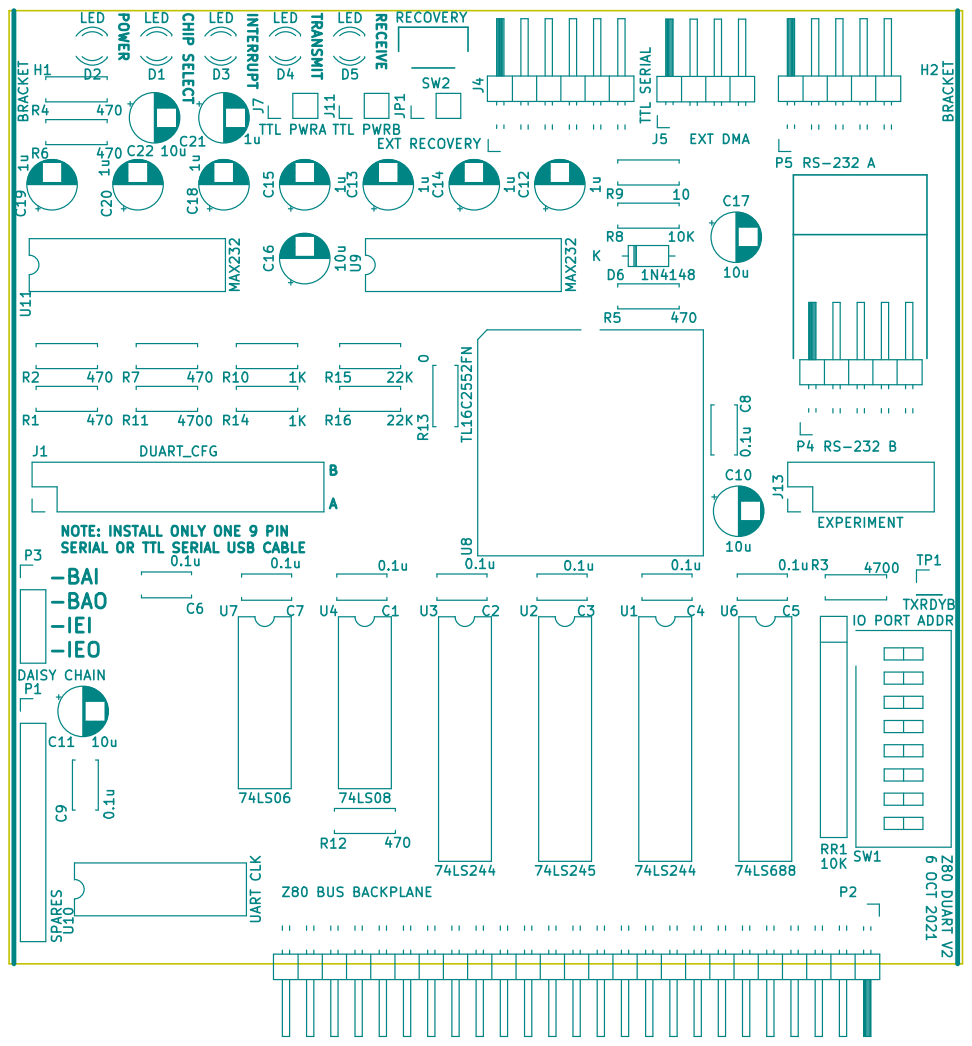
[picture p164: page 3]


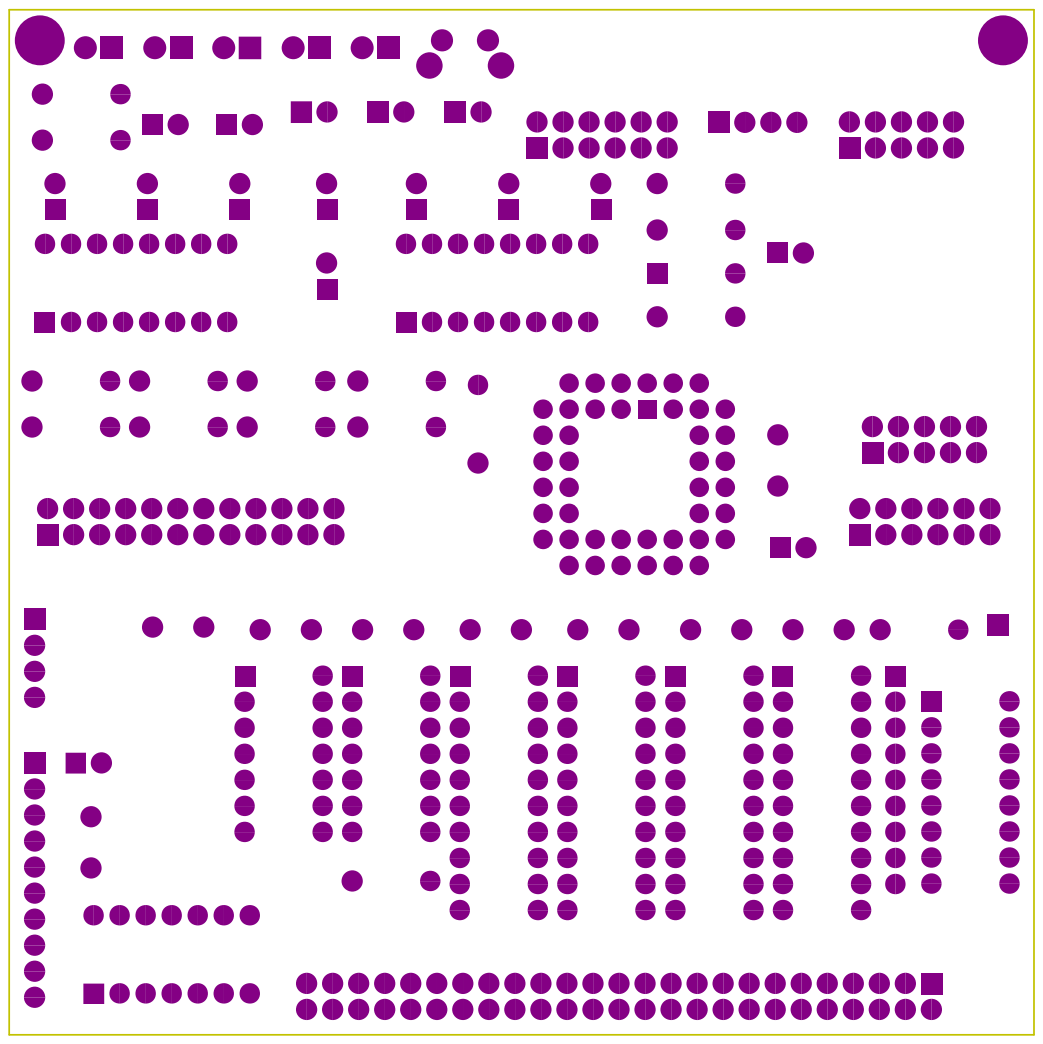
[picture p165: page 5]

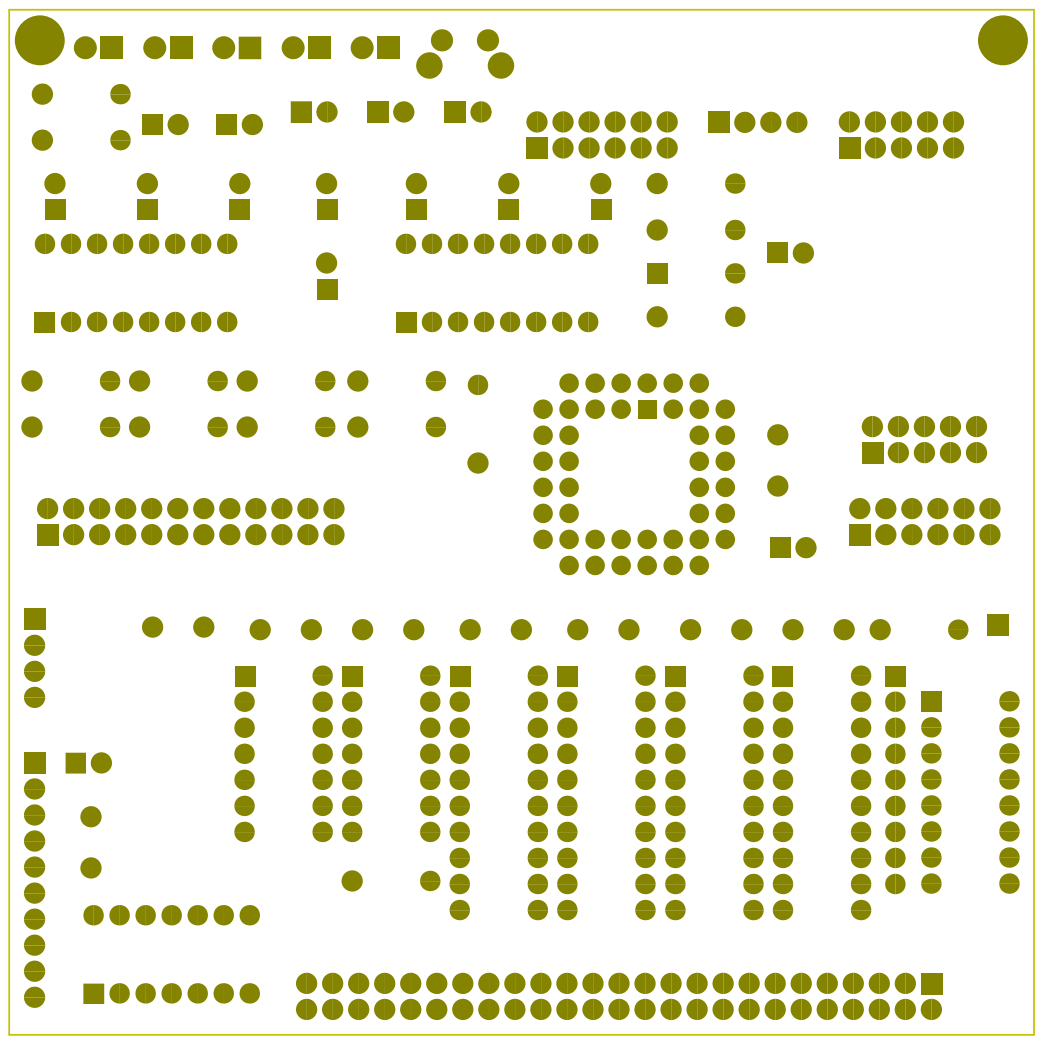
[picture p166: page 6]
