lynchaj/nhyodyne/Z80DMA2/Z80DMA2-PCB.pdf

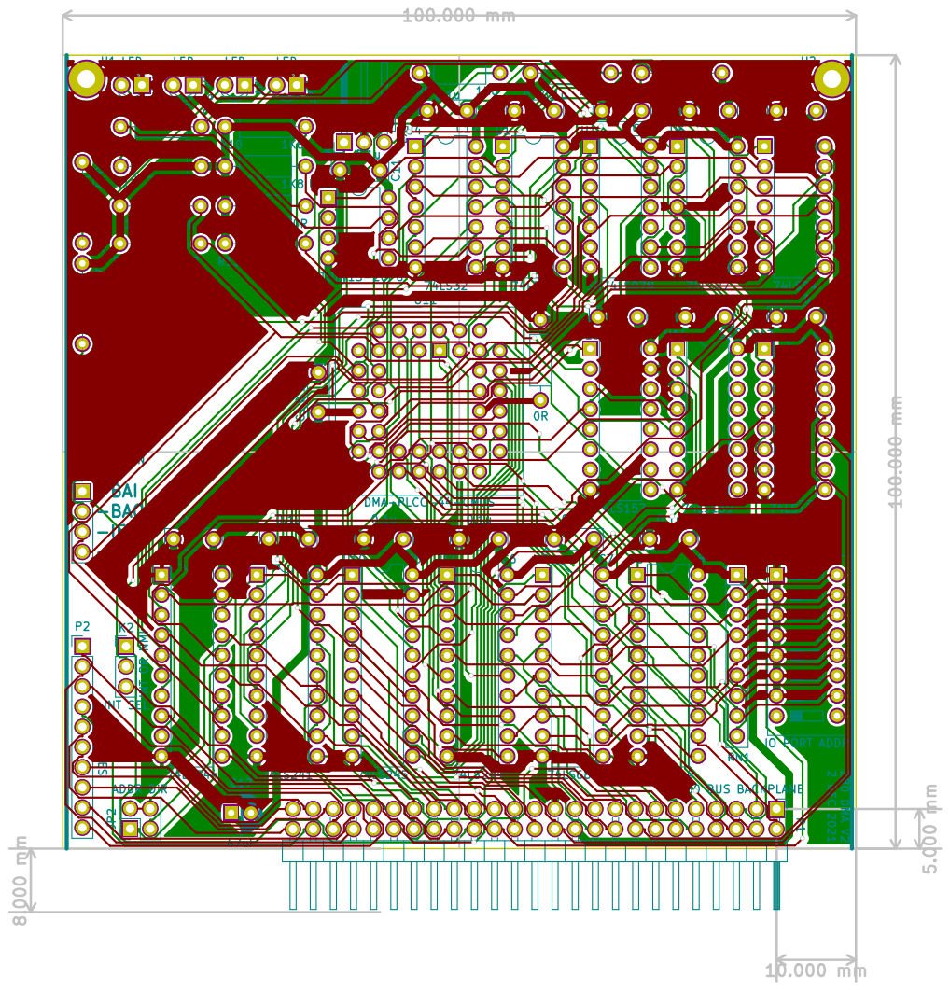
[picture p167: page 1]
