lynchaj/nhyodyne/Z80VDC1/Z80VDC-PCB.pdf

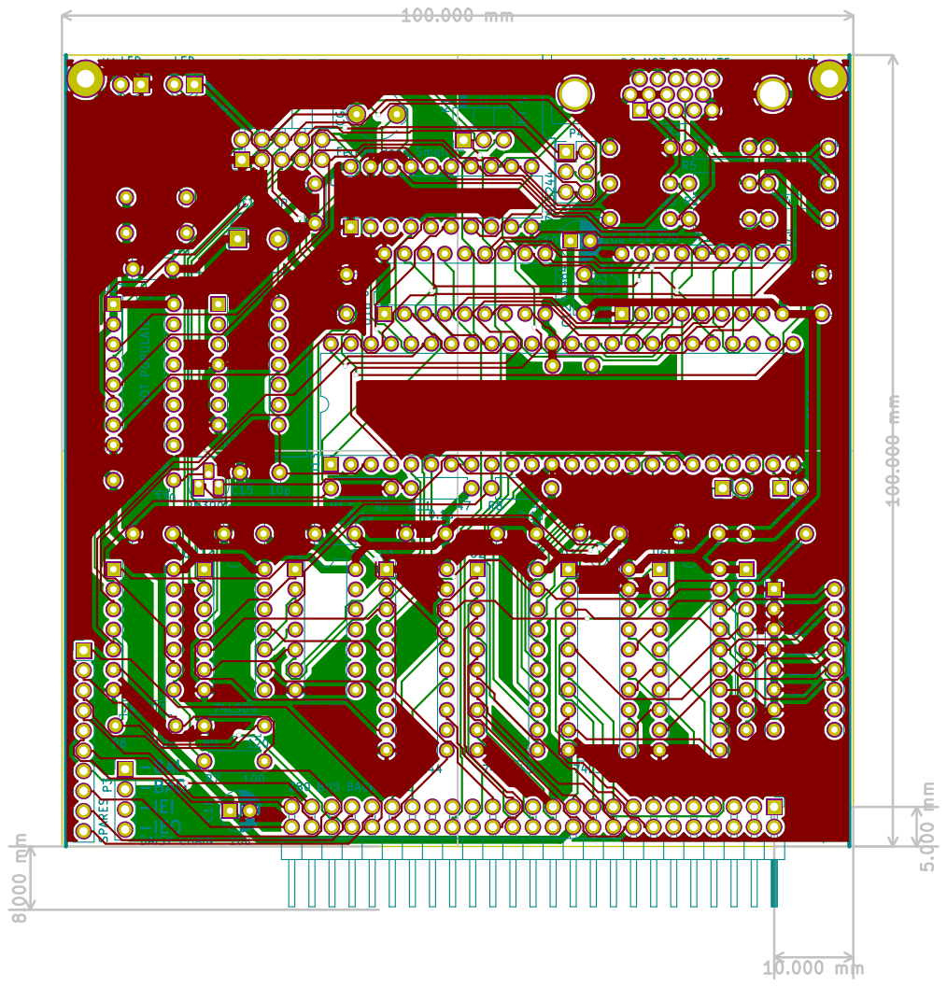
[picture p168: page 1]
