lynchaj/nhyodyne/Z80SERIAL3/Z80SERIAL3-PCB.pdf

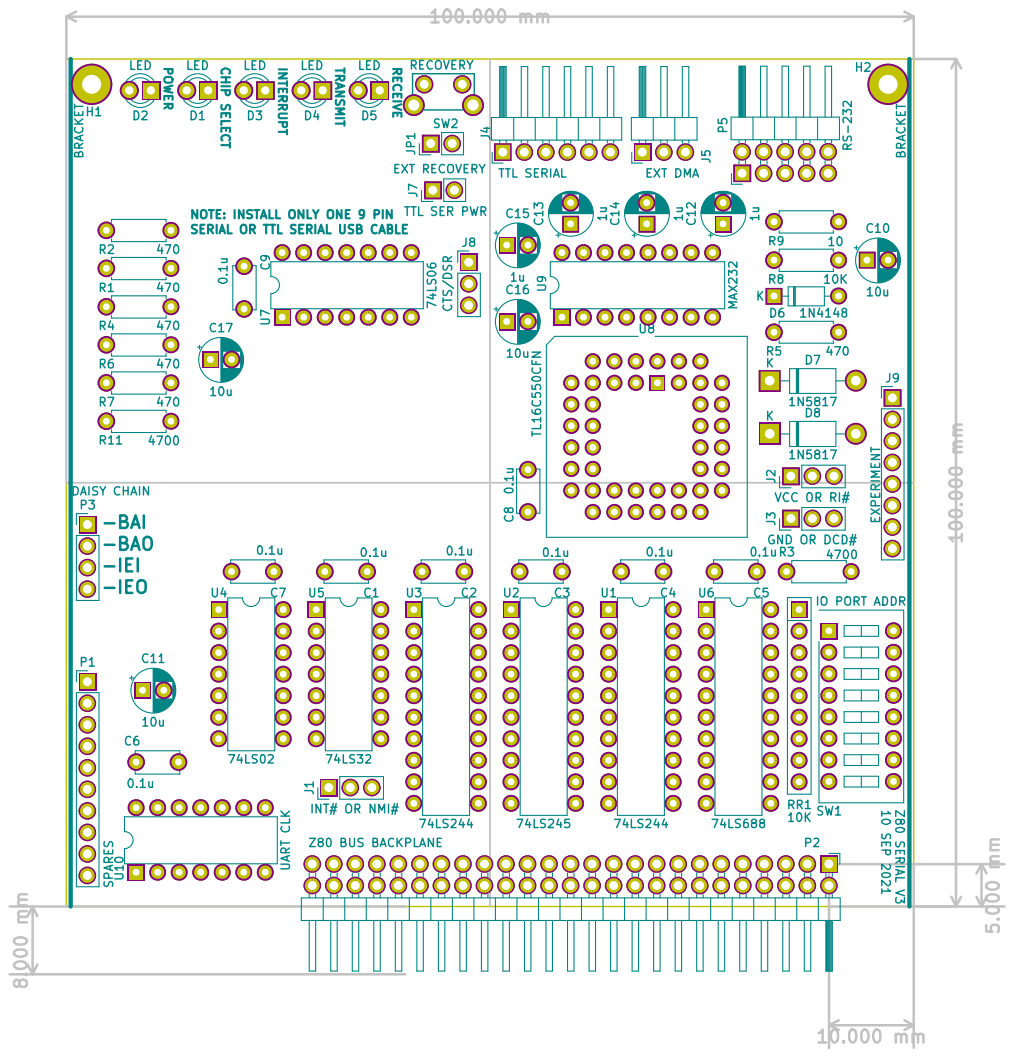
[picture p169: page 1]
