lynchaj/nhyodyne/Z80SERIAL2/Z80SERIAL2-PCB.pdf

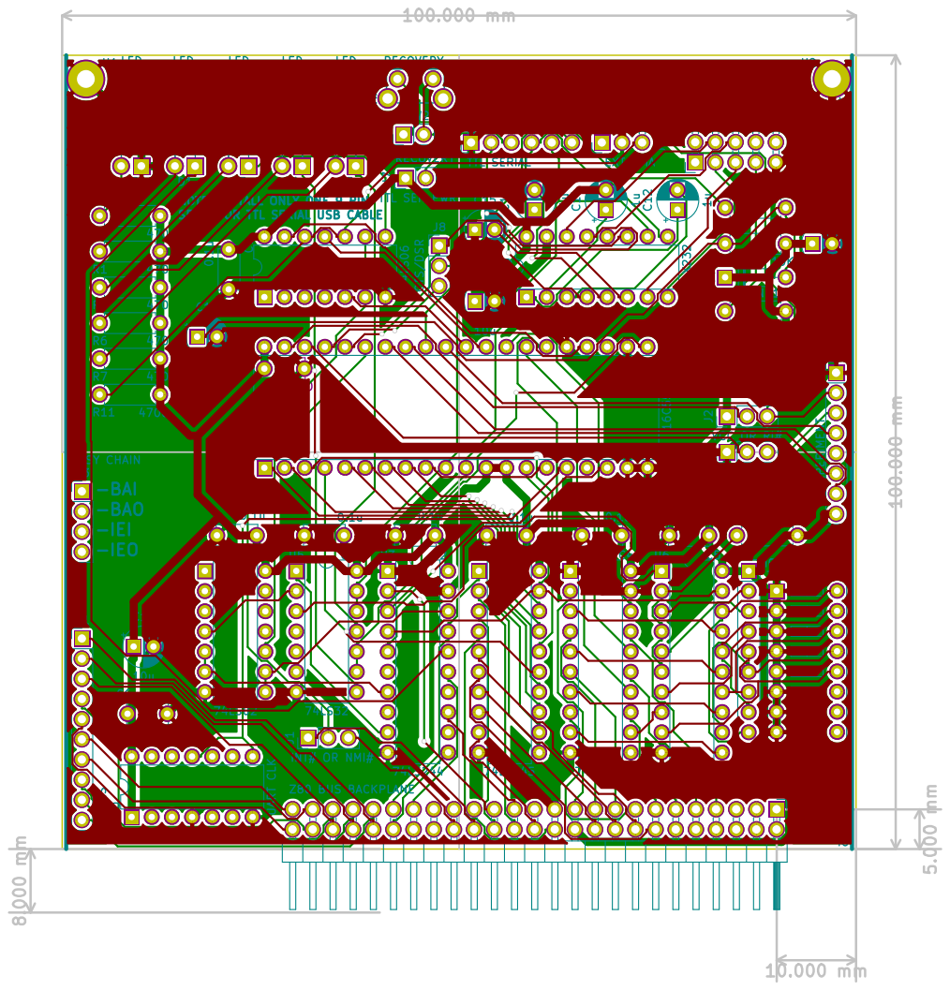
[picture p170: page 1]
