lynchaj/nhyodyne/Z80ROM2/Z80ROM2-PCB.pdf

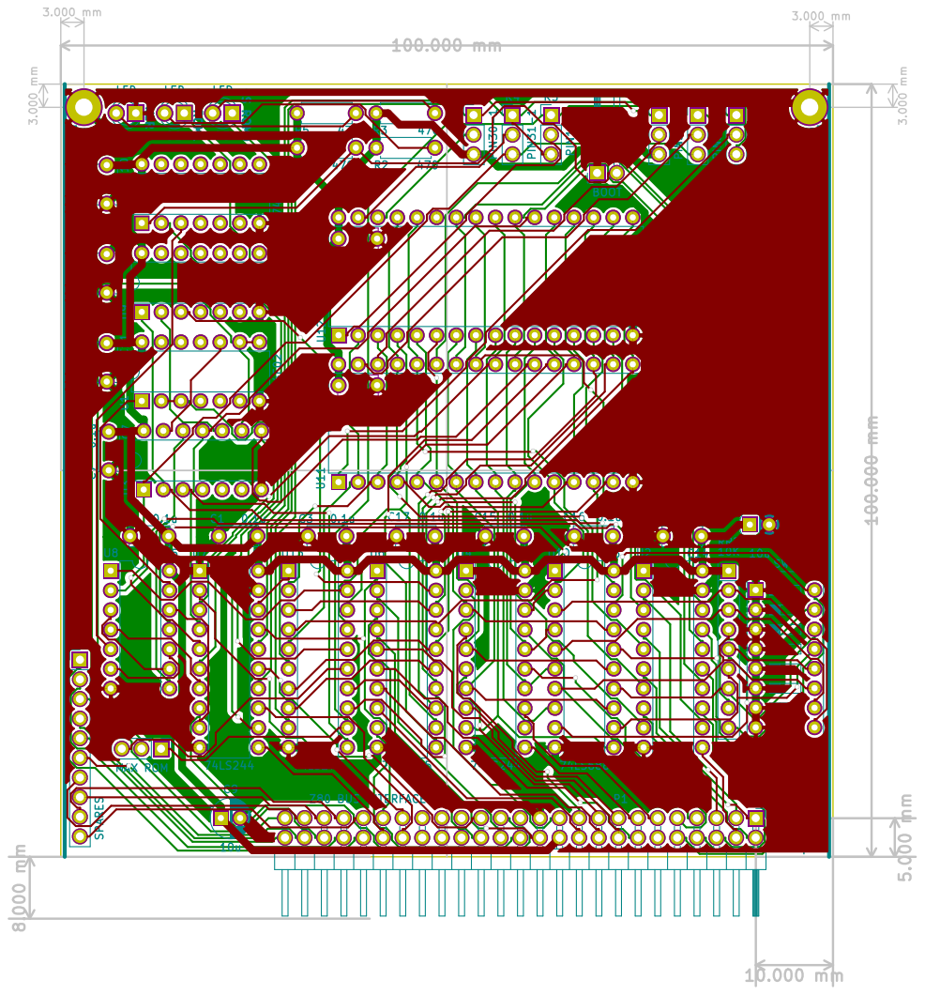
[picture p171: page 1]
