lynchaj/nhyodyne/Z80RAM3/Z80RAM3-PCB.pdf

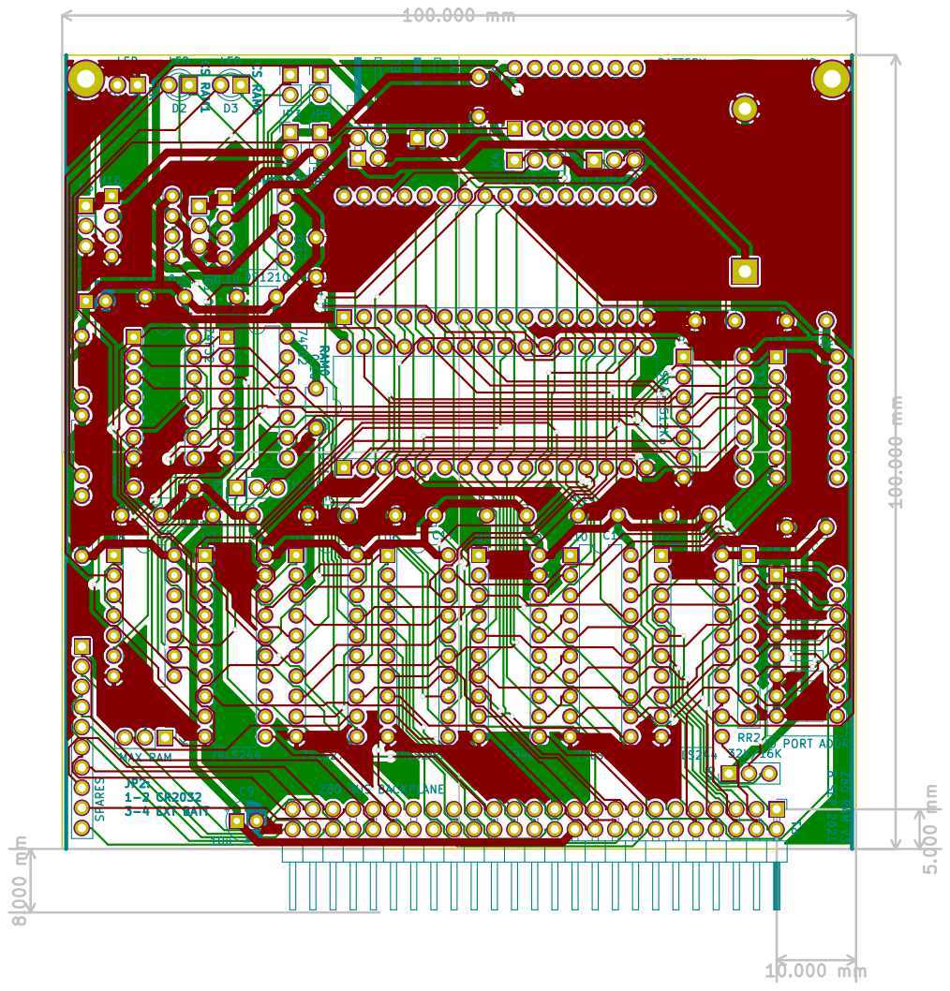
[picture p172: page 1]
