lynchaj/nhyodyne/Z80PROTO2/Z80PROTO2-PCB.pdf

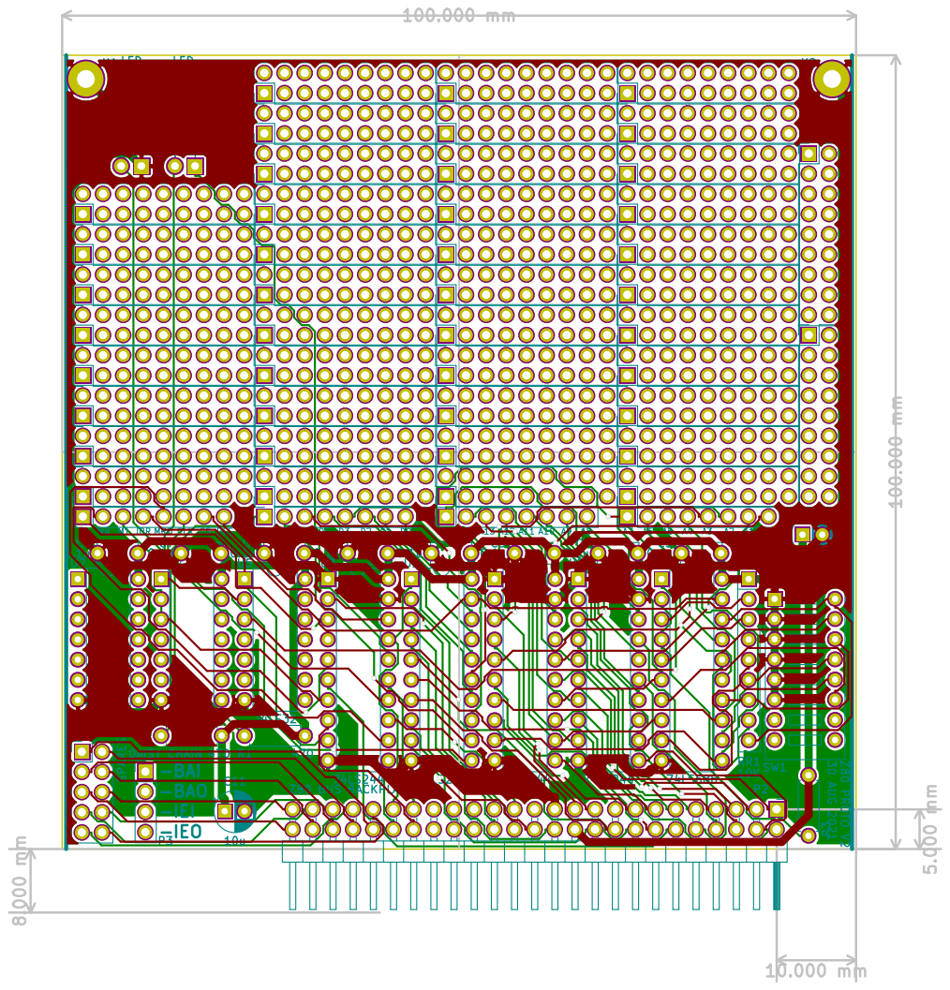
[picture p173: page 1]
