lynchaj/nhyodyne/Z80PROC3/Z80PROC3-PCB.pdf

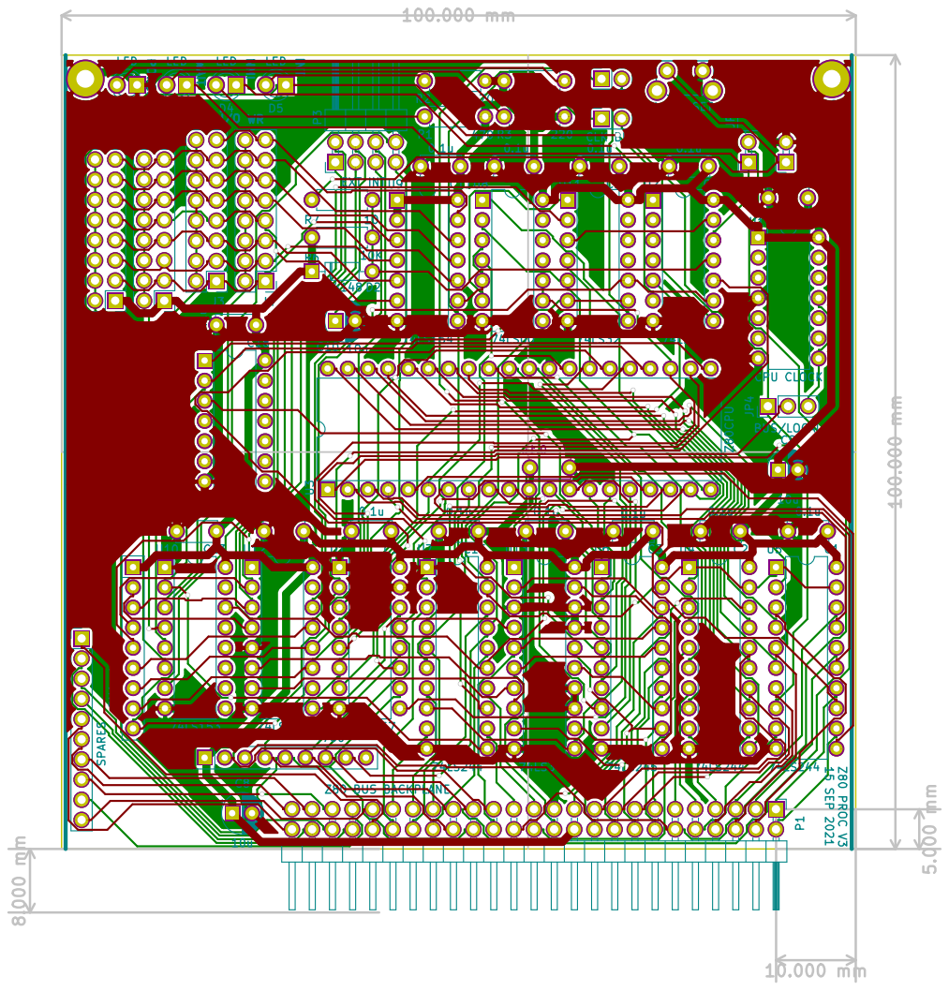
[picture p174: page 1]
