lynchaj/nhyodyne/Z80PPIDE2/Z80PPIDE2-PCB.pdf

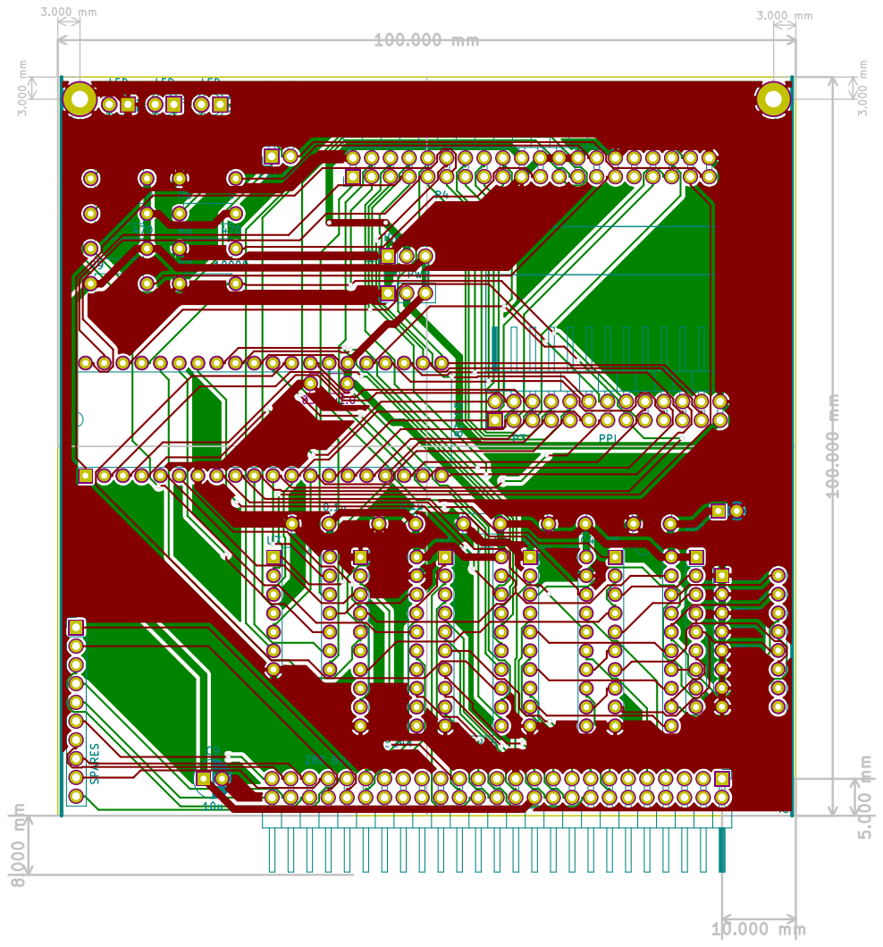
[picture p175: page 1]
