lynchaj/nhyodyne/Z80KBDMSE1/Z80KBDMSE-PCB.pdf

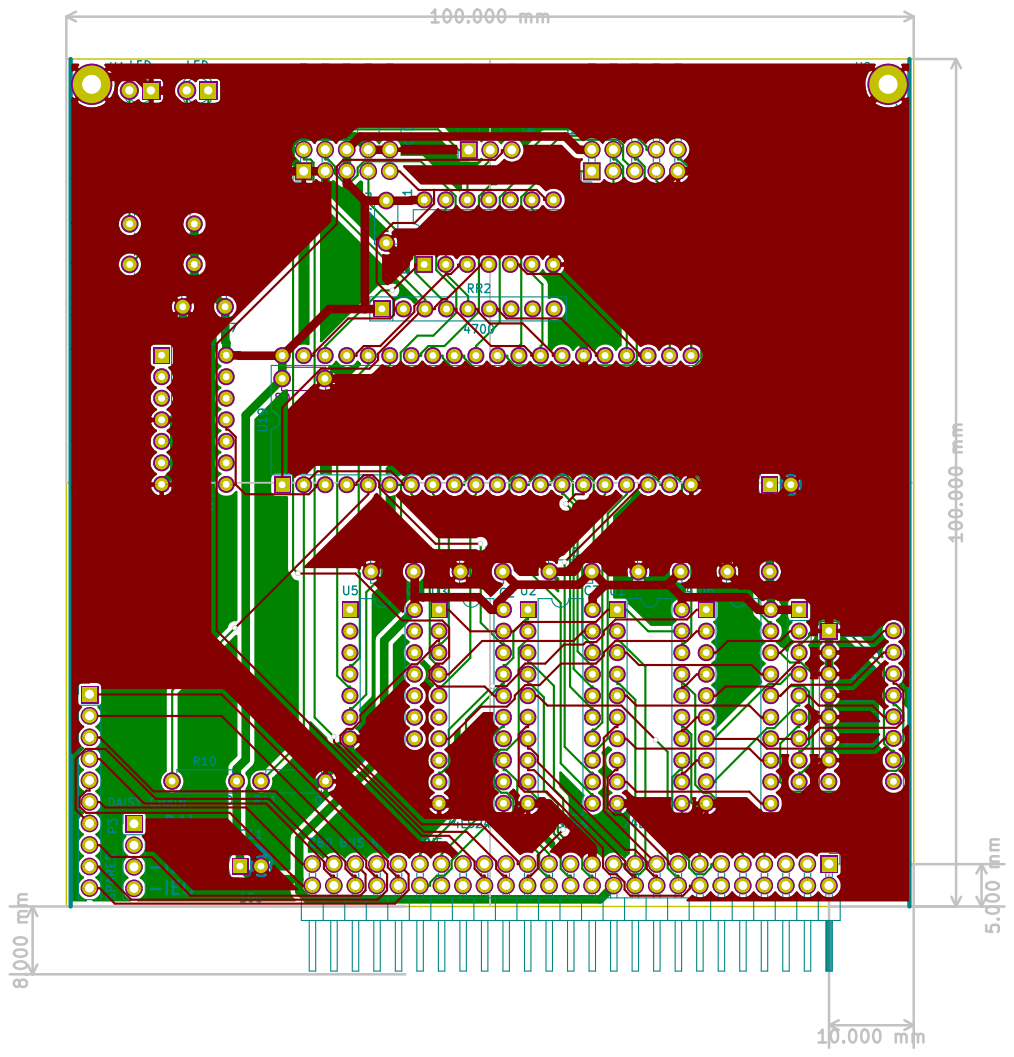
[picture p176: page 1]
