lynchaj/nhyodyne/Z80FDC1/Z80FDC-PCB.pdf

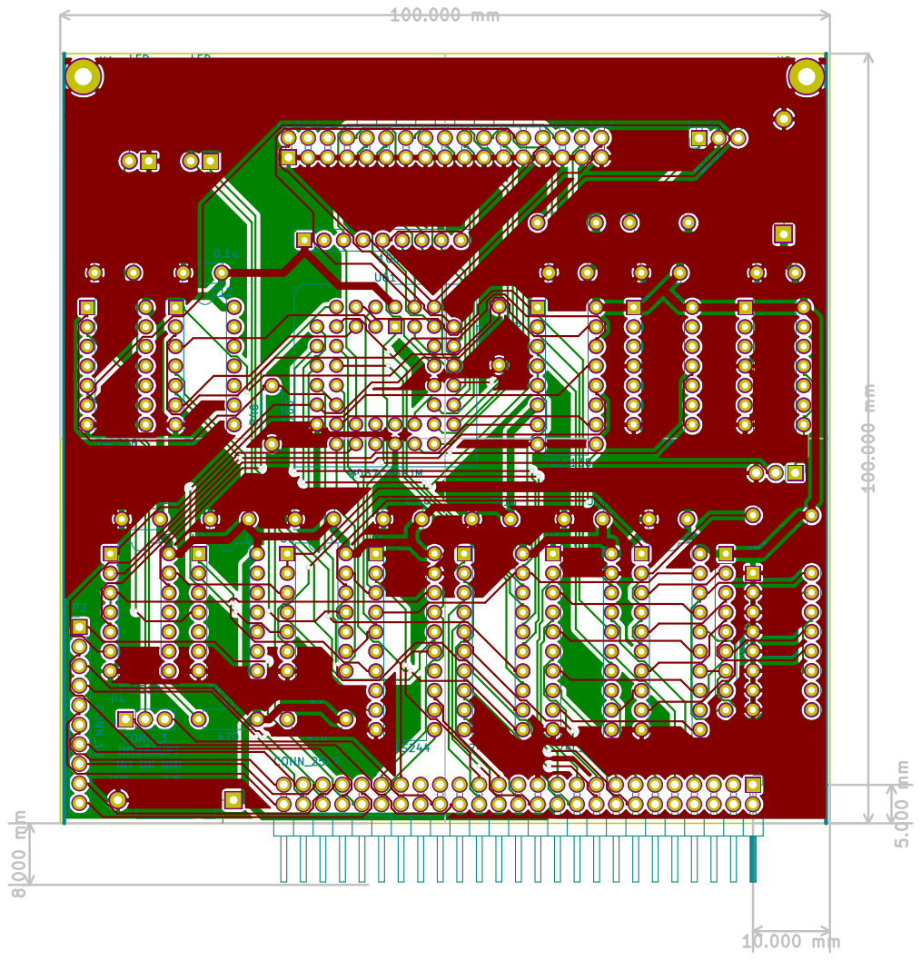
[picture p177: page 1]
