lynchaj/nhyodyne/Z80CLOCK2/Z80CLOCK2-PCB.pdf

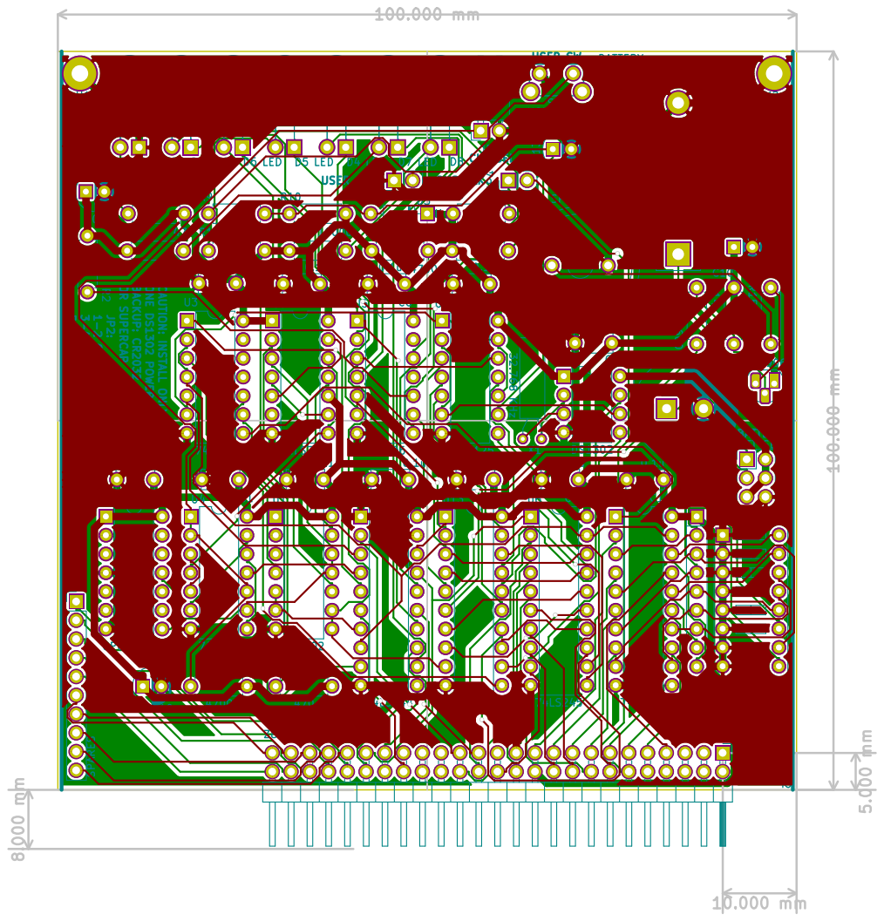
[picture p178: page 1]
