lynchaj/nhyodyne/Z80BCKPLN2/Z80BCKPLN2-PCB.pdf

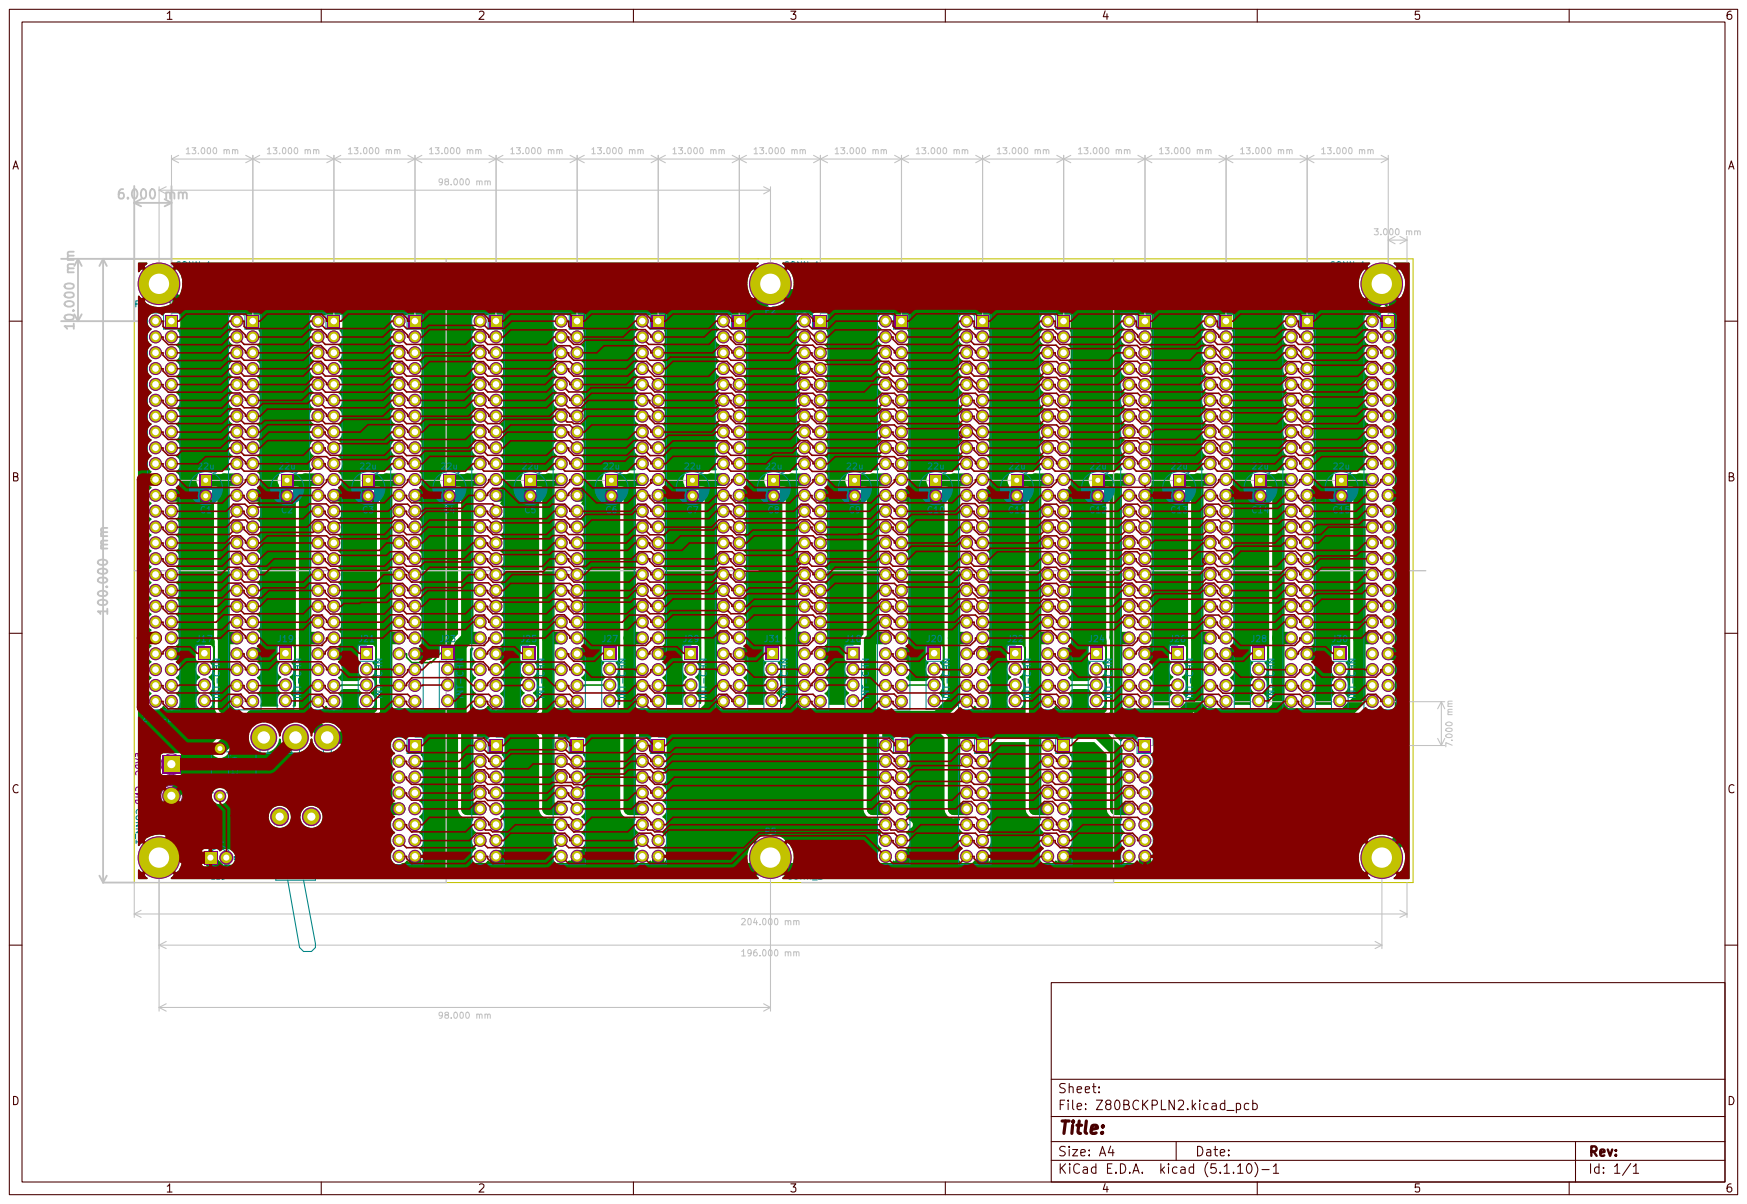
[picture p179: page 1]
