lynchaj/nhyodyne/Z80BCKPLN1/Z80BCKPLN-PCB.pdf

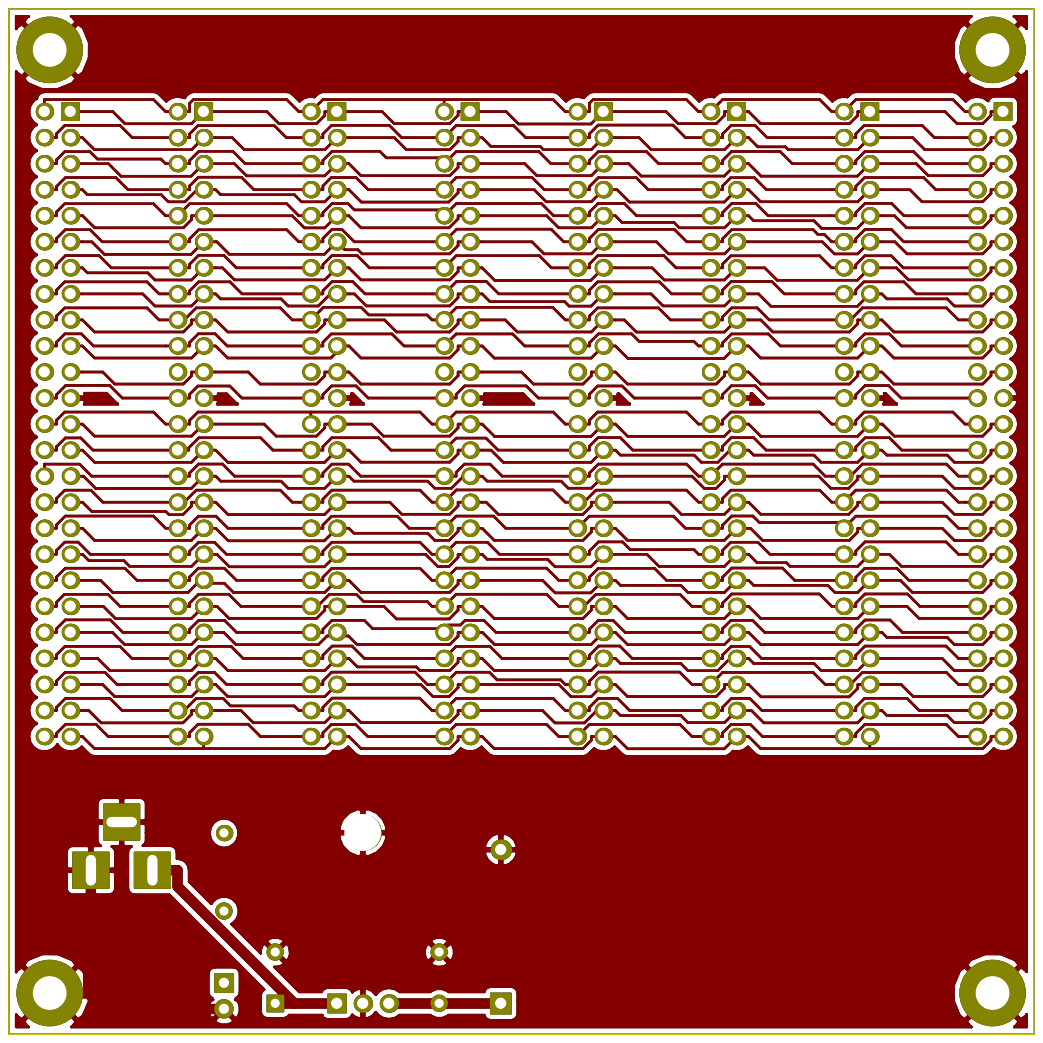
[picture p180: page 1]

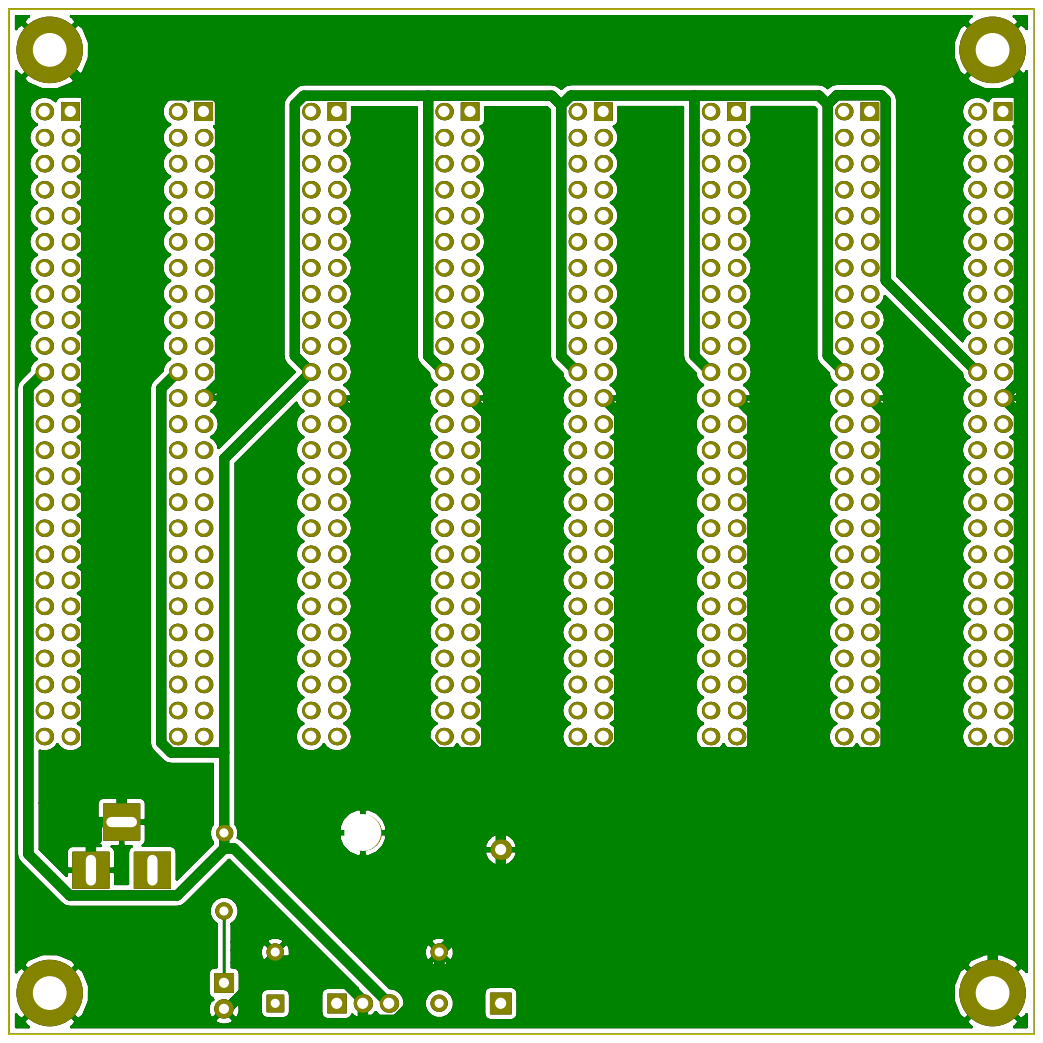
[picture p181: page 2]

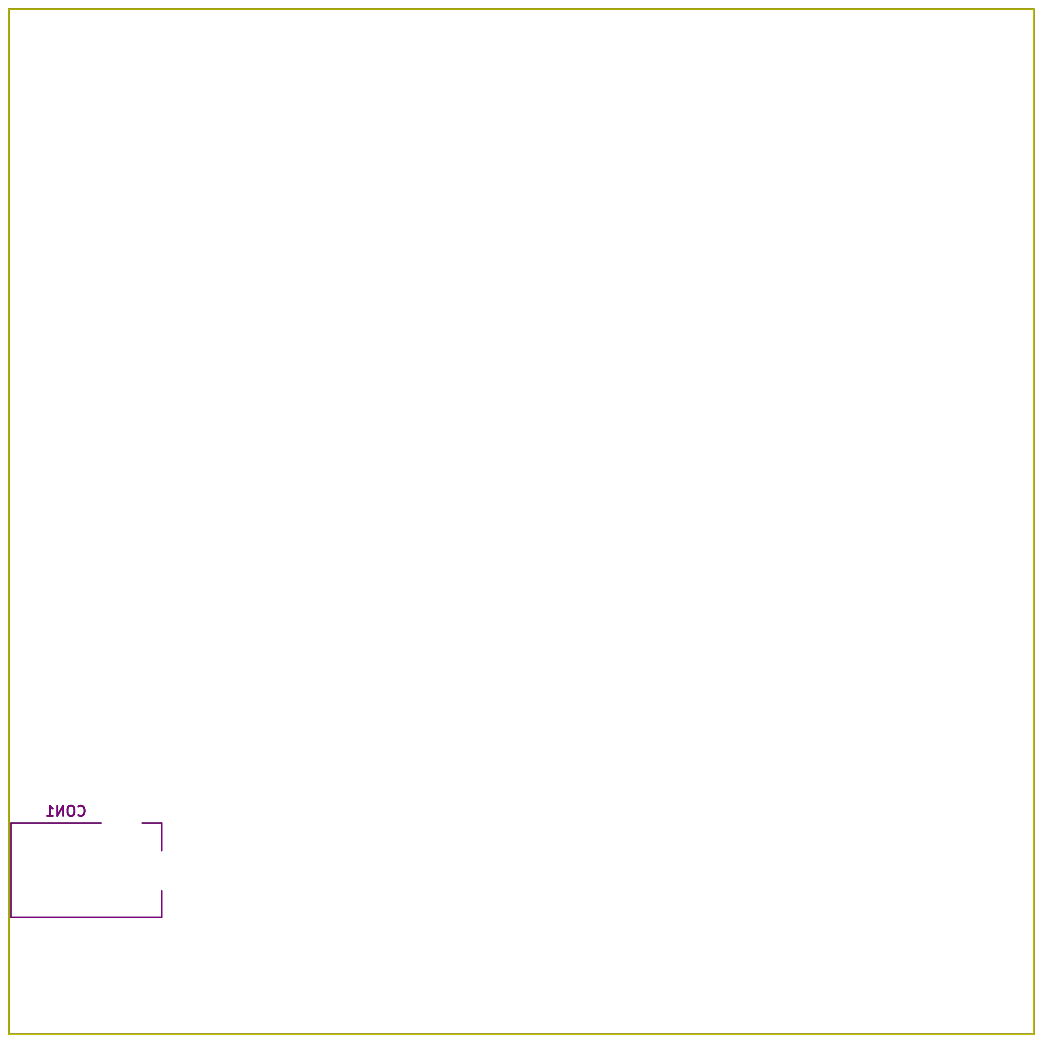
[picture p182: page 3]

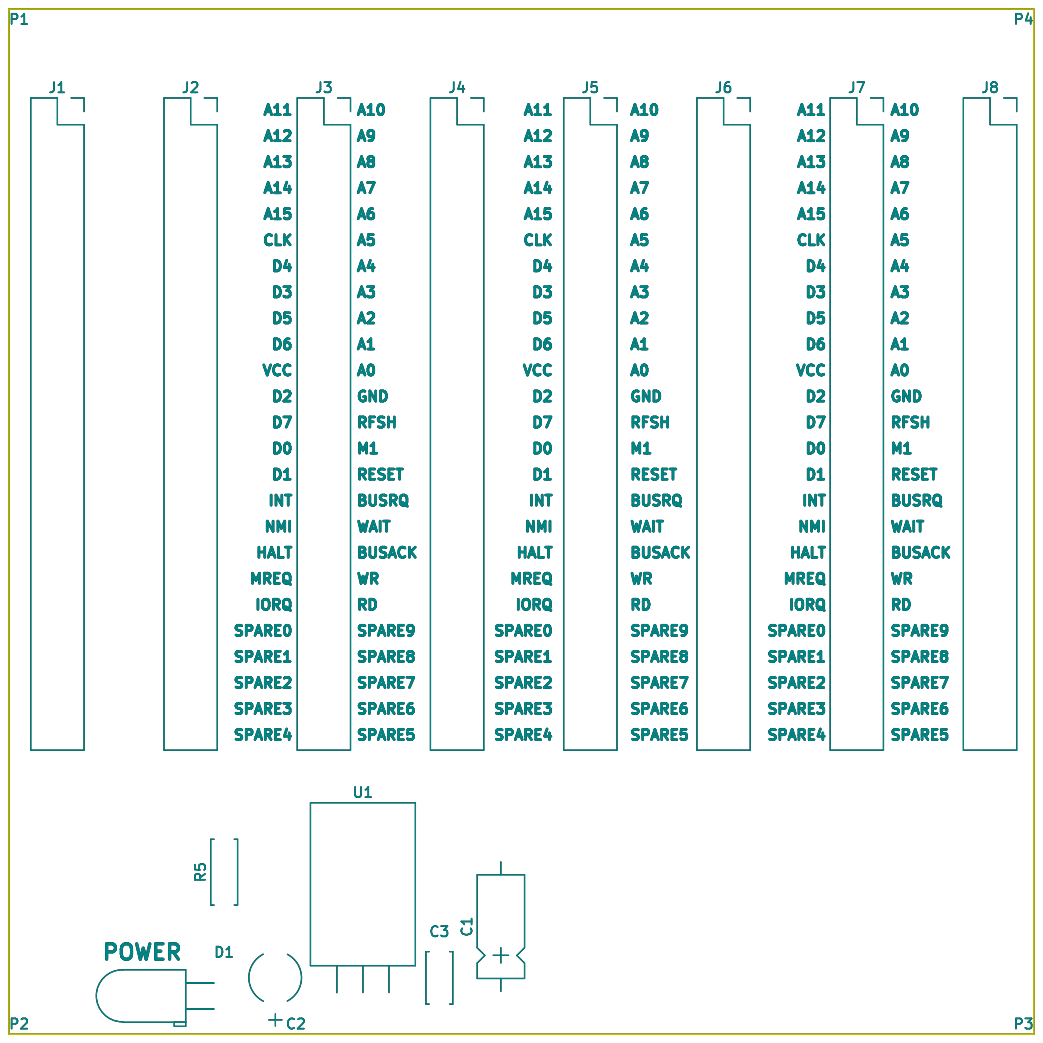
[picture p183: page 4]

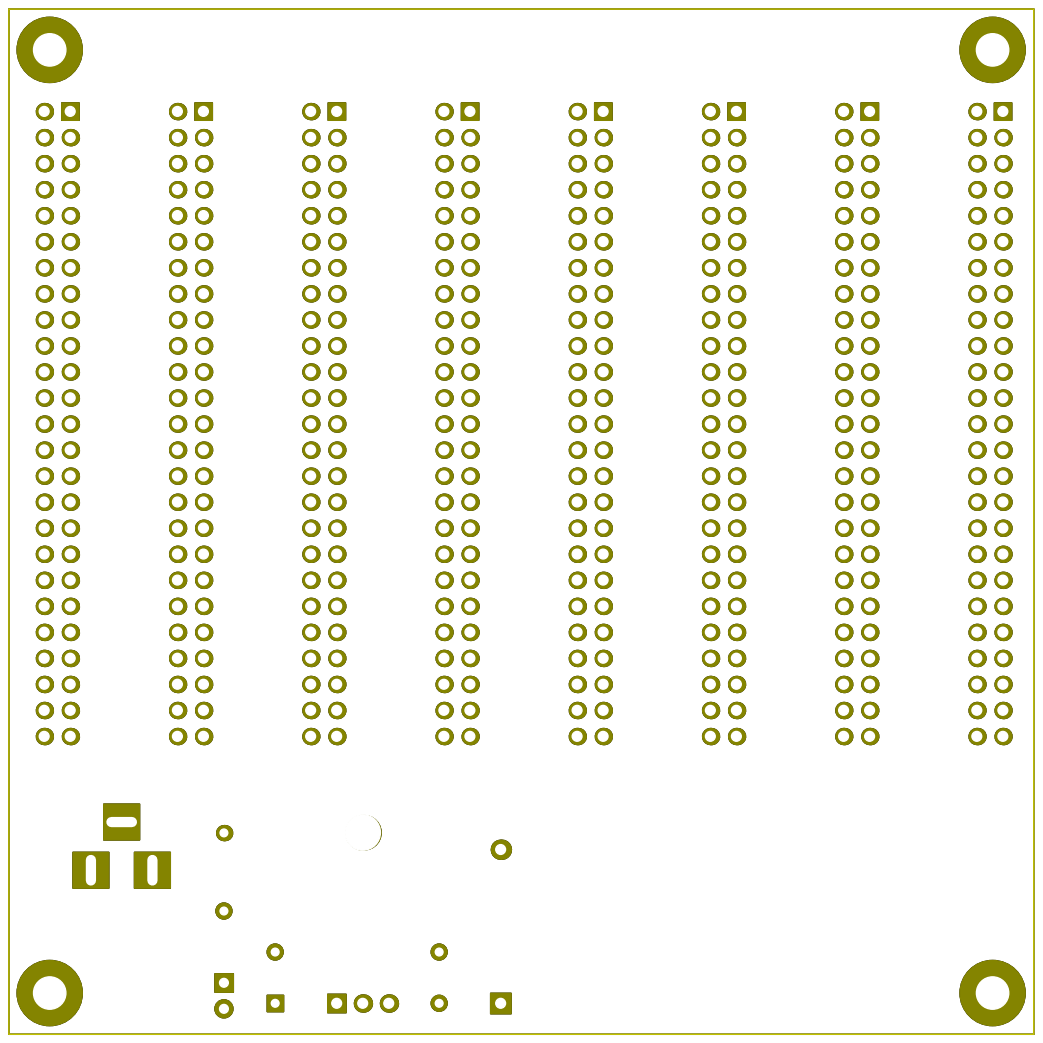
[picture p184: page 5]

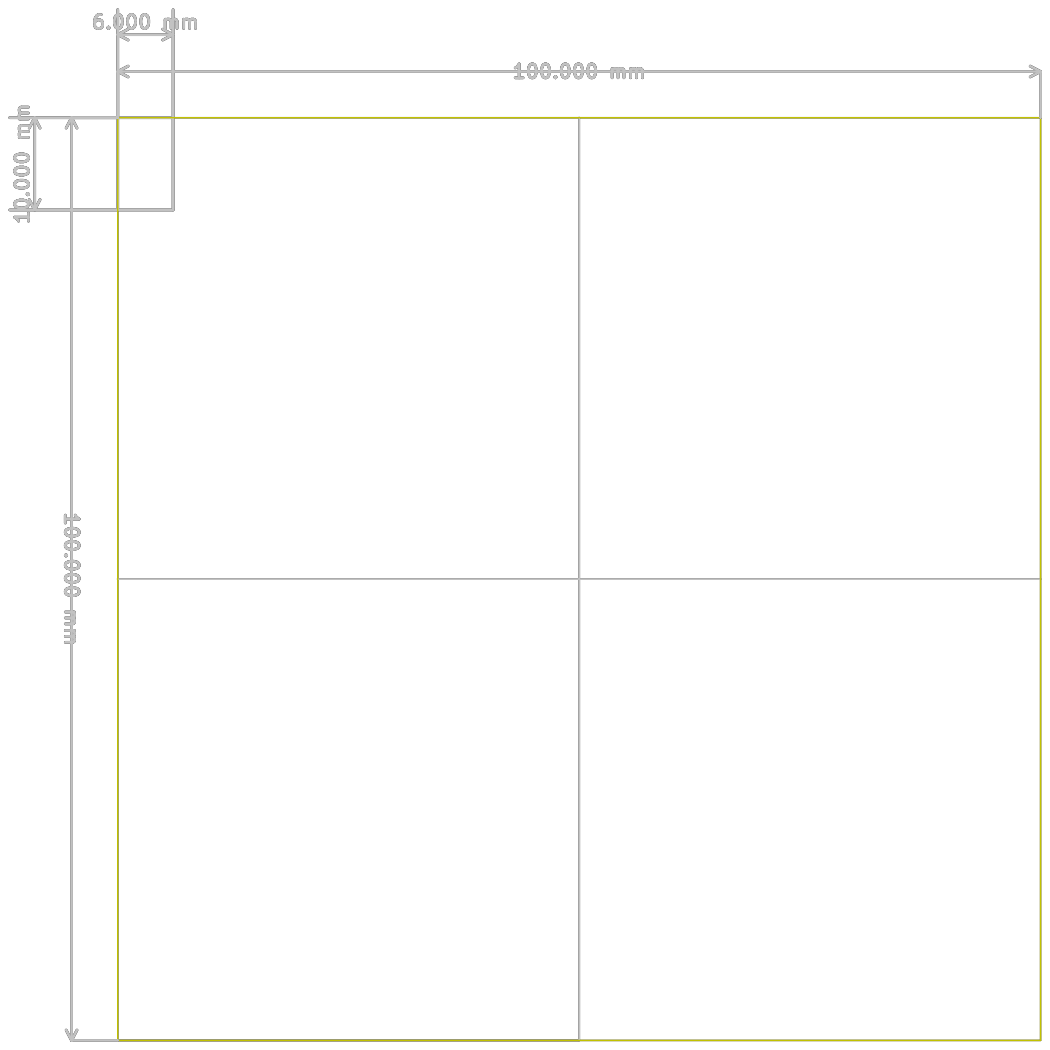
[picture p185: page 7]

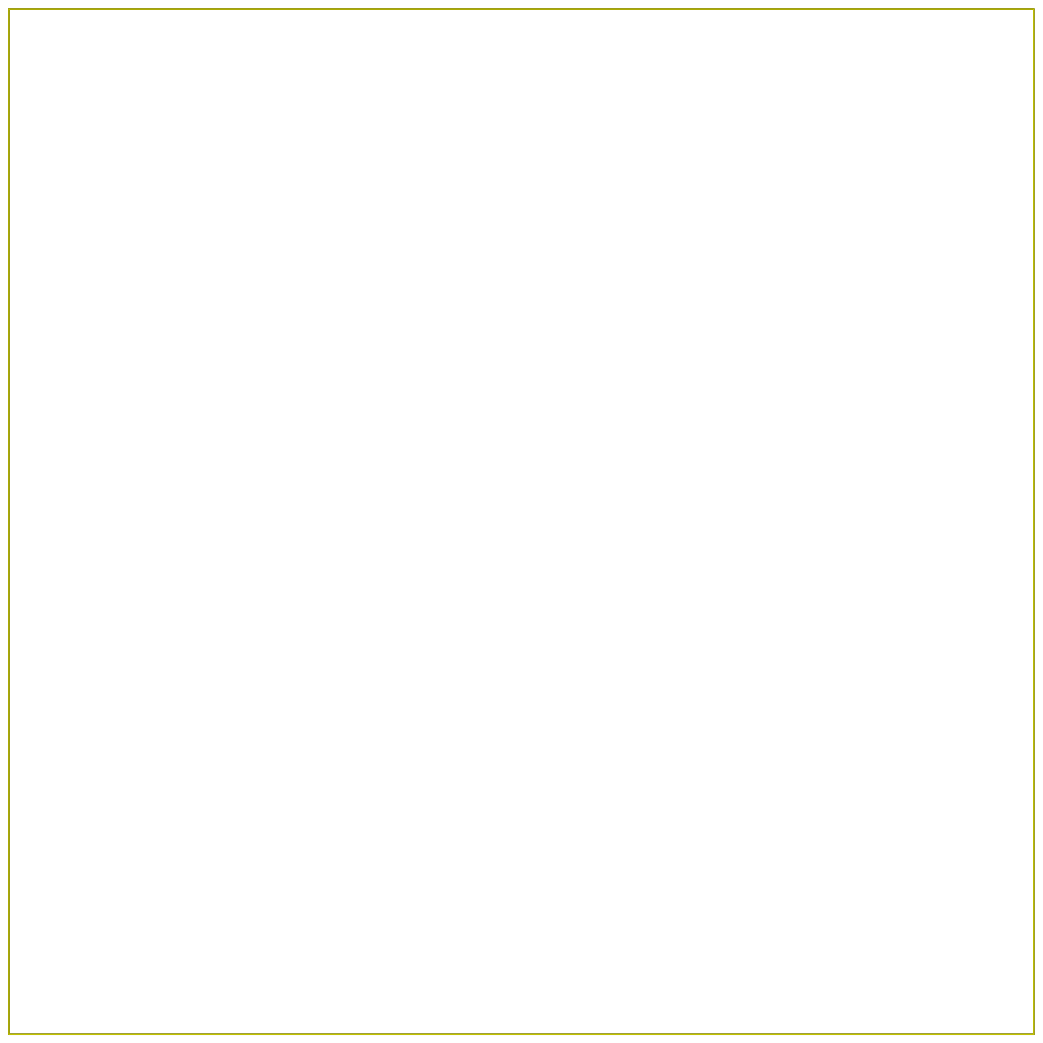
[picture p186: page 8]

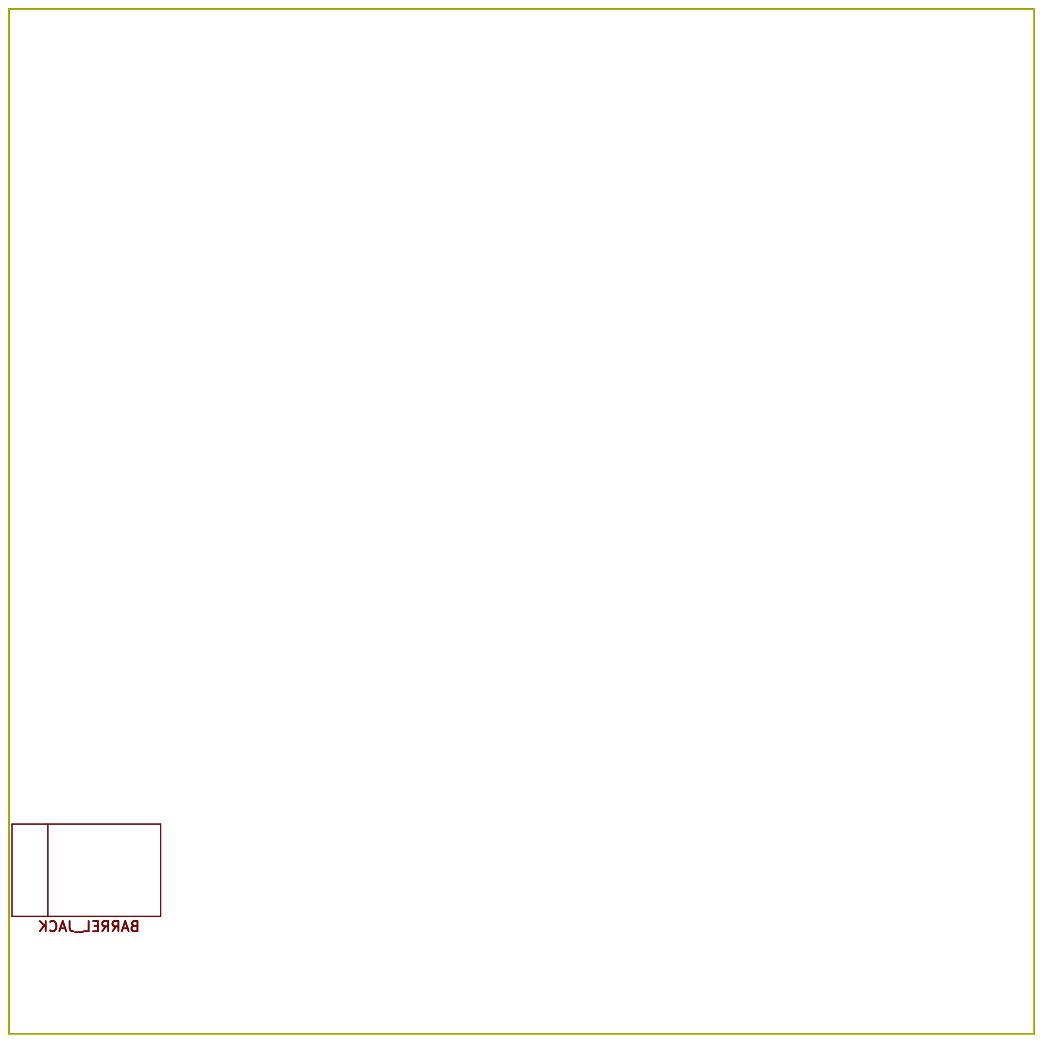
[picture p187: page 9]

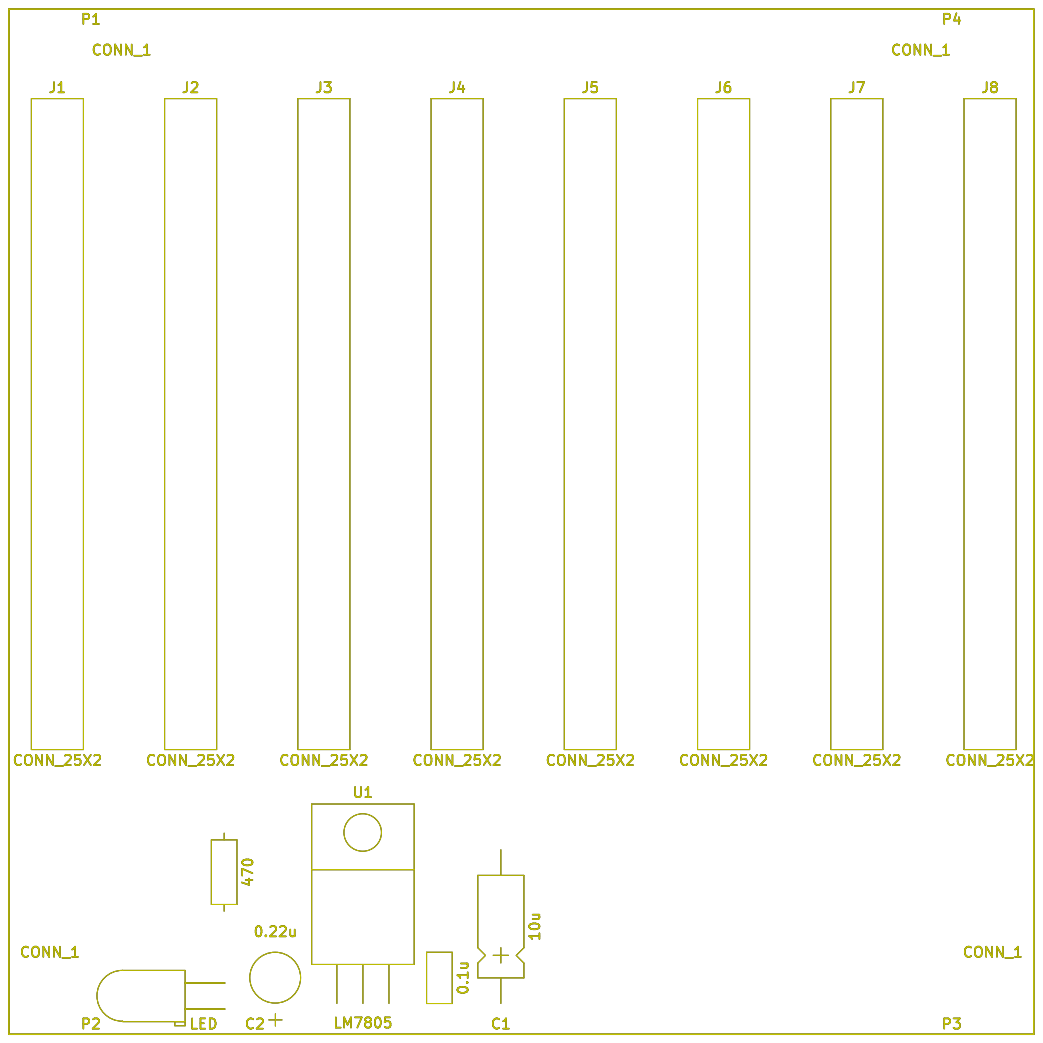
[picture p188: page 10]
