lynchaj/nhyodyne/Z80ESP/HARDWARE/z80esp-pcb-V0.9.pdf

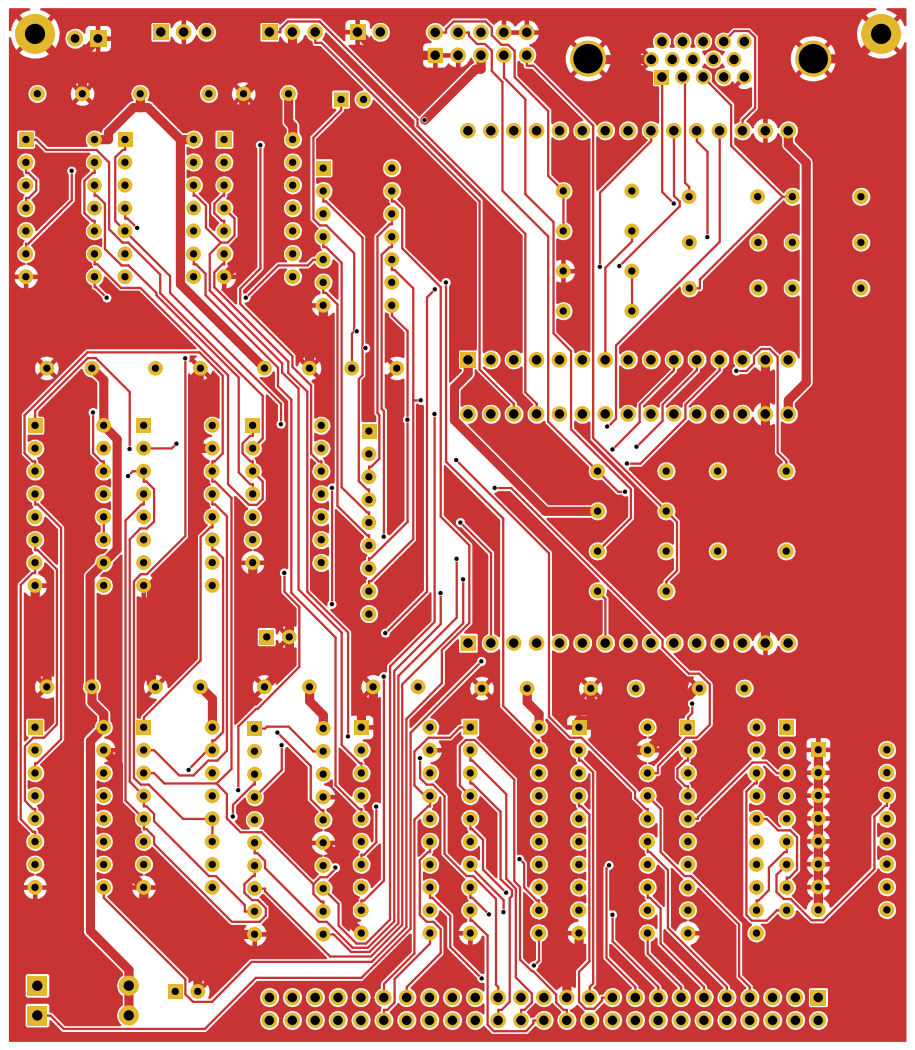
[picture p189: page 1]

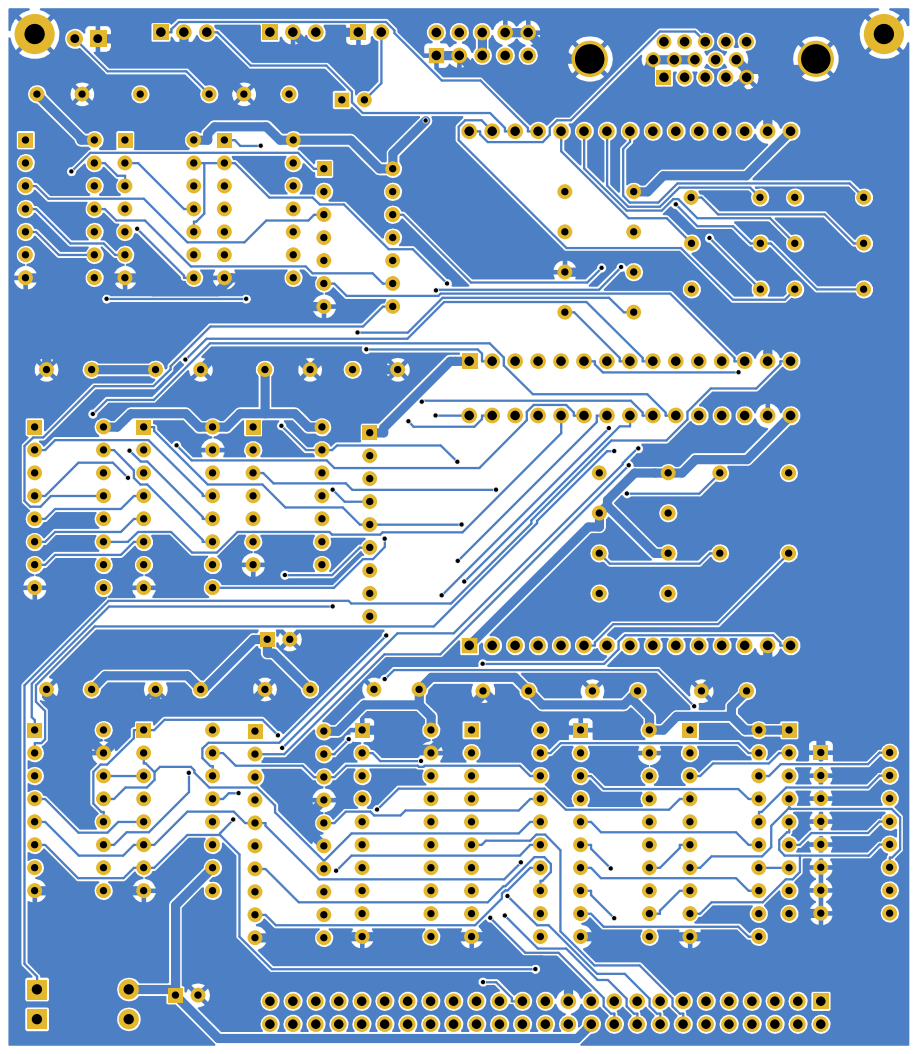
[picture p190: page 2]

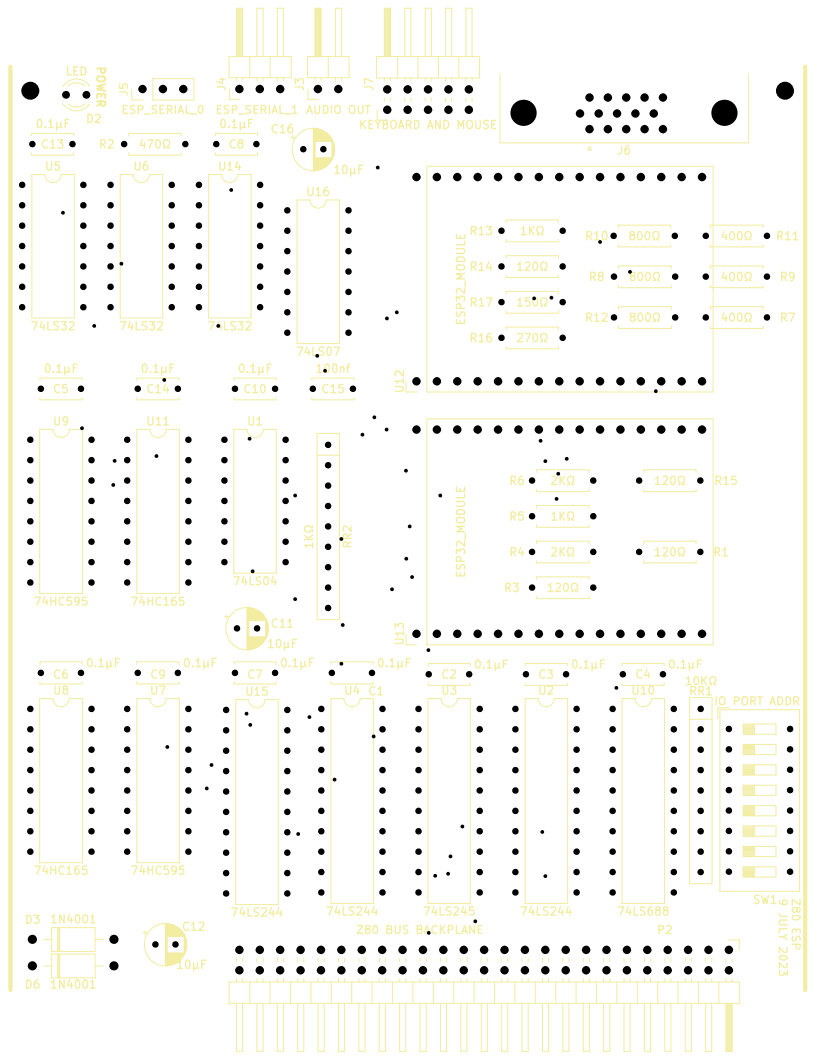
[picture p191: page 3]

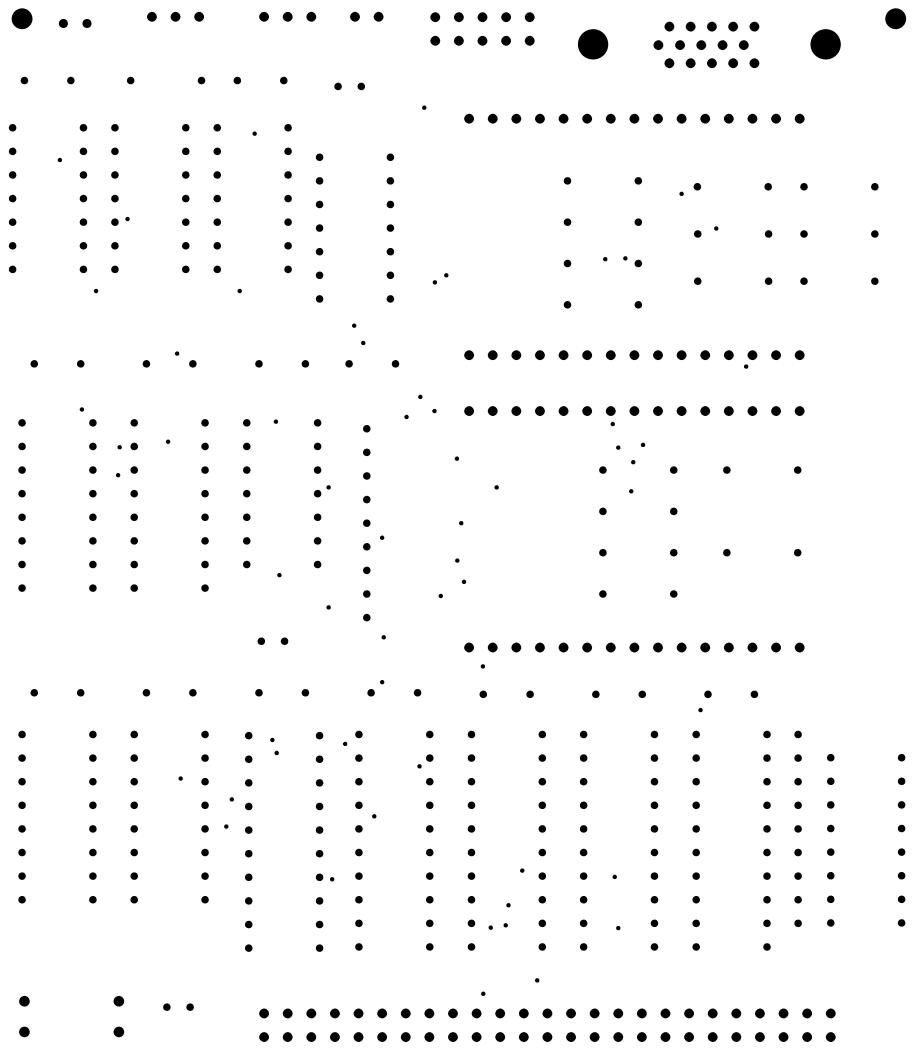
[picture p192: page 4]

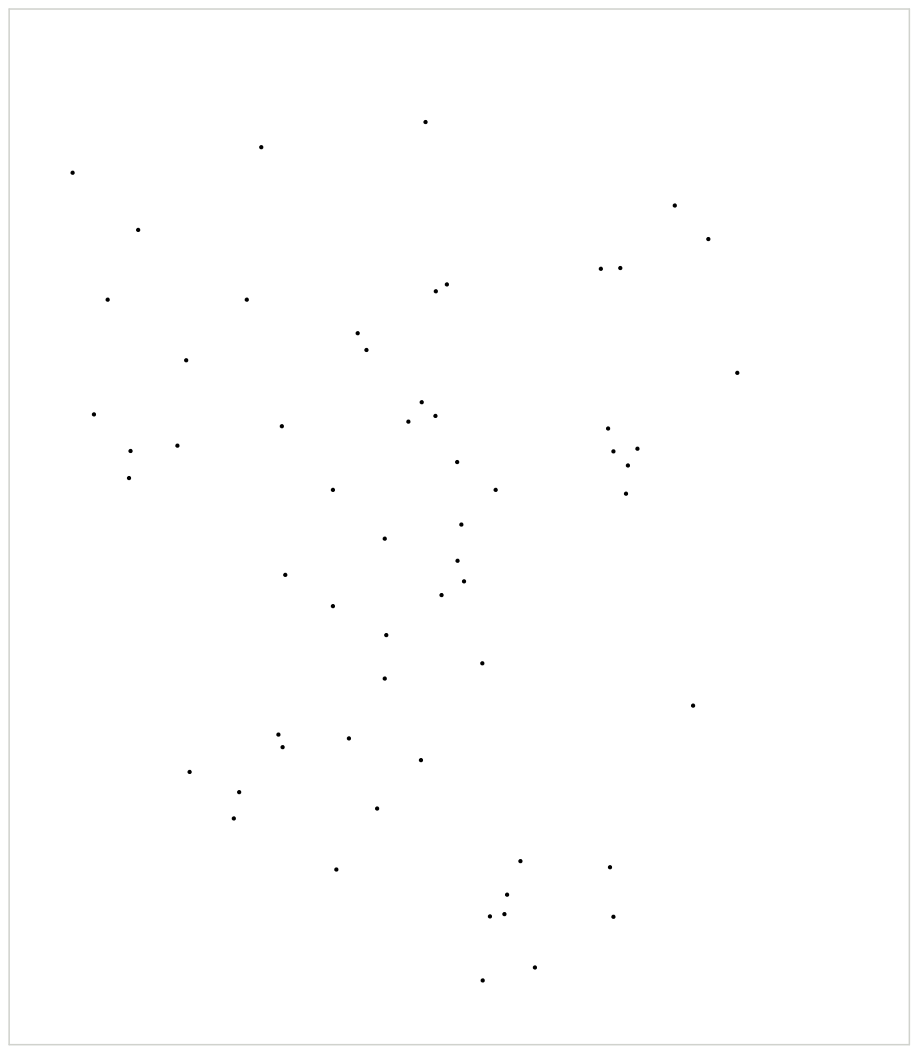
[picture p193: page 5]

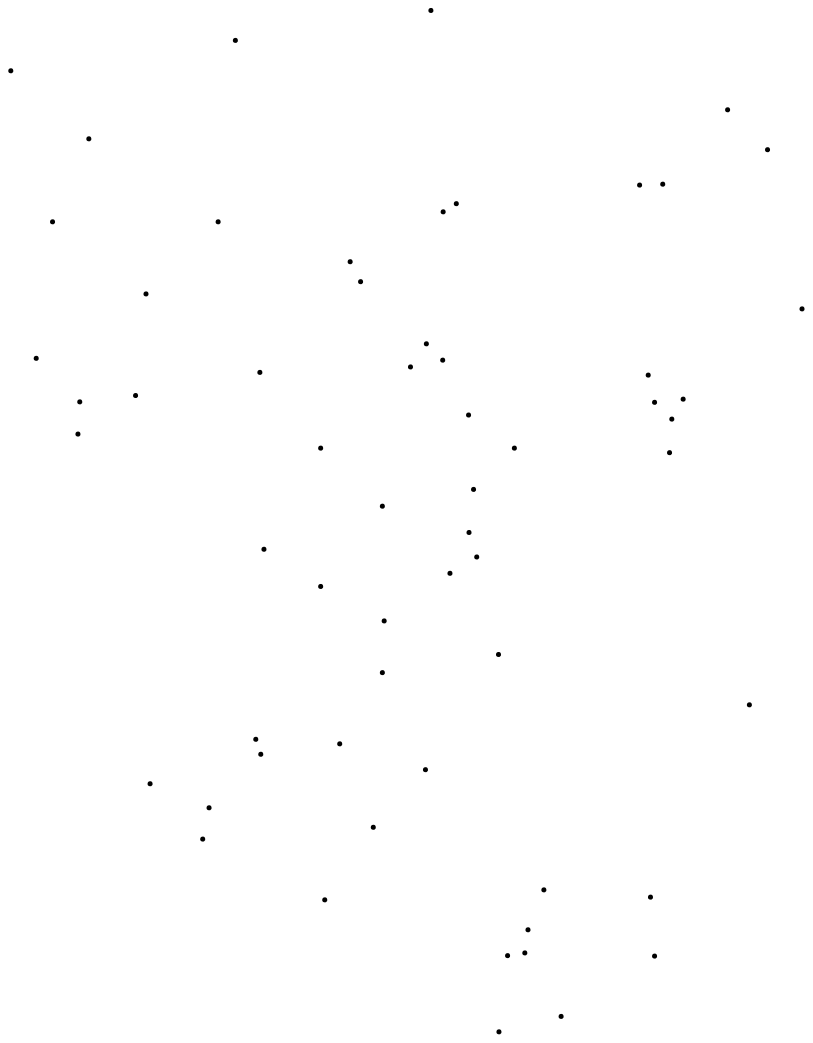
[picture p194: page 6]

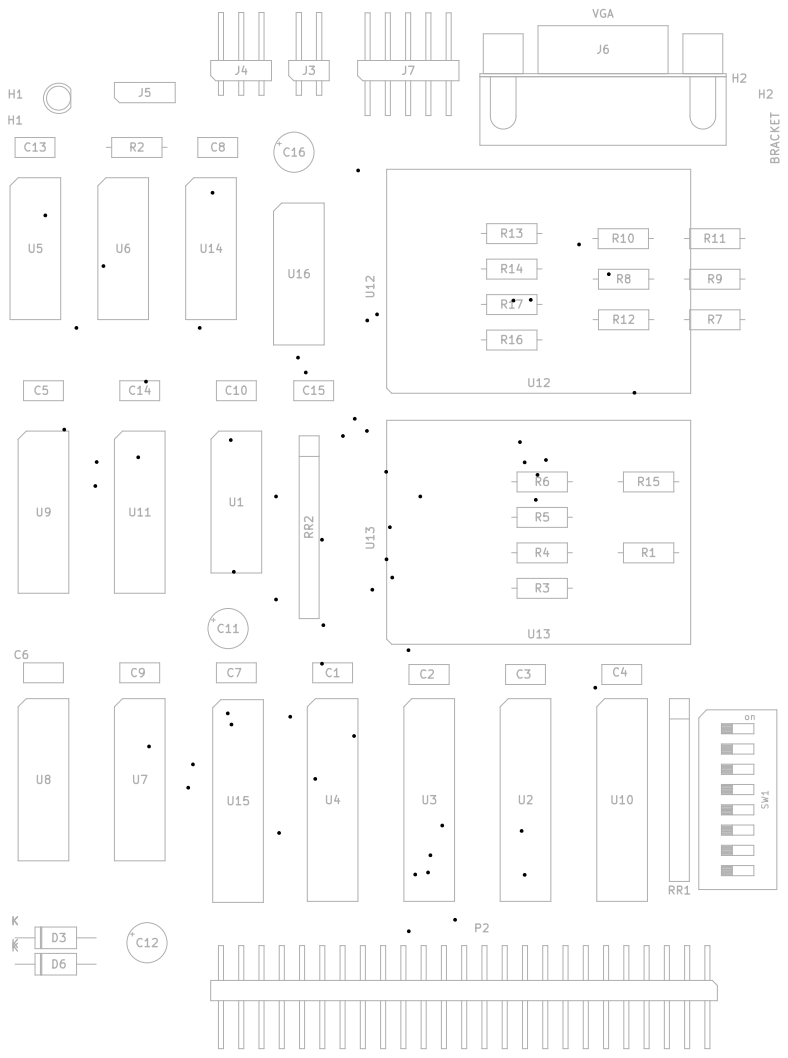
[picture p195: page 7]
