lynchaj/nhyodyne/Z80ESP/HARDWARE/z80esp-schematic-V0.9.pdf

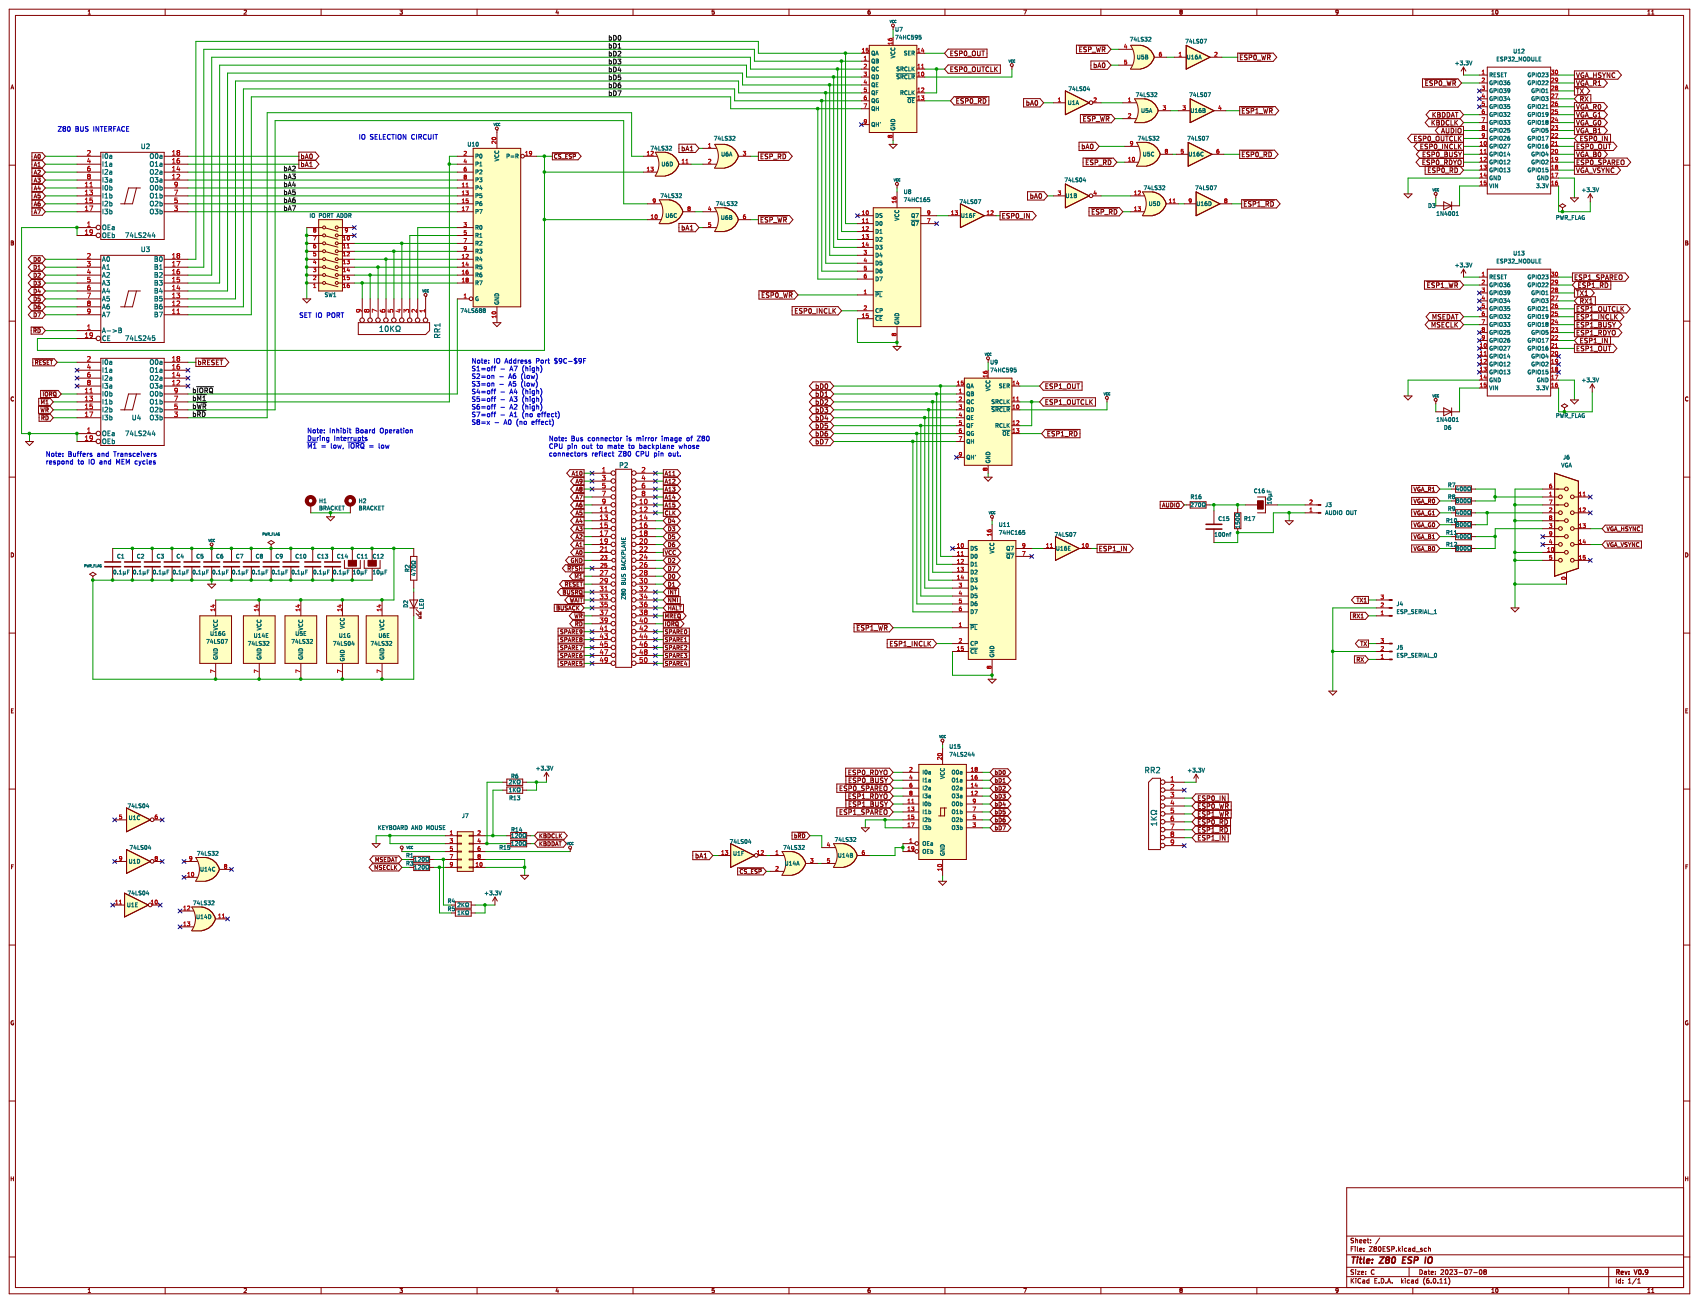
[picture p196: page 1]
