lynchaj/nhyodyne/Z80ESP/HARDWARE/z80esp-pcb-V0.5.pdf

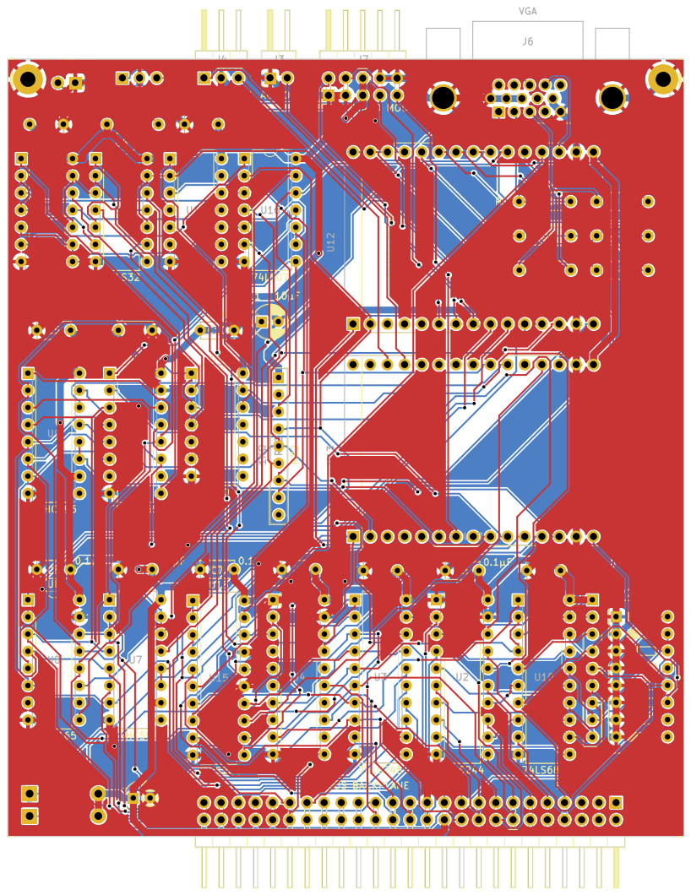
[picture p197: page 1]
