lynchaj/nhyodyne/Z80ESP/HARDWARE/z80esp-pcb-V0.6.pdf

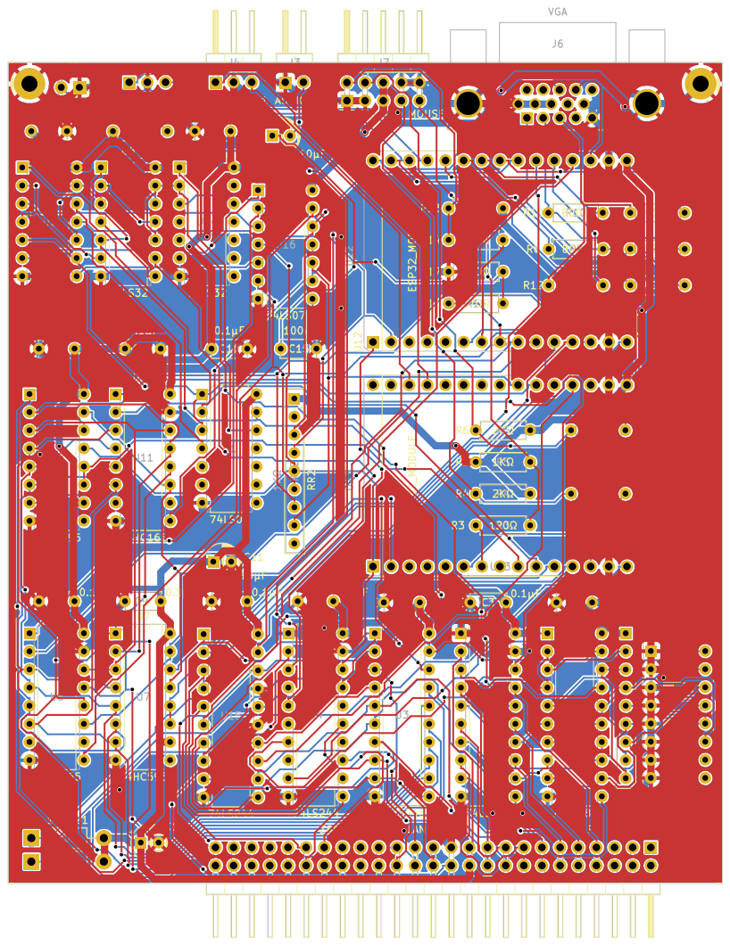
[picture p198: page 1]
