lynchaj/nhyodyne/Z80ESP/HARDWARE/z80esp-pcb-V0.7.pdf

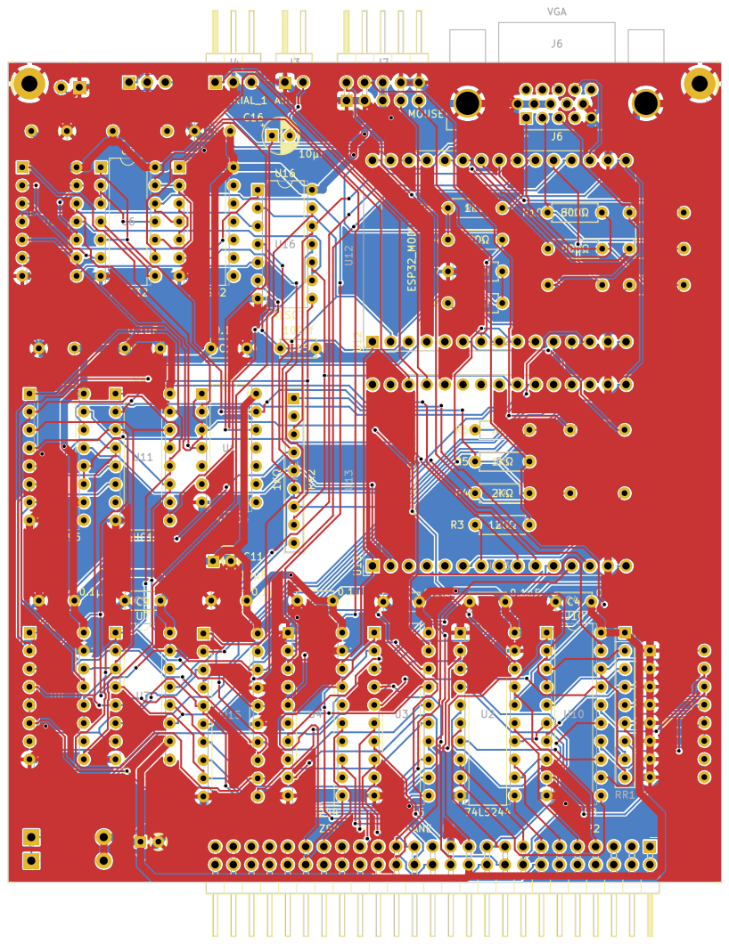
[picture p199: page 1]
