lynchaj/nhyodyne/Z80ESP/HARDWARE/z80esp-schematic-V0.5.pdf

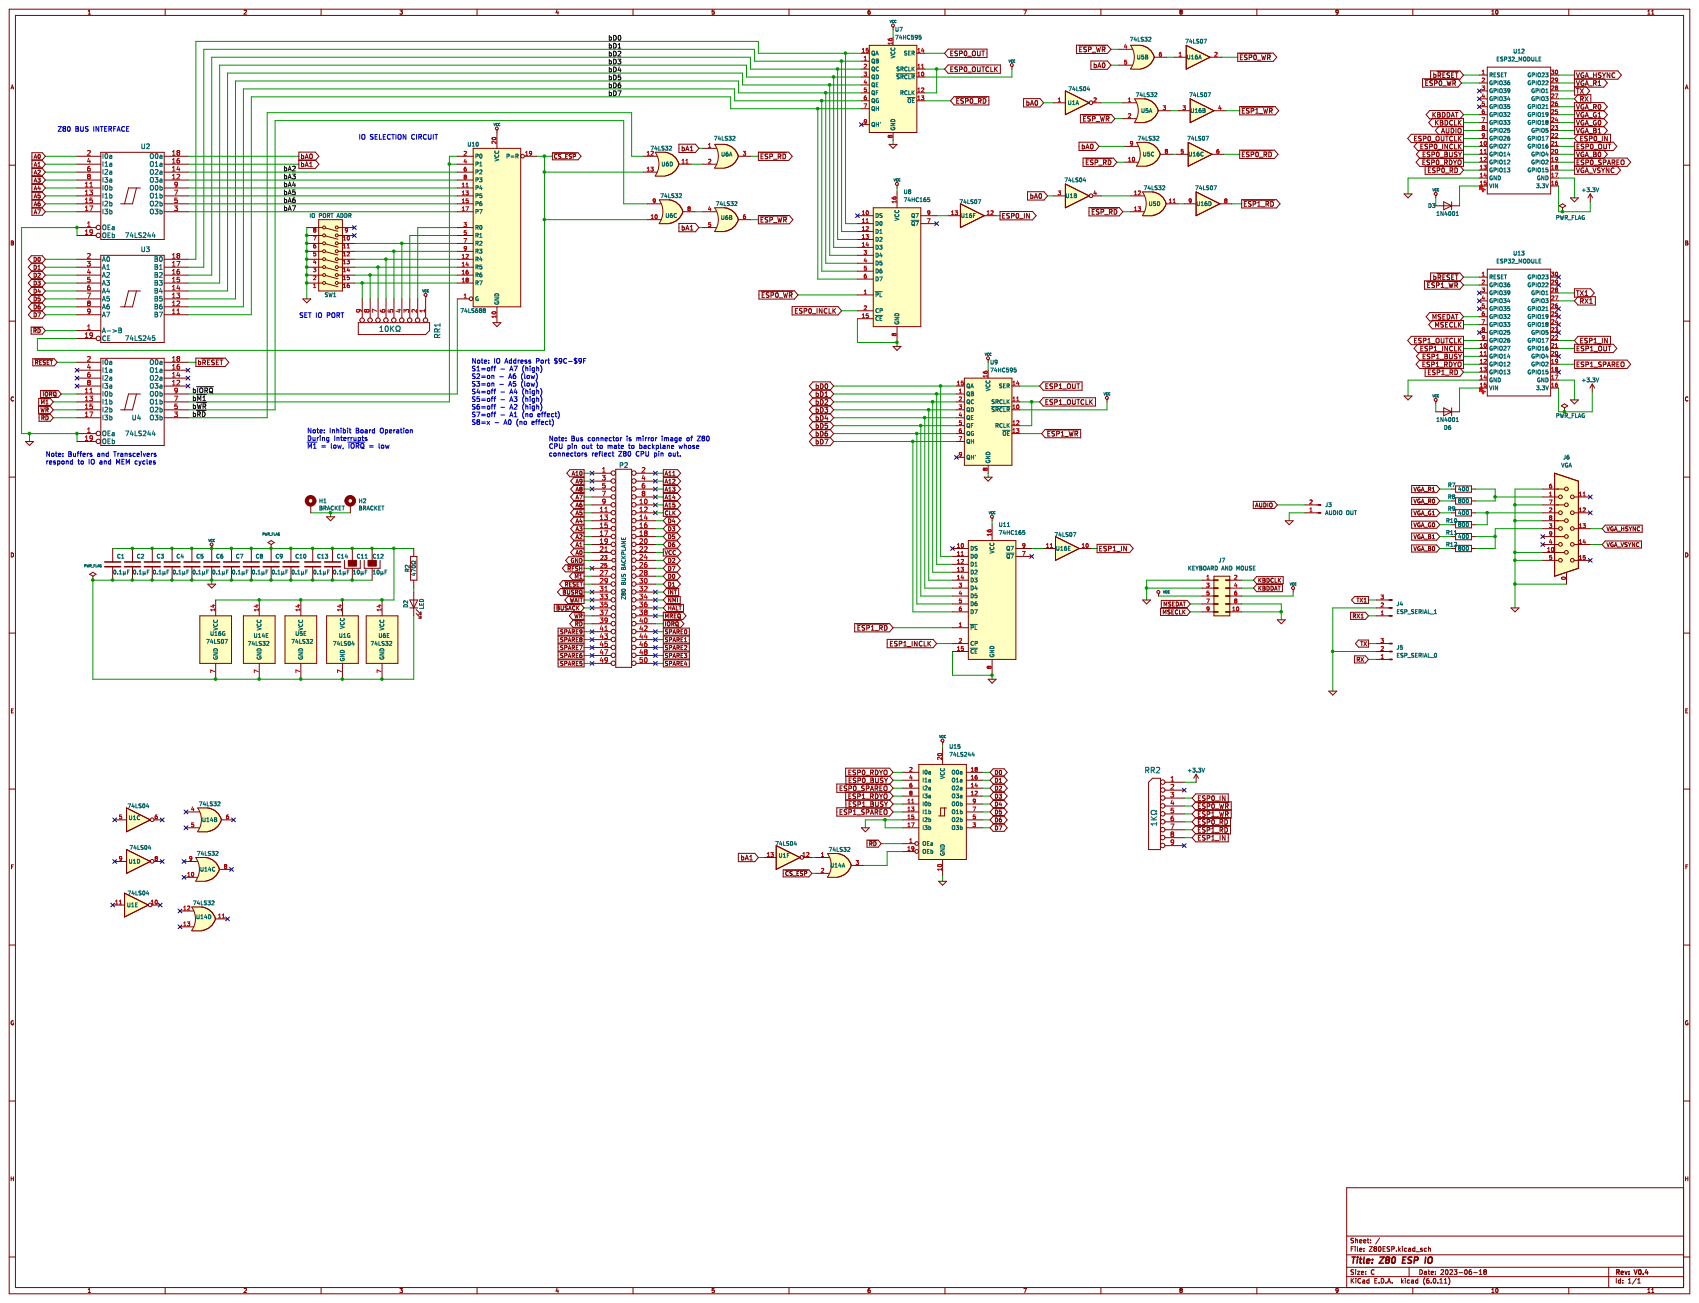
[picture p200: page 1]
