lynchaj/nhyodyne/Z80ESP/HARDWARE/z80esp-schematic-V0.6.pdf

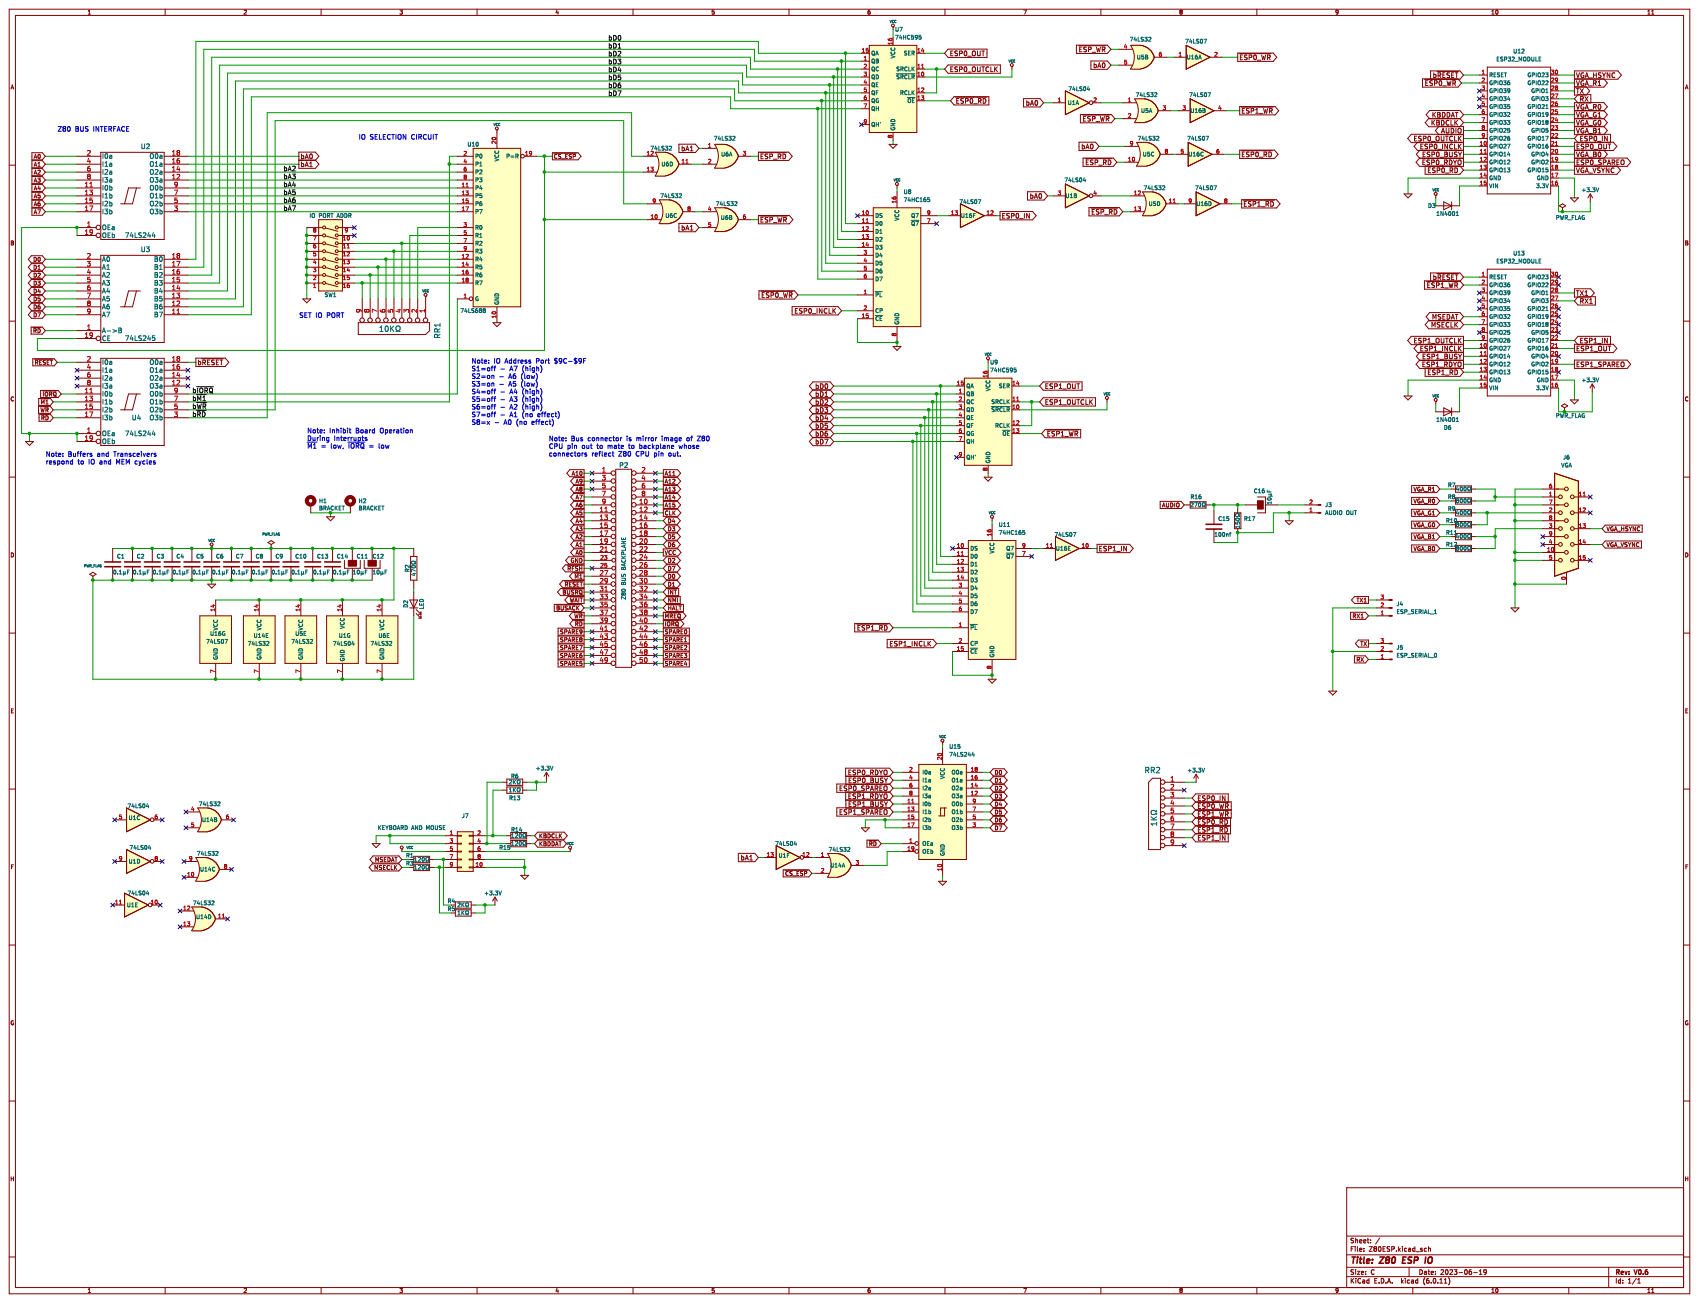
[picture p201: page 1]
