lynchaj/nhyodyne/Z80ESP/HARDWARE/z80esp-schematic-V0.7.pdf

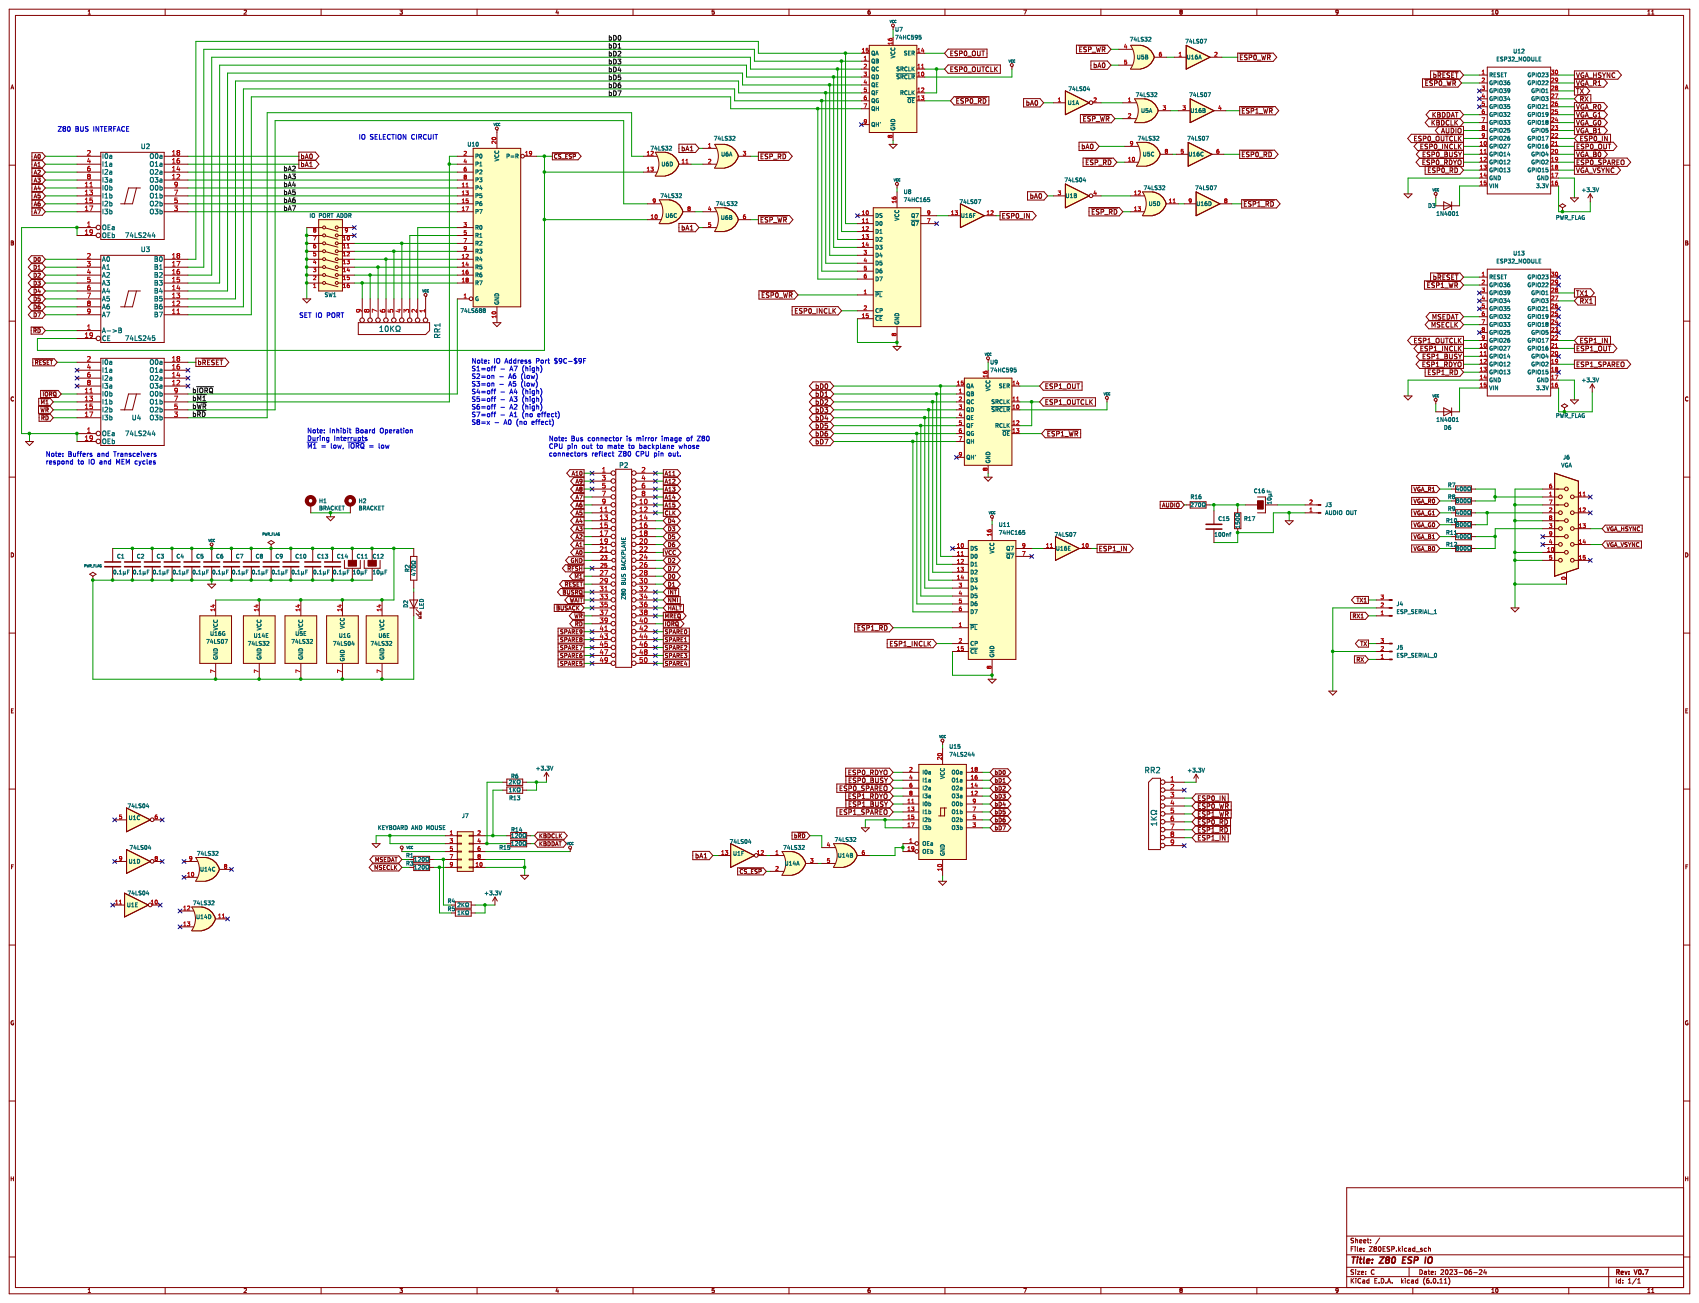
[picture p202: page 1]
