lynchaj/nhyodyne/Z80DUART2/Z80DUART2.kicad_pcb

## KiCad design Z80DUART2/Z80DUART2.kicad_pcb (2021-12-08)

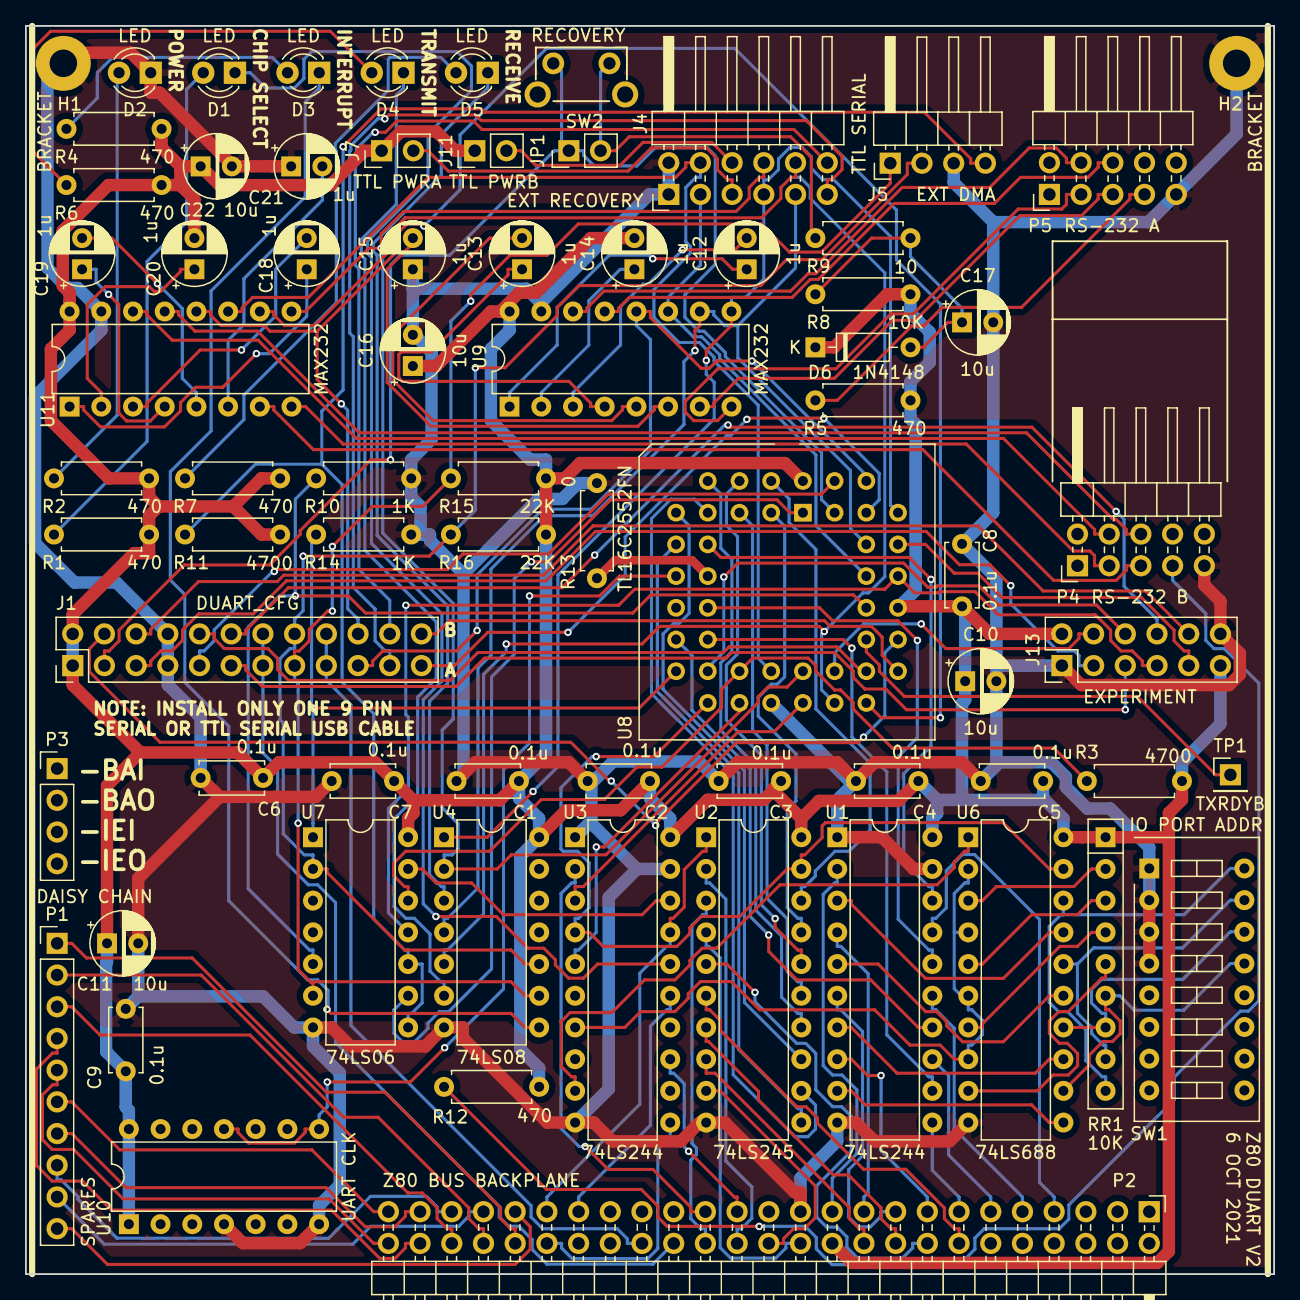
[picture p226: board Z80DUART2.kicad_pcb from above]

Board: 2 copper layers, 100.0 x 100.0 mm, 72 parts (0 on the bottom side), 134 nets.

Parts:
C1, C2, C3, C4, C5, C6, C7, C8, C9: 0.1u; C_Disc_D5.0mm_W2.5mm_P5.00mm
C10, C11, C16, C17, C22: 10u; CP_Radial_D5.0mm_P2.50mm
C12, C13, C14, C15, C18, C19, C20, C21: 1u; CP_Radial_D5.0mm_P2.50mm
D1, D2, D3, D4, D5: LED; LED_D3.0mm
D6: 1N4148; D_DO-35_SOD27_P7.62mm_Horizontal
H1, H2: BRACKET; MountingHole_2.2mm_M2_Pad
J1: DUART_CFG; PinHeader_2x12_P2.54mm_Vertical
J4: TTL SERIAL; PinHeader_2x06_P2.54mm_Horizontal
J5: EXT DMA; PinHeader_1x04_P2.54mm_Horizontal
J7: TTL PWRA; PinHeader_1x02_P2.54mm_Vertical
J11: TTL PWRB; PinHeader_1x02_P2.54mm_Vertical
J13: EXPERIMENT; PinHeader_2x06_P2.54mm_Vertical
JP1: EXT RECOVERY; PinHeader_1x02_P2.54mm_Vertical
P1: SPARES; PinHeader_1x10_P2.54mm_Vertical
P2: Z80 BUS BACKPLANE; PinHeader_2x25_P2.54mm_Horizontal
P3: DAISY CHAIN; PinHeader_1x04_P2.54mm_Vertical
P4: RS-232 B; PinHeader_2x05_P2.54mm_Horizontal
P5: RS-232 A; PinHeader_2x05_P2.54mm_Horizontal
R1, R2, R4, R5, R6, R7, R12: 470; R_Axial_DIN0207_L6.3mm_D2.5mm_P7.62mm_Horizontal
R3, R11: 4700; R_Axial_DIN0207_L6.3mm_D2.5mm_P7.62mm_Horizontal
R8: 10K; R_Axial_DIN0207_L6.3mm_D2.5mm_P7.62mm_Horizontal
R9: 10; R_Axial_DIN0207_L6.3mm_D2.5mm_P7.62mm_Horizontal
R10, R14: 1K; R_Axial_DIN0207_L6.3mm_D2.5mm_P7.62mm_Horizontal
R13: 0; R_Axial_DIN0207_L6.3mm_D2.5mm_P7.62mm_Horizontal
R15, R16: 22K; R_Axial_DIN0207_L6.3mm_D2.5mm_P7.62mm_Horizontal
RR1: 10K; R_Array_SIP9
SW1: IO PORT ADDR; SW_DIP_x8_W7.62mm_Slide
SW2: RECOVERY; SW_Tactile_SPST_Angled
TP1: TXRDYB; PinHeader_1x01_P2.54mm_Vertical
U1, U3: 74LS244; DIP-20_W7.62mm
U2: 74LS245; DIP-20_W7.62mm
U4: 74LS08; DIP-14_W7.62mm
U6: 74LS688; DIP-20_W7.62mm
U7: 74LS06; DIP-14_W7.62mm
U8: TL16C2552FN; PLCC-44_THT-Socket
U9, U11: MAX232; DIP-16_W7.62mm
U10: UART CLK; DIP-14_W7.62mm

Connections:
/688SEL#: U3.9, U6.1
/A0: P2.21, U1.2
/A1: P2.19, U1.4
/A2: P2.17, U1.6
/A3: P2.15, U1.8
/A4: P2.13, U1.11
/A5: P2.11, U1.13
/A6: P2.9, U1.15
/A7: P2.7, U1.17
/CLK_UART: U8.11, U10.8, U10.11
/CS_DUART#: U2.19, U3.4, U6.19, U8.18
/CTSA#: P5.6, U9.13
/CTSA_DSRA#: J1.21, J4.11
/CTSB#: P4.6, U11.13
/CTSB_DSRB#: J1.22, J4.12
/D0: P2.28, U2.2
/D1: P2.30, U2.3
/D2: P2.24, U2.4
/D3: P2.16, U2.5
/D4: P2.14, U2.6
/D5: P2.18, U2.7
/D6: P2.20, U2.8
/D7: P2.26, U2.9
/DTRA#: P5.7, R5.1
/DTRB#: P4.7, R12.1
/EXP_CDA#: J1.11, J13.5
/EXP_CDB#: J1.12, J13.8
/EXP_RIA#: J1.5, J13.3
/EXP_RIB#: J1.6, J13.10
/GND_UART: R13.1, U8.12
/INT#: J1.13, J1.14, P2.32
/INTA: R10.1, U7.5, U8.34
/INTB: R14.1, U7.1, U8.17
/IORQ#: P2.40, U3.11
/M1#: P2.27, U3.13
/NMI#: J1.17, J1.18, P2.34
/RD#: P2.39, U2.1, U3.17
/RESET#: P2.29, U3.2
/RTSA#: P5.4, U9.14
/RTSB#: P4.4, U11.14
/RXA: P5.3, U9.8
/RXB: P4.3, U11.8
/SPARE0: P1.1, P2.42
/SPARE1: P1.2, P2.44
/SPARE2: P1.3, P2.46
/SPARE3: P1.4, P2.48
/SPARE4: P1.5, P2.50
/SPARE5: P1.6, P2.49
/SPARE6: P1.7, P2.47
/SPARE7: P1.8, P2.45
/SPARE8: P1.9, P2.43
/SPARE9: P1.10, P2.41
/TTL_CDA#: J1.9, U8.42
/TTL_CDB#: J1.10, U8.30
/TTL_CTSA#: J1.19, U8.40, U9.12
/TTL_CTSB#: J1.20, U8.28, U11.12
/TTL_DSRA#: J1.23, U8.41
/TTL_DSRB#: J1.24, U8.29
/TTL_DTRA#: J13.9, U8.37
/TTL_DTRB#: J13.4, U8.27
/TTL_MFA#: J13.7, U7.11, U8.35
/TTL_MFB#: J13.6, U8.19
/TTL_RIA#: J1.3, JP1.1, SW2.1, U8.43
/TTL_RIB#: J1.4, U8.31
/TTL_RTSA#: J4.3, U8.36, U9.11
/TTL_RTSB#: J4.4, U8.23, U11.11
/TTL_RXA: J4.7, U4.1, U8.39, U9.9
/TTL_RXB: J4.8, U4.2, U8.25, U11.9
/TTL_TXA: J4.9, U4.4, U8.38, U9.10
/TTL_TXB: J4.10, U4.5, U8.26, U11.10
/TXA: P5.5, U9.7
/TXB: P4.5, U11.7
/TXRDYA#: U7.9, U8.1
/TXRDYB#: TP1.1, U8.32
/UINTA#: J1.15, J5.1, R15.1, U4.9, U7.6
/UINTB#: J1.16, J5.2, R16.1, U4.10, U7.2
/WR#: P2.37, U3.15
/bA0: U1.18, U8.10
/bA1: U1.16, U8.14
/bA2: U1.14, U8.15
/bA3: U1.12, U8.16
/bA4: U1.9, U6.11
/bA5: U1.7, U6.13
/bA6: U1.5, U6.15
/bA7: U1.3, U6.17
/bD0: U2.18, U8.2
/bD1: U2.17, U8.3
/bD2: U2.16, U8.4
/bD3: U2.15, U8.5
/bD4: U2.14, U8.6
/bD5: U2.13, U8.7
/bD6: U2.12, U8.8
/bD7: U2.11, U8.9
/bM1#: U3.7, U6.2, U6.4, U6.6, U6.8
/bRD#: U3.3, U8.24
/bRESET: R3.1, U7.12, U8.21
/bRESET#: U3.18, U7.13
/bWR#: U3.5, U8.20
GND: C1.2, C2.2, C3.2, C4.2, C5.2, C6.2, C7.2, C8.2, C9.2, C10.2, C11.2, C15.1, C16.2, C17.2, C21.1, C22.2, D2.1, H1.1, H2.1, J1.7, J1.8, J4.1, J4.2, J5.3, J13.1, J13.12, P2.23, P4.9, P5.9, R10.2, R13.2, R14.2, SW1.1, SW1.2, SW1.3, SW1.4, U1.1, U1.10, U1.19, U2.10, U3.1, U3.10, U3.19, U4.7, U6.10, U7.7, U8.22, U9.15, U10.4, U10.7, U11.15
unnamed: C12.1, U9.1
unnamed: C12.2, U9.3
unnamed: C13.1, U9.4
unnamed: C13.2, U9.5
unnamed: C14.1, U9.2
unnamed: C15.2, U9.6
unnamed: C17.1, D6.2, R8.1, R9.2
unnamed: C18.1, U11.1
unnamed: C18.2, U11.3
unnamed: C19.1, U11.4
unnamed: C19.2, U11.5
unnamed: C20.1, U11.2
unnamed: C21.2, U11.6
unnamed: D1.1, U3.16
unnamed: D1.2, R1.1
unnamed: D2.2, R2.1
unnamed: D3.1, U4.8
unnamed: D3.2, R4.1
unnamed: D4.1, U4.6
unnamed: D4.2, R6.1
unnamed: D5.1, U4.3
unnamed: D5.2, R7.1
unnamed: J4.5, J7.2
unnamed: J5.4, R11.1, U7.8, U7.10
unnamed: J4.6, J11.2
unnamed: JP1.2, R9.1, SW2.2
unnamed: RR1.2, U6.3
unnamed: RR1.3, U6.5
unnamed: RR1.4, U6.7
unnamed: RR1.5, U6.9
unnamed: RR1.6, SW1.13, U6.12
unnamed: RR1.7, SW1.14, U6.14
unnamed: RR1.8, SW1.15, U6.16
unnamed: RR1.9, SW1.16, U6.18
VCC: C1.1, C2.1, C3.1, C4.1, C5.1, C6.1, C7.1, C8.1, C9.1, C10.1, C11.1, C14.2, C16.1, C20.2, C22.1, D6.1, J1.1, J1.2, J7.1, J11.1, J13.2, J13.11, P2.22, R1.2, R2.2, R3.2, R4.2, R5.2, R6.2, R7.2, R8.2, R11.2, R12.2, R15.2, R16.2, RR1.1, U1.20, U2.20, U3.20, U4.14, U6.20, U7.14, U8.33, U8.44, U9.16, U10.1, U10.14, U11.16
