lynchaj/nhyodyne/Z80ROM2/Z80ROM2.kicad_pcb

## KiCad design Z80ROM2/Z80ROM2.kicad_pcb (2021-11-30)

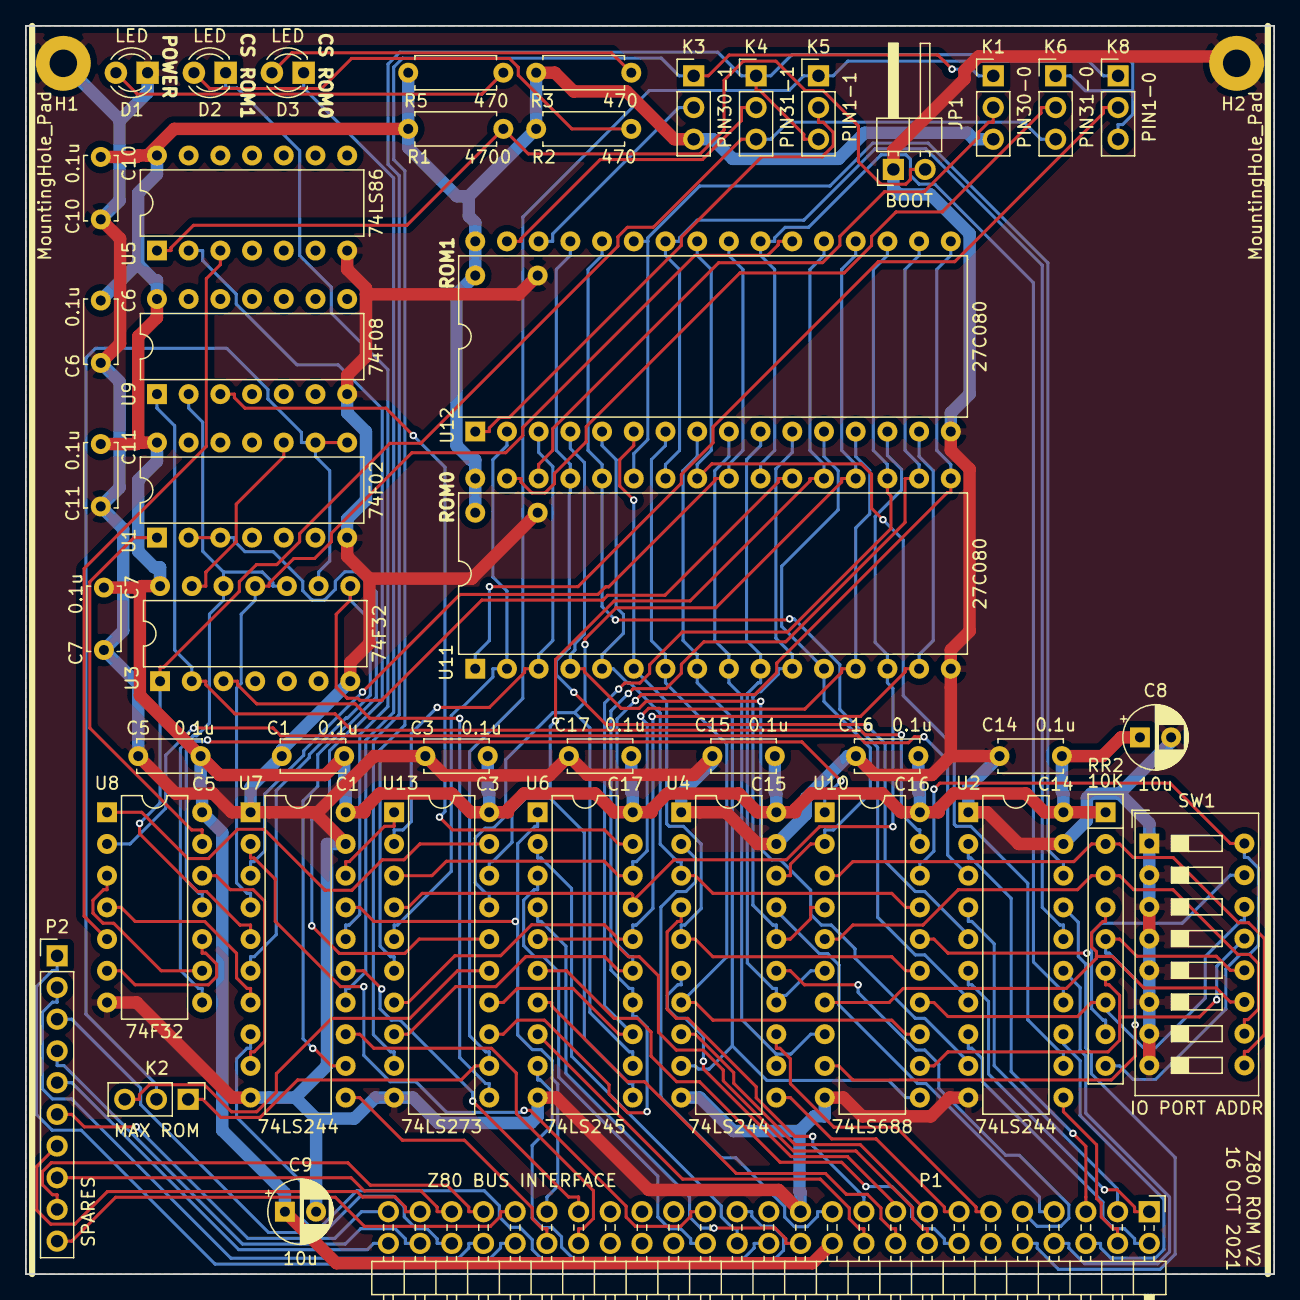
[picture p227: board Z80ROM2.kicad_pcb from above]

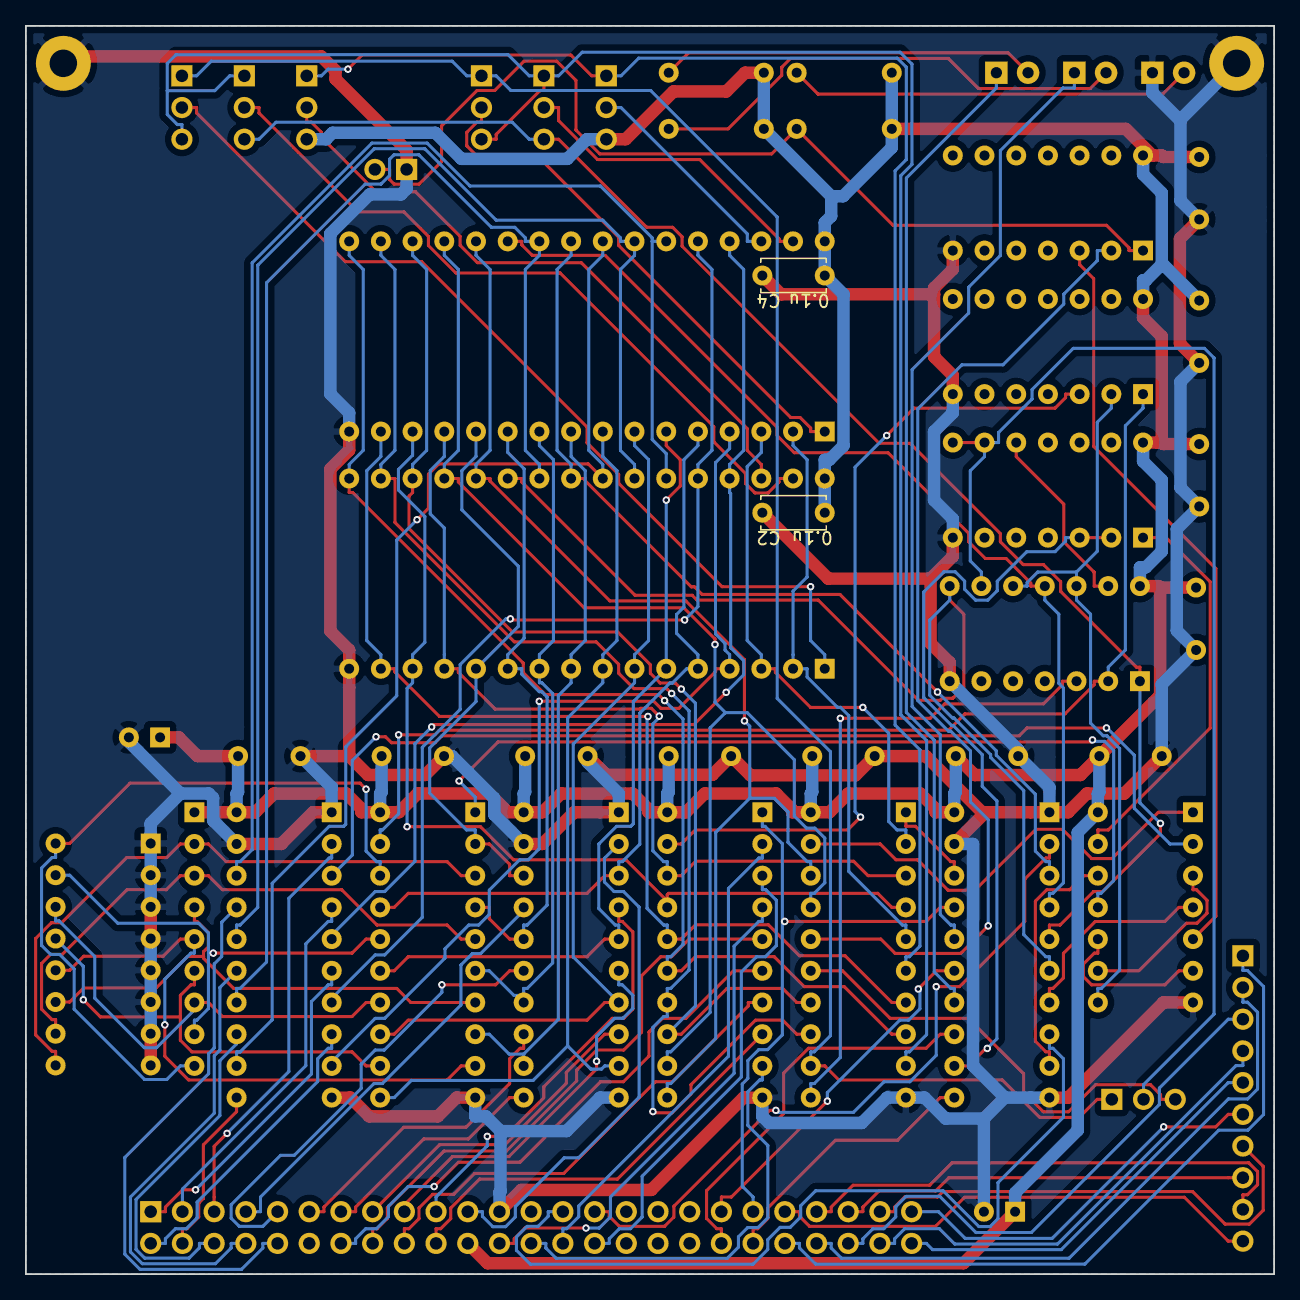
[picture p228: board Z80ROM2.kicad_pcb from below]

Board: 2 copper layers, 100.0 x 100.0 mm, 49 parts (2 on the bottom side), 113 nets.

Parts:
C1, C2, C3, C4, C5, C6, C7, C10, C11, C14, C15, C16, C17: 0.1u; C_Disc_D5.0mm_W2.5mm_P5.00mm
C8, C9: 10u; CP_Radial_D5.0mm_P2.50mm
D1, D2, D3: LED; LED_D3.0mm
H1, H2: MountingHole_Pad; MountingHole_2.2mm_M2_Pad
JP1: BOOT; PinHeader_1x02_P2.54mm_Horizontal
K1: PIN30-0; PinHeader_1x03_P2.54mm_Vertical
K2: MAX ROM; PinHeader_1x03_P2.54mm_Vertical
K3: PIN30-1; PinHeader_1x03_P2.54mm_Vertical
K4: PIN31-1; PinHeader_1x03_P2.54mm_Vertical
K5: PIN1-1; PinHeader_1x03_P2.54mm_Vertical
K6: PIN31-0; PinHeader_1x03_P2.54mm_Vertical
K8: PIN1-0; PinHeader_1x03_P2.54mm_Vertical
P1: Z80 BUS INTERFACE; PinHeader_2x25_P2.54mm_Horizontal
P2: SPARES; PinHeader_1x10_P2.54mm_Vertical
R1: 4700; R_Axial_DIN0207_L6.3mm_D2.5mm_P7.62mm_Horizontal
R2, R3, R5: 470; R_Axial_DIN0207_L6.3mm_D2.5mm_P7.62mm_Horizontal
RR2: 10K; R_Array_SIP9
SW1: IO PORT ADDR; SW_DIP_SPSTx08_Slide_9.78x22.5mm_W7.62mm_P2.54mm
U1: 74F02; DIP-14_W7.62mm
U2, U4, U7: 74LS244; DIP-20_W7.62mm
U3, U8: 74F32; DIP-14_W7.62mm
U5: 74LS86; DIP-14_W7.62mm
U6: 74LS245; DIP-20_W7.62mm
U9: 74F08; DIP-14_W7.62mm
U10: 74LS688; DIP-20_W7.62mm
U11, U12: 27C080; DIP-32_W15.24mm
U13: 74LS273; DIP-20_W7.62mm

Connections:
/688SEL#: U8.11, U10.1
//BOOT_ROM: JP1.2, R1.1, U5.1
//CS_MPCL: U3.2, U9.1, U10.19
//CS_ROM: U3.10, U3.12, U8.8, U9.2
//IORQ: P1.40, U7.11
//LOW_ROM_EN: U8.1, U13.19
//M1: P1.27, U7.8
//MPCL_WR: U3.3, U13.11
//MREQ: P1.38, U7.13
//RD: P1.39, U6.1, U7.17
//RESET: P1.29, U7.2
//WR: P1.37, U7.15
/A0: P1.21, U4.2
/A1: P1.19, U4.4
/A2: P1.17, U4.6
/A3: P1.15, U4.8
/A4: P1.13, U4.11
/A5: P1.11, U4.13
/A6: P1.9, U4.15
/A7: P1.7, U4.17
/A8: P1.5, U2.2
/A9: P1.3, U2.4
/A10: P1.1, U2.6
/A11: P1.2, U2.8
/A12: P1.4, U2.11
/A13: P1.6, U2.13
/A14: P1.8, U2.15
/A15: P1.10, U2.17
/A15_ROM: U11.3, U12.3, U13.2
/A16_ROM: U11.2, U12.2, U13.5
/A17_ROM: K1.1, K3.1, U13.6
/A18_ROM: K4.1, K5.3, K6.1, K8.3, U13.9
/A19_ROM: K2.1, K5.1, K8.1, U13.12
/A20_ROM: K2.3, U13.15
/BOOT: U5.3, U8.5
/BOOT_OVERRIDE: U5.2, U13.16
/CS_ROM0#: U3.8, U7.6, U11.22
/CS_ROM1#: U3.11, U7.4, U12.22
/D0: P1.28, U6.2
/D1: P1.30, U6.3
/D2: P1.24, U6.4
/D3: P1.16, U6.5
/D4: P1.14, U6.6
/D5: P1.18, U6.7
/D6: P1.20, U6.8
/D7: P1.26, U6.9
/ROM_SIZE: K2.2, U1.8, U1.9, U3.9
/SPARE0: P1.42, P2.1
/SPARE1: P1.44, P2.2
/SPARE2: P1.46, P2.3
/SPARE3: P1.48, P2.4
/SPARE4: P1.50, P2.5
/SPARE5: P1.49, P2.6
/SPARE6: P1.47, P2.7
/SPARE7: P1.45, P2.8
/SPARE8: P1.43, P2.9
/SPARE9: P1.41, P2.10
/b/IORQ: U7.9, U8.12
/b/M1: U1.2, U1.3, U7.12
/b/MREQ: U7.7, U8.4
/b/RD: U7.3, U11.24, U12.24
/b/RESET: U7.18, U13.1
/b/WR: K4.3, K6.3, U3.1, U7.5
/bA15: U2.3, U8.2
GND: C1.2, C2.2, C3.2, C4.2, C5.2, C6.2, C7.2, C8.2, C9.2, C10.2, C11.2, C14.2, C15.2, C16.2, C17.2, D1.1, H1.1, H2.1, JP1.1, P1.23, SW1.1, SW1.2, SW1.3, SW1.4, SW1.5, SW1.6, SW1.7, SW1.8, U1.7, U2.1, U2.10, U2.19, U3.7, U4.1, U4.10, U4.19, U5.7, U6.10, U7.1, U7.10, U7.19, U8.7, U9.7, U10.10, U11.16, U12.16, U13.10
unnamed: D1.2, R5.1
unnamed: D2.1, U7.16
unnamed: D2.2, R2.1
unnamed: D3.1, U7.14
unnamed: D3.2, R3.1
unnamed: K1.2, U11.30
unnamed: K3.2, U12.30
unnamed: K4.2, U12.31
unnamed: K5.2, U12.1
unnamed: K6.2, U11.31
unnamed: K8.2, U11.1
unnamed: RR2.2, SW1.9, U10.3
unnamed: RR2.3, SW1.10, U10.5
unnamed: RR2.4, SW1.11, U10.7
unnamed: RR2.5, SW1.12, U10.9
unnamed: RR2.6, SW1.13, U10.12
unnamed: RR2.7, SW1.14, U10.14
unnamed: RR2.8, SW1.15, U10.16
unnamed: RR2.9, SW1.16, U10.18
unnamed: U1.1, U8.13
unnamed: U1.10, U3.13
unnamed: U6.19, U9.3
unnamed: U8.3, U8.9
unnamed: U8.6, U8.10
unnamed: U4.18, U10.2, U11.12, U12.12
unnamed: U4.16, U10.4, U11.11, U12.11
unnamed: U4.14, U10.6, U11.10, U12.10
unnamed: U4.12, U10.8, U11.9, U12.9
unnamed: U4.9, U10.11, U11.8, U12.8
unnamed: U4.7, U10.13, U11.7, U12.7
unnamed: U4.5, U10.15, U11.6, U12.6
unnamed: U4.3, U10.17, U11.5, U12.5
unnamed: U2.9, U11.4, U12.4
unnamed: U6.18, U11.13, U12.13, U13.3
unnamed: U6.17, U11.14, U12.14, U13.4
unnamed: U6.16, U11.15, U12.15, U13.7
unnamed: U6.15, U11.17, U12.17, U13.8
unnamed: U6.14, U11.18, U12.18, U13.13
unnamed: U6.13, U11.19, U12.19, U13.14
unnamed: U6.12, U11.20, U12.20, U13.17
unnamed: U6.11, U11.21, U12.21, U13.18
unnamed: U2.14, U11.23, U12.23
unnamed: U2.12, U11.25, U12.25
unnamed: U2.16, U11.26, U12.26
unnamed: U2.18, U11.27, U12.27
unnamed: U2.7, U11.28, U12.28
unnamed: U2.5, U11.29, U12.29
VCC: C1.1, C2.1, C3.1, C4.1, C5.1, C6.1, C7.1, C8.1, C9.1, C10.1, C11.1, C14.1, C15.1, C16.1, C17.1, K1.3, K3.3, P1.22, R1.2, R2.2, R3.2, R5.2, RR2.1, U1.14, U2.20, U3.14, U4.20, U5.14, U6.20, U7.20, U8.14, U9.14, U10.20, U11.32, U12.32, U13.20
