lynchaj/nhyodyne/Z80PROC3/Z80PROC3.kicad_pcb

## KiCad design Z80PROC3/Z80PROC3.kicad_pcb (2021-11-30)

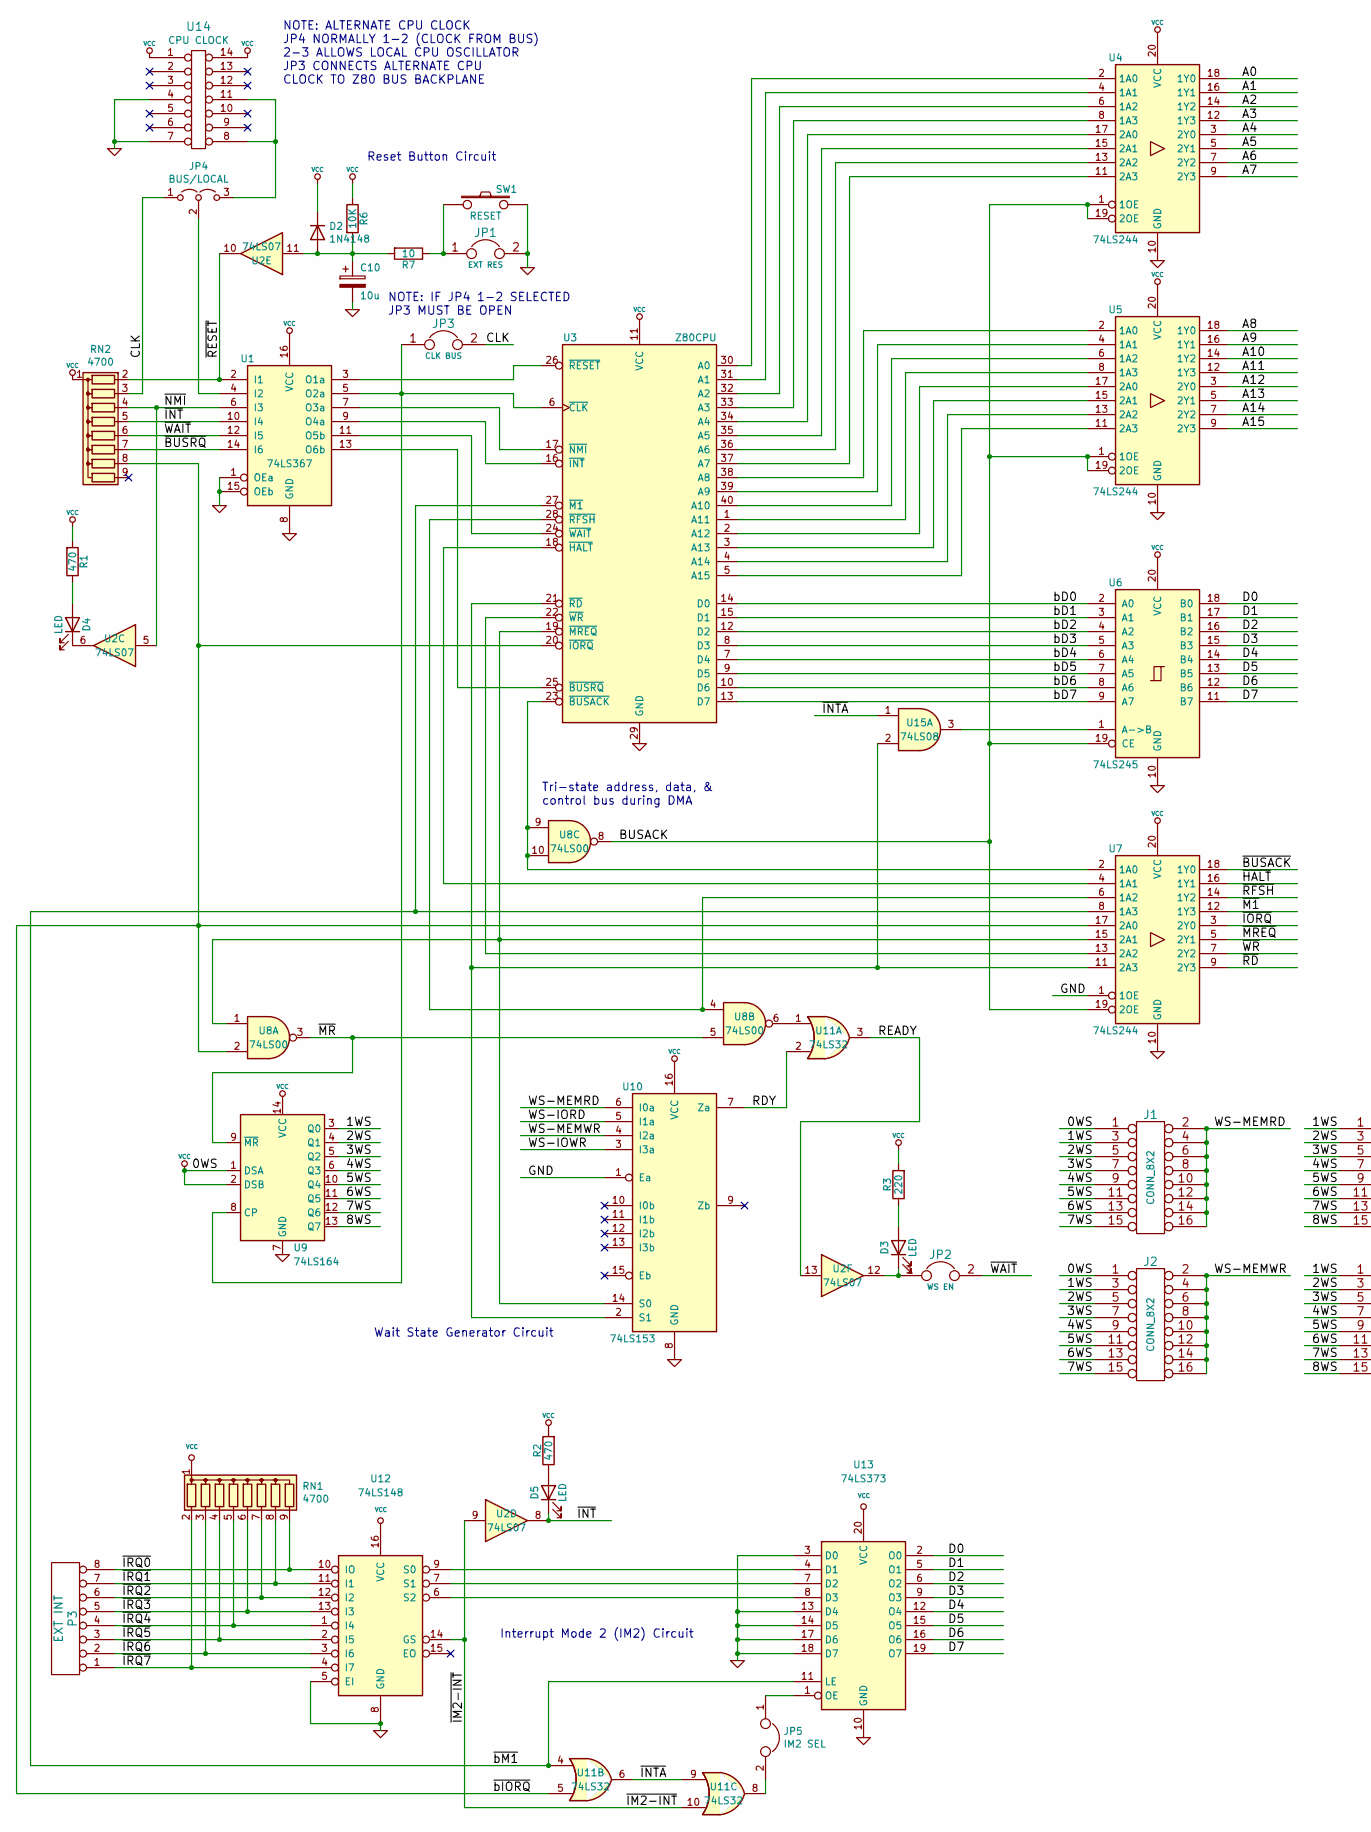
[picture p229: schematic Z80PROC3.sch, part in row 1, column 1]

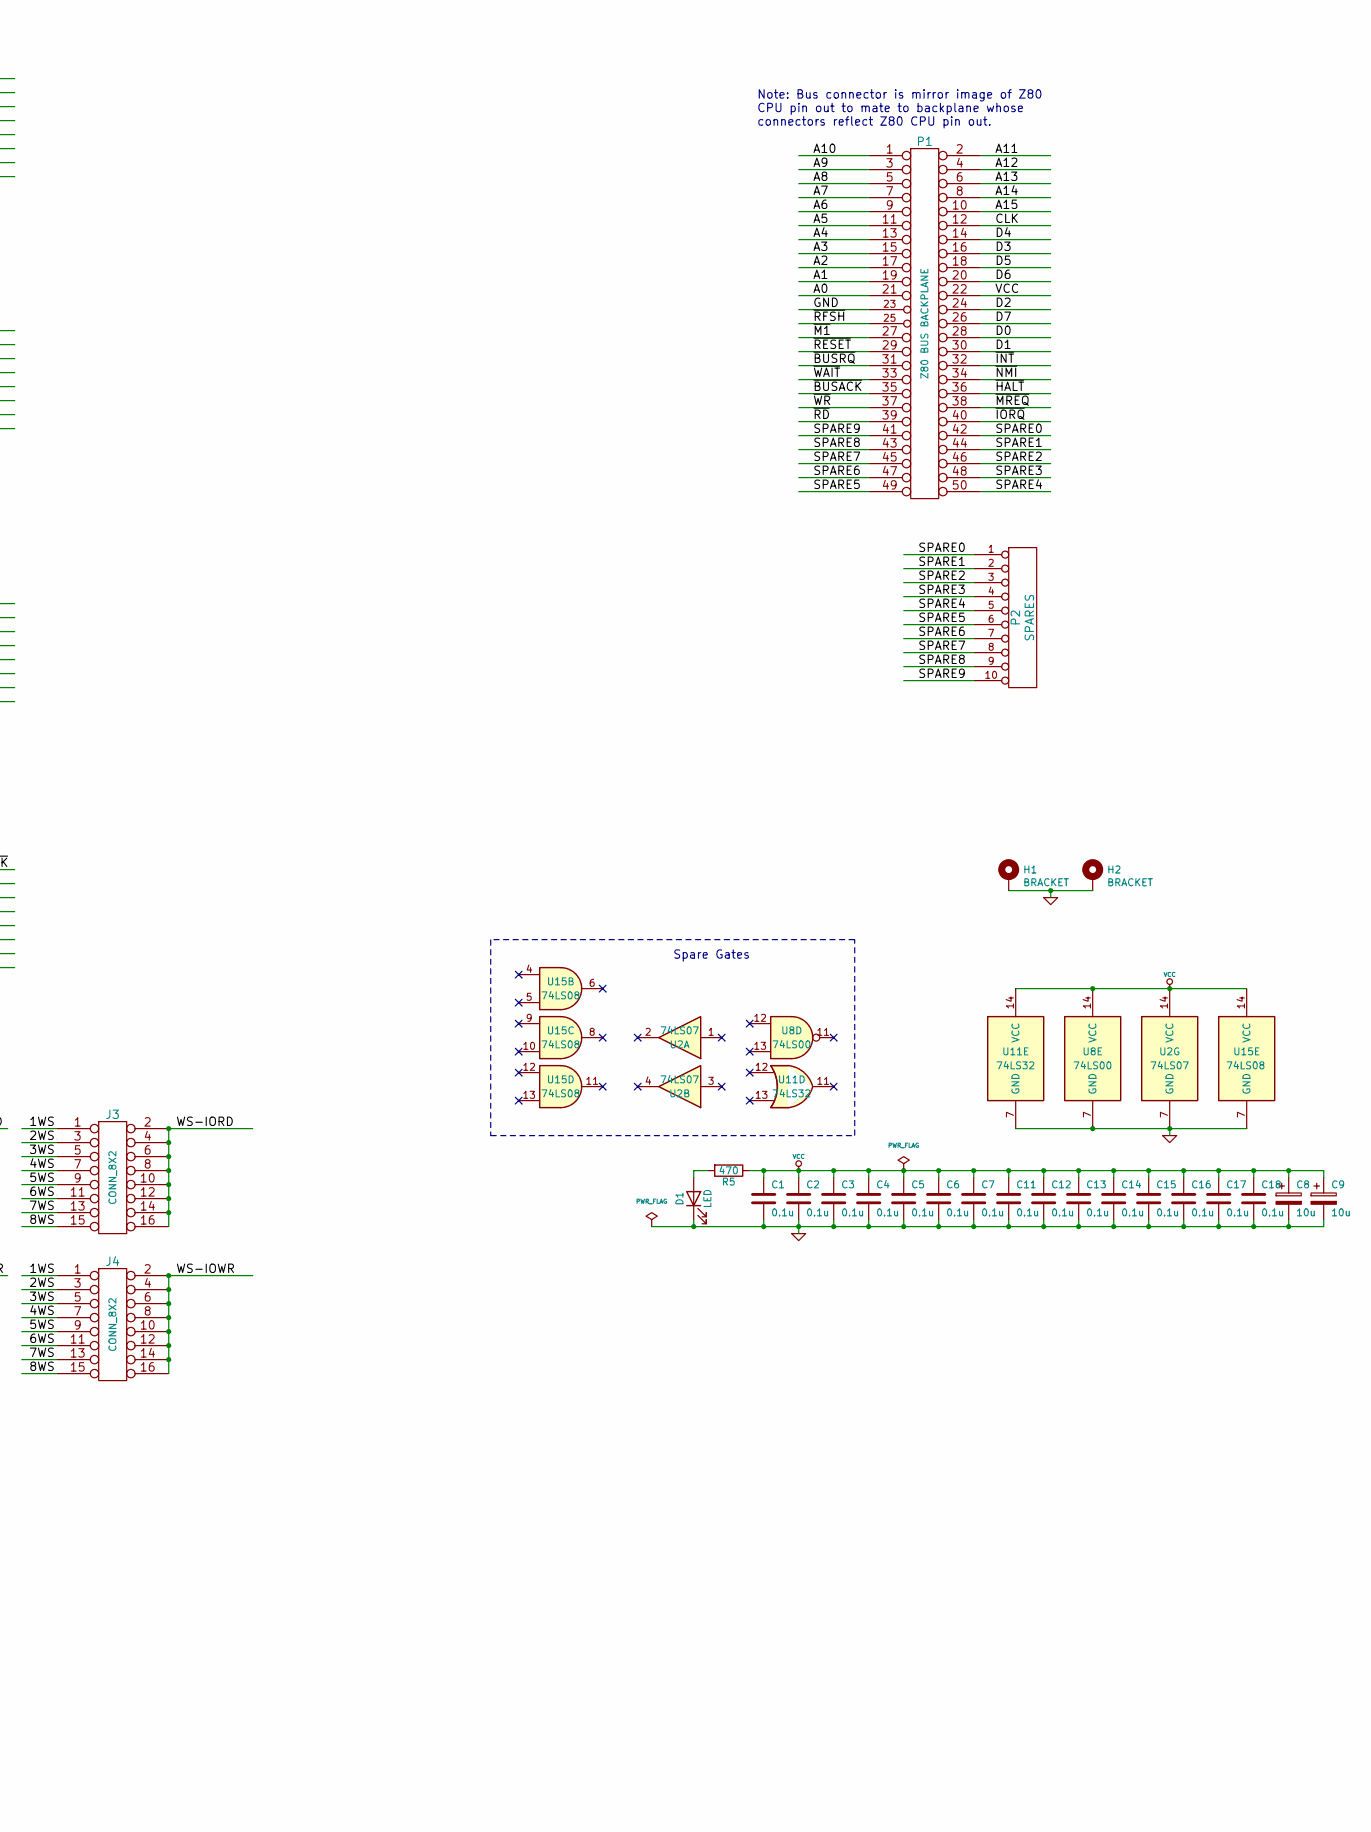
[picture p230: schematic Z80PROC3.sch, part in row 1, column 2]

Parts:
C1, C2, C3, C4, C5, C6, C7, C11, C12, C13, C14, C15, C16, C17, C18: 0.1u; C_Disc_D5.0mm_W2.5mm_P5.00mm
C8, C9, C10: 10u; CP_Radial_D5.0mm_P2.50mm
D1, D3, D4, D5: LED; LED_D3.0mm
D2: 1N4148; D_DO-35_SOD27_P7.62mm_Horizontal
H1, H2: BRACKET; MountingHole_2.2mm_M2_Pad
J1, J2, J3, J4: CONN_8X2; PinHeader_2x08_P2.54mm_Vertical
JP1: EXT RES; PinHeader_2x01_P2.54mm_Horizontal
JP2: WS EN; PinHeader_2x01_P2.54mm_Horizontal
JP3: CLK BUS; PinHeader_2x01_P2.54mm_Vertical
JP4: BUS/LOCAL; PinHeader_1x03_P2.54mm_Vertical
JP5: IM2 SEL; PinHeader_2x01_P2.54mm_Vertical
P1: Z80 BUS BACKPLANE; PinHeader_2x25_P2.54mm_Horizontal
P2: SPARES; PinHeader_1x10_P2.54mm_Vertical
P3: EXT INT; PinHeader_2x04_P2.54mm_Horizontal
R1, R2, R5: 470; R_Axial_DIN0207_L6.3mm_D2.5mm_P7.62mm_Horizontal
R3: 220; R_Axial_DIN0207_L6.3mm_D2.5mm_P7.62mm_Horizontal
R6: 10K; R_Axial_DIN0207_L6.3mm_D2.5mm_P7.62mm_Horizontal
R7: 10; R_Axial_DIN0207_L6.3mm_D2.5mm_P7.62mm_Horizontal
RN1, RN2: 4700; R_Array_SIP9
SW1: RESET; SW_Tactile_SPST_Angled
U1: 74LS367; DIP-16_W7.62mm
U2: 74LS07; DIP-14_W7.62mm
U3: Z80CPU; DIP-40_W15.24mm
U4, U5, U7: 74LS244; DIP-20_W7.62mm
U6: 74LS245; DIP-20_W7.62mm
U8: 74LS00; DIP-14_W7.62mm
U9: 74LS164; DIP-14_W7.62mm
U10: 74LS153; DIP-16_W7.62mm
U11: 74LS32; DIP-14_W7.62mm
U12: 74LS148; DIP-16_W7.62mm
U13: 74LS373; DIP-20_W7.62mm
U14: CPU CLOCK; DIP-14_W7.62mm
U15: 74LS08; DIP-14_W7.62mm

Connections:
/1WS: J1.3, J2.3, J3.1, J4.1, U9.3 (Q0)
/2WS: J1.5, J2.5, J3.3, J4.3, U9.4 (Q1)
/3WS: J1.7, J2.7, J3.5, J4.5, U9.5 (Q2)
/4WS: J1.9, J2.9, J3.7, J4.7, U9.6 (Q3)
/5WS: J1.11, J2.11, J3.9, J4.9, U9.10 (Q4)
/6WS: J1.13, J2.13, J3.11, J4.11, U9.11 (Q5)
/7WS: J1.15, J2.15, J3.13, J4.13, U9.12 (Q6)
/8WS: J3.15, J4.15, U9.13 (Q7)
/A0: P1.21, U4.18 (1Y0)
/A1: P1.19, U4.16 (1Y1)
/A2: P1.17, U4.14 (1Y2)
/A3: P1.15, U4.12 (1Y3)
/A4: P1.13, U4.3 (2Y0)
/A5: P1.11, U4.5 (2Y1)
/A6: P1.9, U4.7 (2Y2)
/A7: P1.7, U4.9 (2Y3)
/A8: P1.5, U5.18 (1Y0)
/A9: P1.3, U5.16 (1Y1)
/A10: P1.1, U5.14 (1Y2)
/A11: P1.2, U5.12 (1Y3)
/A12: P1.4, U5.3 (2Y0)
/A13: P1.6, U5.5 (2Y1)
/A14: P1.8, U5.7 (2Y2)
/A15: P1.10, U5.9 (2Y3)
/BUSACK: U4.1 (1OE), U4.19 (2OE), U5.1 (1OE), U5.19 (2OE), U6.19 (CE), U7.19 (2OE), U8.8
/CLK: JP3.2, JP4.1 (A), P1.12, RN2.3 (R2)
/D0: P1.28, U6.18 (B0), U13.2 (O0)
/D1: P1.30, U6.17 (B1), U13.5 (O1)
/D2: P1.24, U6.16 (B2), U13.6 (O2)
/D3: P1.16, U6.15 (B3), U13.9 (O3)
/D4: P1.14, U6.14 (B4), U13.12 (O4)
/D5: P1.18, U6.13 (B5), U13.15 (O5)
/D6: P1.20, U6.12 (B6), U13.16 (O6)
/D7: P1.26, U6.11 (B7), U13.19 (O7)
/RDY: U10.7 (Za), U11.2
/READY: U2.13, U11.3
/SPARE0: P1.42, P2.1
/SPARE1: P1.44, P2.2
/SPARE2: P1.46, P2.3
/SPARE3: P1.48, P2.4
/SPARE4: P1.50, P2.5
/SPARE5: P1.49, P2.6
/SPARE6: P1.47, P2.7
/SPARE7: P1.45, P2.8
/SPARE8: P1.43, P2.9
/SPARE9: P1.41, P2.10
/WS-IORD: J3.2, J3.4, J3.6, J3.8, J3.10, J3.12, J3.14, J3.16, U10.5 (I1a)
/WS-IOWR: J4.2, J4.4, J4.6, J4.8, J4.10, J4.12, J4.14, J4.16, U10.3 (I3a)
/WS-MEMRD: J1.2, J1.4, J1.6, J1.8, J1.10, J1.12, J1.14, J1.16, U10.6 (I0a)
/WS-MEMWR: J2.2, J2.4, J2.6, J2.8, J2.10, J2.12, J2.14, J2.16, U10.4 (I2a)
/bD0: U3.14 (D0), U6.2 (A0)
/bD1: U3.15 (D1), U6.3 (A1)
/bD2: U3.12 (D2), U6.4 (A2)
/bD3: U3.8 (D3), U6.5 (A3)
/bD4: U3.7 (D4), U6.6 (A4)
/bD5: U3.9 (D5), U6.7 (A5)
/bD6: U3.10 (D6), U6.8 (A6)
/bD7: U3.13 (D7), U6.9 (A7)
/~BUSACK: P1.35, U7.18 (1Y0)
/~BUSRQ: P1.31, RN2.7 (R6), U1.14 (I6)
/~HALT: P1.36, U7.16 (1Y1)
/~IM2-INT: U2.9, U11.10, U12.14 (GS)
/~INT: D5.1 (K), P1.32, RN2.5 (R4), U1.10 (I4), U2.8
/~INTA: U11.6, U11.9, U15.1
/~IORQ: P1.40, U7.3 (2Y0)
/~IRQ0: P3.8, RN1.9 (R8), U12.10 (IO)
/~IRQ1: P3.7, RN1.8 (R7), U12.11 (I1)
/~IRQ2: P3.6, RN1.7 (R6), U12.12 (I2)
/~IRQ3: P3.5, RN1.6 (R5), U12.13 (I3)
/~IRQ4: P3.4, RN1.5 (R4), U12.1 (I4)
/~IRQ5: P3.3, RN1.4 (R3), U12.2 (I5)
/~IRQ6: P3.2, RN1.3 (R2), U12.3 (I6)
/~IRQ7: P3.1, RN1.2 (R1), U12.4 (I7)
/~M1: P1.27, U7.12 (1Y3)
/~MR: U8.3, U8.5, U9.9 (~MR)
/~MREQ: P1.38, U7.5 (2Y1)
/~NMI: P1.34, RN2.4 (R3), U1.6 (I3), U2.5
/~RD: P1.39, U7.9 (2Y3)
/~RESET: P1.29, RN2.2 (R1), U1.2 (I1), U2.10
/~RFSH: P1.25, U7.14 (1Y2)
/~WAIT: JP2.2, P1.33, RN2.6 (R5), U1.12 (I5)
/~WR: P1.37, U7.7 (2Y2)
/~bIORQ: RN2.8 (R7), U3.20 (~IORQ~), U7.17 (2A0), U8.2, U11.5
/~bM1: U3.27 (~M1~), U7.8 (1A3), U11.4, U13.11 (LE)
GND: C1.2, C2.2, C3.2, C4.2, C5.2, C6.2, C7.2, C8.2, C9.2, C10.2, C11.2, C12.2, C13.2, C14.2, C15.2, C16.2, C17.2, C18.2, D1.1 (K), H1.1, H2.1, JP1.2, P1.23, SW1.2, U1.1 (OEa), U1.8 (GND), U1.15 (OEb), U2.7 (GND), U3.29 (GND), U4.10 (GND), U5.10 (GND), U6.10 (GND), U7.1 (1OE), U7.10 (GND), U8.7 (GND), U9.7 (GND), U10.1 (Ea), U10.8 (GND), U11.7 (GND), U12.5 (EI), U12.8 (GND), U13.3 (D0), U13.10 (GND), U13.13 (D4), U13.14 (D5), U13.17 (D6), U13.18 (D7), U14.4, U14.7, U15.7 (GND)
unnamed: C10.1, D2.2 (A), R6.2, R7.2, U2.11
unnamed: D1.2 (A), R5.2
unnamed: D3.1 (K), JP2.1, U2.12
unnamed: D3.2 (A), R3.1
unnamed: D4.1 (K), U2.6
unnamed: D4.2 (A), R1.1
unnamed: D5.2 (A), R2.1
unnamed: JP1.1, R7.1, SW1.1
unnamed: JP3.1, U1.5 (O2a), U3.6 (~CLK~), U9.8 (CP)
unnamed: JP4.2 (C), U1.4 (I2)
unnamed: JP4.3 (B), U14.8, U14.11
unnamed: JP5.1, U13.1 (OE)
unnamed: JP5.2, U11.8
unnamed: U1.3 (O1a), U3.26 (~RESET~)
unnamed: U1.7 (O3a), U3.17 (~NMI~)
unnamed: U1.9 (O4a), U3.16 (~INT~)
unnamed: U1.11 (O5b), U3.24 (~WAIT~)
unnamed: U1.13 (O6b), U3.25 (~BUSRQ~)
unnamed: U3.1 (A11), U5.8 (1A3)
unnamed: U3.2 (A12), U5.17 (2A0)
unnamed: U3.3 (A13), U5.15 (2A1)
unnamed: U3.4 (A14), U5.13 (2A2)
unnamed: U3.5 (A15), U5.11 (2A3)
unnamed: U3.18 (~HALT~), U7.4 (1A1)
unnamed: U3.22 (~WR~), U7.13 (2A2)
unnamed: U3.23 (~BUSACK~), U7.2 (1A0), U8.9, U8.10
unnamed: U3.28 (~RFSH~), U7.6 (1A2), U8.4
unnamed: U3.30 (A0), U4.2 (1A0)
unnamed: U3.31 (A1), U4.4 (1A1)
unnamed: U3.32 (A2), U4.6 (1A2)
unnamed: U3.33 (A3), U4.8 (1A3)
unnamed: U3.34 (A4), U4.17 (2A0)
unnamed: U3.35 (A5), U4.15 (2A1)
unnamed: U3.36 (A6), U4.13 (2A2)
unnamed: U3.37 (A7), U4.11 (2A3)
unnamed: U3.38 (A8), U5.2 (1A0)
unnamed: U3.39 (A9), U5.4 (1A1)
unnamed: U3.40 (A10), U5.6 (1A2)
unnamed: U3.21 (~RD~), U7.11 (2A3), U10.2 (S1), U15.2
unnamed: U3.19 (~MREQ~), U7.15 (2A1), U8.1, U10.14 (S0)
unnamed: U8.6, U11.1
unnamed: U12.6 (S2), U13.8 (D3)
unnamed: U12.7 (S1), U13.7 (D2)
unnamed: U12.9 (S0), U13.4 (D1)
unnamed: U6.1 (A->B), U15.3
VCC: C1.1, C2.1, C3.1, C4.1, C5.1, C6.1, C7.1, C8.1, C9.1, C11.1, C12.1, C13.1, C14.1, C15.1, C16.1, C17.1, C18.1, D2.1 (K), J1.1, J2.1, P1.22, R1.2, R2.2, R3.2, R5.1, R6.1, RN1.1 (common), RN2.1 (common), U1.16 (VCC), U2.14 (VCC), U3.11 (VCC), U4.20 (VCC), U5.20 (VCC), U6.20 (VCC), U7.20 (VCC), U8.14 (VCC), U9.1 (DSA), U9.2 (DSB), U9.14 (VCC), U10.16 (VCC), U11.14 (VCC), U12.16 (VCC), U13.20 (VCC), U14.1, U14.14, U15.14 (VCC)

Notes on the sheet:
Note: Bus connector is mirror image of Z80 CPU pin out to mate to backplane whose connectors reflect Z80 CPU pin out.
Reset Button Circuit
Spare Gates
Wait State Generator Circuit
Tri-state address, data, & control bus during DMA
NOTE: ALTERNATE CPU CLOCK JP4 NORMALLY 1-2 (CLOCK FROM BUS) 2-3 ALLOWS LOCAL CPU OSCILLATOR JP3 CONNECTS ALTERNATE CPU CLOCK TO Z80 BUS BACKPLANE
NOTE: IF JP4 1-2 SELECTED JP3 MUST BE OPEN
Interrupt Mode 2 (IM2) Circuit

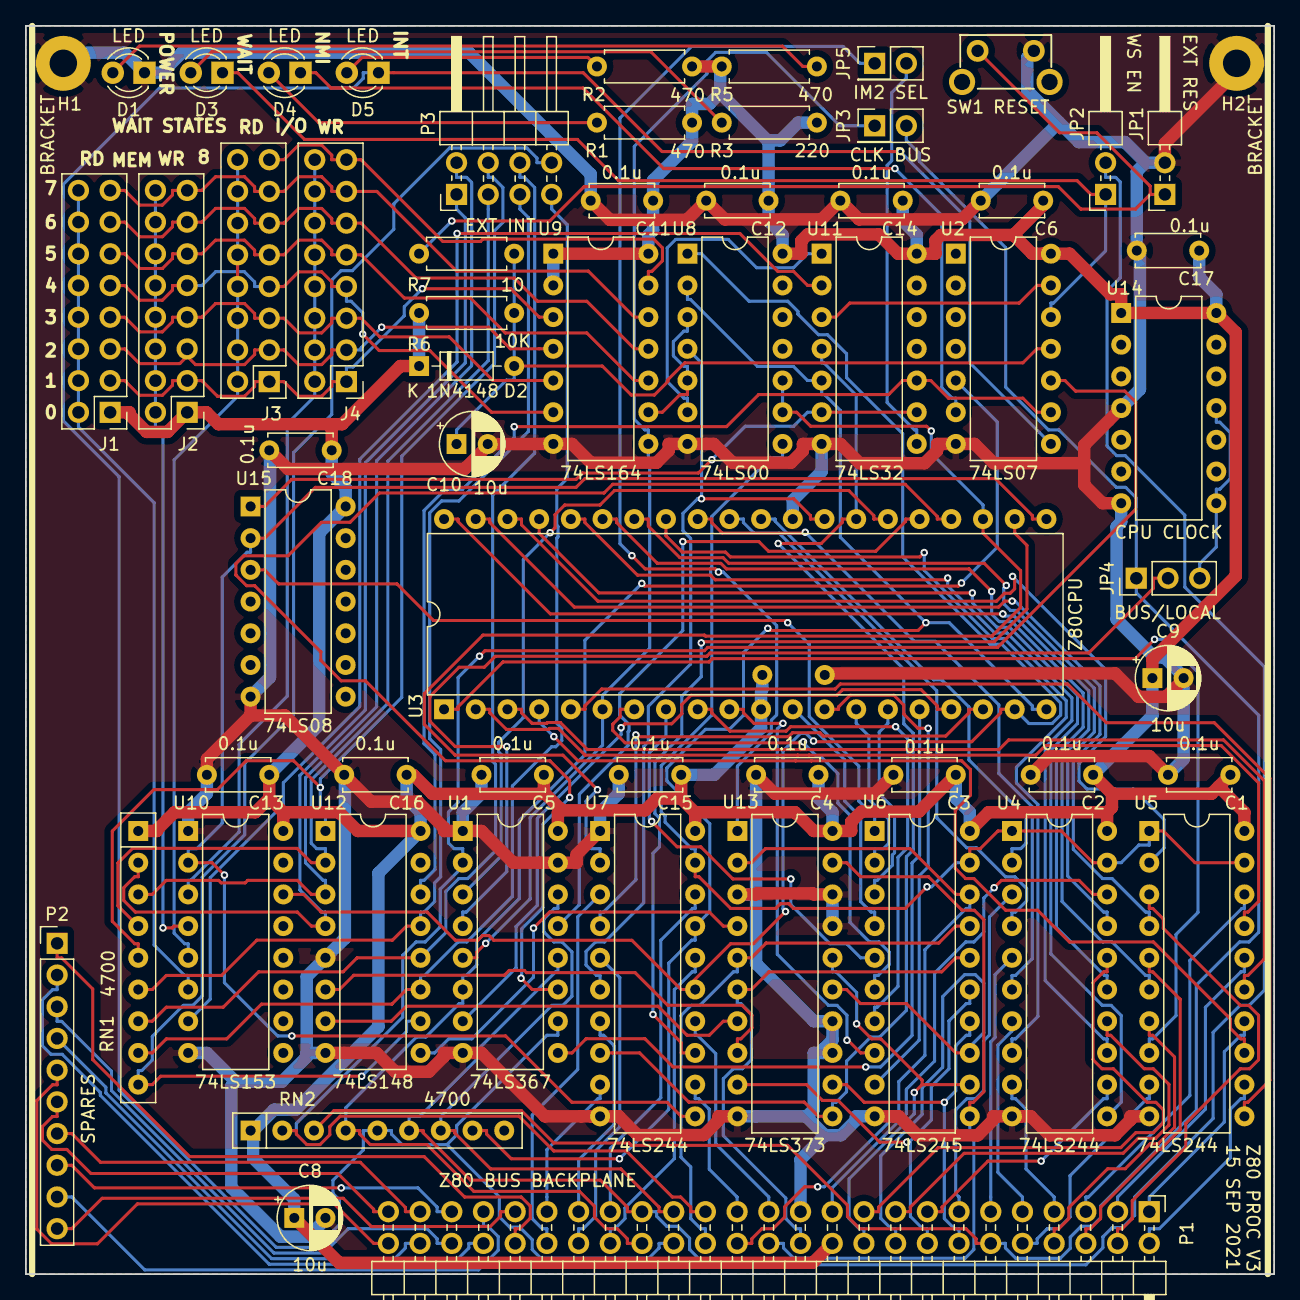
[picture p231: board Z80PROC3/Z80PROC3.kicad_pcb from above]

Board: 2 copper layers, 100.0 x 100.0 mm, 61 parts (1 on the bottom side), 131 nets.
