lynchaj/nhyodyne/Z80FDC1/Z80FDC.kicad_pcb

## KiCad design Z80FDC1/Z80FDC.kicad_pcb (2021-11-30)

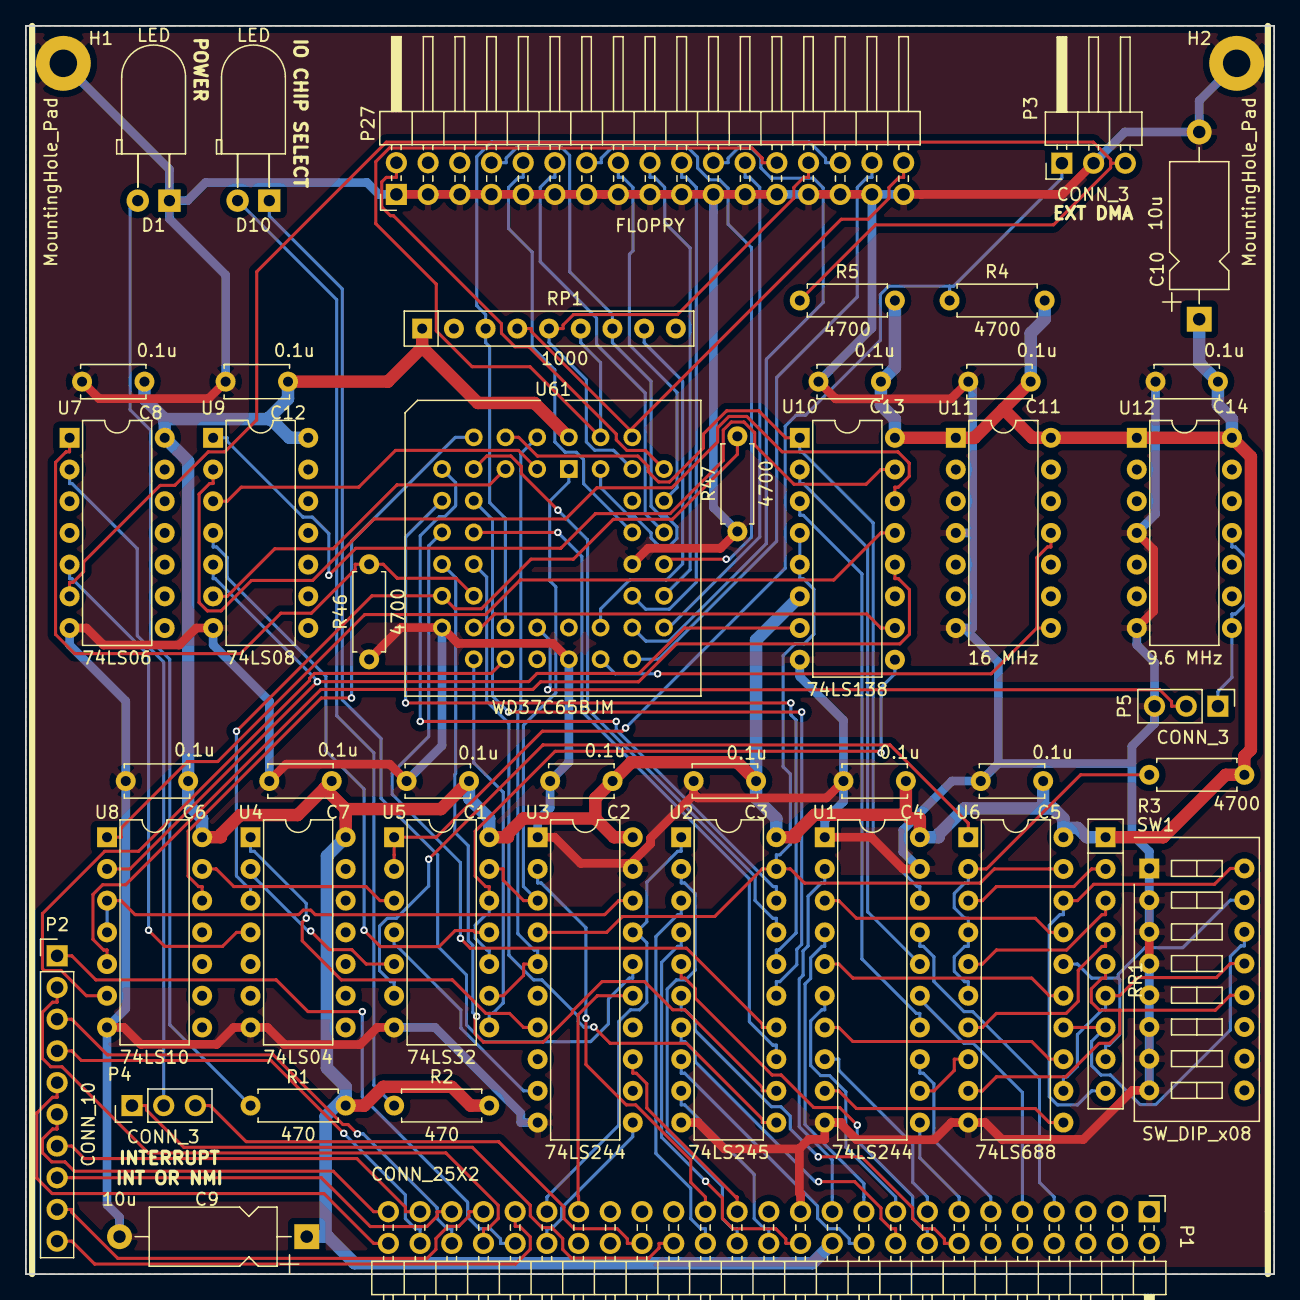
[picture p232: board Z80FDC.kicad_pcb from above]

Board: 2 copper layers, 100.0 x 100.0 mm, 47 parts (0 on the bottom side), 110 nets.

Parts:
C1, C2, C3, C4, C5, C6, C7, C8, C11, C12, C13, C14: 0.1u; C_Disc_D5.0mm_W2.5mm_P5.00mm
C9, C10: 10u; CP_Axial_L10.0mm_D4.5mm_P15.00mm_Horizontal
D1, D10: LED; LED_D5.0mm_Horizontal_O3.81mm_Z3.0mm
H1, H2: MountingHole_Pad; MountingHole_2.2mm_M2_Pad
P1: CONN_25X2; Pin_Header_Angled_2x25_Pitch2.54mm
P2: CONN_10; Pin_Header_Straight_1x10_Pitch2.54mm
P3: CONN_3; PinHeader_1x03_P2.54mm_Horizontal
P4, P5: CONN_3; PinHeader_1x03_P2.54mm_Vertical
P27: FLOPPY; PinHeader_2x17_P2.54mm_Horizontal
R1, R2: 470; R_Axial_DIN0207_L6.3mm_D2.5mm_P7.62mm_Horizontal
R3, R4, R5, R46, R47: 4700; R_Axial_DIN0207_L6.3mm_D2.5mm_P7.62mm_Horizontal
RP1: 1000; R_Array_SIP9
RR1: 10000; R_Array_SIP9
SW1: SW_DIP_x08; SW_DIP_x8_W7.62mm_Slide
U1, U3: 74LS244; DIP-20_W7.62mm
U2: 74LS245; DIP-20_W7.62mm
U4: 74LS04; DIP-14_W7.62mm
U5: 74LS32; DIP-14_W7.62mm
U6: 74LS688; DIP-20_W7.62mm
U7: 74LS06; DIP-14_W7.62mm
U8: 74LS10; DIP-14_W7.62mm
U9: 74LS08; DIP-14_W7.62mm
U10: 74LS138; DIP-16_W7.62mm
U11: 16 MHz; DIP-14_W7.62mm
U12: 9.6 MHz; DIP-14_W7.62mm
U61: WD37C65BJM; PLCC-44_THT-Socket

Connections:
/688SEL#: U5.6, U6.1
/A0: P1.21, U1.2
/A1: P1.19, U1.4
/A2: P1.17, U1.6
/A3: P1.15, U1.8
/A4: P1.13, U1.11
/A5: P1.11, U1.13
/A6: P1.9, U1.15
/A7: P1.7, U1.17
/CS_FDC#: U2.19, U3.4, U6.19, U10.4, U10.5
/D0: P1.28, U2.2
/D1: P1.30, U2.3
/D2: P1.24, U2.4
/D3: P1.16, U2.5
/D4: P1.14, U2.6
/D5: P1.18, U2.7
/D6: P1.20, U2.8
/D7: P1.26, U2.9
/DACK#: U5.11, U9.4
/DACK_AND_TC#: U8.2, U9.5, U10.7
/FDC_DMA: R47.2, U4.3, U61.15
/INT#: P1.32, P4.1
/INT_FDC: R46.2, U7.1, U61.16
/IORQ#: P1.40, U3.11
/LDCR#: U10.10, U61.19
/LDOR#: U5.8, U61.18
/M1#: P1.27, U3.13
/MSR-DATA#: U9.3, U61.3
/NMI#: P1.34, P4.3
/PULSE#: P3.1, R4.1, U5.1, U5.2
/RD#: P1.39, U2.1, U3.17
/RDY: P3.3, R5.1, U7.6
/RESET#: P1.29, U3.2
/SPARE0: P1.42, P2.1
/SPARE1: P1.44, P2.2
/SPARE2: P1.46, P2.3
/SPARE3: P1.48, P2.4
/SPARE4: P1.50, P2.5
/SPARE5: P1.49, P2.6
/SPARE6: P1.47, P2.7
/SPARE7: P1.45, P2.8
/SPARE8: P1.43, P2.9
/SPARE9: P1.41, P2.10
/TC#: U8.1, U10.13
/TEND#: U5.3, U8.13
/USER_RESET#: U8.5, U10.12
/WR#: P1.37, U3.15
/bA0: U1.18, U10.1, U61.4
/bA1: U1.16, U10.2
/bA2: U1.14, U10.3
/bA3: U1.12, U6.8
/bA4: U1.9, U6.11
/bA5: U1.7, U6.13
/bA6: U1.5, U6.15
/bA7: U1.3, U6.17
/bD0: U2.18, U61.7
/bD1: U2.17, U61.8
/bD2: U2.16, U61.9
/bD3: U2.15, U61.10
/bD4: U2.14, U61.11
/bD5: U2.13, U61.12
/bD6: U2.12, U61.13
/bD7: U2.11, U61.14
/bIORQ#: U3.9, U5.4
/bM1#: U3.7, U4.1
/bRD#: U3.3, U5.13, U61.1
/bRESET: U8.6, U61.20
/bRESET#: U3.18, U8.3, U8.4
/bWR#: U3.5, U5.9, U61.2
GND: C1.2, C2.2, C3.2, C4.2, C5.2, C6.2, C7.2, C8.2, C9.2, C10.2, C11.2, C12.2, C13.2, C14.2, D1.1, H1.1, H2.1, P1.23, P3.2, P5.3, P27.1, P27.3, P27.5, P27.7, P27.9, P27.11, P27.13, P27.15, P27.17, P27.19, P27.21, P27.23, P27.25, P27.27, P27.29, P27.31, P27.33, R46.1, R47.1, SW1.1, SW1.2, SW1.3, SW1.4, SW1.5, SW1.6, SW1.7, SW1.8, U1.1, U1.10, U1.19, U2.10, U3.1, U3.10, U3.19, U4.7, U5.7, U6.10, U7.7, U8.7, U9.7, U10.8, U11.4, U11.7, U12.4, U12.7, U61.17, U61.24, U61.34
unnamed: D1.2, R1.1
unnamed: D10.1, U3.16
unnamed: D10.2, R2.1
unnamed: P4.2, U7.2
unnamed: P5.1, U12.8, U12.11
unnamed: P5.2, U61.23
unnamed: P27.2, U61.39
unnamed: P27.8, RP1.7, U61.43
unnamed: P27.10, U61.36
unnamed: P27.12, U61.35
unnamed: P27.14, U61.33
unnamed: P27.16, U61.37
unnamed: P27.18, U61.31
unnamed: P27.20, U61.32
unnamed: P27.22, U61.30
unnamed: P27.24, U61.29
unnamed: P27.26, RP1.6, U61.42
unnamed: P27.28, RP1.5, U61.41
unnamed: P27.30, RP1.3, U61.21
unnamed: P27.32, U61.28
unnamed: P27.34, RP1.4, U61.40
unnamed: R3.1, U6.2, U6.4, U6.6
unnamed: RP1.8, U61.27
unnamed: RR1.2, U6.3
unnamed: RR1.3, U6.5
unnamed: RR1.4, U6.7
unnamed: RR1.5, SW1.12, U6.9
unnamed: RR1.6, SW1.13, U6.12
unnamed: RR1.7, SW1.14, U6.14
unnamed: RR1.8, SW1.15, U6.16
unnamed: RR1.9, SW1.16, U6.18
unnamed: U4.2, U5.5
unnamed: U4.4, U7.5
unnamed: U5.10, U5.12, U10.9
unnamed: U9.2, U10.14
unnamed: U9.1, U10.15
unnamed: U11.8, U11.11, U61.26
unnamed: U9.6, U61.5
unnamed: U8.12, U61.6
VCC: C1.1, C2.1, C3.1, C4.1, C5.1, C6.1, C7.1, C8.1, C9.1, C10.1, C11.1, C12.1, C13.1, C14.1, P1.22, R1.2, R2.2, R3.2, R4.2, R5.2, RP1.1, RR1.1, U1.20, U2.20, U3.20, U4.14, U5.14, U6.20, U7.14, U8.14, U9.14, U10.6, U10.16, U11.1, U11.14, U12.1, U12.14, U61.44
