lynchaj/nhyodyne/Z80CLOCK2/Z80CLOCK2.kicad_pcb

## KiCad design Z80CLOCK2/Z80CLOCK2.kicad_pcb (2021-11-30)

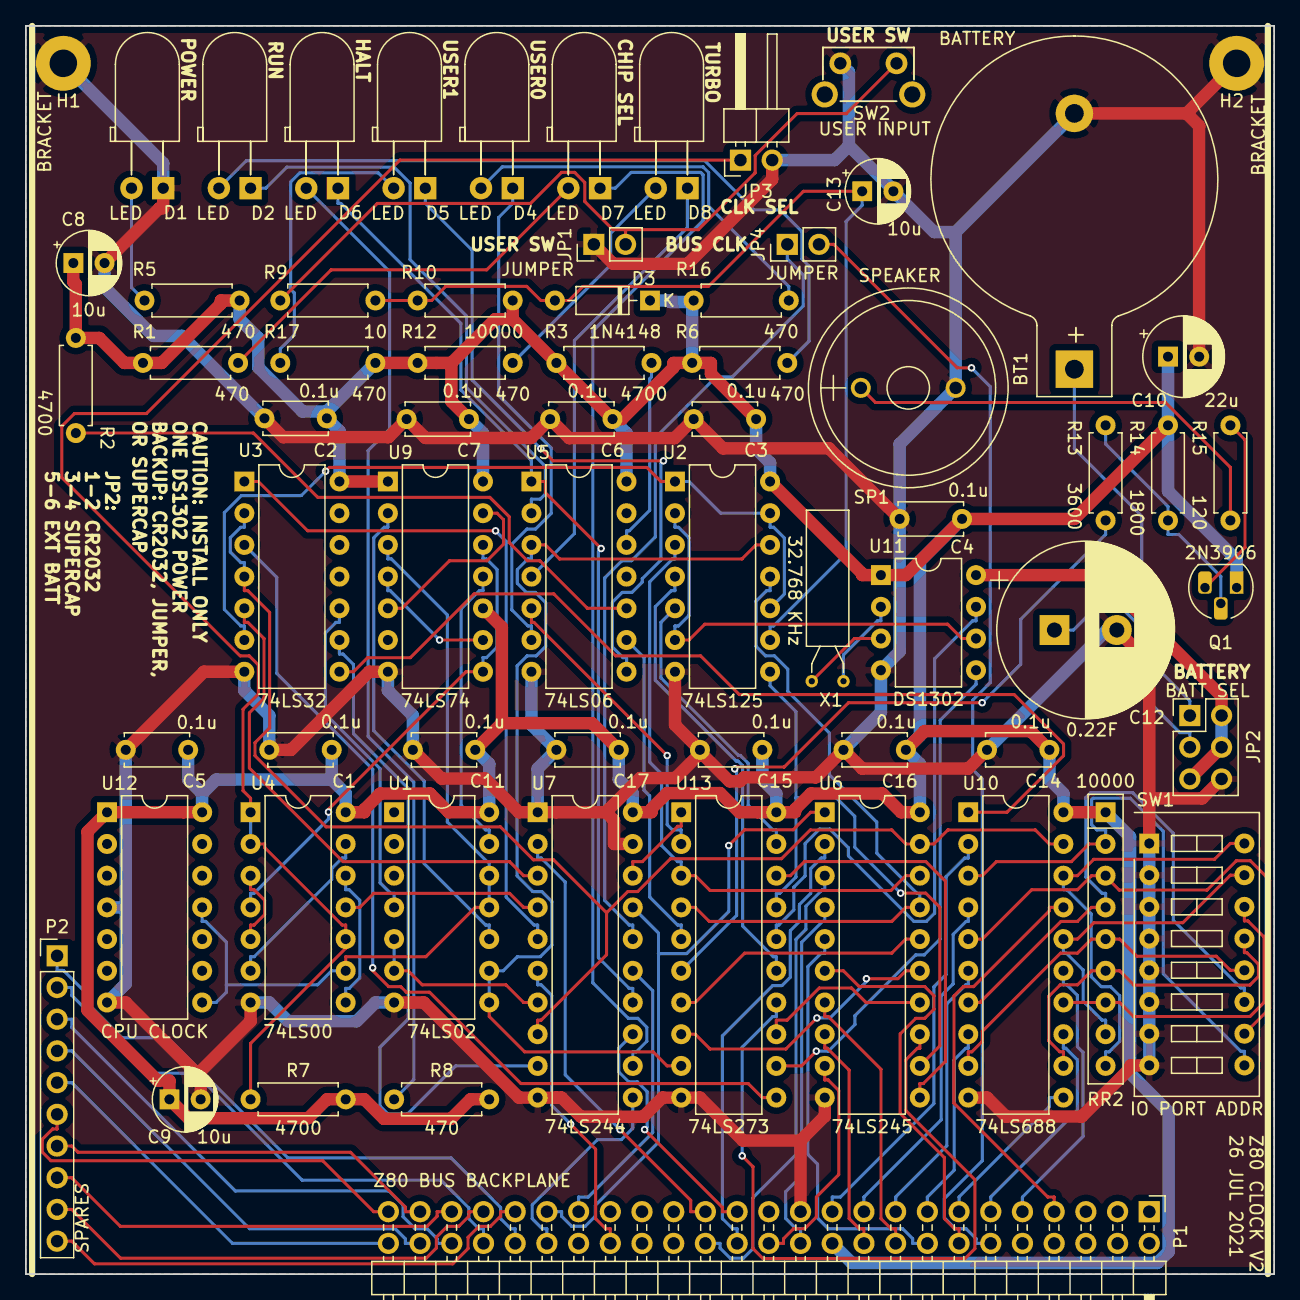
[picture p233: board Z80CLOCK2.kicad_pcb from above]

Board: 2 copper layers, 100.0 x 100.0 mm, 67 parts (0 on the bottom side), 107 nets.

Parts:
BT1: BATTERY; BatteryHolder_Keystone_103_1x20mm
C1, C2, C3, C4, C5, C6, C7, C11, C14, C15, C16, C17: 0.1u; C_Disc_D5.0mm_W2.5mm_P5.00mm
C8, C9, C13: 10u; CP_Radial_D5.0mm_P2.50mm
C10: 22u; CP_Radial_D6.3mm_P2.50mm
C12: 0.22F; CP_Radial_D14.0mm_P5.00mm
D1, D2, D4, D5, D6, D7, D8: LED; LED_D5.0mm_Horizontal_O3.81mm_Z3.0mm
D3: 1N4148; D_DO-35_SOD27_P7.62mm_Horizontal
H1, H2: BRACKET; MountingHole_2.2mm_M2_Pad
JP1, JP4: JUMPER; PinHeader_1x02_P2.54mm_Vertical
JP2: BATT SEL; PinHeader_2x03_P2.54mm_Vertical
JP3: JUMPER; PinHeader_1x02_P2.54mm_Horizontal
P1: Z80 BUS BACKPLANE; PinHeader_2x25_P2.54mm_Horizontal
P2: SPARES; PinHeader_1x10_P2.54mm_Vertical
Q1: 2N3906; TO-92_HandSolder
R1, R5, R6, R8, R12, R16, R17: 470; R_Axial_DIN0207_L6.3mm_D2.5mm_P7.62mm_Horizontal
R2, R3, R7: 4700; R_Axial_DIN0207_L6.3mm_D2.5mm_P7.62mm_Horizontal
R9: 10; R_Axial_DIN0207_L6.3mm_D2.5mm_P7.62mm_Horizontal
R10: 10000; R_Axial_DIN0207_L6.3mm_D2.5mm_P7.62mm_Horizontal
R13: 3600; R_Axial_DIN0207_L6.3mm_D2.5mm_P7.62mm_Horizontal
R14: 1800; R_Axial_DIN0207_L6.3mm_D2.5mm_P7.62mm_Horizontal
R15: 120; R_Axial_DIN0207_L6.3mm_D2.5mm_P7.62mm_Horizontal
RR2: 10000; R_Array_SIP9
SP1: SPEAKER; MagneticBuzzer_StarMicronics_HMB-06_HMB-12
SW1: IO PORT ADDR; SW_DIP_x8_W7.62mm_Slide
SW2: USER INPUT; SW_Tactile_SPST_Angled
U1: 74LS02; DIP-14_W7.62mm
U2: 74LS125; DIP-14_W7.62mm
U3: 74LS32; DIP-14_W7.62mm
U4: 74LS00; DIP-14_W7.62mm
U5: 74LS06; DIP-14_W7.62mm
U6: 74LS245; DIP-20_W7.62mm
U7: 74LS244; DIP-20_W7.62mm
U9: 74LS74; DIP-14_W7.62mm
U10: 74LS688; DIP-20_W7.62mm
U11: DS1302; DIP-8_W7.62mm
U12: CPU CLOCK; DIP-14_W7.62mm
U13: 74LS273; DIP-20_W7.62mm
X1: 32.768 KHz; Crystal_AT310_d3.0mm_l10.0mm_Horizontal

Connections:
/688SEL#: U3.8, U10.1
//CS_RTC: U3.2, U3.4, U6.19, U7.8, U10.19
//HALT: P1.36, U7.6
//IORQ: P1.40, U7.11
//M1: P1.27, U7.13
//RD: P1.39, U6.1, U7.17
//RESET: P1.29, U7.2
//RTC_RD: U2.1, U2.10, U2.13, U3.6
//RTC_WR: U3.3, U13.11
//WR: P1.37, U7.15
/A0: P1.21, U10.2
/A1: P1.19, U10.4
/A2: P1.17, U10.6
/A3: P1.15, U10.8
/A4: P1.13, U10.11
/A5: P1.11, U10.13
/A6: P1.9, U10.15
/A7: P1.7, U10.17
/CLK: JP4.2, P1.12
/CLKSEL: U1.8, U1.9, U2.12, U5.3, U13.9
/CLKSEL#: U1.10, U9.2
/D0: P1.28, U6.2
/D1: P1.30, U6.3
/D2: P1.24, U6.4
/D3: P1.16, U6.5
/D4: P1.14, U6.6
/D5: P1.18, U6.7
/D6: P1.20, U6.8
/D7: P1.26, U6.9
/RTC_CLK_IN: U11.7, U13.16
/RTC_DAT_IN: U2.5, U13.19
/RTC_DQ: U2.2, U2.6, U11.6
/RTC_RST_IN: U11.5, U13.12
/RTC_WR_EN: U2.4, U13.15
/SPARE0: P1.42, P2.1
/SPARE1: P1.44, P2.2
/SPARE2: P1.46, P2.3
/SPARE3: P1.48, P2.4
/SPARE4: P1.50, P2.5
/SPARE5: P1.49, P2.6
/SPARE6: P1.47, P2.7
/SPARE7: P1.45, P2.8
/SPARE8: P1.43, P2.9
/SPARE9: P1.41, P2.10
/SPEAKER: R13.2, U13.6
/USERLED0: U5.5, U13.2
/USERLED1: U5.9, U13.5
/VBAT: JP2.2, JP2.4, JP2.5, U11.8
/b/D0: U2.3, U6.18, U13.3
/b/D1: U2.11, U6.17, U13.4
/b/D6: U2.8, U6.12, U13.17
/b/IORQ: U3.9, U7.9
/b/M1: U1.5, U1.6, U7.7
/b/RD: U3.5, U7.3
/b/WR: U3.1, U7.5
/bCLK: U4.11, U7.4
GND: BT1.2, C1.2, C2.2, C3.2, C4.2, C5.2, C6.2, C7.2, C8.2, C9.2, C10.2, C11.2, C12.2, C13.2, C14.2, C15.2, C16.2, C17.2, D1.1, H1.1, H2.1, JP1.1, JP2.6, JP3.2, P1.23, SP1.1, SW1.1, SW1.2, SW1.3, SW1.4, SW1.5, SW1.6, SW1.7, SW1.8, SW2.1, U1.7, U2.7, U3.7, U4.7, U5.7, U6.10, U7.1, U7.10, U7.19, U9.7, U10.10, U11.4, U12.4, U12.7, U13.10
unnamed: BT1.1, JP2.1
unnamed: C12.1, JP2.3
unnamed: C13.1, D3.2, R9.1, R10.2, U2.9
unnamed: D1.2, R5.1
unnamed: D2.1, U5.2
unnamed: D2.2, R6.1
unnamed: D4.1, U5.6
unnamed: D4.2, R16.2
unnamed: D5.1, U5.8
unnamed: D5.2, R17.2
unnamed: D6.1, U5.1, U7.14
unnamed: D6.2, R8.1
unnamed: D7.1, U7.12
unnamed: D7.2, R1.1
unnamed: D8.1, U5.4
unnamed: D8.2, R12.1
unnamed: JP1.2, R9.2, SW2.2
unnamed: JP3.1, R7.1, U4.1, U4.2, U4.10
unnamed: JP4.1, U7.16
unnamed: Q1.2, R13.1, R14.2
unnamed: Q1.3, R15.1
unnamed: R2.2, U5.10
unnamed: R3.2, U5.12
unnamed: R15.2, SP1.2
unnamed: RR2.2, SW1.9, U10.3
unnamed: RR2.3, SW1.10, U10.5
unnamed: RR2.4, SW1.11, U10.7
unnamed: RR2.5, SW1.12, U10.9
unnamed: RR2.6, SW1.13, U10.12
unnamed: RR2.7, SW1.14, U10.14
unnamed: RR2.8, SW1.15, U10.16
unnamed: RR2.9, SW1.16, U10.18
unnamed: U1.4, U3.10
unnamed: U1.11, U1.12, U4.9, U9.3, U12.8, U12.11
unnamed: U1.13, U9.11
unnamed: U4.3, U4.5
unnamed: U4.4, U9.8, U9.12
unnamed: U4.8, U4.12
unnamed: U4.6, U4.13
unnamed: U9.4, U9.9
unnamed: U9.5, U9.13
unnamed: U11.2, X1.1
unnamed: U11.3, X1.2
unnamed: U7.18, U13.1
unnamed: U6.16, U13.7
unnamed: U6.15, U13.8
unnamed: U6.14, U13.13
unnamed: U6.13, U13.14
unnamed: U6.11, U13.18
VCC: C1.1, C2.1, C3.1, C4.1, C5.1, C6.1, C7.1, C8.1, C9.1, C10.1, C11.1, C14.1, C15.1, C16.1, C17.1, D3.1, P1.22, Q1.1, R1.2, R2.1, R3.1, R5.2, R6.2, R7.2, R8.2, R10.1, R12.2, R14.1, R16.1, R17.1, RR2.1, U1.14, U2.14, U3.14, U4.14, U5.14, U6.20, U7.20, U9.1, U9.10, U9.14, U10.20, U11.1, U12.1, U12.14, U13.20
