lynchaj/nhyodyne/Z80BCKPLN2/Z80BCKPLN2.kicad_pcb

## KiCad design Z80BCKPLN2/Z80BCKPLN2.kicad_pcb (2021-11-30)

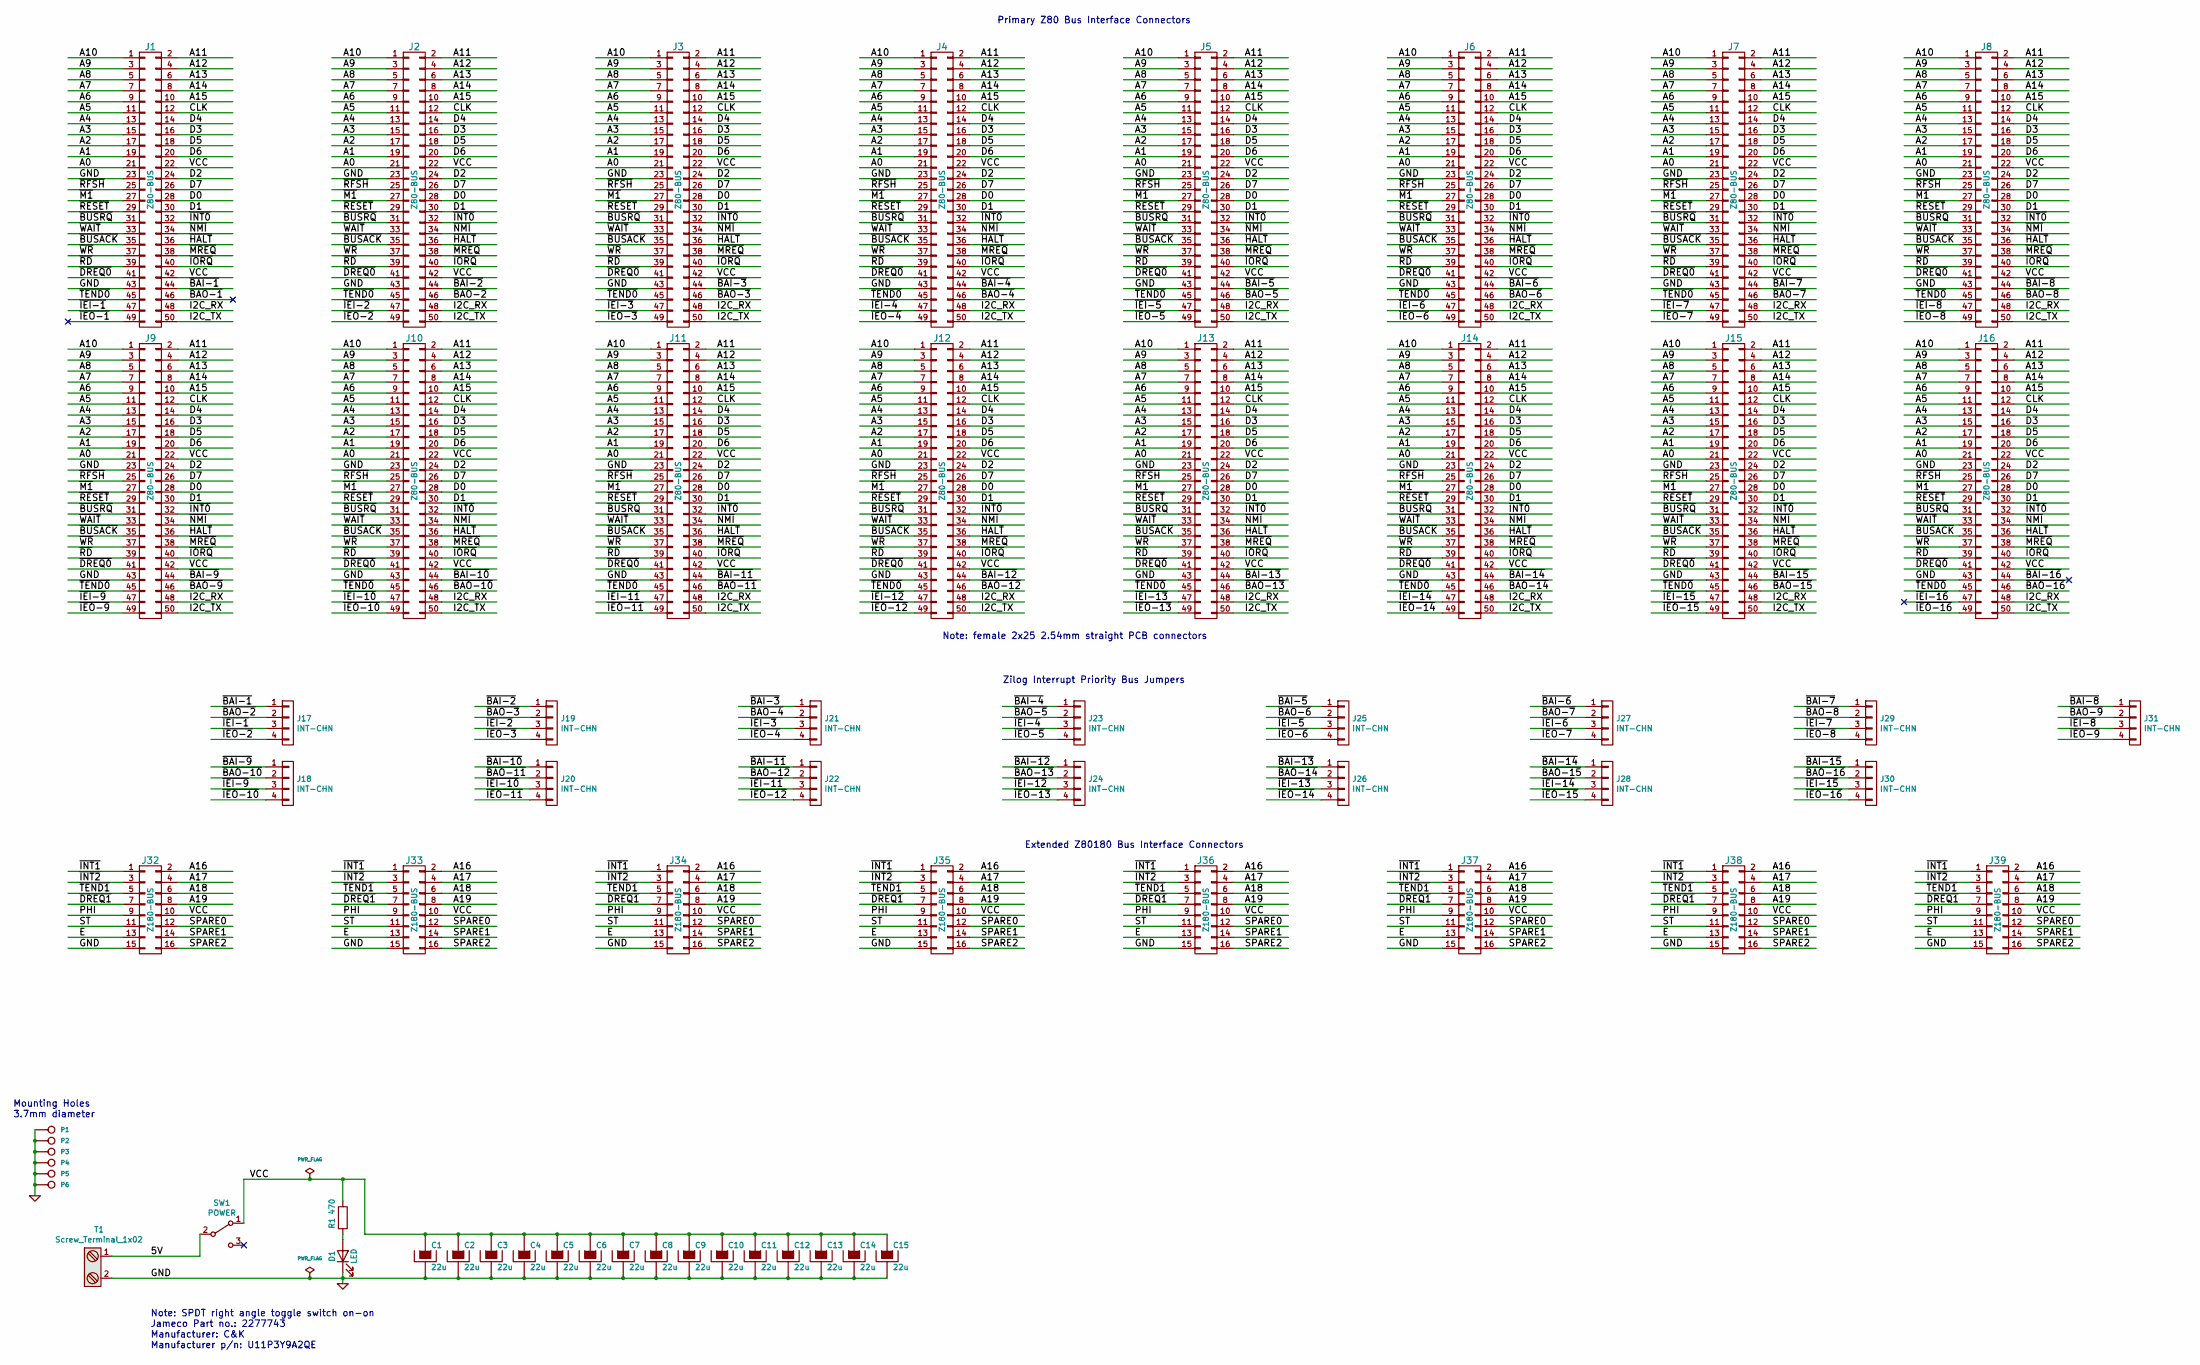
[picture p234: schematic Z80BCKPLN2.sch]

Parts:
C1, C2, C3, C4, C5, C6, C7, C8, C9, C10, C11, C12, C13, C14, C15: 22u; CP_Radial_D5.0mm_P2.50mm
D1: LED; LED_D3.0mm
J1, J2, J3, J4, J5, J6, J7, J8, J9, J10, J11, J12, J13, J14, J15, J16: Z80-BUS; PinSocket_2x25_P2.54mm_Vertical
J17, J18, J19, J20, J21, J22, J23, J24, J25, J26, J27, J28, J29, J30, J31: INT-CHN; PinHeader_1x04_P2.54mm_Vertical
J32, J33, J34, J35, J36, J37, J38, J39: Z180-BUS; PinSocket_2x08_P2.54mm_Vertical
P1, P2, P3, P4, P5, P6: CONN_1; MountingHole_3.2mm_M3_Pad
R1: 470; R_Axial_DIN0207_L6.3mm_D2.5mm_P7.62mm_Horizontal
SW1: POWER; SW_SPDT
T1: Screw_Terminal_1x02; TerminalBlock_MetzConnect_Type101_RT01602HBWC_1x02_P5.08mm_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

Connections:
/5V: SW1.2 (B), T1.1
/A0: J1.21, J2.21, J3.21, J4.21, J5.21, J6.21, J7.21, J8.21, J9.21, J10.21, J11.21, J12.21, J13.21, J14.21, J15.21, J16.21
/A1: J1.19, J2.19, J3.19, J4.19, J5.19, J6.19, J7.19, J8.19, J9.19, J10.19, J11.19, J12.19, J13.19, J14.19, J15.19, J16.19
/A2: J1.17, J2.17, J3.17, J4.17, J5.17, J6.17, J7.17, J8.17, J9.17, J10.17, J11.17, J12.17, J13.17, J14.17, J15.17, J16.17
/A3: J1.15, J2.15, J3.15, J4.15, J5.15, J6.15, J7.15, J8.15, J9.15, J10.15, J11.15, J12.15, J13.15, J14.15, J15.15, J16.15
/A4: J1.13, J2.13, J3.13, J4.13, J5.13, J6.13, J7.13, J8.13, J9.13, J10.13, J11.13, J12.13, J13.13, J14.13, J15.13, J16.13
/A5: J1.11, J2.11, J3.11, J4.11, J5.11, J6.11, J7.11, J8.11, J9.11, J10.11, J11.11, J12.11, J13.11, J14.11, J15.11, J16.11
/A6: J1.9, J2.9, J3.9, J4.9, J5.9, J6.9, J7.9, J8.9, J9.9, J10.9, J11.9, J12.9, J13.9, J14.9, J15.9, J16.9
/A7: J1.7, J2.7, J3.7, J4.7, J5.7, J6.7, J7.7, J8.7, J9.7, J10.7, J11.7, J12.7, J13.7, J14.7, J15.7, J16.7
/A8: J1.5, J2.5, J3.5, J4.5, J5.5, J6.5, J7.5, J8.5, J9.5, J10.5, J11.5, J12.5, J13.5, J14.5, J15.5, J16.5
/A9: J1.3, J2.3, J3.3, J4.3, J5.3, J6.3, J7.3, J8.3, J9.3, J10.3, J11.3, J12.3, J13.3, J14.3, J15.3, J16.3
/A10: J1.1, J2.1, J3.1, J4.1, J5.1, J6.1, J7.1, J8.1, J9.1, J10.1, J11.1, J12.1, J13.1, J14.1, J15.1, J16.1
/A11: J1.2, J2.2, J3.2, J4.2, J5.2, J6.2, J7.2, J8.2, J9.2, J10.2, J11.2, J12.2, J13.2, J14.2, J15.2, J16.2
/A12: J1.4, J2.4, J3.4, J4.4, J5.4, J6.4, J7.4, J8.4, J9.4, J10.4, J11.4, J12.4, J13.4, J14.4, J15.4, J16.4
/A13: J1.6, J2.6, J3.6, J4.6, J5.6, J6.6, J7.6, J8.6, J9.6, J10.6, J11.6, J12.6, J13.6, J14.6, J15.6, J16.6
/A14: J1.8, J2.8, J3.8, J4.8, J5.8, J6.8, J7.8, J8.8, J9.8, J10.8, J11.8, J12.8, J13.8, J14.8, J15.8, J16.8
/A15: J1.10, J2.10, J3.10, J4.10, J5.10, J6.10, J7.10, J8.10, J9.10, J10.10, J11.10, J12.10, J13.10, J14.10, J15.10, J16.10
/A16: J32.2, J33.2, J34.2, J35.2, J36.2, J37.2, J38.2, J39.2
/A17: J32.4, J33.4, J34.4, J35.4, J36.4, J37.4, J38.4, J39.4
/A18: J32.6, J33.6, J34.6, J35.6, J36.6, J37.6, J38.6, J39.6
/A19: J32.8, J33.8, J34.8, J35.8, J36.8, J37.8, J38.8, J39.8
/CLK: J1.12, J2.12, J3.12, J4.12, J5.12, J6.12, J7.12, J8.12, J9.12, J10.12, J11.12, J12.12, J13.12, J14.12, J15.12, J16.12
/D0: J1.28, J2.28, J3.28, J4.28, J5.28, J6.28, J7.28, J8.28, J9.28, J10.28, J11.28, J12.28, J13.28, J14.28, J15.28, J16.28
/D1: J1.30, J2.30, J3.30, J4.30, J5.30, J6.30, J7.30, J8.30, J9.30, J10.30, J11.30, J12.30, J13.30, J14.30, J15.30, J16.30
/D2: J1.24, J2.24, J3.24, J4.24, J5.24, J6.24, J7.24, J8.24, J9.24, J10.24, J11.24, J12.24, J13.24, J14.24, J15.24, J16.24
/D3: J1.16, J2.16, J3.16, J4.16, J5.16, J6.16, J7.16, J8.16, J9.16, J10.16, J11.16, J12.16, J13.16, J14.16, J15.16, J16.16
/D4: J1.14, J2.14, J3.14, J4.14, J5.14, J6.14, J7.14, J8.14, J9.14, J10.14, J11.14, J12.14, J13.14, J14.14, J15.14, J16.14
/D5: J1.18, J2.18, J3.18, J4.18, J5.18, J6.18, J7.18, J8.18, J9.18, J10.18, J11.18, J12.18, J13.18, J14.18, J15.18, J16.18
/D6: J1.20, J2.20, J3.20, J4.20, J5.20, J6.20, J7.20, J8.20, J9.20, J10.20, J11.20, J12.20, J13.20, J14.20, J15.20, J16.20
/D7: J1.26, J2.26, J3.26, J4.26, J5.26, J6.26, J7.26, J8.26, J9.26, J10.26, J11.26, J12.26, J13.26, J14.26, J15.26, J16.26
/E: J32.13, J33.13, J34.13, J35.13, J36.13, J37.13, J38.13, J39.13
/I2C_RX: J1.48, J2.48, J3.48, J4.48, J5.48, J6.48, J7.48, J8.48, J9.48, J10.48, J11.48, J12.48, J13.48, J14.48, J15.48, J16.48
/I2C_TX: J1.50, J2.50, J3.50, J4.50, J5.50, J6.50, J7.50, J8.50, J9.50, J10.50, J11.50, J12.50, J13.50, J14.50, J15.50, J16.50
/PHI: J32.9, J33.9, J34.9, J35.9, J36.9, J37.9, J38.9, J39.9
/SPARE0: J32.12, J33.12, J34.12, J35.12, J36.12, J37.12, J38.12, J39.12
/SPARE1: J32.14, J33.14, J34.14, J35.14, J36.14, J37.14, J38.14, J39.14
/SPARE2: J32.16, J33.16, J34.16, J35.16, J36.16, J37.16, J38.16, J39.16
/ST: J32.11, J33.11, J34.11, J35.11, J36.11, J37.11, J38.11, J39.11
/VCC: C1.1, C2.1, C3.1, C4.1, C5.1, C6.1, C7.1, C8.1, C9.1, C10.1, C11.1, C12.1, C13.1, C14.1, C15.1, J1.22, J1.42, J2.22, J2.42, J3.22, J3.42, J4.22, J4.42, J5.22, J5.42, J6.22, J6.42, J7.22, J7.42, J8.22, J8.42, J9.22, J9.42, J10.22, J10.42, J11.22, J11.42, J12.22, J12.42, J13.22, J13.42, J14.22, J14.42, J15.22, J15.42, J16.22, J16.42, J32.10, J33.10, J34.10, J35.10, J36.10, J37.10, J38.10, J39.10, R1.1, SW1.1 (A)
/~BAI-1: J1.44, J17.1
/~BAI-2: J2.44, J19.1
/~BAI-3: J3.44, J21.1
/~BAI-4: J4.44, J23.1
/~BAI-5: J5.44, J25.1
/~BAI-6: J6.44, J27.1
/~BAI-7: J7.44, J29.1
/~BAI-8: J8.44, J31.1
/~BAI-9: J9.44, J18.1
/~BAI-10: J10.44, J20.1
/~BAI-11: J11.44, J22.1
/~BAI-12: J12.44, J24.1
/~BAI-13: J13.44, J26.1
/~BAI-14: J14.44, J28.1
/~BAI-15: J15.44, J30.1
/~BAO-2: J2.46, J17.2
/~BAO-3: J3.46, J19.2
/~BAO-4: J4.46, J21.2
/~BAO-5: J5.46, J23.2
/~BAO-6: J6.46, J25.2
/~BAO-7: J7.46, J27.2
/~BAO-8: J8.46, J29.2
/~BAO-9: J9.46, J31.2
/~BAO-10: J10.46, J18.2
/~BAO-11: J11.46, J20.2
/~BAO-12: J12.46, J22.2
/~BAO-13: J13.46, J24.2
/~BAO-14: J14.46, J26.2
/~BAO-15: J15.46, J28.2
/~BAO-16: J16.46, J30.2
/~BUSACK: J1.35, J2.35, J3.35, J4.35, J5.35, J6.35, J7.35, J8.35, J9.35, J10.35, J11.35, J12.35, J13.35, J14.35, J15.35, J16.35
/~BUSRQ: J1.31, J2.31, J3.31, J4.31, J5.31, J6.31, J7.31, J8.31, J9.31, J10.31, J11.31, J12.31, J13.31, J14.31, J15.31, J16.31
/~DREQ0: J1.41, J2.41, J3.41, J4.41, J5.41, J6.41, J7.41, J8.41, J9.41, J10.41, J11.41, J12.41, J13.41, J14.41, J15.41, J16.41
/~DREQ1: J32.7, J33.7, J34.7, J35.7, J36.7, J37.7, J38.7, J39.7
/~HALT: J1.36, J2.36, J3.36, J4.36, J5.36, J6.36, J7.36, J8.36, J9.36, J10.36, J11.36, J12.36, J13.36, J14.36, J15.36, J16.36
/~IEI-1: J1.47, J17.3
/~IEI-2: J2.47, J19.3
/~IEI-3: J3.47, J21.3
/~IEI-4: J4.47, J23.3
/~IEI-5: J5.47, J25.3
/~IEI-6: J6.47, J27.3
/~IEI-7: J7.47, J29.3
/~IEI-8: J8.47, J31.3
/~IEI-9: J9.47, J18.3
/~IEI-10: J10.47, J20.3
/~IEI-11: J11.47, J22.3
/~IEI-12: J12.47, J24.3
/~IEI-13: J13.47, J26.3
/~IEI-14: J14.47, J28.3
/~IEI-15: J15.47, J30.3
/~IEO-2: J2.49, J17.4
/~IEO-3: J3.49, J19.4
/~IEO-4: J4.49, J21.4
/~IEO-5: J5.49, J23.4
/~IEO-6: J6.49, J25.4
/~IEO-7: J7.49, J27.4
/~IEO-8: J8.49, J29.4
/~IEO-9: J9.49, J31.4
/~IEO-10: J10.49, J18.4
/~IEO-11: J11.49, J20.4
/~IEO-12: J12.49, J22.4
/~IEO-13: J13.49, J24.4
/~IEO-14: J14.49, J26.4
/~IEO-15: J15.49, J28.4
/~IEO-16: J16.49, J30.4
/~INT0: J1.32, J2.32, J3.32, J4.32, J5.32, J6.32, J7.32, J8.32, J9.32, J10.32, J11.32, J12.32, J13.32, J14.32, J15.32, J16.32
/~INT1: J32.1, J33.1, J34.1, J35.1, J36.1, J37.1, J38.1, J39.1
/~INT2: J32.3, J33.3, J34.3, J35.3, J36.3, J37.3, J38.3, J39.3
/~IORQ: J1.40, J2.40, J3.40, J4.40, J5.40, J6.40, J7.40, J8.40, J9.40, J10.40, J11.40, J12.40, J13.40, J14.40, J15.40, J16.40
/~M1: J1.27, J2.27, J3.27, J4.27, J5.27, J6.27, J7.27, J8.27, J9.27, J10.27, J11.27, J12.27, J13.27, J14.27, J15.27, J16.27
/~MREQ: J1.38, J2.38, J3.38, J4.38, J5.38, J6.38, J7.38, J8.38, J9.38, J10.38, J11.38, J12.38, J13.38, J14.38, J15.38, J16.38
/~NMI: J1.34, J2.34, J3.34, J4.34, J5.34, J6.34, J7.34, J8.34, J9.34, J10.34, J11.34, J12.34, J13.34, J14.34, J15.34, J16.34
/~RD: J1.39, J2.39, J3.39, J4.39, J5.39, J6.39, J7.39, J8.39, J9.39, J10.39, J11.39, J12.39, J13.39, J14.39, J15.39, J16.39
/~RESET: J1.29, J2.29, J3.29, J4.29, J5.29, J6.29, J7.29, J8.29, J9.29, J10.29, J11.29, J12.29, J13.29, J14.29, J15.29, J16.29
/~RFSH: J1.25, J2.25, J3.25, J4.25, J5.25, J6.25, J7.25, J8.25, J9.25, J10.25, J11.25, J12.25, J13.25, J14.25, J15.25, J16.25
/~TEND0: J1.45, J2.45, J3.45, J4.45, J5.45, J6.45, J7.45, J8.45, J9.45, J10.45, J11.45, J12.45, J13.45, J14.45, J15.45, J16.45
/~TEND1: J32.5, J33.5, J34.5, J35.5, J36.5, J37.5, J38.5, J39.5
/~WAIT: J1.33, J2.33, J3.33, J4.33, J5.33, J6.33, J7.33, J8.33, J9.33, J10.33, J11.33, J12.33, J13.33, J14.33, J15.33, J16.33
/~WR: J1.37, J2.37, J3.37, J4.37, J5.37, J6.37, J7.37, J8.37, J9.37, J10.37, J11.37, J12.37, J13.37, J14.37, J15.37, J16.37
GND: C1.2, C2.2, C3.2, C4.2, C5.2, C6.2, C7.2, C8.2, C9.2, C10.2, C11.2, C12.2, C13.2, C14.2, C15.2, D1.1 (K), J1.23, J1.43, J2.23, J2.43, J3.23, J3.43, J4.23, J4.43, J5.23, J5.43, J6.23, J6.43, J7.23, J7.43, J8.23, J8.43, J9.23, J9.43, J10.23, J10.43, J11.23, J11.43, J12.23, J12.43, J13.23, J13.43, J14.23, J14.43, J15.23, J15.43, J16.23, J16.43, J32.15, J33.15, J34.15, J35.15, J36.15, J37.15, J38.15, J39.15, P1.1, P2.1, P3.1, P4.1, P5.1, P6.1, T1.2
unnamed: D1.2 (A), R1.2

Notes on the sheet:
Note: female 2x25 2.54mm straight PCB connectors
Mounting Holes 3.7mm diameter
Note: SPDT right angle toggle switch on-on Jameco Part no.: 2277743 Manufacturer: C&K Manufacturer p/n: U11P3Y9A2QE
Primary Z80 Bus Interface Connectors
Zilog Interrupt Priority Bus Jumpers
Extended Z80180 Bus Interface Connectors

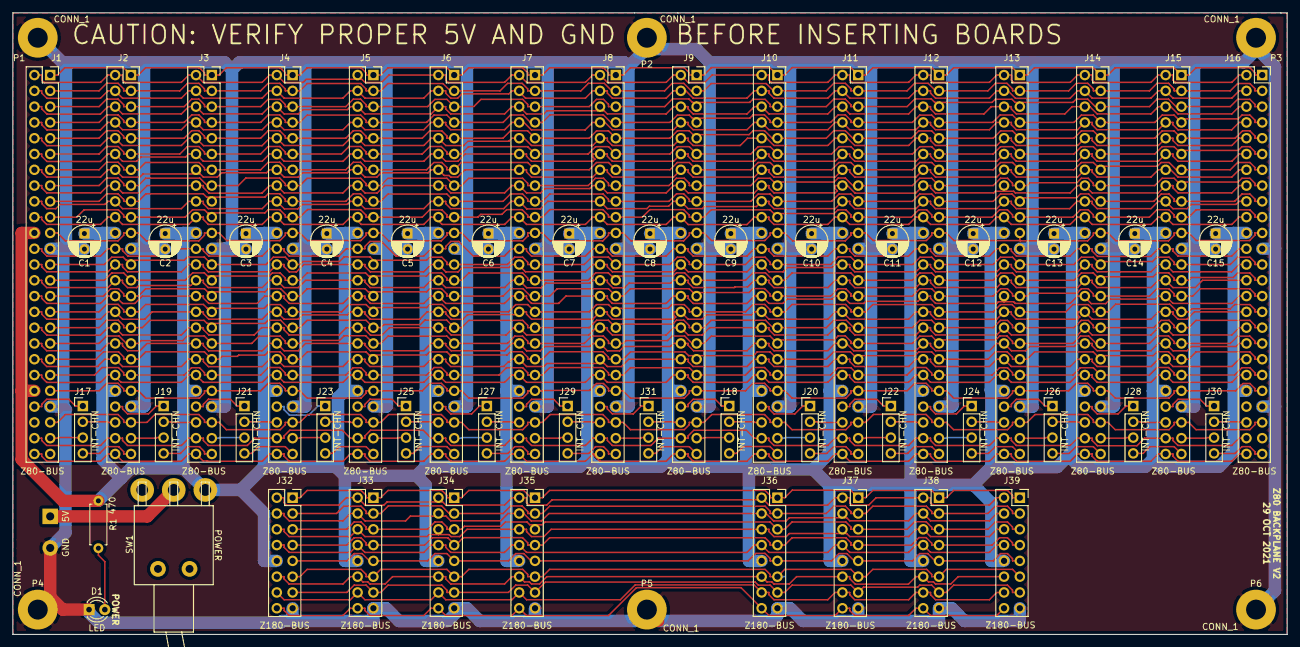
[picture p235: board Z80BCKPLN2.kicad_pcb from above]

Board: 2 copper layers, 205.0 x 100.0 mm, 64 parts (1 on the bottom side), 120 nets.
