lynchaj/nhyodyne/Z80BCKPLN1/Z80BCKPLN.kicad_pcb

## KiCad design Z80BCKPLN1/Z80BCKPLN.kicad_pcb (2021-11-30)

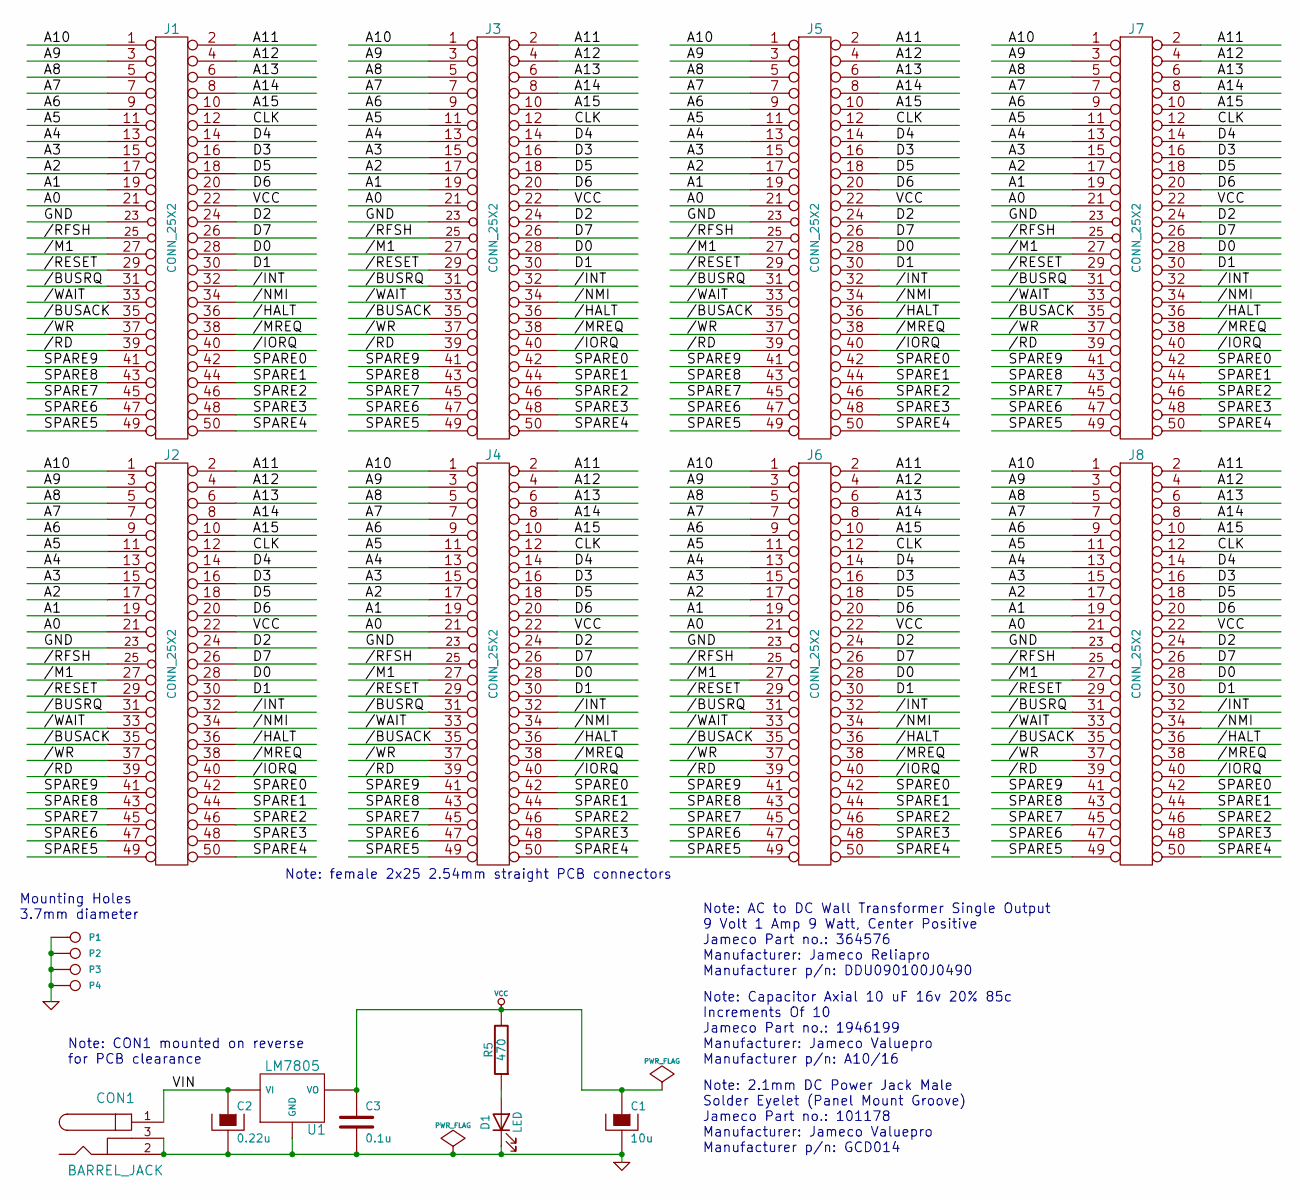
[picture p236: schematic Z80BCKPLN.sch]

Parts:
C1: 10u; CP_Axial_L10.0mm_D4.5mm_P15.00mm_Horizontal
C2: 0.22u; CP_Radial_Tantal_D5.0mm_P5.00mm
C3: 0.1u; C_Disc_D5.0mm_W2.5mm_P5.00mm
CON1: BARREL_JACK; JACK_ALIM
D1: LED; LED_D5.0mm_Horizontal_O3.81mm_Z3.0mm
J1, J2, J3, J4, J5, J6, J7, J8: CONN_25X2; Socket_Strip_Straight_2x25_Pitch2.54mm
P1, P2, P3, P4: CONN_1; MountingHole_3.2mm_M3_Pad
R5: 470; R_Axial_DIN0207_L6.3mm_D2.5mm_P7.62mm_Horizontal
U1: LM7805; TO-220-3_Horizontal_TabDown

Connections:
//BUSACK: J1.35, J2.35, J3.35, J4.35, J5.35, J6.35, J7.35, J8.35
//BUSRQ: J1.31, J2.31, J3.31, J4.31, J5.31, J6.31, J7.31, J8.31
//HALT: J1.36, J2.36, J3.36, J4.36, J5.36, J6.36, J7.36, J8.36
//INT: J1.32, J2.32, J3.32, J4.32, J5.32, J6.32, J7.32, J8.32
//IORQ: J1.40, J2.40, J3.40, J4.40, J5.40, J6.40, J7.40, J8.40
//M1: J1.27, J2.27, J3.27, J4.27, J5.27, J6.27, J7.27, J8.27
//MREQ: J1.38, J2.38, J3.38, J4.38, J5.38, J6.38, J7.38, J8.38
//NMI: J1.34, J2.34, J3.34, J4.34, J5.34, J6.34, J7.34, J8.34
//RD: J1.39, J2.39, J3.39, J4.39, J5.39, J6.39, J7.39, J8.39
//RESET: J1.29, J2.29, J3.29, J4.29, J5.29, J6.29, J7.29, J8.29
//RFSH: J1.25, J2.25, J3.25, J4.25, J5.25, J6.25, J7.25, J8.25
//WAIT: J1.33, J2.33, J3.33, J4.33, J5.33, J6.33, J7.33, J8.33
//WR: J1.37, J2.37, J3.37, J4.37, J5.37, J6.37, J7.37, J8.37
/A0: J1.21, J2.21, J3.21, J4.21, J5.21, J6.21, J7.21, J8.21
/A1: J1.19, J2.19, J3.19, J4.19, J5.19, J6.19, J7.19, J8.19
/A2: J1.17, J2.17, J3.17, J4.17, J5.17, J6.17, J7.17, J8.17
/A3: J1.15, J2.15, J3.15, J4.15, J5.15, J6.15, J7.15, J8.15
/A4: J1.13, J2.13, J3.13, J4.13, J5.13, J6.13, J7.13, J8.13
/A5: J1.11, J2.11, J3.11, J4.11, J5.11, J6.11, J7.11, J8.11
/A6: J1.9, J2.9, J3.9, J4.9, J5.9, J6.9, J7.9, J8.9
/A7: J1.7, J2.7, J3.7, J4.7, J5.7, J6.7, J7.7, J8.7
/A8: J1.5, J2.5, J3.5, J4.5, J5.5, J6.5, J7.5, J8.5
/A9: J1.3, J2.3, J3.3, J4.3, J5.3, J6.3, J7.3, J8.3
/A10: J1.1, J2.1, J3.1, J4.1, J5.1, J6.1, J7.1, J8.1
/A11: J1.2, J2.2, J3.2, J4.2, J5.2, J6.2, J7.2, J8.2
/A12: J1.4, J2.4, J3.4, J4.4, J5.4, J6.4, J7.4, J8.4
/A13: J1.6, J2.6, J3.6, J4.6, J5.6, J6.6, J7.6, J8.6
/A14: J1.8, J2.8, J3.8, J4.8, J5.8, J6.8, J7.8, J8.8
/A15: J1.10, J2.10, J3.10, J4.10, J5.10, J6.10, J7.10, J8.10
/CLK: J1.12, J2.12, J3.12, J4.12, J5.12, J6.12, J7.12, J8.12
/D0: J1.28, J2.28, J3.28, J4.28, J5.28, J6.28, J7.28, J8.28
/D1: J1.30, J2.30, J3.30, J4.30, J5.30, J6.30, J7.30, J8.30
/D2: J1.24, J2.24, J3.24, J4.24, J5.24, J6.24, J7.24, J8.24
/D3: J1.16, J2.16, J3.16, J4.16, J5.16, J6.16, J7.16, J8.16
/D4: J1.14, J2.14, J3.14, J4.14, J5.14, J6.14, J7.14, J8.14
/D5: J1.18, J2.18, J3.18, J4.18, J5.18, J6.18, J7.18, J8.18
/D6: J1.20, J2.20, J3.20, J4.20, J5.20, J6.20, J7.20, J8.20
/D7: J1.26, J2.26, J3.26, J4.26, J5.26, J6.26, J7.26, J8.26
/SPARE0: J1.42, J2.42, J3.42, J4.42, J5.42, J6.42, J7.42, J8.42
/SPARE1: J1.44, J2.44, J3.44, J4.44, J5.44, J6.44, J7.44, J8.44
/SPARE2: J1.46, J2.46, J3.46, J4.46, J5.46, J6.46, J7.46, J8.46
/SPARE3: J1.48, J2.48, J3.48, J4.48, J5.48, J6.48, J7.48, J8.48
/SPARE4: J1.50, J2.50, J3.50, J4.50, J5.50, J6.50, J7.50, J8.50
/SPARE5: J1.49, J2.49, J3.49, J4.49, J5.49, J6.49, J7.49, J8.49
/SPARE6: J1.47, J2.47, J3.47, J4.47, J5.47, J6.47, J7.47, J8.47
/SPARE7: J1.45, J2.45, J3.45, J4.45, J5.45, J6.45, J7.45, J8.45
/SPARE8: J1.43, J2.43, J3.43, J4.43, J5.43, J6.43, J7.43, J8.43
/SPARE9: J1.41, J2.41, J3.41, J4.41, J5.41, J6.41, J7.41, J8.41
/VIN: C2.1, CON1.1, U1.VI
GND: C1.2, C2.2, C3.2, CON1.2, CON1.3, D1.1 (K), J1.23, J2.23, J3.23, J4.23, J5.23, J6.23, J7.23, J8.23, P1.1, P2.1, P3.1, P4.1, U1.GND
unnamed: D1.2 (A), R5.1
VCC: C1.1, C3.1, J1.22, J2.22, J3.22, J4.22, J5.22, J6.22, J7.22, J8.22, R5.2, U1.VO

Notes on the sheet:
Note: 2.1mm DC Power Jack Male Solder Eyelet (Panel Mount Groove) Jameco Part no.: 101178 Manufacturer: Jameco Valuepro Manufacturer p/n: GCD014
Note: female 2x25 2.54mm straight PCB connectors
Note: Capacitor Axial 10 uF 16v 20% 85c Increments Of 10 Jameco Part no.: 1946199 Manufacturer: Jameco Valuepro Manufacturer p/n: A10/16
Note: CON1 mounted on reverse for PCB clearance
Mounting Holes 3.7mm diameter
Note: AC to DC Wall Transformer Single Output 9 Volt 1 Amp 9 Watt, Center Positive Jameco Part no.: 364576 Manufacturer: Jameco Reliapro Manufacturer p/n: DDU090100J0490

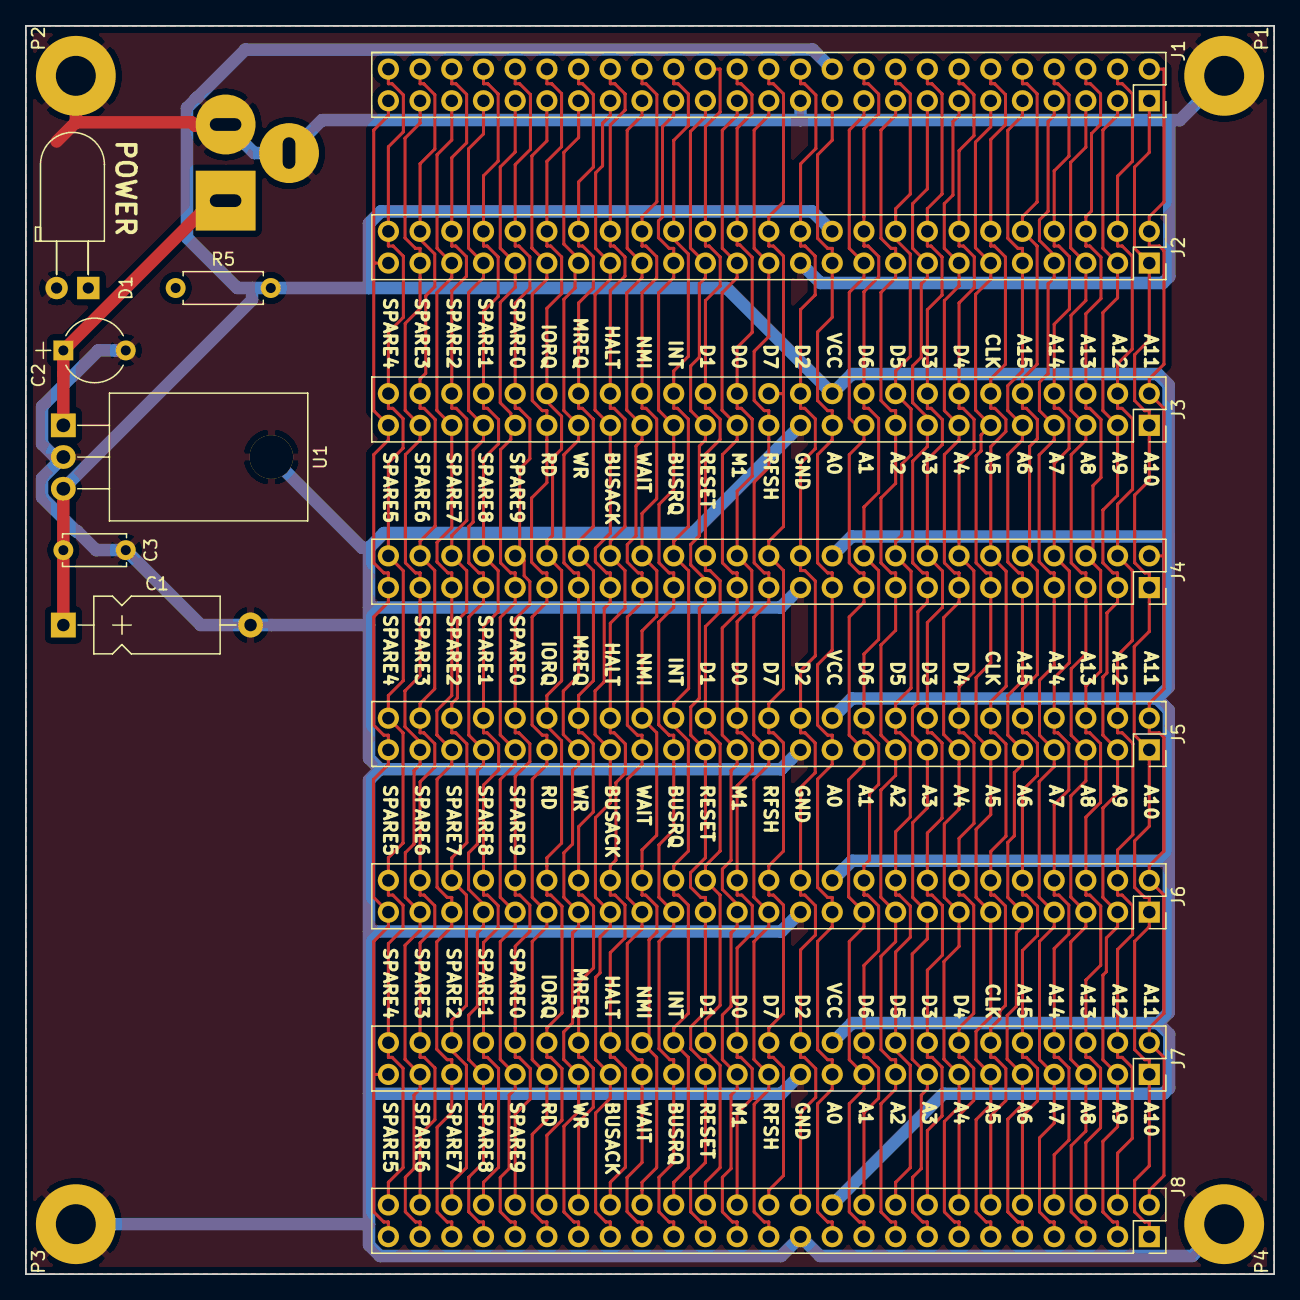
[picture p237: board Z80BCKPLN.kicad_pcb from above]

Board: 2 copper layers, 100.0 x 100.0 mm, 19 parts (1 on the bottom side), 52 nets.
