lynchaj/nhyodyne/Z80VDC1/Z80VDC.kicad_pcb

## KiCad design Z80VDC1/Z80VDC.kicad_pcb (2021-11-30)

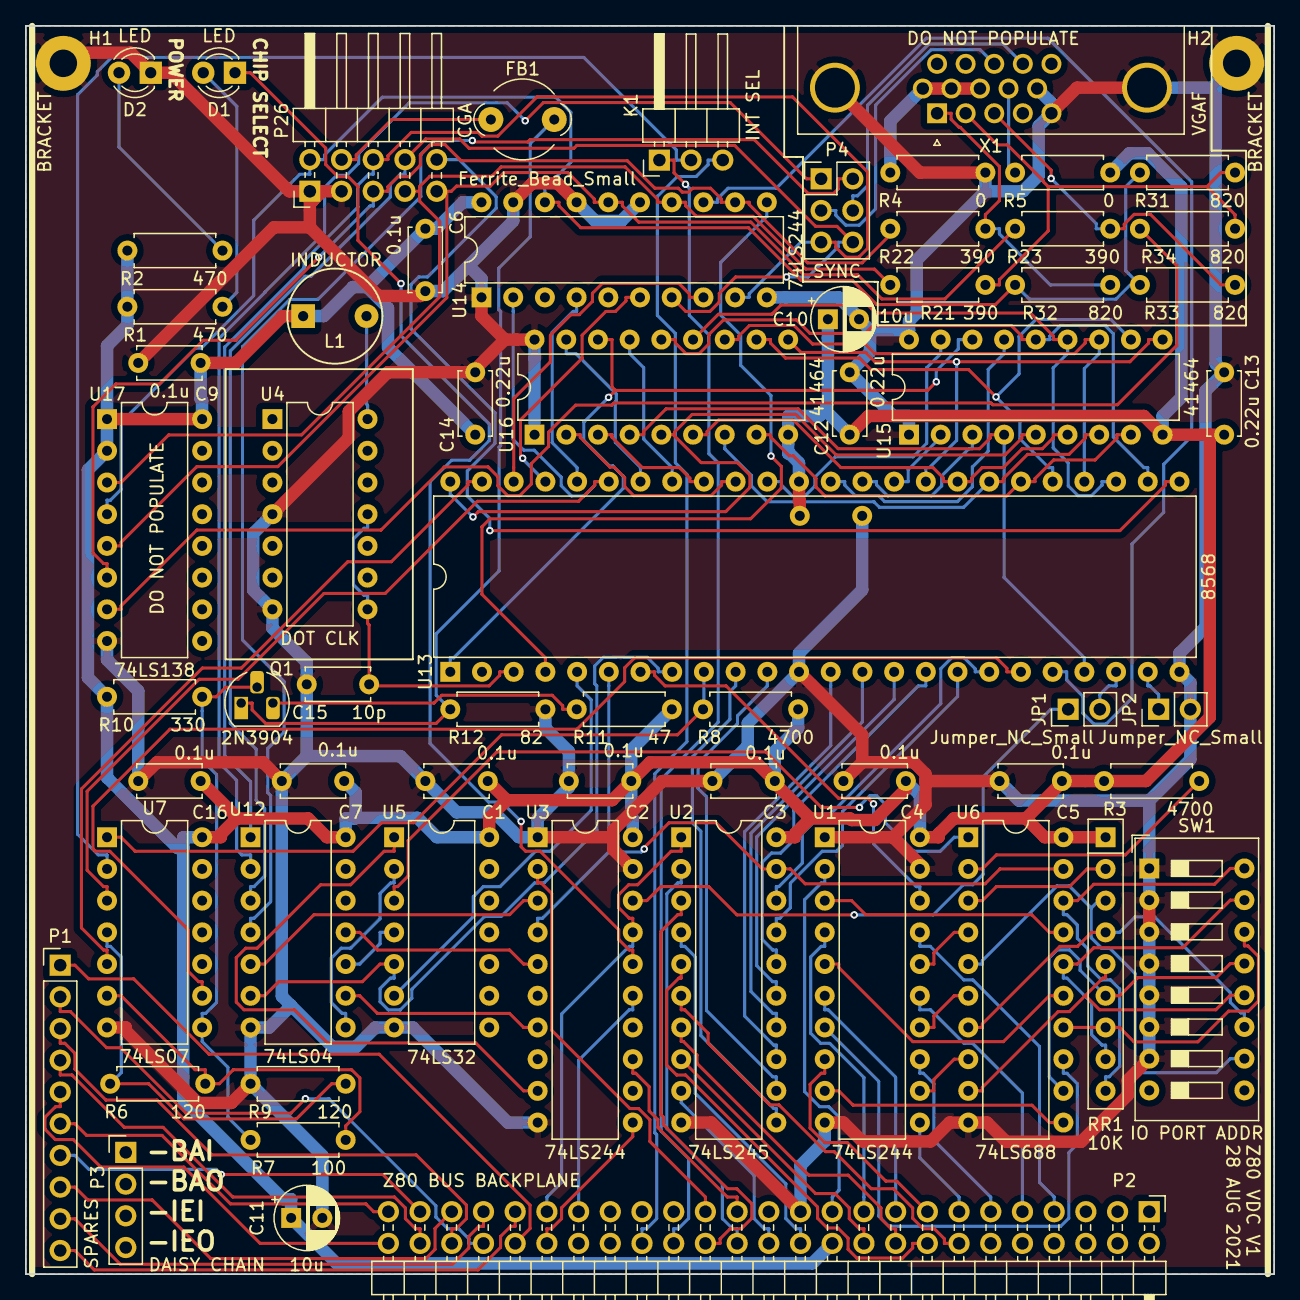
[picture p238: board Z80VDC.kicad_pcb from above]

Board: 2 copper layers, 100.0 x 100.0 mm, 66 parts (1 on the bottom side), 130 nets.

Parts:
C1, C2, C3, C4, C5, C6, C7, C8, C9, C16: 0.1u; C_Disc_D5.0mm_W2.5mm_P5.00mm
C10, C11: 10u; CP_Radial_D5.0mm_P2.50mm
C12, C13, C14: 0.22u; C_Disc_D5.0mm_W2.5mm_P5.00mm
C15: 10p; C_Disc_D5.0mm_W2.5mm_P5.00mm
D1, D2: LED; LED_D3.0mm
FB1: Ferrite_Bead_Small; LairdTech_28C0236-0JW-10
H1, H2: BRACKET; MountingHole_2.2mm_M2_Pad
JP1, JP2: Jumper_NC_Small; PinHeader_1x02_P2.54mm_Vertical
K1: INT SEL; PinHeader_1x03_P2.54mm_Horizontal
L1: INDUCTOR; INDUCTOR_V
P1: SPARES; PinHeader_1x10_P2.54mm_Vertical
P2: Z80 BUS BACKPLANE; PinHeader_2x25_P2.54mm_Horizontal
P3: DAISY CHAIN; PinHeader_1x04_P2.54mm_Vertical
P4: SYNC; PinHeader_2x03_P2.54mm_Vertical
P26: CGA; PinHeader_2x05_P2.54mm_Horizontal
Q1: 2N3904; TO-92_HandSolder
R1, R2: 470; R_Axial_DIN0207_L6.3mm_D2.5mm_P7.62mm_Horizontal
R3, R8: 4700; R_Axial_DIN0207_L6.3mm_D2.5mm_P7.62mm_Horizontal
R4, R5: 0; R_Axial_DIN0207_L6.3mm_D2.5mm_P7.62mm_Horizontal
R6, R9: 120; R_Axial_DIN0207_L6.3mm_D2.5mm_P7.62mm_Horizontal
R7: 100; R_Axial_DIN0207_L6.3mm_D2.5mm_P7.62mm_Horizontal
R10: 330; R_Axial_DIN0207_L6.3mm_D2.5mm_P7.62mm_Horizontal
R11: 47; R_Axial_DIN0207_L6.3mm_D2.5mm_P7.62mm_Horizontal
R12: 82; R_Axial_DIN0207_L6.3mm_D2.5mm_P7.62mm_Horizontal
R21, R22, R23: 390; R_Axial_DIN0207_L6.3mm_D2.5mm_P7.62mm_Horizontal
R31, R32, R33, R34: 820; R_Axial_DIN0207_L6.3mm_D2.5mm_P7.62mm_Horizontal
RR1: 10K; R_Array_SIP9
SW1: IO PORT ADDR; SW_DIP_SPSTx08_Slide_9.78x22.5mm_W7.62mm_P2.54mm
U1, U3, U14: 74LS244; DIP-20_W7.62mm
U2: 74LS245; DIP-20_W7.62mm
U4: DOT CLK; DIP-14_W7.62mm
U5: 74LS32; DIP-14_W7.62mm
U6: 74LS688; DIP-20_W7.62mm
U7: 74LS07; DIP-14_W7.62mm
U12: 74LS04; DIP-14_W7.62mm
U13: 8568; DIP-48_W15.24mm
U15, U16: 41464; DIP-18_W7.62mm
U17: 74LS138; DIP-16_W7.62mm
X1: VGAF; DSUB-15-HD_Female_Horizontal_P2.29x1.98mm_EdgePinOffset3.03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

Connections:
/688SEL#: U5.3, U6.1
/A0: P2.21, U1.2
/A1: P2.19, U1.4
/A2: P2.17, U1.6
/A3: P2.15, U1.8
/A4: P2.13, U1.11
/A5: P2.11, U1.13
/A6: P2.9, U1.15
/A7: P2.7, U1.17
/B: U13.44, U14.4
/BOUT: P26.9, R23.1, U14.16, U17.5
/CAS#: U13.1, U15.16, U16.16
/CSYNC: U7.9, U13.19
/CS_VDC#: U2.19, U3.4, U6.19, U13.6
/CV: U7.5, U13.47
/CVBS: FB1.1, P26.4
/D0: P2.28, U2.2
/D1: P2.30, U2.3
/D2: P2.24, U2.4
/D3: P2.16, U2.5
/D4: P2.14, U2.6
/D5: P2.18, U2.7
/D6: P2.20, U2.8
/D7: P2.26, U2.9
/DA0: U13.26, U15.14, U16.14
/DA1: U13.27, U15.13, U16.13
/DA2: U13.28, U15.12, U16.12
/DA3: U13.29, U15.11, U16.11
/DA4: U13.30, U15.8, U16.8
/DA5: U13.31, U15.7, U16.7
/DA6: U13.32, U15.6, U16.6
/DA7: U13.33, U15.10, U16.10
/DCLK#: C15.1, U4.8, U4.11, U13.3
/DD0: U13.34, U15.2
/DD1: U13.35, U15.3
/DD2: U13.36, U15.15
/DD3: U13.38, U15.17
/DD4: U13.39, U16.2
/DD5: U13.40, U16.3
/DD6: U13.41, U16.15
/DD7: U13.42, U16.17
/DR-W: U13.21, U15.4, U16.4
/FIX_BROWN: R34.1, U17.7
/G: U13.45, U14.6
/GOUT: P26.7, R21.1, U14.14, U17.3
/HSYN: U13.4, U14.11
/HSYNOUT: P4.5, P26.6, U12.1, U14.9
/I: U7.3, U13.43, U14.2
/INT#: K1.1, P2.32
/INTR#: R8.1, U7.1, U13.9
/IORQ#: P2.40, U3.11
/IOUT: P26.2, R31.1, R32.1, R33.1, U14.18, U17.4
/LP2#: P26.10, U13.25
/M1#: P2.27, U3.13
/MONOCHROME: FB1.2, Q1.1, R12.1
/NMI#: K1.3, P2.34
/R: U13.46, U14.8
/RAS#: U13.48, U15.5, U16.5
/RD: U5.5, U12.6, U13.8
/RD#: P2.39, U2.1, U3.17
/RESET#: P2.29, U3.2
/ROUT: P26.5, R22.1, U14.12, U17.6
/SPARE0: P1.1, P2.42
/SPARE1: P1.2, P2.44
/SPARE2: P1.3, P2.46
/SPARE3: P1.4, P2.48
/SPARE4: P1.5, P2.50
/SPARE5: P1.6, P2.49
/SPARE6: P1.7, P2.47
/SPARE7: P1.8, P2.45
/SPARE8: P1.9, P2.43
/SPARE9: P1.10, P2.41
/VGA5v: R5.1, X1.9
/VGA-BLUE: R23.2, R33.2, X1.3
/VGA-GND: R4.1, X1.6, X1.7, X1.8
/VGA-GREEN: R21.2, R31.2, R34.2, X1.2
/VGA-HSYNC: P4.3, X1.13
/VGA-RED: R22.2, R32.2, X1.1
/VGA-VSYNC: P4.4, X1.14
/VSYN: U13.20, U14.13
/VSYNOUT: P4.6, P26.8, U12.3, U14.7
/WR: U5.4, U12.10
/WR#: P2.37, U3.15
/bA0: U1.18, U13.7
/bA1: U1.16, U6.4
/bA2: U1.14, U6.6
/bA3: U1.12, U6.8
/bA4: U1.9, U6.11
/bA5: U1.7, U6.13
/bA6: U1.5, U6.15
/bA7: U1.3, U6.17
/bD0: U2.18, U13.18
/bD1: U2.17, U13.17
/bD2: U2.16, U13.16
/bD3: U2.15, U13.15
/bD4: U2.14, U13.14
/bD5: U2.13, U13.13
/bD6: U2.12, U13.11
/bD7: U2.11, U13.10
/bIORQ#: U3.9, U5.1
/bM1#: U3.7, U12.9
/bRD#: U3.3, U12.5
/bRESET#: JP1.1, U3.18
/bWR#: U3.5, U12.11
GND: C1.2, C2.2, C3.2, C4.2, C5.2, C6.2, C7.2, C8.2, C9.2, C10.2, C11.2, C12.2, C13.2, C14.2, C15.2, C16.2, D2.1, H1.1, H2.1, JP2.2, P2.23, P26.1, P26.3, R4.2, R9.1, R12.2, SW1.1, SW1.2, SW1.3, SW1.4, SW1.5, SW1.6, SW1.7, U1.1, U1.10, U1.19, U2.10, U3.1, U3.10, U3.19, U4.4, U4.7, U5.7, U6.10, U7.7, U12.7, U13.12, U13.24, U14.1, U14.10, U14.15, U14.17, U14.19, U15.1, U15.18, U16.1, U16.18, U17.8, X1.5, X1.10, X1.SH1, X1.SH2
unnamed: D1.1, U3.16
unnamed: D1.2, R1.1
unnamed: D2.2, R2.1
unnamed: JP1.2, U13.22
unnamed: JP2.1, U13.23
unnamed: K1.2, U7.2
unnamed: L1.2, U4.14
unnamed: P4.1, U12.2
unnamed: P4.2, U12.4
unnamed: Q1.2, R7.1, R10.2, U7.8
unnamed: Q1.3, R11.2
unnamed: R3.1, U6.2
unnamed: R6.1, R9.2, U7.4
unnamed: R6.2, R7.2, U7.6
unnamed: RR1.2, U6.3
unnamed: RR1.3, SW1.10, U6.5
unnamed: RR1.4, SW1.11, U6.7
unnamed: RR1.5, SW1.12, U6.9
unnamed: RR1.6, SW1.13, U6.12
unnamed: RR1.7, SW1.14, U6.14
unnamed: RR1.8, SW1.15, U6.16
unnamed: RR1.9, SW1.16, U6.18
unnamed: U5.2, U12.8
unnamed: U5.6, U13.5
VCC: C1.1, C2.1, C3.1, C4.1, C5.1, C6.1, C7.1, C8.1, C9.1, C10.1, C11.1, C12.1, C13.1, C14.1, C16.1, L1.1, P2.22, R1.2, R2.2, R3.2, R5.2, R8.2, R10.1, R11.1, RR1.1, U1.20, U2.20, U3.20, U5.14, U6.20, U7.14, U12.14, U13.37, U14.20, U15.9, U16.9, U17.1, U17.2, U17.16
