lynchaj/nhyodyne/6502PROC/DOS65/os/dosflp.asm

;__FLOPPY DRIVERS________________________________________________________________________________________________________________
;
; 	DOS/65 floppy drivers for MBC FDC card
;
;	Entry points:
;		FL_SETUP        - called during OS init
;		FL_READ_SECTOR	- read a sector from drive
;		FL_WRITE_SECTOR	- write a sector to drive
;
;________________________________________________________________________________________________________________________________
;
;*
;* HARDWARE I/O ADDRESSES
;*
FDC_MSR         = $0330         ; ADDRESS OF MAIN STATUS REGISTER
FDC_DATA        = $0331         ; FLOPPY DATA REGISTER
FDC_RESET       = $0333         ; FLOPPY RESET
FDC_DCR         = $0335         ; LOAD CONTROL REGISTER
FDC_DOR         = $0336         ; CONFIGURATION CONTROL REGISTER
FDC_TC          = $0337         ; TERMINAL COUNT

;
; FDC COMMANDS
;
CFD_READ        = %00000110     ; CMD,HDS/DS,C,H,R,N,EOT,GPL,DTL --> ST0,ST1,ST2,C,H,R,N
CFD_READDEL     = %00001100     ; CMD,HDS/DS,C,H,R,N,EOT,GPL,DTL --> ST0,ST1,ST2,C,H,R,N
CFD_WRITE       = %00000101     ; CMD,HDS/DS,C,H,R,N,EOT,GPL,DTL --> ST0,ST1,ST2,C,H,R,N
CFD_WRITEDEL    = %00001001     ; CMD,HDS/DS,C,H,R,N,EOT,GPL,DTL --> ST0,ST1,ST2,C,H,R,N
CFD_READTRK     = %00000010     ; CMD,HDS/DS,C,H,R,N,EOT,GPL,DTL --> ST0,ST1,ST2,C,H,R,N
CFD_READID      = %00001010     ; CMD,HDS/DS --> ST0,ST1,ST2,C,H,R,N
CFD_FMTTRK      = %00001101     ; CMD,HDS/DS,N,SC,GPL,D --> ST0,ST1,ST2,C,H,R,N
CFD_SCANEQ      = %00010001     ; CMD,HDS/DS,C,H,R,N,EOT,GPL,STP --> ST0,ST1,ST2,C,H,R,N
CFD_SCANLOEQ    = %00011001     ; CMD,HDS/DS,C,H,R,N,EOT,GPL,STP --> ST0,ST1,ST2,C,H,R,N
CFD_SCANHIEQ    = %00011101     ; CMD,HDS/DS,C,H,R,N,EOT,GPL,STP --> ST0,ST1,ST2,C,H,R,N
CFD_RECAL       = %00000111     ; CMD,DS --> <EMPTY>
CFD_SENSEINT    = %00001000     ; CMD --> ST0,PCN
CFD_SPECIFY     = %00000011     ; CMD,SRT/HUT,HLT/ND --> <EMPTY>
CFD_DRVSTAT     = %00000100     ; CMD,HDS/DS --> ST3
CFD_SEEK        = %00001111     ; CMD,HDS/DS --> <EMPTY>
CFD_VERSION     = %00010000     ; CMD --> ST0

CFD_MFM         = %01000000     ;

;
;
; Specify Command:
; +-----+-----+-----+-----+-----+-----+-----+-----+-----+
; |Byte |  7  |	 6  |  5  |  4	|  3  |	 2  |  1  |  0	|
; +-----+-----+-----+-----+-----+-----+-----+-----+-----+
; |  0	|  0  |	 0  |  0  |  0	|  0  |	 0  |  1  |  1	|
; |  1	| ----- STEP RATE ----- | -- HEAD UNLOAD TIME - |
; |  2	| ------------ HEAD LOAD TIME ----------- | NDM |
; +-----+-----+-----+-----+-----+-----+-----+-----+-----+
;
;
; Step Rate (milliseconds):		 Head Unload Time (milliseconds):	Head Load Time (milliseconds):
; +------+------+------+------+------+	 +------+------+------+------+------+	+------+------+------+------+------+
; |	 |	   BITRATE	     |	 |	|	  BITRATE	    |	|      |	 BITRATE	   |
; |  VAL | 1.0M | 500K | 300K | 250K |	 |  VAL | 1.0M | 500K | 300K | 250K |	|  VAL | 1.0M | 500K | 300K | 250K |
; +------+------+------+------+------+	 +------+------+------+------+------+	+------+------+------+------+------+
; |    0 |  8.0 | 16.0 | 26.7 | 32.0 |	 |    0 |  128 |  256 |	 426 |	512 |	|    0 |  128 |	 256 |	426 |  512 |
; |    1 |  7.5 | 15.0 | 25.0 | 30.0 |	 |    1 |    8 |   16 | 26.7 |	 32 |	|    1 |    1 |	   2 |	3.3 |	 4 |
; |    2 |  7.0 | 14.0 | 23.3 | 28.0 |	 |    2 |   16 |   32 | 53.3 |	 64 |	|    2 |    2 |	   4 |	6.7 |	 8 |
; |  ... |  ... |  ... |  ... |	 ... |	 |  ... |  ... |  ... |	 ... |	... |	|  ... |  ... |	 ... |	... |  ... |
; |   14 |  1.0 |  2.0 |  3.3 |	 4.0 |	 |   14 |  112 |  224 |	 373 |	448 |	|  126 |  126 |	 252 |	420 |  504 |
; |   15 |  0.5 |  1.0 |  1.7 |	 2.0 |	 |   15 |  120 |  240 |	 400 |	480 |	|  127 |  127 |	 254 |	423 |  508 |
; +------+------+------+------+------+	 +------+------+------+------+------+	+------+------+------+------+------+
;
; IBM PS/2 CALLS FOR:
;   STEP RATE: 3ms (6ms FOR ALL 41mm OR 720K DRIVES)
;   HEAD LOAD TIME: 15ms

DOR_INIT        = %00001100     ; SOFT RESET INACTIVE, DMA ENABLED
DOR_BR250       = DOR_INIT
DOR_BR500       = DOR_INIT



FLOPPY_RETRIES  = 6             ; HOW ABOUT SIX RETIRES?
FLOPPY_RETRIES1 = 2             ; TWO ITERATIONS OF RECAL?

;__FL_SETUP______________________________________________________________________________________________________________________
;
;	SETUP FLOPPY DRIVE SETTINGS
;________________________________________________________________________________________________________________________________
;
FL_SETUP:
        LDA     #$00            ; RESET TRACK/CYL/SEC STORAGE
        STA     debhead         ;
        STA     debcyl          ;
        STA     debsec          ;
        LDA     #$FF            ; SET CACHE TO INVALID
        STA     Cdebhead        ;
        STA     Cdebcyl         ;
        STA     Cdebsec         ;

        PRTS    "FD: MODE=MBC$"
;
        PRTS    " IO=0x$"
        LDA     #>FDC_MSR
        JSR     PRTHEXBYTE
        LDA     #<FDC_MSR
        JSR     PRTHEXBYTE
        JSR     FD_DETECT       ; CHECK FOR FDC
        CMP     #$00
        BEQ     :+              ; CONTINUE IF FOUND
        PRTS    " NOT PRESENT$" ; NOT ZERO, H/W NOT PRESENT
        JSR     NEWLINE
        LDA     #$FF
        RTS                     ; BAIL OUT
:
        PRTS    " PRESENT$"     ; NOT ZERO, H/W NOT PRESENT
        JSR     NEWLINE
        LDA     #DOR_INIT       ; RESET SETTINGS
        STA     FDC_DOR

        JSR     CHECKINT        ;
        LDA     #CFD_SPECIFY    ; SPECIFY COMMAND
        JSR     PFDATA          ; OUTPUT TO FDC
        LDA     #$7F            ; 6 MS STEP, 480 MS HEAD UNLOAD
        JSR     PFDATA          ; OUTPUT TO FDC
        LDA     #$05            ; 508 MS HEAD LOAD, NON-DMA MODE
        JSR     PFDATA          ; OUTPUT TO FDC

        JSR     CHECKINT        ; SEND SEVERAL INTERRUPTS TO ENSURE PROPER STATE
        JSR     CHECKINT        ;
        JSR     CHECKINT        ;
        JSR     CHECKINT        ;
        JSR     CHECKINT        ;
        JSR     CHECKINT        ;

        LDA     #$00
        STA     sekdsk
        LDA     #%00010000
        STA     DSKUNIT
        JSR     RECAL           ;
        LDA     #39             ;
        STA     debcyl          ;
        JSR     SETTRK1
        JSR     RECAL           ;

        LDA     #$01
        STA     sekdsk
        LDA     #%00100001
        STA     DSKUNIT
        JSR     RECAL           ;
        LDA     #39             ;
        STA     debcyl          ;
        JSR     SETTRK1
        JSR     RECAL           ;
        LDA     #DOR_INIT       ; RESET SETTINGS
        STA     FDC_DOR
        RTS


;__FL_READ_SECTOR________________________________________________________________________________________________________________
;
; 	READ A FLOPPY SECTOR
;________________________________________________________________________________________________________________________________
;
;
FL_READ_SECTOR:
        LDA     HARDWARE_DETCT
        CMP     #$00
        BEQ     :+
        RTS
:
        JSR     FL_READ_SECTOR_RAW
        PHA
        JSR     DEBSECR512
        PLA
        RTS

FL_READ_SECTOR_RAW:
        LDA     #$00
        STA     FLRETRY         ; BLANK RETRIES
        STA     FLRETRY1
        LDA     #DOR_INIT
        ORA     DSKUNIT         ;
        STA     FDC_DOR         ; OUTPUT TO CONTROLLER
        JSR     SETUP_FD_CHS
        LDA     debhead         ;
        CMP     Cdebhead        ;
        BNE     READFL_DIRTY
        LDA     debcyl          ;
        CMP     Cdebcyl         ;
        BNE     READFL_DIRTY
        LDA     debsec          ;
        CMP     Cdebsec         ;
        BNE     READFL_DIRTY
; SECTOR ALREADY IN CACHE, DEBLOCK
        LDA     #$00
        RTS
READFL_DIRTY:
        LDA     debhead         ; STORE CURRENT PARMS
        STA     Cdebhead        ;
        LDA     debcyl          ;
        STA     Cdebcyl         ;
        LDA     debsec          ;
        STA     Cdebsec         ;

READFL1:
        LDA     #CFD_READ|CFD_MFM; BIT 6 SETS MFM, 06H IS READ COMMAND
        STA     FCMD            ; SET COMMAND
        JSR     DSKOP           ; DO DISK OPERATION

        CMP     #$00
        BEQ     READFLDONE      ; OPERATION SUCCESSFUL
        INC     FLRETRY         ; LET'S RETRY
        LDA     FLRETRY
        CMP     #FLOPPY_RETRIES
        BNE     READFL1
        JSR     RECAL           ; AFTER X RETRIES, LET'S RECAL THE HEAD
        JSR     SETTRACK        ;
        LDA     #$00            ;
        STA     FLRETRY         ; MORE RETRIES!
        INC     FLRETRY1
        LDA     FLRETRY1
        CMP     #FLOPPY_RETRIES1
        BNE     READFL1

        LDA     #$FF            ; RETRIES FAILED, INVALIDATE CACHE AND REPORT ERROR
        STA     Cdebhead        ;
        STA     Cdebcyl         ;
        STA     Cdebsec         ;
        RTS                     ; A = $FF ON RETURN = OPERATION ERROR
READFLDONE:
        LDA     #$00            ; A = 0 ON RETURN = OPERATION OK
        RTS

;__FL_WRITE_SECTOR_______________________________________________________________________________________________________________
;
; 	WRITE A FLOPPY SECTOR
;________________________________________________________________________________________________________________________________
;
FL_WRITE_SECTOR:
        LDA     HARDWARE_DETCT
        CMP     #$00
        BEQ     :+
        RTS
:
        JSR     FL_READ_SECTOR_RAW
        JSR     BLKSECR512

FL_WRITE_SECTOR_RAW:
        LDA     #$00
        STA     FLRETRY         ; BLANK RETRIES
        STA     FLRETRY1
        LDA     #$FF
        STA     Cdebhead        ; INVALIDATE CACHE
        STA     Cdebcyl         ;
        STA     Cdebsec         ;

WRITEFL1:
        LDA     #CFD_WRITE|CFD_MFM; BIT 6 SETS MFM, 05H IS WRITE COMMAND
        STA     FCMD
        JSR     DSKOP

        CMP     #$00
        BEQ     WRITEFLDONE
        INC     FLRETRY
        LDA     FLRETRY
        CMP     #FLOPPY_RETRIES
        BNE     WRITEFL1
        JSR     RECAL
        JSR     SETTRACK
        LDA     #$00
        STA     FLRETRY
        INC     FLRETRY1
        LDA     FLRETRY1
        CMP     #FLOPPY_RETRIES1
        BNE     WRITEFL1
        LDA     #$FF            ; INVALIDATE CACHE
        STA     Cdebhead        ;
        STA     Cdebcyl         ;
        STA     Cdebsec         ;
        RTS                     ; A = $FF ON RETURN = OPERATION ERROR
WRITEFLDONE:
        LDA     #$00            ; A = 0 ON RETURN = OPERATION OK
        RTS


;__SETUP_FD_CHS__________________________________________________________________________________________________________________
;
; 	TRANSFORM DOS65 CHS TO FLOPPY
;________________________________________________________________________________________________________________________________
;
SETUP_FD_CHS:
        LDA     sektrk          ; LOAD TRACK # (LOW BYTE)
        AND     #$01            ; FILTER OUT HEAD
        STA     debhead         ; STORE HEAD
        LDA     sektrk          ; SAVE TRACK IN A
        LSR     A               ; REMOVE HEAD BIT
        STA     debcyl          ; STORE IN TRACK
        LDA     seksec          ; LOAD SECTOR # (LOW BYTE)
        LSR     A               ;
        LSR     A               ; DIVIDE BY 4 (FOR BLOCKING)
        STA     debsec          ; STORE IN SECTOR

        .IF     USEDSKY=1 || USEDSKYNG=1
            PRTDBG  "DSKY OUTPUT 1$"
            LDA     sekdsk
            STA     DSKY_HEXBUF
            LDA     debcyl
            STA     DSKY_HEXBUF+1
            LDA     debhead
            STA     DSKY_HEXBUF+2
            LDA     debsec
            STA     DSKY_HEXBUF+3
            JSR     DSKY_BIN2SEG
            JSR     DSKY_SHOW
        .ENDIF

        RTS

;__DSKOP__________________________________________________________________________________________________________________________
;
; 	PERFORM A DISK OPERATION
;________________________________________________________________________________________________________________________________
;
DSKOP:
        SEI
        JSR     CHECKINT        ; CHECK INTERRUPT STATUS, MAKE SURE IT IS CLEAR
        CMP     #$FF            ; DID IT RETURN WITH ERROR CODE?
        BEQ     DSKEXIT         ; IF YES, EXIT WITH ERROR CODE
;
        JSR     SETTRACK        ; PERFORM SEEK TO TRACK
;
        LDA     FCMD            ; WHAT COMMAND IS PENDING?
        CMP     #CFD_READ|CFD_MFM; IS IT A READ COMMAND?
        BNE     GWRR_POLL       ;
        JMP     RDD_POLL        ;
GWRR_POLL:
        JMP     WRR_POLL        ;
DSKEXIT:
        LDA     #0              ; SET MOTOR OFF
        STA     FDC_DOR         ; OUTPUT TO CONTROLLER
        LDA     #$FF            ; SET IF ERROR
        CLI
        RTS

SNDFDWR:
        CLC
        LDA     DSKUNIT         ; GET DISK UNIT NUMBER
        AND     #$01            ; MASK FOR TWO DRIVES.
        STA     UNIT            ; PARK IT IN TEMP
        LDA     debhead         ; GET HEAD SELECTION
        AND     #$01            ; INSURE SINGLE BIT
        ASL     A               ;
        ASL     A               ; MOVE HEAD TO BIT 2 POSITION
        ORA     UNIT            ; OR HEAD TO UNIT BYTE IN COMMAND BLOCK
        STA     UNIT            ; STORE IN UNIT
        LDA     FCMD            ;
        JSR     PFDATA          ; PUSH COMMAND TO I8272
        LDA     UNIT            ;
        JSR     PFDATA          ;
        LDA     debcyl          ;
        JSR     PFDATA          ;
        LDA     debhead         ;
        JSR     PFDATA          ;
        CLC                     ;
        LDA     debsec          ;
        ADC     #$01            ;
        JSR     PFDATA          ;
        LDA     #$02            ;
        JSR     PFDATA          ; WHAT DENSITY
        LDA     #$09            ;
        JSR     PFDATA          ; ASSUME SC (SECTOR COUNT)  EOT
        LDA     #$1B            ;
        JSR     PFDATA          ; WHAT GAP IS NEEDED
        LDA     #$FF            ; DTL, IS THE LAST COMMAND BYTE TO I8272
        JSR     PFDATAS
        RTS


; PERFORM READ
; FROM READ TO READ MUST NOT EXCEED 25US WORST CASE MIN. (AT 2MHZ IS 2,000,000 CYCLES PER SECOND == 50 CYCLE BUDGET.)
;
RDD_POLL:
        LDX     #$00
        LDY     #$00
        JSR     SNDFDWR         ;
RDS1:
        LDA     FDC_MSR         ; GET STATUS  (4 CYCLES)
        BPL     RDS1            ; FDC IS NOT READY, WAIT FOR IT (UP TO 4 CYCLES)
        AND     #%00100000      ; EXECUTION MODE? (2 CYCLES)
        BEQ     DSKOPEND        ; NO, ERROR
RDS1A:
        LDA     FDC_DATA        ; GET DATA (4 CYCLES)
        STA     hstbuf,Y        ; WRITE IT (5 CYCLES)
        INY                     ; (2 CYCLES)
        BNE     RDS1            ; KEEP GOING (UP TO 4 CYCLES)   TOTAL =
        LDX     #$00
RDS2:
        LDA     FDC_MSR         ; GET STATUS
        BPL     RDS2            ; FDC IS NOT READY, WAIT FOR IT (UP TO 4 CYCLES)
        AND     #%00100000      ; EXECUTION MODE?
        BEQ     DSKOPEND        ; NO, ERROR
RDS2A:
        LDA     FDC_DATA        ; GET DATA
        STA     hstbuf+256,Y    ; WRITE IT
        INY
        BNE     RDS2            ; KEEP GOING
DSKOPEND:
        LDA     FDC_TC
        JSR     FDDELAY
;
        JSR     GFDATA          ;GET ERROR TYPE
        STA     FLERR
;* CLEAR OUT ANY REMAINING DATA
RESUL3:
        JSR     GFDATA          ;READ BYTE FROM FDC
        CMP     #$00
        BNE     RESUL3          ;CLEAR THEM ALL
        LDA     FLERR           ;
        AND     #%11000000      ;
        RTS


WRR_POLL:
        JSR     SNDFDWR         ;
WRS1:   ;
        LDA     FDC_MSR         ; GET STATUS
        BPL     WRS1            ; NOT READY
        AND     #%00100000      ; EXECUTION MODE?
        BEQ     WRS3            ; NO, ERROR
        LDA     hstbuf,Y        ; WRITE IT
        STA     FDC_DATA        ; WRITE TO FDC
        INY
        BNE     WRS1            ; DO NEXT
WRS2:   ;
        LDA     FDC_MSR         ; GET STATUS
        BPL     WRS2            ; NOT READY
        AND     #%00100000      ; EXECUTION MODE?
        BEQ     WRS3            ; NO, ERROR
        LDA     hstbuf+256,Y    ; WRITE IT
        STA     FDC_DATA        ; WRITE TO FDC
        INY
        BNE     WRS2            ; DO NEXT
WRS3:
        JMP     DSKOPEND        ;


;__SETTRACK__________________________________________________________________________________________________________________________
;
; 	SEEK TO A TRACK ON GIVEN UNIT
; 	A: TRACK #
;________________________________________________________________________________________________________________________________
;
SETTRACK:
        LDA     #DOR_INIT
        ORA     DSKUNIT         ; SET MOTOR ON
        STA     FDC_DOR         ; OUTPUT TO CONTROLLER

; ANY INTERUPT PENDING
; IF YES FIND OUT WHY/CLEAR
        JSR     CHECKINT        ; CHECK INTERRUPT STATUS, MAKE SURE IT IS CLEAR
        CMP     #$FF            ; DID IT RTSURN WITH ERROR CODE?
        BNE     SETTRK1
        JMP     SETTRKEXIT      ;

;
SETTRK1:
        LDA     debcyl          ; GET TRACK
        CMP     #$00            ;
        BEQ     RECAL           ; IF 0 PERFORM RECAL INSTEAD OF SEEK
        LDA     #CFD_SEEK       ; SEEK COMMAND
        JSR     PFDATA          ; PUSH COMMAND
        LDA     DSKUNIT         ; SAY WHICH UNIT
        AND     #$01
        JSR     PFDATA          ; SEND THAT
        LDA     debcyl          ; TO WHAT TRACK
        JSR     PFDATA          ; SEND THAT TOO
        JMP     WAINT           ; WAIT FOR INTERRUPT SAYING DONE
RECAL:
        LDA     #DOR_INIT
        ORA     DSKUNIT         ; SET MOTOR ON
        STA     FDC_DOR         ; OUTPUT TO CONTROLLER
        LDA     #CFD_RECAL      ; RECAL TO TRACK 0
        JSR     PFDATA          ; SEND IT
        LDA     DSKUNIT         ; SAY WHICH UNIT
        AND     #$01
        JSR     PFDATA          ; SEND THAT TOO
;
WAINT:
        PHA
        TXA
        PHA
        LDX     #100
        JSR     FDVDELAY
        PLA
        TAX
        PLA
:
        JSR     CHECKINT
        LDA     FDC_MSR         ; READ SEEK STATUS
        AND     #%00001111      ; ANY DRIVES SEEKING?
        BNE     :-              ; YES, WAIT FOR THEM
;
SETTRKEXIT:
        RTS

;__PFDATA__________________________________________________________________________________________________________________________
;
; WRITE A COMMAND OR PARAMETER SEQUENCE
;
; TRANSFERS ARE SYNCHONIZED BY MSR D7 <RQM> AND D6 <DIO>
;	RQM  DIO
;	0	0	BUSY
;	1	0	WRITE TO DATA REGISTER PERMITTED
;	1	1	BYTE FOR READ BY HOST PENDING
;	0	1	BUSY
;
;________________________________________________________________________________________________________________________________
;
PFDATA:
        PHA                     ; SAVE DATA BYTE
        LDY     #$00
WRF1:
        LDA     FDC_MSR         ; READ FDC STATUS
        TAX
        AND     #$80            ;
        BNE     :+
        INY
        BNE     WRF1            ; FDC IS NOT READY, WAIT FOR IT
        PLA
        LDA     #$FF
        RTS
:
        TXA
        AND     #$40            ; TEST DIO BIT
        BNE     WRF2            ; FDC IS OUT OF SYNC
        PLA                     ; RESTORE DATA
        STA     FDC_DATA        ; WRITE TO FDC
        JSR     FDDELAY
        JSR     FDDELAY
        JSR     FDDELAY
        RTS
; FDC IS OUT OF SYNC CLEAR IT OUT AND RE-TRY
WRF2:
        LDA     FDC_DATA        ; READ DATA REGISTER
        JMP     WRF1            ; AND CONTINUE

;__PFDATAS_________________________________________________________________________________________________________________________
;
; WRITE A COMMAND OR PARAMETER SEQUENCE (NO PAUSE)
;
; TRANSFERS ARE SYNCHONIZED BY MSR D7 <RQM> AND D6 <DIO>
;	RQM  DIO
;	0	0	BUSY
;	1	0	WRITE TO DATA REGISTER PERMITTED
;	1	1	BYTE FOR READ BY HOST PENDING
;	0	1	BUSY
;
;________________________________________________________________________________________________________________________________
;
PFDATAS:
        PHA                     ; SAVE DATA BYTE
WRF1S:
        LDA     FDC_MSR         ; READ FDC STATUS
        TAX
        AND     #$80            ;
        BEQ     WRF1S           ; FDC IS NOT READY, WAIT FOR IT
        TXA
        AND     #$40            ; TEST DIO BIT
        BNE     WRF2S           ; FDC IS OUT OF SYNC
        PLA                     ; RESTORE DATA
        STA     FDC_DATA        ; WRITE TO FDC
        RTS
; FDC IS OUT OF SYNC CLEAR IT OUT AND RE-TRY
WRF2S:
        LDA     FDC_DATA        ; READ DATA REGISTER
        JMP     WRF1S           ; AND CONTINUE



;__CHECKINT__________________________________________________________________________________________________________________________
;
; CHECK FOR ACTIVE FDC INTERRUPTS BEFORE GIVING I8272 COMMANDS
; POLL RQM FOR WHEN NOT BUSY AND THEN SEND FDC
; SENSE INTERRUPT COMMAND.  IF IT RTSURNS WITH NON ZERO
; ERROR CODE, PASS BACK TO JSRING ROUTINE FOR HANDLING
;________________________________________________________________________________________________________________________________
;
CHECKINT:
        LDY     #$00
:
        LDA     FDC_MSR         ; READING OR WRITING IS KEYS TO D7 RQM
        AND     #$80
        BNE     :+              ; WAIT FOR RQM TO BE TRUE. WAIT UNTIL DONE
        JSR     FDDELAY
        INY
        BNE     :-
        JMP     ERRCLR

:
        LDA     FDC_MSR         ; READING OR WRITING IS KEYS TO D7 RQM
        AND     #$40            ; WAITING FOR INPUT?
        BEQ     SENDINT
        RTS

ERRCLR:
        LDY     #$00
:
        LDA     FDC_DATA        ; CLEAR THE JUNK OUT OF DATA REGISTER
        LDA     FDC_MSR         ; CHECK WITH RQM
        AND     #$80            ; IF STILL NOT READY, READ OUT MORE JUNK
        BNE     :+              ;
        JSR     FDDELAY
        INY
        BNE     :-
:
        LDA     #$FF            ; RETURN ERROR CODE -1
;
        RTS

;__SENDINT__________________________________________________________________________________________________________________________
;
; SENSE INTERRUPT COMMAND
;________________________________________________________________________________________________________________________________
;
SENDINT:
        LDA     #CFD_SENSEINT   ; SENSE INTERRUPT COMMAND
        JSR     PFDATA          ; SEND IT
        JSR     GFDATA          ; GET RESULTS
        STA     ST0             ; STORE THAT
        AND     #$C0            ; MASK OFF INTERRUPT STATUS BITS
        CMP     #$80            ; CHECK IF INVALID COMMAND
        BEQ     ENDSENDINT      ; YES, EXIT
        JSR     GFDATA          ; GET ANOTHER (STATUS CODE 1)
        LDA     ST0             ; GET FIRST ONE
        AND     #$C0            ; MASK OFF ALL BUT INTERRUPT CODE 00 IS NORMAL
ENDSENDINT:
        RTS                     ; ANYTHING ELSE IS AN ERROR


;__GFDATA__________________________________________________________________________________________________________________________
;
; GET DATA FROM FLOPPY CONTROLLER
;
; TRANSFERS ARE SYNCHONIZED BYT MSR D7 <RQM> AND D6 <DIO>
;	RQM  DIO
;	0	0	BUSY
;	1	0	WRITE TO DATA REGISTER PERMITTED
;	1	1	BYTE FOR READ BY HOST PENDING
;	0	1	BUSY
;
;________________________________________________________________________________________________________________________________
;
GFDATA:
        LDY     #$00
:
        LDA     FDC_MSR         ; GET STATUS
        TAX                     ;
        AND     #%10000000      ; NOT READY, WAIT
        BNE     :+              ;
        INY
        BNE     :-
        LDA     #$00
        RTS
:
        TXA
        AND     #%01000000      ; ANY DATA FOR US?
        BEQ     GFDATA1         ; NO, SKIP IT
        LDA     FDC_DATA        ; GET FDC DATA
GFDATA1:
        RTS

;__FD_DETECT______________________________________________________________________________________________________________________
;
; 	DETECT FLOPPY HARDWARE
;________________________________________________________________________________________________________________________________
FD_DETECT:
; BLINDLY RESET FDC (WHICH MAY OR MAY NOT EXIST)
        JSR     FC_RESETFDC     ; RESET FDC

        LDA     FDC_MSR         ; READ MSR
        CMP     #$80
        BEQ     FD_DETECT1      ; $80 IS OK
        CMP     #$D0
        BEQ     FD_DETECT1      ; $D0 IS OK
        LDA     #$FF            ; NOT OK
        STA     HARDWARE_DETCT
        RTS
;
FD_DETECT1:
        LDX     #100
        JSR     FDVDELAY        ; WAIT A BIT FOR FDC
        LDA     FDC_MSR         ; READ MSR AGAIN
        CMP     #$80
        BEQ     :+              ; $80 IS OK
        CMP     #$D0
        LDA     #$FF            ; NOT OK
        STA     HARDWARE_DETCT
        RTS
:
        LDA     #$00            ; OK
        STA     HARDWARE_DETCT
        RTS

FC_RESETFDC:
        LDA     FDC_RESET
        LDA     FDC_RESET
        LDX     #150
        JSR     FDVDELAY        ; WAIT A BIT FOR FDC

        LDA     #$00
        STA     FDC_DOR
        JSR     FDDELAY
        LDA     #DOR_INIT
        STA     FDC_DOR
        LDX     #150            ;
        JSR     FDVDELAY
        RTS


FDDELAY:
        PHA
        PLA
        PHA
        PLA
        RTS
FDVDELAY:
        PHA
        PLA
        PHA
        PLA
        DEX
        CPX     #$00
        BNE     FDVDELAY
        RTS

        .IF     DRIVERS=1
;*__FL_STORE_BOOT_IMAGE_______________________________________________________________________________
;*
;*  WRITE Boot image to block 0 of device
;*
;*  YA points to:
;* 			DB 	Device Unit
;*			DB 	RAM Page
;*			DW 	Source Address
;* 			DB	Image Length (Pages)
;*____________________________________________________________________________________________________
FL_STORE_BOOT_IMAGE:

            STA     pointr          ; SET POINTR TO INFO BLOCK
            STY     pointr+1
            LDA     #<BOOTUNIT
            STA     room
            LDA     #>BOOTUNIT
            STA     room+1
            LDY     #$00            ; COPY PARAMETERS TO USEFUL AREA
:
            LDA     (pointr),Y
            STA     (room),Y
            INY
            CPY     #05
            BNE     :-

            LDA     BOOTUNIT
            CMP     #$00
            BNE     :+
            LDA     #$10
            JMP     :++
:
            LDA     #$21
            STA     DSKUNIT
:
            JSR     RECAL           ;

            LDA     #$00
            STA     debcyl
            STA     debhead
            STA     debsec          ;
            JSR     SETTRACK        ;


            JSR     INIT_PAGE_COPY  ; COPY PAGE COPY CODE TO LORAM
            LDA     BOOTSOURCE      ; SETUP SOURCE POINTER
            STA     pointr
            LDA     BOOTSOURCE+1
            STA     pointr+1

:
            LDA     BOOTRAMPAGE
            JSR     COPY_PAGE_TO_HSTBUF; COPY 512 BYTES AT POINTR TO HSTBUF (AND INC POINTER)

            LDA     #DOR_INIT
            ORA     DSKUNIT         ;
            STA     FDC_DOR         ; OUTPUT TO CONTROLLER
            JSR     FL_WRITE_SECTOR_RAW
            CMP     #$FF
            BEQ     FL_STORE_BOOT_IMAGE_ERROR
            INC     debsec
            LDA     debsec
            CMP     #9
            BNE     :+
            LDA     #00
            STA     debsec
            INC     debhead
            LDA     debhead
            CMP     #$02
            BNE     :+
            LDA     #00
            STA     debhead
            INC     debcyl
            JSR     SETTRACK
:
            DEC     BOOTLENGTH
            LDA     BOOTLENGTH
            CMP     #$00
            BNE     :--
            LDA     #$00            ; ZERO ON RETURN = OPERATION OK
            RTS
FL_STORE_BOOT_IMAGE_ERROR:
            LDA     #$FF            ; 1 ON RETURN = OPERATION FAIL
            RTS

;*__IDE_RESTORE_BOOT_IMAGE____________________________________________________________________________
;*
;*  READ Boot image from block 0 of device
;*
;*  YA points to:
;* 			DB 	Device Unit
;*			DB 	RAM Page
;*			DW 	Source Address
;* 			DB	Image Length (Pages)
;*____________________________________________________________________________________________________
FL_RESTORE_BOOT_IMAGE:

            STA     pointr          ; SET POINTR TO INFO BLOCK
            STY     pointr+1
            LDA     #<BOOTUNIT
            STA     room
            LDA     #>BOOTUNIT
            STA     room+1
            LDY     #$00            ; COPY PARAMETERS TO USEFUL AREA
:
            LDA     (pointr),Y
            STA     (room),Y
            INY
            CPY     #05
            BNE     :-

            LDA     BOOTUNIT
            CMP     #$00
            BNE     :+
            LDA     #$10
            JMP     :++
:
            LDA     #$21
            STA     DSKUNIT
:
            STA     DSKUNIT
            JSR     RECAL           ;

            LDA     #$00
            STA     debcyl
            STA     debhead
            STA     debsec          ;
            JSR     SETTRACK        ;


            JSR     INIT_PAGE_COPY  ; COPY PAGE COPY CODE TO LORAM
            LDA     BOOTSOURCE      ; SETUP SOURCE POINTER
            STA     pointr
            LDA     BOOTSOURCE+1
            STA     pointr+1

:
            JSR     READFL_DIRTY
            CMP     #$FF
            BEQ     FL_RESTORE_BOOT_IMAGE_ERROR
            LDA     BOOTRAMPAGE
            JSR     COPY_HSTBUF_TOPAGE; COPY 512 BYTES FROM HSTBUF TO POINTR HSTBUF (AND INC POINTER)
            INC     debsec
            LDA     debsec
            CMP     #9
            BNE     :+
            LDA     #00
            STA     debsec
            INC     debhead
            LDA     debhead
            CMP     #$02
            BNE     :+
            LDA     #00
            STA     debhead
            INC     debcyl
            JSR     SETTRACK        ;
:
            DEC     BOOTLENGTH
            LDA     BOOTLENGTH
            CMP     #$00
            BNE     :--
            LDA     #$00            ; ZERO ON RETURN = OPERATION OK
            RTS
FL_RESTORE_BOOT_IMAGE_ERROR:
            LDA     #$FF            ; 1 ON RETURN = OPERATION FAIL
            RTS
        .ENDIF


HARDWARE_DETCT:
        .BYTE   0               ; HARDWARE DETECTED
debhead:
        .BYTE   0               ; DEBLOCKED HEAD
debcyl:
        .BYTE   0               ; DEBLOCKED CYLINDER
debsec:
        .BYTE   0               ; DEBLOCKED SECTOR
Cdebhead:
        .BYTE   0               ; DEBLOCKED HEAD (cache)
Cdebcyl:
        .BYTE   0               ; DEBLOCKED CYLINDER (cache)
Cdebsec:
        .BYTE   0               ; DEBLOCKED SECTOR (cache)
FLERR:
        .BYTE   $00             ;
UNIT:
        .BYTE   $00             ;
FCMD:
        .BYTE   0               ; COMMAND READ OR WRITE,
ST0:
        .BYTE   0               ; COMMAND READ OR WRITE,
FLRETRY:
        .BYTE   00
FLRETRY1:
        .BYTE   00
